AnasSarkiz/tscircuit-ai-agent-remote/assets/product-concepts/ai-remote-v1-infographic-v2.prompt.txt

Edit the attached AI Remote product infographic into a substantially cleaner, more premium SCREEN-FIRST handheld concept. The user's correction is the highest priority: MOST OF THE DEVICE IS SCREEN, and there is ONLY ONE PHYSICAL BUTTON, ON THE TOP EDGE, used to HOLD TO TALK. The old design has far too many controls and a small screen; completely redesign that device geometry while retaining the reference infographic's overall three-column presentation.

DEVICE INVARIANTS FOR EVERY VIEW: one consistent beautiful slim portrait rounded rectangular handheld, matte graphite/dark charcoal frame, restrained radiused corners, narrow bezels, a large edge-to-edge-ish portrait color touchscreen covering approximately 90% of the entire front face. The front is almost entirely glass/screen, like a small dedicated AI communicator. No chin, no large control panel, no front physical buttons. Exactly ONE tactile hold-to-talk button is recessed into the TOP EDGE of the enclosure, easily operated by an index finger. Show the top-edge button visibly in the three-quarter hero render, not centered on the front face. Discreet USB-C on the bottom edge. No rotary encoder, no dial, no knob, no dedicated APPROVE/REJECT physical buttons, no side switches, no extra side buttons, no exposed RGB LED. Tiny microphone openings and a discreet speaker opening may appear on the edge, subordinate to the screen. No visible physical control besides the single top-edge TALK button. Keep this geometry and button placement identical in the hero, exploded lid, and all other device renderings.

AESTHETIC: restrained, refined industrial design, excellent proportions, polished glass and matte graphite, premium consumer electronics CGI, not a chunky hobby enclosure. Clean white canvas, charcoal/navy typography, restrained teal/cyan accents, hairline separators, much more breathing room, clear hierarchy. Keep the three-column editorial idea of the supplied image but simplify all clutter and shorten text. Photoreal concept render, soft daylight lifestyle hero on a clean desk, tasteful studio lighting on exploded assembly. No background novelty typography, no mugs with slogans, no plant labels. No garish rainbow controls. Crisp carefully spelled typography throughout.

HEADER: large title "AI Remote V1" with V1 in teal. Subtitle "Hold to talk. Release to ask." Top right short sentence "Your AI, in your hand."

LEFT, LARGE HERO: the redesigned screen-dominant device is upright on a quiet wooden desk, slightly angled so the single top-edge button is clearly visible. Its front display is very large with a calm dark navy/cyan interface: small heading "LISTENING", a tasteful luminous cyan waveform, and simple large copy "I'm listening." Small line "Release to send". A minimal bottom status area is part of the screen, not a physical control. Keep the front elegant, spacious and mostly glass. Beneath hero: "One button. A conversation." and smaller "Hold, speak, release."

CENTER, EXPLODED CONCEPT: show the same slender enclosure with large front glass/display, the display module, a thin green concept PCB, a thin LiPo pouch, a small speaker, and rear shell. No front button mat or encoder mechanism. The only mechanical control is the single top-edge pushbutton. Five small numbered cyan/blue callouts, with correct leader targets and no overlaps:
1 "Large display" / "Screen-first interface"
2 "Hold-to-talk button" / "One button on the top edge"
3 "Voice + sound" / "Microphones and speaker"
4 "Wireless AI" / "Wi-Fi to your backend"
5 "Rechargeable" / "USB-C + LiPo"
This is an illustrative assembly, not verified mechanical CAD.

RIGHT: two clean, smaller conceptual green PCB views titled "PCB TOP — concept" and "PCB BOTTOM — concept". Show a slim portrait same-outline board on both faces. Top view contains an ESP32-S3 antenna module at the top with a clear hatched antenna keepout, microphone component categories, a display connector and exactly one top-edge button interface. No large tactile front controls, no encoder footprint, no colored physical buttons. Bottom view shows USB-C, power circuit, battery connector and speaker connector. Use only 3–4 concise readable labels per view: "ESP32-S3", "Antenna clearance", "Display connector", "Top button"; then "USB-C", "Power + battery", "Speaker". Caption "Proposed PCB layout"; do not invent final screen size or enclosure dimensions.

BOTTOM: simple elegant interaction flow with small teal icons: "HOLD" → "SPEAK" → "RELEASE" → "AI RESPONSE". No physical approval/rejection claims or decision icons. A thin readable footer states "Concept illustration • Proposed layout • Untested prototype".

Absolutely remove every old dial/encoder, all front physical buttons, the old MIC OFF side slider, green/red button imagery, the old physical approval callouts and the old small-screen proportions. The visual must communicate a dedicated handheld where almost the whole device is the display and the only physical button is on top, hold-to-talk only. Make the new enclosure visibly more minimal and screen-dominant than the original. Output a polished high-resolution 3:2 landscape infographic with nothing cropped and consistent product identity across views.
