AnasSarkiz/tscircuit-ai-agent-remote/assets/product-concepts/ai-remote-v1-infographic-v3.prompt.txt

Edit the referenced AI Remote infographic into a MUCH SIMPLER SQUARE DEVICE concept with TOP-SIDE PCB ASSEMBLY ONLY. The user wants a simple square form, and only top assembly. Preserve the earlier essential interaction: the front is almost entirely the display, exactly one exterior physical button on the top edge, HOLD TO TALK. Change the tall phone-like enclosure to a compact square, with width and height nearly equal. Do not merely crop the old image; redesign the product and simplify the composition.

Output one polished landscape 3:2 product concept graphic with bright white background, elegant restrained navy/black typography, soft cyan/teal accents, realistic premium industrial design CGI, generous whitespace, and only a few short labels. Far less text and diagram clutter than the reference.

SQUARE PRODUCT: a small slim square handheld AI communicator, graphite/dark charcoal rounded-square enclosure, softly radiused corners, thin bezels. A nearly square color display covers about 90% of the front face. No large chin or control panel. Exactly one modest recessed tactile button centered on the TOP EDGE, visibly separate from the glass, easy to hold with an index finger. No front buttons, no knobs, no encoder, no side switches, no extra buttons or visible status LEDs. Discreet USB-C on the bottom edge and tiny microphone/speaker apertures only. The same square device and top-button geometry must be consistent in every depiction.

COMPOSITION:
1. LEFT/HERO, roughly 50% width: large beautiful three-quarter front view of the square device, on an uncluttered pale warm wooden surface, soft studio/daylight reflections. Angle it gently so both the screen and the single TOP EDGE button are visible. No lifestyle props or distracting background. On-screen UI is minimal: small cyan heading "LISTENING", a single elegant cyan waveform, large copy "I'm listening.", small line "Release to send". Avoid smartphone UI clutter and time/battery icon rows. The device must look SQUARE rather than portrait-phone-shaped.
2. CENTER/RIGHT, roughly 50% width: a simple isolated assembly illustration, with only two or three levels, showing the same square front enclosure/display slightly raised over the square main PCB. Use one clear TOP VIEW of the populated PCB. Show every soldered electronic component on this TOP face: ESP32-S3 module, small power circuitry, a display connector, microphone categories, battery/speaker connectors and top-edge button. All connectors and controls are mounted/accessed from the same top component side as a PROPOSED assembly. The PCB underside is not shown; no bottom view or underside populated electronics. The PCB is compact and square to match the enclosure. If a rear enclosure/base is shown, keep it simple, no extra electronic layers or clutter. No invented routing-validation claims. Empty hatched antenna keepout with no copper/components; all placement is illustrative.

TEXT/HIERARCHY:
Top large title: "AI Remote"
Subtitle: "Square. Simple. Hold to talk."
Short callout pointing at the exterior top edge: "One top button"
One callout at screen: "Large display"
Heading over PCB view: "PCB — TOP ASSEMBLY ONLY"
Under PCB heading small note: "Proposed placement"
At most three small PCB leader labels: "ESP32-S3", "Display connector", "USB-C + power".
Bottom thin interaction strip, no excessive icons: "HOLD" → "SPEAK" → "RELEASE" → "AI RESPONSE".
Small readable footer: "Concept only • Top-side assembly proposed • Untested prototype"

STRICT REQUIREMENTS: Device outline is nearly 1:1 square, not tall portrait. Screen occupies nearly all front. Exactly one exterior physical top-edge hold-to-talk button. No rotary dial, no approve/reject physical controls, no side privacy slider. Only top-side populated PCB assembly is depicted; remove the previous bottom PCB diagram entirely. No dimensions or fabrication-ready claims. Do not represent this as validated CAD or a physical tested prototype. Reduce annotation count and give the render room to breathe. Clean accurate spelling, no duplicated labels, no cropped text, no overlapping arrows. Premium, minimal, practical, elegant.
