AnasSarkiz/tscircuit-ai-agent-remote/CLOUD_HANDOFF.md

Latest delivery checkpoint: generated native SHA-256
`16c299accb1750ce3b93997726c7c3316595e9848730bd9f20a55b6d24c4317a`.
Read `evidence/pcb-completion-2026-10-08/review.md` and current receipt index.
All 13 actual phase SRJs/output paths are archived. Optional replay endpoint
metadata/four via IDs differ; all copper geometry and electrical source records
are preserved. Fresh independent audits confirm 0 shorts/geometric violations,
12 open nets and all 9,813 parent connected pairs. Schematic UI has one retained
parallel-branch advisory; the additional R63/U3 collision is corrected. Native
retains 16 supplier-refresh and four pin-attribute lookup warnings. Genuine
imports and strict rotation remain qualified; no warning is hidden. Source
snapshot runs complete but unchanged golden references fail. No fabricated
final supervisor timing/memory is reported after the session lost that receipt.
Setup installs separate checksum-verified Bun 1.4.0 for generation while keeping
Bun 1.3.9 frozen install/tests. Saved onboarding draft revision 32 is read back;
it does not apply runtime policy. Public delivery is established by final
publication receipts, not by presumed cloud CI or fabrication approval.

## Current canonical generator qualification — 2026-10-08

**0.0.11-wip-generator-qualification — NOT READY TO ORDER.** Canonical project
runtime fixes eliminate all 169 schema failures and missing pill paste. The
untouched genuine C7848 import clears U14 supplier rotation. Local regulator
escape requirements now explicitly preserve 1 mm trunks. All 9,813 existing
connected pairs are preserved; all 125 purchased component poses are unchanged.
Fresh native checks still report 50 connection errors / 12 physically open
assigned nets plus two unassigned battery contacts. Shorts and measured copper
clearance violations are zero. The final 2.8-inch LCD, backlight, RF/mechanical
integration and battery polarity remain unqualified.

The corrected canonical Gerber library preserves USB slots. Independent strict
Gerber parsing and Excellon inspection pass; actual exports are explicitly
NOT FOR FABRICATION. Strict PnP rotation passes for all 125 parts, and the official
resolved BOM covers all 43 supplier identities. Current inventory confirms 39
identities conservatively; D2 is out of stock and three positive-stock records
require assembly-availability confirmation. Complete current/thermal and full fabrication gates remain open.
All 15 original schematic style issues are corrected in the actual schematic
trial, with identical PCB/CAD geometry. One newly exposed alignment advisory
misclassifies the VMOTOR flyback/bleeder parallel branches as a series pair;
its exact six-contact topology and conflicting orientation advice are reviewed
and retained in the schematic-style-repair evidence. Final routed checks are
recorded independently; no failure is hidden.

Core also prevents disabled subcircuits from starting autorouting during
updates; both disabled controls and an enabled control are regression-tested.
The actual isolated MCU diagnostic now has zero copper and zero routing events.
Board tests: 51 pass; the full-board fabrication gate still fails on 50
unresolved native connections. These are 50 assigned open contacts plus two
unassigned J3 contacts, not a completed board.

Receipts and source patches: `evidence/pcb-completion-2026-10-08/` and `toolchain/`.
Older entries below are historical.

---

## Current local microphone bypass — 2026-10-08

**0.0.10-wip-microphone-bypass; not ready to order.** Read
`evidence/microphone-local-bypass-2026-10-08/review.md` and its native/qualification
receipts first. C81/C45000 is now (17.05,-28.10)/180 degrees top, beside U5;
R93/C105881 moves to (16.50,-31.42)/0 degrees top. Actual .30 mm top bypass:
1.442790 mm supply, .599976 mm ground pour entry, no bypass via. All four local
terminal contacts pass. Only these two rigid purchased poses change; all 125
identities, 123 stationary geometries and 244 genuine asset/solver files remain.

Native SHA `8be25ca28e6271890aab0d450ffdc62088ced91967ae1b6185ab8267ff9f1177`:
381 traces / 320 full-span .30/.45 vias / 273 pours. Zero measured shorts and
geometric/clearance violations; all 9,813 prior contacts preserved and all 250
active authored region widths pass. Full-board gates still fail: 50 native
errors (46 J7/4 U27), 12 assigned open nets, plus two unassigned J3 outer
contacts. Requested centered 2.8-inch landscape LCD is unimplemented; exact
contact/fold/bend/antenna/backlight qualification remains required.

All five source checks, TypeScript, formatting and 94 routing regressions pass;
board tests 49 pass/2 fail, UI style 15 issues, strict schema 169 failures,
unchanged-reference source snapshots fail. Two native routes violate explicit
width minima and 65 need nominal/current review; 32 native paste records,
polygon Gerber/short-check and U14 rotation remain unresolved. No order claim.

Fresh official JLC pages: 12/43 identities cover one board, 2 have zero public
buyability (U1/D2), 29 HTTP503 inventory results unknown. D2 also reports zero
stock. $26.3055 is the prior unchanged-identity reference subtotal, not a quote.
Latest core .2110 still lacks the tested paste fix; keep frozen runtime.

The genuine renderer required 43 exact prior official supplier-orientation
cache inputs to retain supplier maps during live lookup failures. Their origin,
hashes and failed native trial are preserved. For source rebuilds: run
`bun run publish:prepare`, link frozen node_modules as previously documented,
then `python3 evidence/microphone-local-bypass-2026-10-08/restore-supplier-orientation.py .publish/board /tmp/restored-board-supplier-orientation.json`.
Preserve actual native/events; clean stage with publish:prepare before upload.
Public package is 128 regular files; hidden input caches are exact GitHub
evidence, not invented solver results. One heavy Linux operation through the
budget supervisor at a time; no local Mac routing or unchanged whole-net retry.

Public GitHub implementation 3d88ca2 and tsci .10 release
d17c1129-2a2a-4834-a186-e562b77aa268 are verified: all128 anonymous files exact,
native preview exact object, release public/listed/ready. The two HTTP413 files
were verified missing before bounded supported archive repair. No readiness
override. Both automatic .10 cloud jobs failed infrastructure sandbox
initialization before source execution; any supported retry/actual observation
is recorded separately, never inferred from uploaded native availability.
The actual .9 cloud job completed without a user-code job error, superseding
its old pending observation. Latest official circuit-json .521 independently
still reports the same169 failures on the exact current native. Active pins
remain frozen. Cloud draft30 startup instructions are saved/readback exact;
installation/repositories/network/requirements unchanged. Review/save/publish
is needed to activate the environment; fresh restoration remains unverified.
Earlier entries are historical.

---

## Current UART and supply repair — 2026-10-07

**0.0.9-wip-standard-uart; not ready to order.** Read
`evidence/programmer-direct-uart-2026-10-07/review.md` first. Genuine untouched J6/C160389 now
has RX/GND/TX on pins 1/2/3 and grounded holds 4/5; pose remains (-17.4,-10) mm,
0° top. Specified numbered SH3 cable directly connects the standard programmer;
separate power, manual BOOT/RESET and open enclosure required (6.3 mm mated
height). Hardware/cable assembly is untested.

Real authored UART copper, ground pad links, audio-gate detour and 0.8 mm bottom
V3V3 bypass are implemented. Native SHA `bcee32a49486610d7379583efb2b378846cc75f232272b50c717ad129c495704`.
381 traces / 322 full-span 0.30/0.45 mm vias / 273 pours. All 250 active region
widths and all 9,813 retained contact pairs pass. Other 124 purchased geometries
are unchanged. Measured shorts/geometry violations: 0/0. **50 native display
errors / 12 physically open nets remain.** Five source checks, TypeScript,
formatting and 94 routing regressions pass; board tests 49 pass/2 fail. Actual
UI: 15 style issues. Strict schema: 169 failures. Snapshots fail with unchanged
references. All failed trials and actual source/native events are preserved.

Requested centered landscape LCD remains unimplemented: exact fold/contact map,
bend radius, RF overlap and opposite backlight topology are unqualified. J3
outer battery contacts remain unnumbered/unrouted. Active paste, U14 rotation,
Gerber, two regulator width minima/current review and assembler allocation
remain gates. Official core 0.0.2108 still lacks the tested canonical paste fix.
Keep the frozen official runtime; no local package links, import/JSON edits,
weaker checks or orders. All 43 part identities have dated official receipts;
public buyability covers 40. Reference subtotal $26.3055 excludes fabrication,
assembly, external assemblies, shipping and minimum order quantities.

Public GitHub implementation commit 1642750 and tsci release
f520e705-7b21-4a06-89d2-a66b70ced491 (.9) are verified: all 128 public runtime
files match; the native preview is the exact qualified object. Release is public,
listed, latest and ready-to-build. No manual readiness override. An earlier
incomplete-upload cloud job failed missing STEP; that asset is now exact/public.
The later cloud job was still generating pours at observation, not a CI pass.
Continue with frozen Bun 1.3.9 and one budgeted heavy Linux operation at a time.
Saved cloud draft revision 29 retains all 20 custom hosts, install/repositories
and previous startup instructions; Save/Publish remains needed to apply it.
Earlier entries below are historical.

---

## Latest canonical paste repair — 2026-10-07

Read `evidence/core-pill-paste-fix-2026-10-07/review.md` first. The pill/rotated-pill
paste generator is fixed in canonical core source at base commit 90785db
(package 0.0.2106). Seventeen relevant tests, full TypeScript, formatting, build
and dist smoke pass. Genuine U14 coupon has 20 valid apertures with identical
physical pads; genuine U16/U27 coupons have 34. All local package links were
removed and official packages restored. Official 0.0.2106 still reproduces zero
U14 paste, so this is an unreleased source fix. Do not claim the active board's
32 missing paste records are repaired or deploy a local yalc runtime.

Active board remains official core 0.0.2090 and exact accepted native SHA below.
Latest copper audit still finds 0 measured shorts/clearance violations, 12 open
nets and 50 native open-port errors. No LCD pose, schematic or routing change is
accepted. Exact panel/RF/flex qualification and a supported released generator
fix remain dependencies. Saved cloud draft is revision 28 with 20 custom hosts;
its network settings still require runtime application. Use CI Bun 1.4.0 only
for the isolated upstream source work; keep the board's frozen setup intact.

## Latest 2.8-inch request —2026-10-07

The uploaded follow-up explicitly supersedes the2.3-inch plan with a landscape
BuyDisplay~2.8-inch panel and left/right FPC/J7 connection. **No replacement is
implemented.** Exact ER-TFT028A2-4 primary mirror confirms69.3×50.2mm body,
57.6×43.2mm active area,ILI9341 and common-cathode backlight. Centred body overlaps
current antenna keepout59.5mm²;flat 26.7mm tail leaves the enclosure;minimum bend
radius is not published. Preferred A3 download is still challenged and the actual
Cloudflare subdomain is proxy-blocked. Saved19-domain draft/startup priorities
need runtime application;model CDN is responding. Canonical exact/download C7848
re-import now fixes supplier pin 1 and preserves exact CAD assets/origin,but20
pill pads have no paste,so it is not applied to the active board. Old2.3-inch
staged sources and rejected placement are retained underE13. Current accepted
native/source/routes remain unchanged,with 50 opens and fabrication gates.
Read `evidence/display028-integration-2026-10-07/review.md` and the latest user
decision first. Do not continue the superseded2.3-inch poses or guess final J7
mating. Requested actual placement/routing is blocked,not complete.

Historical handoff follows.

## Current approved 2.3-inch selection and primary review — 2026-10-07

The user uploaded the exact **ER-TFT023-1** datasheet and accepted the smaller
2.3-inch display. The earlier ≥80% display-body coverage target is explicitly
relaxed for this panel. Select the no-touch ILI9342 / 320×240 panel for the next
revision; do not confuse an accepted selection with an implemented replacement.

The primary PDF is now archived and reviewed in
`evidence/display023-primary-review-2026-10-07/`. SHA-256:
`476f23033ca4ce0caa9ca6470fbc3d287b841240afaa54db986756fdfa588095`.
Rotate the native front view 90° CCW for a 45.8×50.9 mm portrait body with a
right-side flex. The 50-pin audit finds one required role change under the old
provisional mapping: panel pin 6 / IM0 must connect to 2.8 V VLCD, giving SPI
mode 1111. The other 49 assignments match; physical mapping is not qualified.
Existing 2.8 V logic and four-sink backlight circuitry fit the reviewed limits.

The manufacturer recommends a top-contact socket for a flat tail. Retaining
C262650 behind the panel needs a qualified two-fold path and proposed J7 rotation
270°; a single-fold alternative uses lower-contact C11063 at 90°. Both proposed
poses conditionally map panel n → J7 n. No arrangement or new contact-dependent
source/copper is accepted yet. The nominal placement proposal moves J7, U14,
C42 and C43, with about 69.54% body/PCB overlap and no nominal rectangle overlaps.
It does not establish full housing/flex fit, copper clearance or native DRC.

**Dependent implementation is blocked** by unresolved physical flex/slot/contact
tolerances and the existing U14/C7848 strict supplier pin-1 rotation discrepancy.
Do not patch a genuine import, guess bend limits, or preserve the old mapping
after a connector rotation. Preserve accepted native bytes and all 9,842 prior
connections before any qualified move. The archived proposal and exact native
measurement coupons make the remaining work reviewable; they are not a board
build or fabrication pass. Native remains 50 opens (46 J7 + 4 U27), and the board
is not ready to order. Public package remains 0.0.8-wip-speaker-routing.

The missing new panel PDF blocker is superseded by this upload. Supplier website
Cloudflare and the alternate connector's signed-CDN denial remain distinct
observations. Updated cloud startup instructions preserve the 17-host draft and
previous setup. Draft saving does not apply settings or publish the environment.

---

## Previous independent display search — 2026-10-07

The user instructs the agent to find the new display documentation directly,
rather than asking them for another PDF. Manufacturer catalog search, robots
and sitemap return Cloudflare403. Google/Bing CONNECT requests are denied;
their exact domains are now added to the saved draft, pending user
Save/Publish. GitHub code search works and yields third-party ER-TFT023-1
references. A 50-pin table matches the old panel's roles for the current SPI
configuration. One older BOM uses ER-CON50HT-1 and ILI9342 firmware, but its
symbol/datasheet point to ER-TFT024-3. These are useful leads, not current primary
mechanical/power/controller qualification. No exact PDF was found in those trees.

The user explicitly approved the CA import and the exact command completed
with exit 0. The initial missing-CA diagnosis was incorrect: the matching CA
already existed under `OpenAI-nebula-dns`. The actual browser failure was NSS
SEC_ERROR_READ_ONLY (-8126) under the filesystem sandbox. Approved browser access
to its actual database restored TLS verification. BuyDisplay then returned a
Cloudflare challenge requiring `challenges.cloudflare.com`; this host independently
returns CONNECT403. It is now added to the saved **17-domain draft**, alongside
the preserved supplier/search hosts. User Save/Publish is needed to apply it;
no proxy, TLS or challenge bypass is authorized. Do not request CA approval again.
See
`evidence/display-index-search-2026-10-07/review.md` and its exact receipts.

The restored browser also ran the actual schematic UI analysis against the
accepted native: **14 issues**, versus the earlier CLI result of zero. The
exact UI records are in that review's `ui-analysis/` directory. The UI check
executed but did not pass; the former certificate blocker is superseded.

The accepted board/source/native and public package remain unchanged. The
replacement's flex, pin correspondence and power limits remain unqualified.

---

## Previous display replacement review — 2026-10-07

The user rejects the ER-TFT026-1 bottom flex for the present right-side J7 and
requests review of BuyDisplay's SPI 2.3-inch 320×240 ILI9432 product plus a
matching connector. This supersedes the earlier conditional display selection,
not the accepted native copper checkpoint below. No replacement has been
qualified or implemented.

The uploaded ER-TFT026-1 primary PDF is now available and reviewed in
`evidence/display-datasheet-routing-2026-10-07/`; its contact face and local
pin-1 views are documented. All 50 named-net assignments match only under the
old provisional 51−n mapping. Do not keep reporting that the old PDF is missing,
and do not use it as a specification for the new display.

The new product page/PDF retrieval fails with Cloudflare HTTP403; normal
Chromium fails certificate trust. Its flex exit, pinout and electrical/mechanical
specifications remain unverified. Obtain the new exact PDF/drawing before
choosing its connector or changing contact-dependent nets and copper.
`evidence/display-replacement-review-2026-10-07/review.md` records the attempts
and qualification requirements.

Candidate C11063/AFC07-S50FCC-00 is a genuine imported 50-pin 0.5mm lower-contact
socket, with 6,076 official total stock / 6,045 available-to-buy at 11:30UTC.
It is not accepted for the new display. Its local pin-1 side differs from the
present upper-contact C262650 import; do not swap it without a physical mapping
review. The prior 13-domain draft now additionally allows the official JLCPCB
datasheet CDN `jlc-prod-smt.oss-eu-central-1.aliyuncs.com`. Updated continuation
instructions and the additive domain list are saved; user Save/Publish is still
needed to apply them. BuyDisplay's origin challenge is a separate failure.

Board source, native bytes, imports and all 126 published package files stay
unchanged. The board still has 50 native opens and is not fabrication ready.

---

## Current accepted speaker checkpoint — 2026-10-07

**0.0.8-wip-speaker-routing — NOT READY TO ORDER.** Resume from the untouched
official CLI native at `dist/index/circuit.json`, SHA-256
`35c5fb2bfc870daf11b5f5e30847f1e5a86fd886ebb8ef11fc3cf6e88e77e63d`.
The source repair connects both speaker outputs using explicit manual top-layer
paths. U3, J4, C50, R69 and R70 move; TP1 moves; 120 purchased poses stay fixed.
All imports/models/original solver paths are byte-identical. No purchased part
is added. Retirement lists keep source indices stable and retain logical traces
so genuine native connectivity errors remain visible.

Measured state: 384 traces, 325 full-span 0.30/0.45 vias, 270 pours; zero measured
shorts/clearance violations; all 9,842 previous terminal pairs preserved; all
247 active authored regions at nominal widths. Fifty native opens and twelve
physical open nets remain around J7/U27. J3 outer contacts remain unassigned.

Type/format, 92 routing regressions and five source/placement checks pass.
Board tests remain 48 pass / 2 fail. The direct official-platform placement
capture is correctly unrouted and matches real supplier metadata. CLI placement
still emits copper even with `--routing-disabled`; do not accept it as a pass.
CLI schematic style passes; the actual UI CDN module fails certificate trust.
All 26 sheets and critical copper views were inspected. The actual source
snapshot completes with both historical reference mismatches; do not blindly
update references. Detailed raw outcomes, rejected proposals and lossless
native event archives are in the current evidence directory.

The AKY2945 PDF is retrieved but does not number its outer contacts. The older
BuyDisplay retrieval observation below is superseded by the uploaded PDF and
replacement review above; final display mating remains unresolved.
JST/LCSC/EasyEDA requests also fail. The saved complete domain draft adds
`www.jst-mfg.com`, `www.lcsc.com`, `easyeda.com`; only user Save/Publish can apply
it. Do not bypass network policy, TLS, supplier drawings or failed imports.

Stock covers 42/43 identities for two prototypes; J6/C160405 is unavailable.
C265110 is a different SHL family and fails the supported exact import. No
substitute is accepted. Reference parts cost is $26.333/board; Standard PCBA,
setup/loading, external assemblies, shipping/tax and allocation remain open.

Next dependent gates: verified J3/J7 interfaces; genuine stocked programmer
connector import/mating; canonical paste/schema/polygon exporter corrections;
qualified U14 supplier rotation; regulator widths/current, remaining bypass,
signal integrity, stackup/enclosure/flex/battery and final CAM/assembly review.
Original imported exceptions remain only the two historical acoustic holes.
Never rewrite native JSON or solver caches, weaken checks, create custom parts,
resume the watcher, spawn agents, place orders or claim physical test results.

Use `source scripts/cloud/env.sh` and the exclusive budget supervisor for every
heavy cloud command. Follow the standing authorized GitHub main/public tsci WIP
workflow and verify every staged source/native byte before any upload retry.
[Current review](evidence/routing-continuation-2026-10-07/review.md) and
`context/build-checkpoint.json` carry the exact final publication observations.
The older sections below are historical.

---

## Historical manual routing repair — 2026-10-07

**0.0.7-wip-manual-routing-repairs — NOT READY TO ORDER.** This entry
supersedes the historical checkpoints below. U4 now has a real 0.36 mm ground
escape to a 0.30/0.45 mm through via. Its clock/data escapes were moved to make
room while retaining their original nets and minimum widths.

The supported source CLI build completes in 251.86 seconds and exits 1 with
**52 open-port errors**: 46 J7 display contacts, four U27 backlight contacts and
two SPEAKER_N contacts. The unchanged generated JSON contains 381 traces,
325 through vias and 271 pours. Independent geometric checks measure **zero
shorts and zero clearance violations**, preserve all 9,842 previously connected
numbered-terminal pairs and verify all 247 authored regions at their nominal
widths. There are still 13 physically open nets. J3's unassigned outer contacts
are excluded from that count; battery polarity and display mating remain
unqualified. Every purchased component footprint, pose and model is unchanged.

A speaker/VSYS candidate was rejected: its native output disconnected U25.2 and
C76.2 ground, losing 266 existing terminal pairs, and reported a bus-skew error.
The candidate and follow-up proposals are preserved as evidence, not accepted
routing. Original speaker constraints and original power copper remain intact.
No native errors or checks were suppressed.

The five source/placement checks pass. Board tests remain 48 pass / 2 fail;
169 strict native-schema failures, 32 missing U16/U27 paste records and the
official shorts/export error “Unsupported shape polygon” still block approval.
Two regulator traces violate explicit source widths; 63 nominal-width branches
and current/signal-integrity qualification remain open. Stock and programmer
limitations in the prior review still apply. No order or physical test occurred.

Primary supplier retrieval is blocked by HTTP 403 from the cloud policy. Add
`www.buydisplay.com` and `www.elektronik.ropla.eu` to the existing Environment
settings allowlist, then save and publish it to resume exact J3/J7 qualification.
The editable allowlist was unavailable; no unknown list was replaced.

[Current repair review and exact receipts](https://github.com/AnasSarkiz/tscircuit-ai-agent-remote/blob/main/evidence/routing-zero-drc-2026-10-07/review.md).
Matching public publication and cloud CI are separate observations; a WIP
preview does not establish zero DRC or fabrication readiness.

Current validation receipts: supported source checks pass, TypeScript and
formatting pass, and all 87 routing regressions pass. Full board tests remain
48 pass / 2 fail. The required source snapshot completes in 61.10 seconds and
fails on PCB/schematic differences; references are unchanged. All five cloud
supervisor smoke cases pass, including cleanup of a live descendant after its
parent exits. The final source build and measured copper are bound by SHA-256
in the repair review. Requirements/interfaces and schematic/BOM remain
**blocked**; final placement is **in progress**; routing, automated checks and
fabrication qualification remain **blocked**; ordering/hardware tests are
**not started**.

---

## Previous connection repairs — 2026-10-06

**0.0.6-wip-connection-repairs — NOT READY TO ORDER.** This is a historical
source/native checkpoint, superseded by the manual routing repair above.

Manual native routing reduces open-port errors from 89 to **53** and physically
open nets from 25 to **13**. The actual frozen-install CLI build completes in
256.86 seconds and exits 1 on the remaining errors. Its unchanged native output
has 380 traces, 322 full-span 0.30/0.45 mm vias and 269 pours. Independent copper
measurement finds **zero shorts and zero clearance violations**, preserves all
8,152 previously connected numbered-terminal pairs and adds 1,690 connected
pairs. All 245 authored regions meet their nominal widths after fixing an
outline-generator defect at short bends. Component footprints, poses, models
and original solver caches remain unchanged.

Source checks, CLI schematic style, TypeScript, formatting and 80 routing
regressions pass. Full board tests remain 48 pass / 2 fail. Remaining native
errors are 46 J7, four backlight U27, two SPEAKER_N contacts and U4 ground.
J3's centre NTC is routed; its outer polarity and J7 mating remain unqualified.
Two regulator routes violate their explicit source widths; 63 nominal-width
branches, current/signal integrity, 169 schema failures, 32 missing paste
records and polygon Gerber export still block fabrication. Dated stock still
shows J6/C160405 unavailable. The standard programmer needs the documented
adapter and has not been hardware-tested.

[Actual repair review and receipts](https://github.com/AnasSarkiz/tscircuit-ai-agent-remote/blob/main/evidence/connection-repair-2026-10-06/review.md).
Matching public source/native publication is established by its anonymous
verification receipts, not by preview availability or a passing cloud CI claim.
No fabrication order or physical test has been performed.

---

## Current six-point review — 2026-10-06

**0.0.5-wip-style-vias-power — NOT READY TO ORDER.** This entry supersedes the older counts and status below.

J1 now uses the requested native USB-C schematic symbol while preserving its numbered contacts, supplier identity, physical footprint and models. CLI schematic-placement analysis reports zero issues. The actual UI analysis was invoked but its external analysis module failed to load; this is a blocked check, not a passing result.

The clarified high-current requirement is implemented: all 80 authored high-current trunks and 59 audited native high-current traces use top/bottom copper. Six low-current pull-up/control/probe branches have separate documented requirements. All 217 vias physically span all four layers, with exactly 0.30 mm holes and 0.45 mm pads; blind/buried vias are explicitly disabled. All 151 native supply/control and relocated signal regions meet their nominal widths.

The supported frozen-install CLI build completes in 247.03 seconds and exits 1 with **89 real open-port errors**. Native output contains 328 traces, 217 vias and 183 pours. The independent geometry audit measures zero shorts and zero clearance violations, preserves all 8,146 previously connected port pairs, and still finds **25 physically open nets**. All 125 purchased component footprints, poses and models are unchanged. TP1 moves to (-22.2, 12.3) mm inside the main ground island. The five source checks, copper-free placement build, TypeScript, formatting and 64 routing regressions pass. Board tests report 48 pass / 2 fail (fabrication and strict native schema).

Official exact-part JLCPCB pages cover all 43 identities / 125 placements: 42 identities report enough total stock for one board; **J6 C160405 reports zero stock**. Positive stock for U1, D2 and U16 does not qualify assembly allocation. No stock reservation or assembler rotation approval is claimed.

Remaining fabrication blockers include unresolved J3 numbered outer polarity and J7 FPC mating, incomplete connections, 169 strict native-schema failures, missing pill-pad paste, unsupported polygon Gerber shorts/export, two regulator switching routes with 0.275 mm necks below their explicit 1.0 mm source requirement, 55 nominal-net-width branches requiring load review, and supplier rotations/current/stackup/signal-integrity/mechanical qualification. The standard JST programmer needs the documented adapter; direct connector mating and hardware operation are untested.

The supported source snapshot comparison completes in 61.13 seconds and fails on PCB and schematic differences; committed references are retained. All 26 native A4 pages, four copper layers, mask/paste and critical zooms were inspected. Native component guides cover all 135 references with valid annotation schema. Final component inventory confirms 32 missing pill-pad paste records on U16/U27.

[Full review and actual receipts](evidence/six-point-board-review-2026-10-06/review.md). Publication is recorded independently; native preview availability does not establish passing cloud CI or fabrication approval. No order or physical test has been performed.

---

## Schematic component explanations — 2026-10-06

Public version0.0.4-wip-schematic-notes is verified:120/120exact files,
latest/public/listed/ready=true and26native A4sheets. Accepted GitHub source is
81c066f8044f98c4d25e685a65edb3bc792affcb; nativeSHA256 is
8a68235d7b446165de53665adb2e53ca971e7e179969c2eb07c1e1185b140042.
[Updated native preview](https://tscircuit.com/AnasSarkiz/tscircuit-ai-agent-remote/releases/7fe00b28-1971-41f3-b4e5-c327c6b6b3e0/preview).
Automatic cloud job6873fe90-66f8-45be-8122-3a5fd15e15b9 is recorded separately.
No duplicate cloud build or model/native-file edits were used for publication.
The first80-second observation ends with the automatic cloud job still running;
remote CI is pending. Read the recorded build ID rather than requesting another.

Revision `0.0.4-wip-schematic-notes` adds a plain-English explanation for every
schematic component reference: 125 purchased components and 10 solder/test
pads. The 13 circuit drawings link to paired A4 component-guide pages, numbered
14–26, to keep the original symbols and connections readable.

Open the schematic sheet selector in tscircuit and choose a **Component guide**
page for the relevant circuit. Guides explain power, controls, USB/programming,
display, speaker, haptic drive, microphones, backlight and measurement access.
Battery connector polarity and display mating remain explicitly unverified.

[Annotation validation and rendered pages](https://github.com/AnasSarkiz/tscircuit-ai-agent-remote/blob/main/evidence/schematic-component-notes-2026-10-06/review.md).
This documentation revision does not establish fabrication or hardware readiness.

The fresh frozen-install native CLI build completed in249.96seconds and
retains90open-port errors. Annotation coverage/native schema, TypeScript and
formatting checks pass. AllPCB/source nets/ports and the original schematic
symbols/wires/labels match the prior board. The source checkpoint verifies
unchanged imports, models, lockfile and routing artifacts. The accepted schematic
snapshot adds all26A4pages; the PCB reference remains unchanged.

Final board checks remain blocked:47tests pass/3fail,169native schema failures
and90open ports. The placement fixture's extra mismatch is only10native test
pads receiving empty supplier maps from the CLI; strict PCB/net comparison
passes. The required source snapshot reaches its recorded360-second budget;
the supported snapshot of accepted native JSON completes, passes the reviewed
schematic reference and retains the original PCB-reference mismatch.

---

## Public correction checkpoint — 2026-10-06

Accepted source commit: `7c8c78efcd8ffb6072ce824aa95de75672c36188`.
Public tsci version: `0.0.3-wip-local-bypass`, release
`8dd2f2c2-5ce3-4826-a126-aa7cc7ea78b8`. All119 package files hash-match
anonymous readback; native preview exactly matches the accepted JSON.
[Preview](https://tscircuit.com/AnasSarkiz/tscircuit-ai-agent-remote/releases/8dd2f2c2-5ce3-4826-a126-aa7cc7ea78b8/preview).
Cloud build `5f93c81b-9582-428b-872d-654926e8d60d` was scheduled automatically;
it completed with user_code_job_infrastructure_error while waiting on part
orientation and its RPC stream disconnected. See cloud-build-failure.md; do not
queue duplicate jobs or claim successful cloud CI.
Full-board gates remain false. See the correction review and public receipts
under `evidence/board-corrections-2026-10-06/`.

## Latest MCU correction — 2026-10-06

**Revision `0.0.3-wip-local-bypass`; NOT READY TO ORDER.** C31 now has a
native top-layer local supply/ground connection beside U1: supply-pin distance
falls from36.000mm to2.000mm, with a0.8mm branch to the existing U1 supply
escape and no additional supply via. C30 now uses the genuine imported
22µF GRM188R61A226ME15D/C84419 shown in Espressif's reference circuit.
Bulk placement/effective capacitance and microphone bypasses still need work.

Fresh native copper has306 traces,249 full-span ordinary vias and190 pours:
**0measured shorts/clearance violations**, but26 open nets/90 native errors and
35GND islands remain. All152 authored region widths pass; two switch traces
and55 nominal-width branches still need correction/current qualification.
Eight target programmer copper groups pass; programming is not hardware-tested.
The supported BOM resolver generates125 purchased rows with verified recorded
MPNs/package labels and no blank descriptions. Current stock, rotations,
169schema failures,32missing paste apertures, polygon Gerber export and exact
battery/display mating still block fabrication.

[Correction evidence](evidence/board-corrections-2026-10-06/review.md).
The complete publication package now installs with the original frozen lockfile.
Its native CLI build finishes in222.33seconds and reports the90open-port errors;
all physical copper records match the validated board. Publication/remote CI
receipts are separate; this is a WIP step, not fabrication approval.

---

## Latest placement, component and programmer review — 2026-10-06

**NOT READY TO ORDER.** Electrical placement needs correction even though the
native overlap check passes: U1's nearest external3V3 bypass is26.160mm away;
U5's assigned100nF bypass is18.191mm away on a different supply copper island.
The manufacturer's local microphone bypass recommendation is not met by the
current separate-via arrangement.19 IC supply locations are measured in the
[new six-point review](evidence/board-programmer-stock-review-2026-10-06/review.md).

The requested Standard JST programmer v0.8.0 can use UART conditionally:
J5.1TX→J6.6RX, J5.2GND→J6.1GND, J5.3RX→J6.5TX. A custom3-to6 adapter,
separate target power, matching firmware and manual BOOT/RESET are required.
5host logical and8target logical/physical groups pass; no actual flashing test.
Fresh manufacturer pin tests5pass/0fail. Board copper/parts/imports remain
unchanged:26 open nets/90 native port errors and existing fabrication blockers.

All43 exact JLCPCB identities/125 placements have a dated stock manifest;
**current stock is unverified**, because the inherited proxy denies
jlcsearch.tscircuit.com with403. That one domain was added to the reusable
network draft; review/save and publish it in environment settings before retry.
Saving the draft does not apply or publish it. Historical C107701 stock8vs5
per board and C98220 stock22vs20 warrant priority refresh. No unchanged board
registry upload or fabrication approval is claimed.

## Current order-readiness audit — 2026-10-06

**NOT READY TO ORDER.** Fresh current native render is byte-identical to the
canonical board. Measured geometry:0 shorts/0 clearance violations, but26
physically open nets and90 native connection errors; J3 outer contacts are
additional unassigned omissions. All306 traces/792 wire segments checked:
0 below0.20 mm,2 regulator switch routes below explicit1.0 mm source minima,
and55 traces below named-net nominal widths needing current/escape review.
All152 authored region widths pass. Current critical manufacturer pin tests
pass; physical connectivity and current capacity remain unapproved.

Assembly still fails:32 missing U16/U27 paste records,169 native schema
failures,31 blank BOM descriptions,125 unqualified supplier rotations.
J3 pack polarity/J7 flex mating, stock/stackup/current/mechanical/fabrication
qualification remain open. Types and60 routing regressions pass; board tests
47pass/2real failed gates. Board/import/dependency/cache bytes unchanged.
[Full order-readiness report and measurements](evidence/order-readiness-2026-10-06/review.md).
This verification adds no copper and does not create a duplicate registry upload.

# AI Remote cloud continuation — current 2026-10-06

Latest manual/Freerouting continuation accepted **zero new board routes**.
Official Freerouting2.5.0/JDK25 are installed with verified release checksums.
The maintained exact-geometry bridge now checks engine pad topology/grid and
active-net plane semantics; representing SMT pad metal as structure planes had
made the router skip real missing signal connections. Corrected fixed-area
input is qualified, but the actual strict signal trial saved an empty SES
(0 wires / 0 vias) after geometry/no-connection errors. Manual contacts at actual
nominal net widths also returned0.
The supported 0.0001 mm extra-reserve /0.05 mm manual-grid trial also returned
0 paths on all6 eligible signals, preserving the required0.20 mm native minimum.
Read
`evidence/freerouting-continuation-2026-10-06/review.md` and
`scripts/routing/FREEROUTING.md`. Earlier DSN-development qualifications lack
the net-semantics check; never use normalized writer output as routing input.

Fresh audit still measures0 geometry violations/0 shorts, **26 disconnected
nets / 90 native errors**, and152 authored widths pass. Source/current native
JSON are unchanged. No zero-DRC/fabrication approval or new registry version.
52 routing regressions, TypeScript and formatting pass; board tests retain
42pass/2failed gates. Actual frozen install and4 supervisor smoke cases now
pass, superseding older installation-block wording below. Checkpoint hashes
record the reviewed helper-width fix and new tools; board/import/cache hashes
remain preserved. Startup/installation changes are a saved draft, not an applied
or published environment. Keep all existing interface/manufacturing restrictions.

Latest continuation tried native bus lanes and fanout, finer manual/power grids,
passive relocation, explicit AMP_SD_MODE paths and four ground-repair approaches.
**No new board copper/placement was accepted.** Bus lanes returned a terminal-
count error and no collision-free dogbone assignment; fanout routed 0/1. Manual
AMP paths joined the signal but split U3 ground. Moving the escape via did not
repair it; reducing the top cutout margin also introduced six drill violations.
Exact baseline sources and canonical JSON are restored. Read
`evidence/native-remaining-routing-2026-10-06/review.md` and its restored checkpoint
before retrying. Captured inputs/events/source snapshots are losslessly archived.
The new `scripts/routing/solve-native-stage.mjs` uses public native solver APIs;
results remain diagnostic until native regeneration and physical audits pass.
The stock DSN export drops required copper geometry/rules, so Freerouting was
not invoked. Required clearance/width/via rules and original caches are intact.

The original Pipeline9 SRJs and upstream report were delivered in
https://github.com/tscircuit/tscircuit-autorouter/issues/2878. The accepted board
and existing public WIP release below are unchanged. Fresh clean install is
blocked by HTTP401 for the locked pcb-trace-linter GitHub archive; retained
Linux tools work. No fresh dependency-install success or fabrication readiness
is claimed.

Latest routing request: explicitly use Pipeline9. `main.tsx` now selects
`autorouterVersion="beta_pipeline9"`; dependencies remain pinned. Actual native
metadata verified `AutoroutingPipelineSolver9_PreloadedTraceGraph`. The full-copper
USB attempt reached its time budget; the same input via the public library reached
the memory budget. A temporary signal-first trial reduced the input to 2,996
obstacles but returned `aJ ran out of iterations (capacity-autorouter@0.0.958)`.
No new route was accepted. All original copper is restored, and a fresh native
build has the identical SHA256 below. See `evidence/pipeline9-routing-2026-10-05/review.md`
and the preserved source snapshots/events/outcomes. Do not claim Pipeline9 completed
routing, accept the rejected reduced-copper output, or enable unqualified contacts.

The explicit selection is published at GitHub board commit
`a9600d81e40761d3fc7c2471c57cb05d77c548a4` and public tscircuit WIP version
`0.0.2-wip-pipeline9` (release `60b0df33-f229-4c85-8515-e9f5d2250674`).
All 116 files are anonymously byte-verified. The preview API finds the exact
native JSON and its preview page responds HTTP200. The earlier cloud-routing
release below is historical. The supported resume helper now accepts explicit
`--max-archive-bytes 3000000`; its three bounded archives overcame HTTP413 for
the full archive while preserving all original bytes. Use fresh receipts for
future mutations; this release is already complete. Cloud CI completion and
fresh browser visual review are not claimed. Updated startup instructions were
saved as a draft, not applied or published.

Latest human request: "push it to tsci" supersedes the earlier registry deferral. Native browser authentication completed as AnasSarkiz. Public release `0.0.2-wip-cloud-routing` now has**116/116 exact-matching files**, including current board JSON and required C262650 STEP. The official multipart archive endpoint resumed the existing release without changing any file bytes and enabled normal cloud scheduling. Build `ac331034-5de6-4b66-adf8-e29efd851e84` has started; check `evidence/cloud-tsci-publication/resumed-cloud-build-observation.json` for its actual result. See the current review and `resumed-complete-remote-receipt.json`. Do not repeat a full push, omit/modify required files or manually override readiness. Startup draft records the current workflow.

The registry preview API now finds `index.circuit.tsx` and returns the exact6,848-element native board array; its preview page responds HTTP200. `resumed-registry-preview-receipt.json` records this. Cloud CI remains running without an error or completion after two observation windows; the fresh final read is `resumed-cloud-build-latest-receipt.json`. Do not call this CI-passed or fabricate new preview-image validation. The locally built board and full registry upload are already verified; continue observing the existing remote job if needed.

**WIP prototype. Routing incomplete; NOT FABRICATION READY.** Continue this existing checkout. Linux cloud is running and tested. No Mac routing, replacement board, worktree, watcher, duplicate unchanged registry upload, supplier messages or fabrication order.

Repository: https://github.com/AnasSarkiz/tscircuit-ai-agent-remote, public main. Entry `index.circuit.tsx` delegates to `main.tsx`. Current exact native build: `dist/index/circuit.json`, **306 traces / 250 full-span vias / 190 pours / 90 native open-port errors**. Source/current build receipt: `context/build-checkpoint.json`. SHA256 `81c31f77ac0871bfc4414b0940752e4f4fe0692a62089320b409908d4a8d5315`. Matching native origin/source snapshot: `evidence/cloud-runs/final-native/`.

The independent audit measures **0 geometry violations / 0 shorts**, and all **152 authored region widths pass**, but finds **26 disconnected nets** and retains all 90 native errors. Its full gate fails. **46 errors concern J7**; the two unassigned J3 outer contacts are omitted from native counts. Do not turn measured partial results into zero-DRC or fabrication approval.

Read [current review](evidence/cloud-runs/review.md), VALIDATION.md, REQUIREMENTS.md, BOM.md, context/user-decisions.md and repository skills. Original migration handoff is preserved at `evidence/cloud-runs/historical-cloud-handoff.md`. Historical counts and unbuilt-proposal wording below older validation entries are superseded.

## Decisions and accepted implementation

Keep 50×65×1.0 mm/four-layer PCB, ≤60×75×16 mm enclosure, top assembly, ESP32-S3, one top hold-to-talk actuator, two microphones, external 8-ohm speaker, protected LiPo and USB charging/programming. J6 is optional service UART; J8 is removed in favor of M+/M− motor pads. Major placement remains conditionally frozen. C4's accepted A7 position is (-2.25,-12.65),90°; R103 now (1,18.9),0° after demonstrated PWM routing obstruction. Final mechanical/RF/FPC/harness qualification remains open.

U2 ground via is now (-3.35,-14.15) mm; actual closest foreign bottom wire gap **0.298119 mm** versus 0.20 required. Its original 0.192053 mm neighbor was CHARGER_ILIM, correcting the historical REG_PG label. Native GND top/internal pours, manual signal paths, and native internal/bottom routing regions plus ordinary vias are active. Genuine saved phase caches remain unchanged; retired USB_CC1 branch/amplifier-BCLK/display-enable replay portions are replaced by explicitly manual routes. Never manufacture a solver cache.

Manual trace `pcbPath` supports top/bottom full through transitions. Transitions to internal layers generated partial-span vias in rejected earlier trials. Internal routing uses native copper regions and explicit top→bottom vias. Audit rejects every ordinary via missing any board layer. Always validate actual geometry, width, drilled-aperture contact and physical connectivity, not source settings or endpoint markers alone.

J3: exact AKY2945/LP523450 pack drawing has red BAT+, yellow middle 10 kΩ NTC, black GND. Centre is PACK_NTC; keyed numbered outer polarity remains absent and both outer contacts stay unassigned/unrouted. Written numbered supplier evidence or physical measurement is required; do not guess.

J7: provisional BuyDisplay ER-TFT026-1 bare no-touch ILI9341 panel, not its 8051 development board. Logical SPI mapping is authored; actual contact face, pin-1 direction and portrait FPC fold/mating pose remain unqualified. Contact-dependent fanout stays deferred; safe upstream circuitry may continue. Top GND excludes the contact strip. Supplier references and mechanical allocations remain in the original A4/A7 evidence.

## Validated capabilities and remaining gates

TypeScript and maintained-source formatting pass; routing regressions 17 pass; board tests **42 pass / 2 fail**, retaining fabrication/native-schema failures. Required five electrical/placement checks pass. Standard CLI copper-free placement build passes. Current direct native placement fixture uses the same renderer as routed JSON; the CLI adds empty metadata to native pads.

Current routed native API render completes in 180.20 s/1.68 GB peak RSS. Full routed CLI build, bitmap shorts and snapshot reached time budgets and are incomplete. Gerber shorts/export fail `Unsupported shape polygon`; no fabrication ZIP was generated. Strict schema has169 failing elements. U16/U27 each lack16 native pill-paste records; official core2091 investigation still does not fix these. Imported definitions/pins/assets and locked dependency versions must not be patched or checks relaxed. Current/BOM/CPL/stock, USB/speaker SI and final mechanical/stencil checks remain open. No physical hardware evidence exists.

Use `evidence/cloud-runs/final-copper-audit.json` for exact remaining real-port islands. Independent open wiring includes USB, supply leafs/GND islands, upstream LCD/reset, amplifier enable/speaker pair and microphones. Conservative planner failures are not proof of impossibility. Rejected priority/multilayer trials remain evidence, not accepted copper.

## Reusable cloud commands

```sh
cd /workspace/tscircuit-ai-agent-remote
source scripts/cloud/env.sh
python3 scripts/cloud/verify_checkpoint.py
python3 scripts/cloud/run_with_budget.py --seconds 300 --log /tmp/native-render.log -- bun evidence/a7-routing-2026-10-05/capture-native.tsx /tmp/native-render
python3 scripts/cloud/run_with_budget.py --seconds 120 --log /tmp/placement-fixture.log -- bun scripts/routing/capture-placement.tsx dist/placement/circuit.json
python3 scripts/cloud/run_with_budget.py --seconds 120 --log /tmp/copper-audit.log -- python3 scripts/routing/audit-copper.py dist/index/circuit.json /tmp/copper-audit.json
```

All heavy operations run sequentially through the single-lock memory/time supervisor. Audit exit1 is correct while any native error/disconnection remains. Keep Bun1.3.9/core2090/CLI2237/capacity958 and the lockfile. Current dependencies support development; clean frozen install remains HTTP403-blocked at api.github.com until the saved environment network change is applied. No credential values are needed in chat.

The CLI virtual filesystem eagerly reads diagnostic JSON across the checkout. Raw native events exhausted memory. `scripts/cloud/archive-native-events.py` losslessly archives verified original event/start bytes; per-capture receipts give `tar -xzf native-events.tar.gz` restoration instructions. Preserve full actual events/JSON/snapshots before changes, and avoid retaining huge duplicate raw events during CLI builds. Archives are directly committed; do not discard failed evidence.

GitHub WIP pushes with matching generated JSON are authorized. Registry publication/retries remain deferred; no upstream issue messages, extra agents, watcher activity, orders or invented physical-test claims. Review exact publication receipts before stating a remote update succeeded.
