AnasSarkiz/tscircuit-ai-agent-remote/context/user-decisions.md

Implementation follow-up, 2026-10-08 (not a new human decision): WIP .10 moves
only genuine C81/R93 to provide a measured 1.442790 mm top supply / .599976 mm
top ground U5 bypass, .30 mm wide with no bypass via. Zero measured shorts and
clearance violations, all 9,813 previous contacts preserved, all genuine
identities/assets retained. Full-board gates remain failed: 50 native J7/U27
errors / 12 assigned open nets plus J3 unassigned outer contacts, 169 schema
failures, 15 actual UI style issues and width/paste/export/stock/mechanical
qualification. Latest user target remains zero DRC and zero missing connections;
no lowered threshold or fabrication approval. Actual .9 cloud job now completed
without a user-code job error. Fresh .10 inventory only confirms 12/43 identities
covering one board, U1/D2 zero public buyability and 29 unknown HTTP503 results.
Read evidence/microphone-local-bypass-2026-10-08/review.md. Public implementation
3d88ca2 / tsci .10 release d17c1129 have all128 files and exact native preview
verified. Both automatic .10 cloud jobs failed platform sandbox initialization
before executing source; any supported retry remains a separate observation.
Latest official schema .521 still has169 failures on this exact native. Draft30
startup saving/readback preserves previous settings and does not activate the
environment. Standing push authority continues; requested centered landscape
LCD remains unimplemented.

Implementation follow-up, 2026-10-07 (not a new human decision): genuine
J6/C160389 direct SH3 UART and the local 0.8 mm bottom supply bypass are
implemented and qualified as WIP .9. Actual cable/programming operation is
untested. Other purchased poses remain. Zero measured shorts/geometry
violations does not mean full zero DRC: 50 display errors / 12 open nets,
schema/style/paste/export/width/stock/mechanical gates remain. The centered
2.8-inch LCD request remains active and unimplemented. Read current checkpoint
and evidence/programmer-direct-uart-2026-10-07/review.md. Standing public
GitHub/tsci publication authorization remains in force. The implementation is
now public at GitHub 1642750 and tsci .9/f520e705; all 128 files and the native
preview are exact. Cloud source build success remains unverified. Draft29
startup/settings saving does not apply/publish the environment.

Latest explicit request, 2026-10-07, user-pasted file_00000000cb0881f4952a48a1ad747186:
**Replace the unfinished ER-TFT023-1 plan with a BuyDisplay approximately2.8-inch
LANDSCAPE display**, preferably ER-TFT028A3-4 or an exact-qualified close variant.
PCB approximately50×65mm/front approximately60×75mm;body approximately69×50mm,
active approximately58×43mm. Keep the body centred on the board. In the finished
landscape device,FPC must exit left/right;move J7 to the corresponding PCB edge
using the real manufacturer drawing. Verify pitch,thickness,face,pin 1 and minimum
bend radius;no guessed folds,antenna overlap or reuse of an incompatible pinout.
Move interfering parts while preserving RF/electrical constraints,review backlight,
then actually implement/reroute and run complete connectivity/DRC. Do not stop at
an image-only proposal. This supersedes the earlier 2.3-inch selection and coverage
relaxation. ER-TFT028A2-4 exact primary mirror is reviewed as a candidate only:
69.3×50.2mm landscape body,ILI9341,common-cathode backlight,26.7mm tail. It overlaps
the current RF keepout and has no published minimum bend radius. Final J7 mating
and poses remain unassigned;no PCB replacement/routing is accepted. See
`evidence/display028-integration-2026-10-07/review.md`. The unaccepted 2.3-inch staged
source is preserved separately and restored to exact publicHEAD. No orders,
genuine-import patches,check suppression,watcher,subagents or other-chat messages.

Independent implementation follow-up, 2026-10-07: the canonical rounded-pad paste
generator is fixed and tested in upstream source, with genuine 20-pad U14 and
34-pad U16/U27 coupons. This is an unreleased runtime change, not a new human
decision or active board repair. All local links are removed. Board source,
placement and copper remain unchanged; exact LCD/RF/flex gates still precede
J7 placement and routing. See `evidence/core-pill-paste-fix-2026-10-07/review.md`.

Historical 2.3-inch decision below is superseded by this request.

Latest explicit display decision, 2026-10-07: **“Accept the 2.3-inch display
(Recommended)”**. Select no-touch ER-TFT023-1 for the next revision, and relax
the earlier ≥80% display-body coverage target for this panel. The uploaded exact
ER-TFT023-1 primary PDF is now available and reviewed; it confirms ILI9342,
50 contacts at 0.5 mm, and a right-side flex after portrait rotation. This approval
does not verify a folded mating arrangement or authorize guessing its contacts.
The review finds required SPI IM0-high / mode 1111, and a nominal placement
proposal, with final mating and U14 supplier pin-1 discrepancy still unresolved.
No board source/native replacement has been accepted; preserve the current WIP.
See evidence/display023-primary-review-2026-10-07/review.md.

Latest explicit browser approval, 2026-10-07: **"Approve this CA import"** for
the existing environment proxy CA into Chromium's `/home/agent/.pki/nssdb`.
The exact import completed. Fingerprints show this CA was already trusted under
another nickname; actual browser NSS initialization was blocked by read-only
sandbox access. Approved browser execution restored normal TLS, then encountered
a real supplier Cloudflare challenge whose required host is proxy-denied.
The 17-domain draft preserves supplier/search hosts and adds
`challenges.cloudflare.com`; saving the draft is not runtime application or
environment publication. Do not ask for the same CA approval again. Keep TLS
verification and the inherited proxy intact. The actual schematic UI analysis
now ran and reports 14 unresolved issues; no passing style/DRC/order claim.

Latest continuation, 2026-10-07: search for the replacement display directly
on the website and other published sources instead of asking the user to supply
another PDF. Continue independently accessible review; actual network and
automatic approval-review denials remain external blockers when unresolved.
The earlier browser CA-import question has now been explicitly answered above.

Latest display request, 2026-10-07: reject the ER-TFT026-1 bottom-tail panel
because it does not connect mechanically to the current right-side J7. Review
https://www.buydisplay.com/spi-2-3-inch-tft-lcd-touch-screen-display-320x240-ili9432-controller
and find a matching genuine JLCPCB connector. This authorizes a qualified
display/connector replacement and supersedes the earlier conditional display
selection. It does not confirm the new product's pinout, contact face or fit.
Review the exact replacement-panel drawing before changing the board; the
uploaded ER-TFT026-1 datasheet belongs to the rejected old display. Existing
native copper remains the accepted WIP checkpoint while selection is pending.

Latest continuation: continue toward zero DRC, including manual routing. The goal remains fully connected, correctly sized, fabrication-qualified copper. Keep checks intact, verify every accepted repair against previous connections and publish matching WIP source/native after completed steps. Do not guess unverified J3/J7 contacts or turn partial geometry results into fabrication approval.

Latest request, 2026-10-06: fix the connection errors autonomously and keep the matching tscircuit source/native updated. Repair independently verified interfaces without per-issue approval, preserve actual connection/width/DRC evidence and report unresolved gates honestly. Do not guess J3 outer polarity or J7 physical mating, alter genuine imports or solver caches, hide native errors, place an order, resume the watcher or send other-chat messages.

Latest six-point request,2026-10-06: use the native USB-C standard connector
schematic for J1, run UI and CLI style analysis, verify current JLCPCB stock,
require ordinary through vias with0.30mm holes/0.45mm pads, and route high-current
paths on the outer PCB layers (explicit user clarification). The J1 symbol change
and additional canonical role aliases are explicitly requested; preserve the
original numbered physical contacts, imported footprint and manufacturer model.
Saved solver output remains immutable; any dimensional replay adaptation is
explicitly authored and must be independently measured. Preserve unresolved
J3/J7 mating and fabrication gates; no orders or invented stock/hardware evidence.

Latest request, 2026-10-06: add text in the schematic explaining each component.
Use readable native schematic annotations and paired A4 guide pages where
needed; preserve electrical source, PCB layout/routing and existing fabrication
gates. Publish the annotated revision under the standing public authorization.

Latest implementation request,2026-10-06: autonomously fix the review issues
and keep tscircuit updated. This explicitly supersedes historical registry
upload deferrals. Continue independent corrections without per-issue approval;
preserve actual source/copper evidence and fabrication gates. No guessing
battery polarity or display mating, no orders or physical-test claims.

# Accepted human decisions and continuation authority

Latest review request, 2026-10-06: check placement, part suitability, current
JLCPCB availability, real nets and issues, and programming using
https://tscircuit.com/tscircuit/standard-jst-programmer#3d. Its public v0.8.0
UART J5 has 3.3V TX/GND/RX and supports the ESP32-S3 UART bootloader conditionally.
Current six-pin J6 requires a reviewed three-to-six adapter, separate target
power, matching programmer firmware and manual BOOT/RESET. This is not direct
SWD compatibility or hardware-tested programming. Preserve native USB access.
Measured remote MCU/microphone bypass placements now block final electrical
placement acceptance despite passing overlap checks. See
evidence/board-programmer-stock-review-2026-10-06/review.md. Current supplier
lookup is proxy-blocked; historical stock is not current availability.

Latest request, 2026-10-06: independently verify current actual connections,
shorts/DRC, every trace width, real components/pin assignments and whether the
board is ready to order. Preserve real failures and do not approve fabrication
without all current gates passing.

Latest clarification: use manual tracing together with Freerouting for remaining
connections. Continue autonomously within the existing board requirements;
accept only actual native copper that passes clearance/short/width/connectivity
checks. Tool completion or saved output is not routing/fabrication approval.

Latest routing continuation, 2026-10-06: proceed with manual tracing or a qualified
remaining-trace router, and try tscircuit bus-lane/fanout solvers where useful.
Preserve existing copper, manufacturing rules and actual native solver evidence;
accept changes only after independent clearance, short, width and connectivity
checks. The requested Pipeline9 SRJs and upstream bug report were delivered in
https://github.com/tscircuit/tscircuit-autorouter/issues/2878.

Latest routing request, 2026-10-05: use Pipeline9. Explicitly select the supported `autorouterVersion="beta_pipeline9"` and preserve actual native solver events before accepting new routes. Keep the existing zero-shorts, geometry and full-connectivity requirements; do not interpret this request as approval to guess J3 outer polarity or J7 contact orientation.

Latest request, 2026-10-05: "push it to tsci" explicitly authorizes publishing the current engineering WIP to tscircuit, superseding the earlier registry-upload deferral. Preserve all imported models and fabrication blockers; do not represent partial or unauthenticated publication as success.

This is a curated decision record, not a full conversation export. Original supplied briefs are in user-requests/ and current artifacts/validation supply exact engineering evidence.

- Continue the existing handheld AI remote to prototype fabrication readiness; do not restart. No fabrication order or invented physical tests.
- Rounded enclosure, dominant front display, one top-edge hold-to-talk button. Top PCB assembly. ESP32-S3 Wi-Fi/BLE/USB, dual digital microphones, external speaker, haptic function. J8 haptic JST removed in favor of direct motor pads. J6 UART optional; USB programming is required.
- PCB fixed 50 × 65 mm. Current accepted A7 thickness 1.0 mm, four layers. Enclosure maximum 60 × 75 × 16 mm; use latest A7 mechanical evidence, not earlier 15 mm proposal. Keep battery/display/metal/wiring outside the antenna region. Major placement frozen conditionally; documented C4 passive move accepted.
- Display bought from BuyDisplay, not JLCPCB: provisional ER-TFT026-1 no-touch with integrated ILI9341 controller, not the 8051 development kit. Physical display coverage target ≥80% of PCB; projected overlap 82.712%, tolerance allocation 81.737%. This does not prove final FPC fit or usable pixel coverage.
- Protected rechargeable 1S battery AKY2945 / LP523450. Supplier drawing: red BAT+, yellow 10 kΩ NTC in centre, black GND, JST PHR-3 2 mm. J3 centre must be PACK_NTC. Outer contact numbering NOT confirmed: do not guess or route either outer contact until keyed numbered supplier confirmation or physical measurement.
- J7 display connector orientation/face/pin1/short-FPC fold still needs exact physical/vendor evidence. Continue independent and upstream routing; no speculative contact-dependent fanout.
- Genuine JLC imports for board electronics; no custom/edited imported symbols or footprints except expressly allowed C370970 and C5656610 0.60 mm acoustic hole. Alternatives must be genuine imports with pin/land/stock review. Current resistor substitution C22548 → C21190 and C105588 → C22775; verify BOM quantities/current stock before assembly.
- Both board GitHub repository and tscircuit package must be public, with generated circuit.json included. Official compressed registry upload was explicitly authorized; A7 brief currently defers registry upload retries and requests routing progress. Migration Git push is authorized and needed for Cloud.
- Saved routes must preserve real native events/full JSON/per-phase paths before moves and demonstrate replay. Manual native paths allowed, clearly separated from genuine solver outputs. Incomplete/time-killed solver runs are NOT accepted routes.
- Stop reporting issues to another chat. Background automation remains paused; do not resume it. No extra threads/agents requested.
- Latest instruction: stop Mac routing due to memory exhaustion; set up this repo for Codex Cloud with all relevant continuation context. Carry over current accepted checkpoint and unbuilt proposals separately. Linux setup/resource supervisor limits one heavy process at a time and records failures truthfully.

Engineering status remains partial routing, pending copper/DRC/fabrication review. See CLOUD_HANDOFF.md for current exact build/source/cache hashes, blockers, next actions and commands.
