AnasSarkiz/tscircuit-ai-agent-remote/evidence/display023-routing-2026-10-07/review.md

# Superseded 2.3-inch staging — not accepted

This directory preserves the actual uncommitted attempt to implement the earlier
centred ER-TFT023-1 request. The later uploaded 2.8-inch landscape request supersedes
it. Every staged electrical/placement source was archived before restoring the
exact public HEAD source. The accepted routed native JSON was never overwritten.

The first canonical copper-free placement capture reports 18 native courtyard
errors. The later v4 proposal has zero intersections among 125 independently
transformed courtyards, but was never applied to the board or checked by a final
native placement build. Neither result is a completed placement/routing pass.
Retired-path source in the archive is an abandoned partial staging step.

The initial genuine exact-import download returned 16-byte `Domain forbidden`
model bodies despite CLI exit 0; these were rejected. The no-download source had
a 4.05 mm model origin that did not align with the existing normalized assets.
A later real canonical import with valid downloads resolves pin-1 metadata and
CAD alignment, but its 20 pill pads lack paste. See
../display028-integration-2026-10-07/u14-canonical-import/qualification.json.
No imported component was hand-patched or accepted with fabricated geometry.

The cloud setup rerun completed frozen installation and supervisor smoke checks.
Its new smoke outputs are retained under setup-rerun-smoke before restoring the
previously tracked outputs. Current design status and remaining blockers are in
../display028-integration-2026-10-07/review.md.
