AnasSarkiz/tscircuit-ai-agent-remote/evidence/blocker-recheck-2026-10-03-1357/usb/schematic-a4.pdf

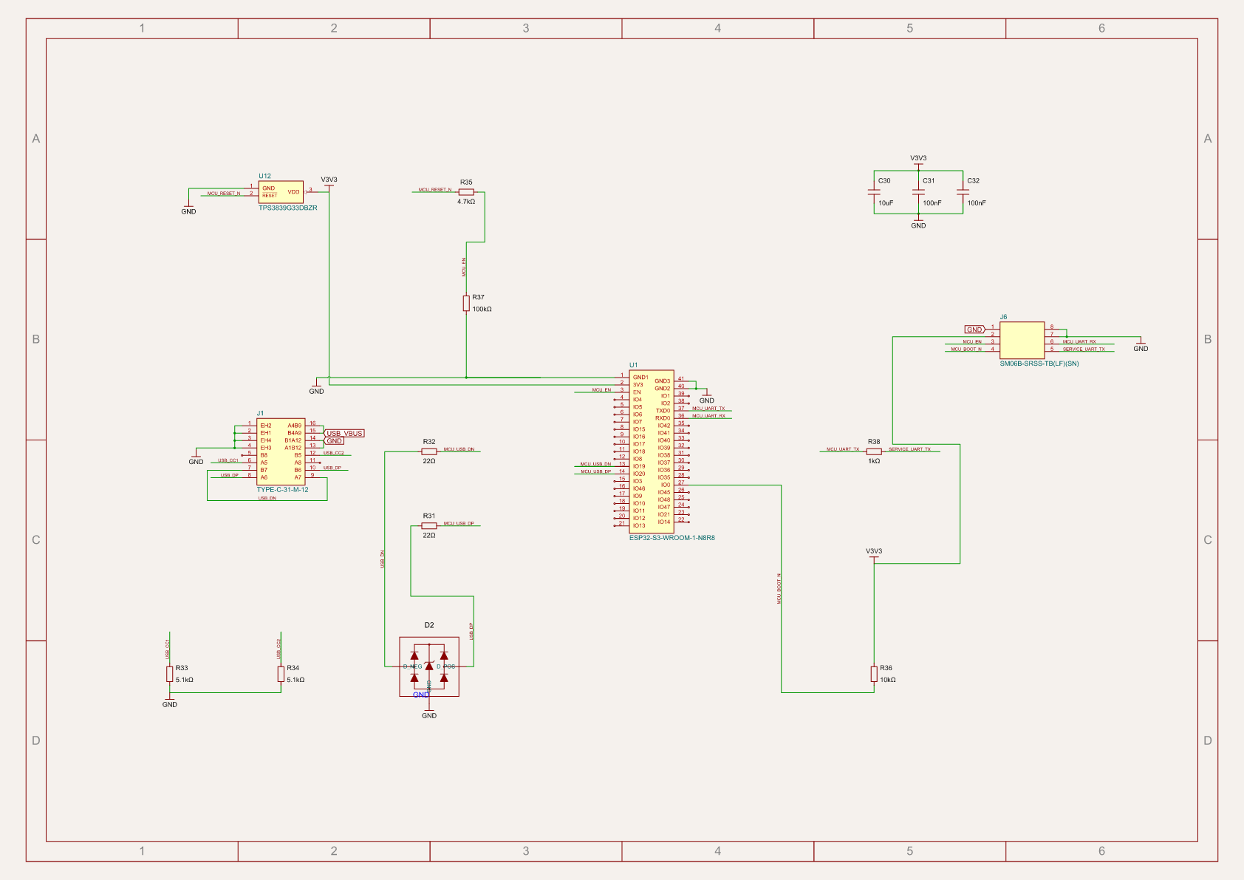
[picture p9: page 1]
