AnasSarkiz/tscircuit-ai-agent-remote/evidence/a3-routing-2026-10-04/buydisplay/afc07-s50eca.png

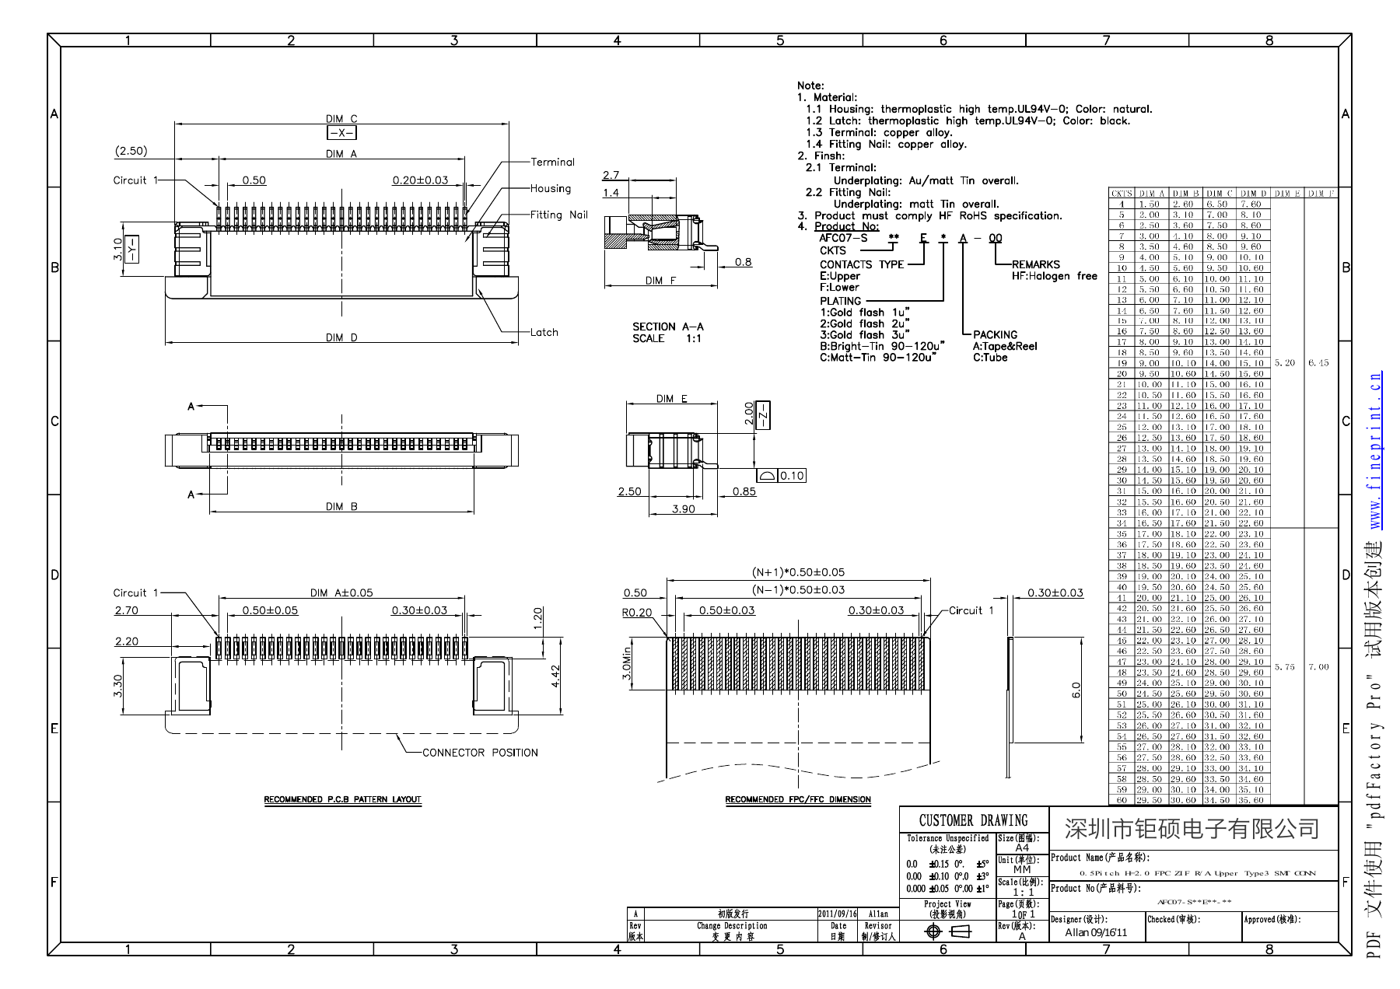
evidence/a3-routing-2026-10-04/buydisplay/afc07-s50eca.png
