AnasSarkiz/tscircuit-ai-agent-remote/evidence/a3-routing-2026-10-04/buydisplay/er022-drawing.png

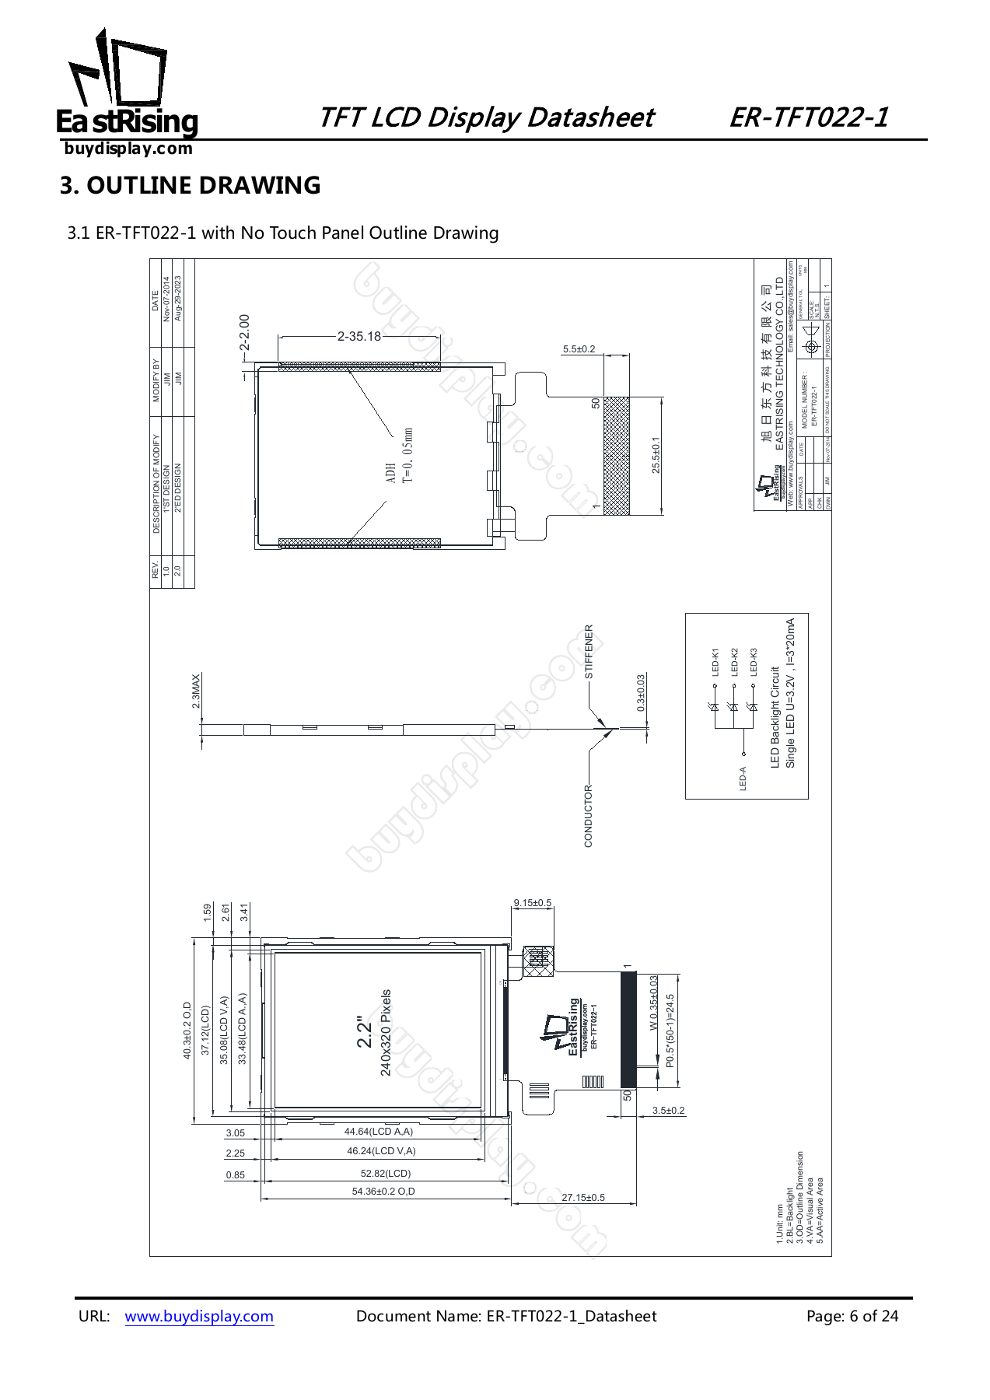
evidence/a3-routing-2026-10-04/buydisplay/er022-drawing.png
