AnasSarkiz/tscircuit-ai-agent-remote/evidence/a3-routing-2026-10-04/buydisplay/er024-drawing.png

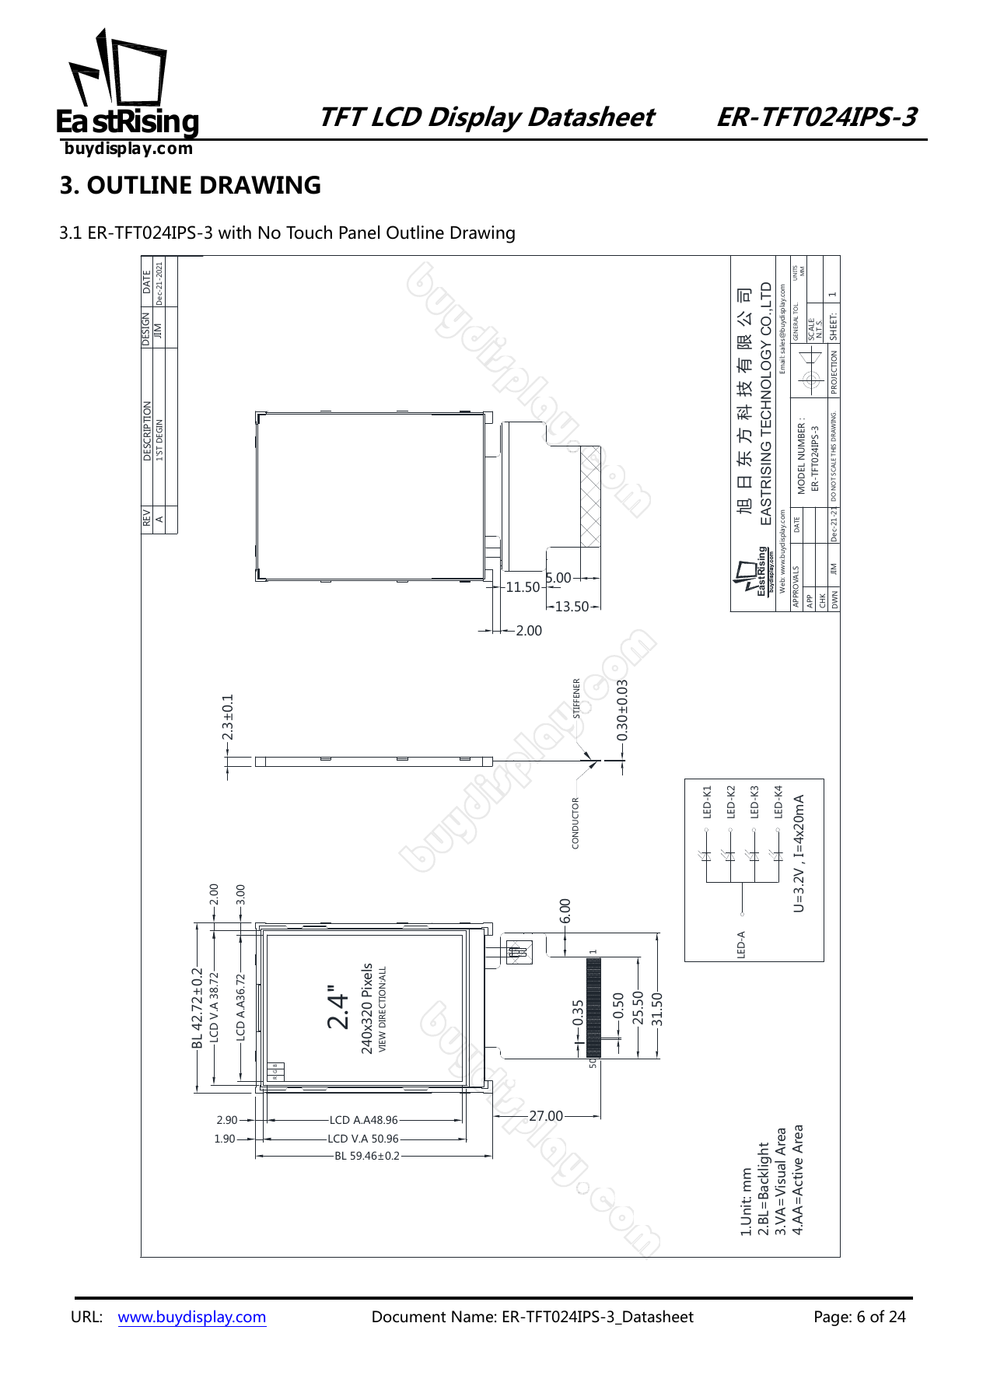
evidence/a3-routing-2026-10-04/buydisplay/er024-drawing.png
