AnasSarkiz/tscircuit-ai-agent-remote/evidence/a3-routing-2026-10-04/buydisplay/ercon50.png

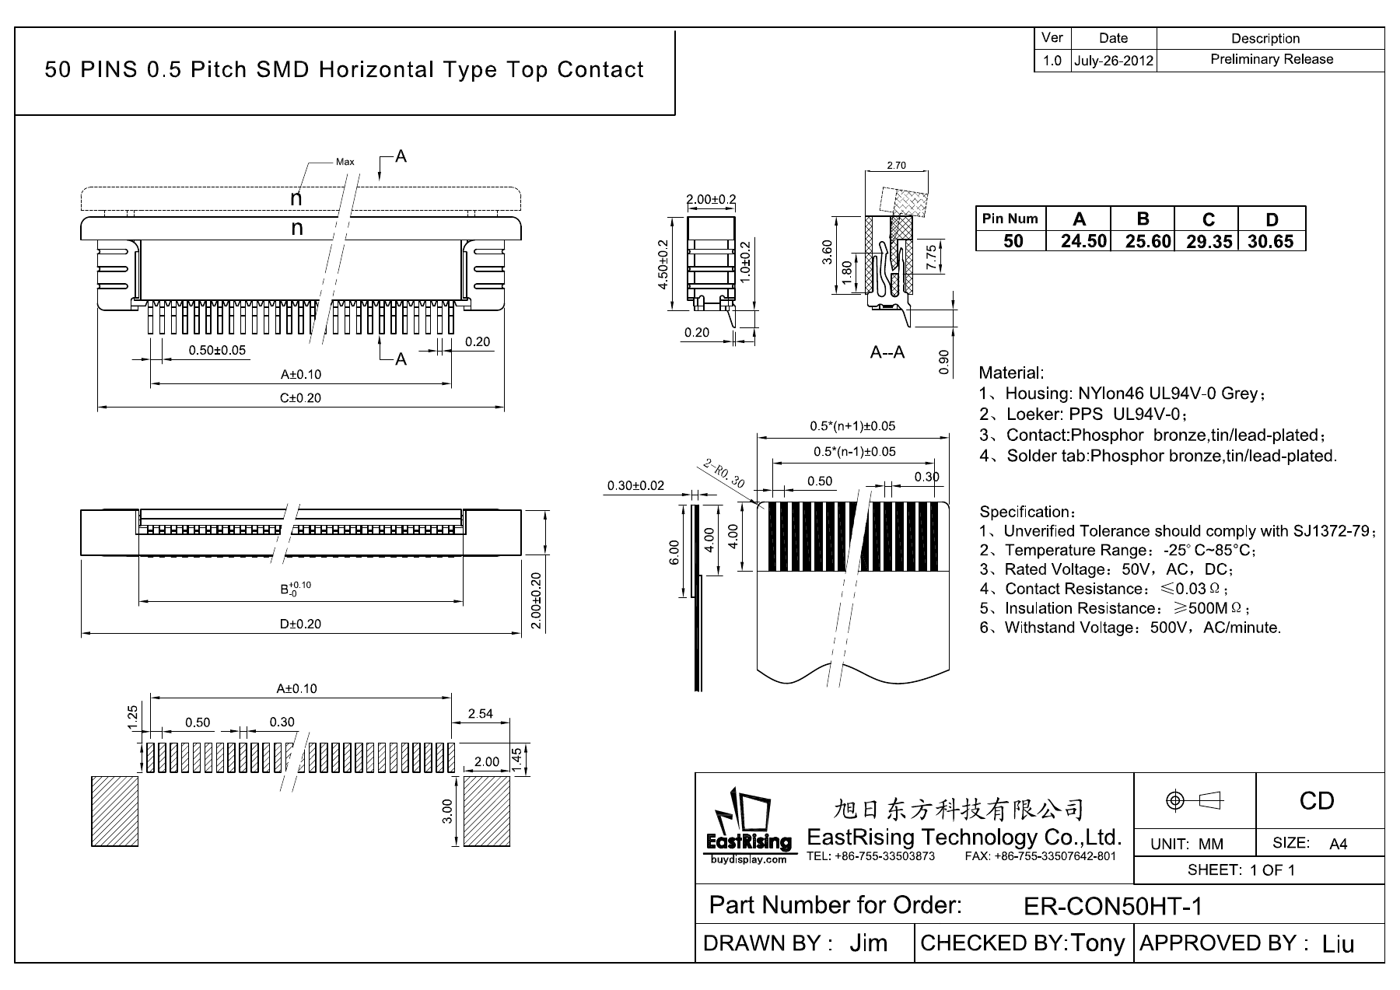
evidence/a3-routing-2026-10-04/buydisplay/ercon50.png
