AnasSarkiz/tscircuit-ai-agent-remote/evidence/a3-routing-2026-10-04/buydisplay/module-drawing-page42.png

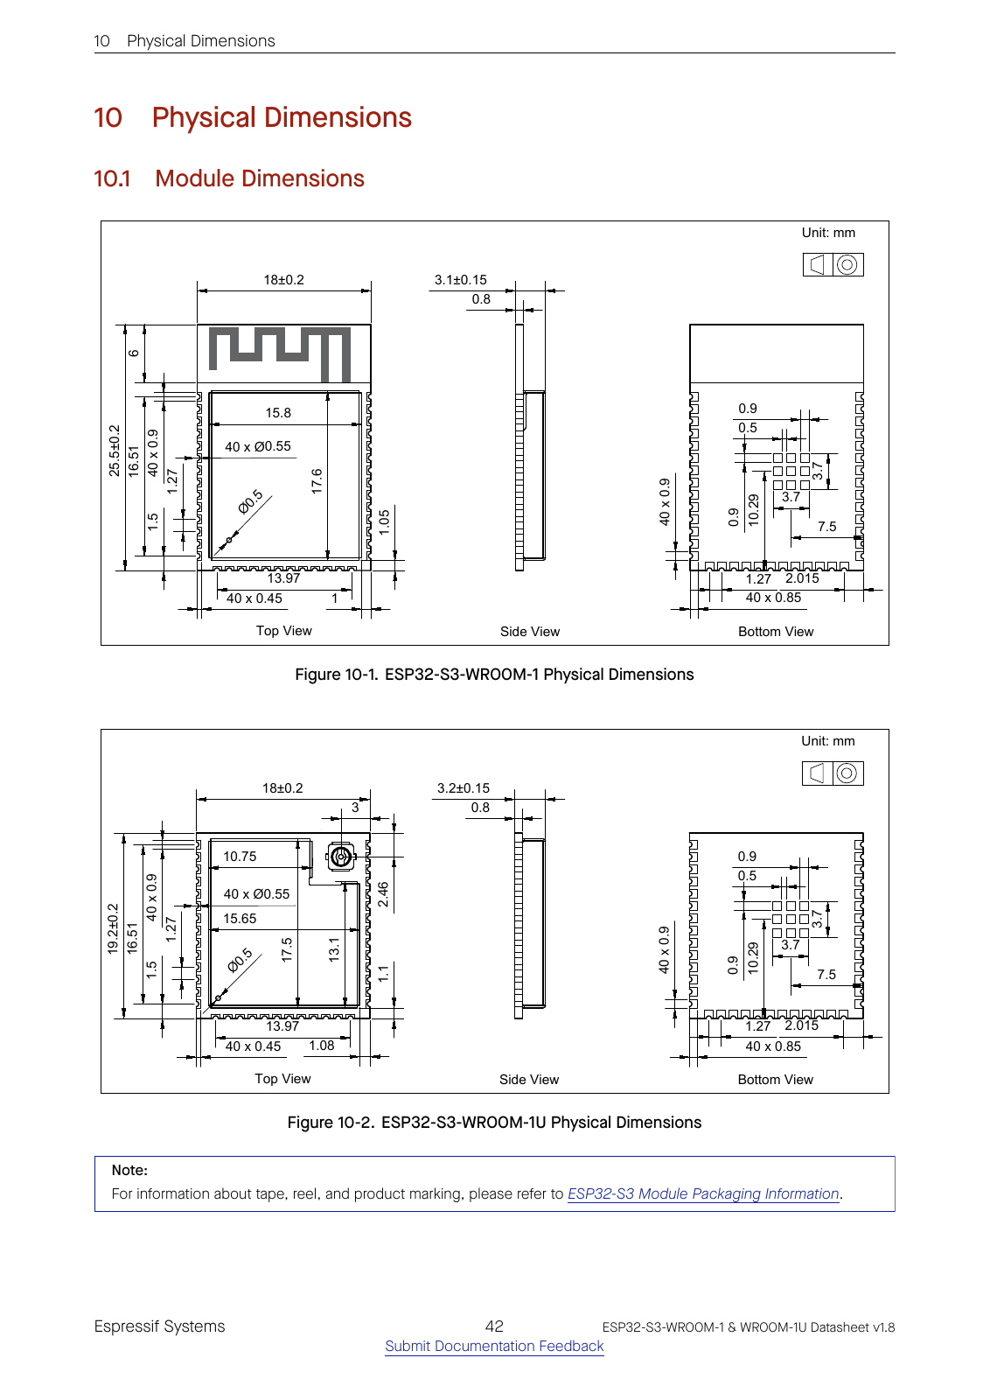
evidence/a3-routing-2026-10-04/buydisplay/module-drawing-page42.png
