AnasSarkiz/tscircuit-ai-agent-remote/evidence/a3-routing-2026-10-04/esp32-antenna.png

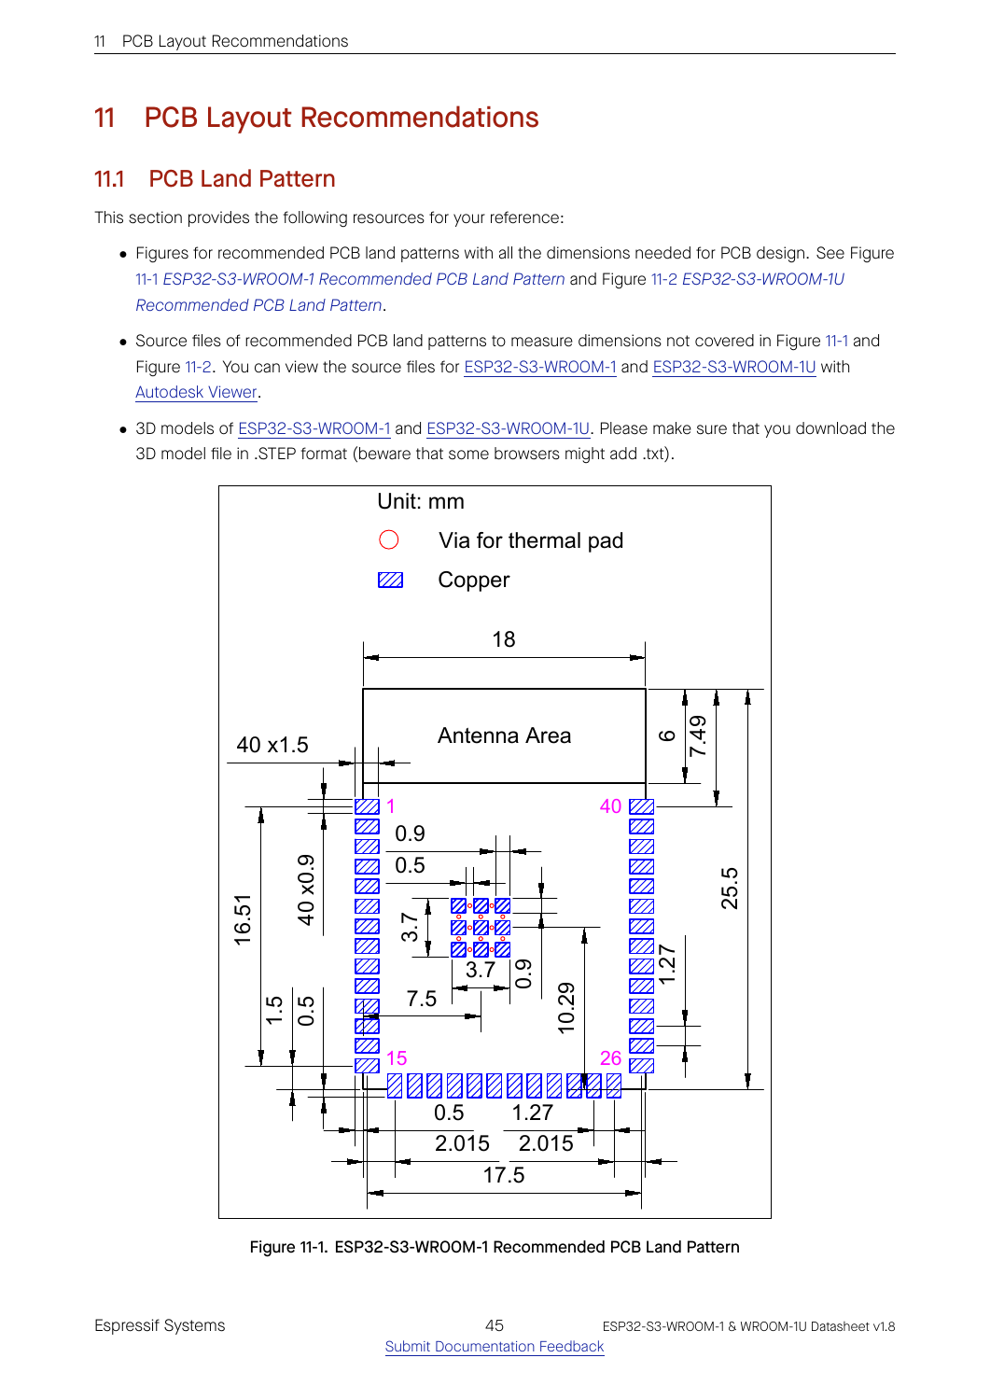
evidence/a3-routing-2026-10-04/esp32-antenna.png
