AnasSarkiz/tscircuit-ai-agent-remote/evidence/a3-routing-2026-10-04/esp32-land.png

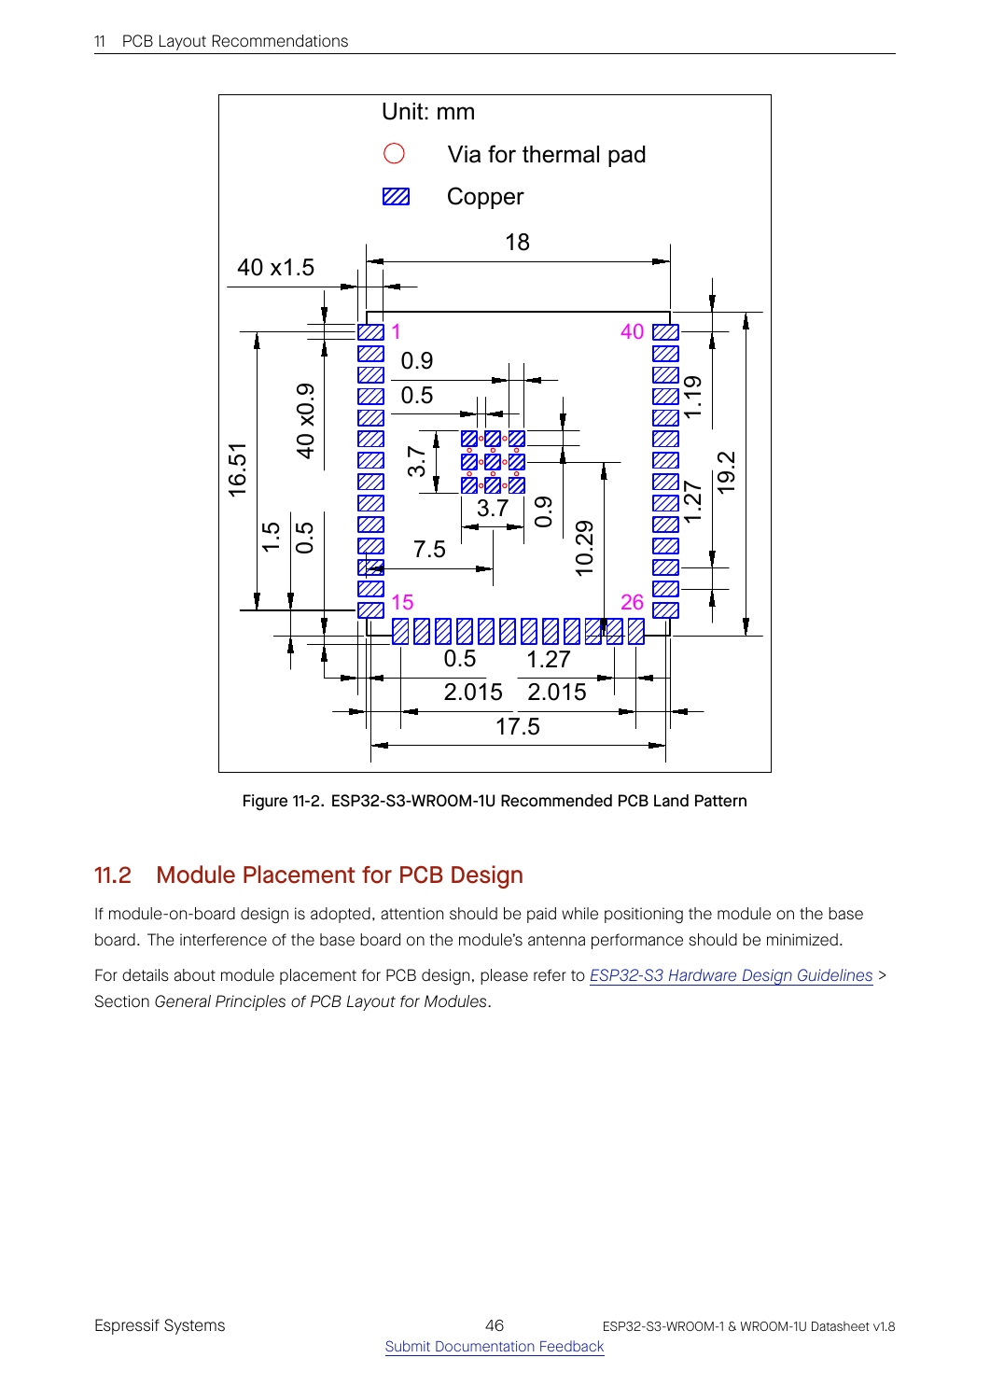
evidence/a3-routing-2026-10-04/esp32-land.png
