AnasSarkiz/tscircuit-ai-agent-remote/evidence/a3-routing-2026-10-04/jst-ph-mated.png

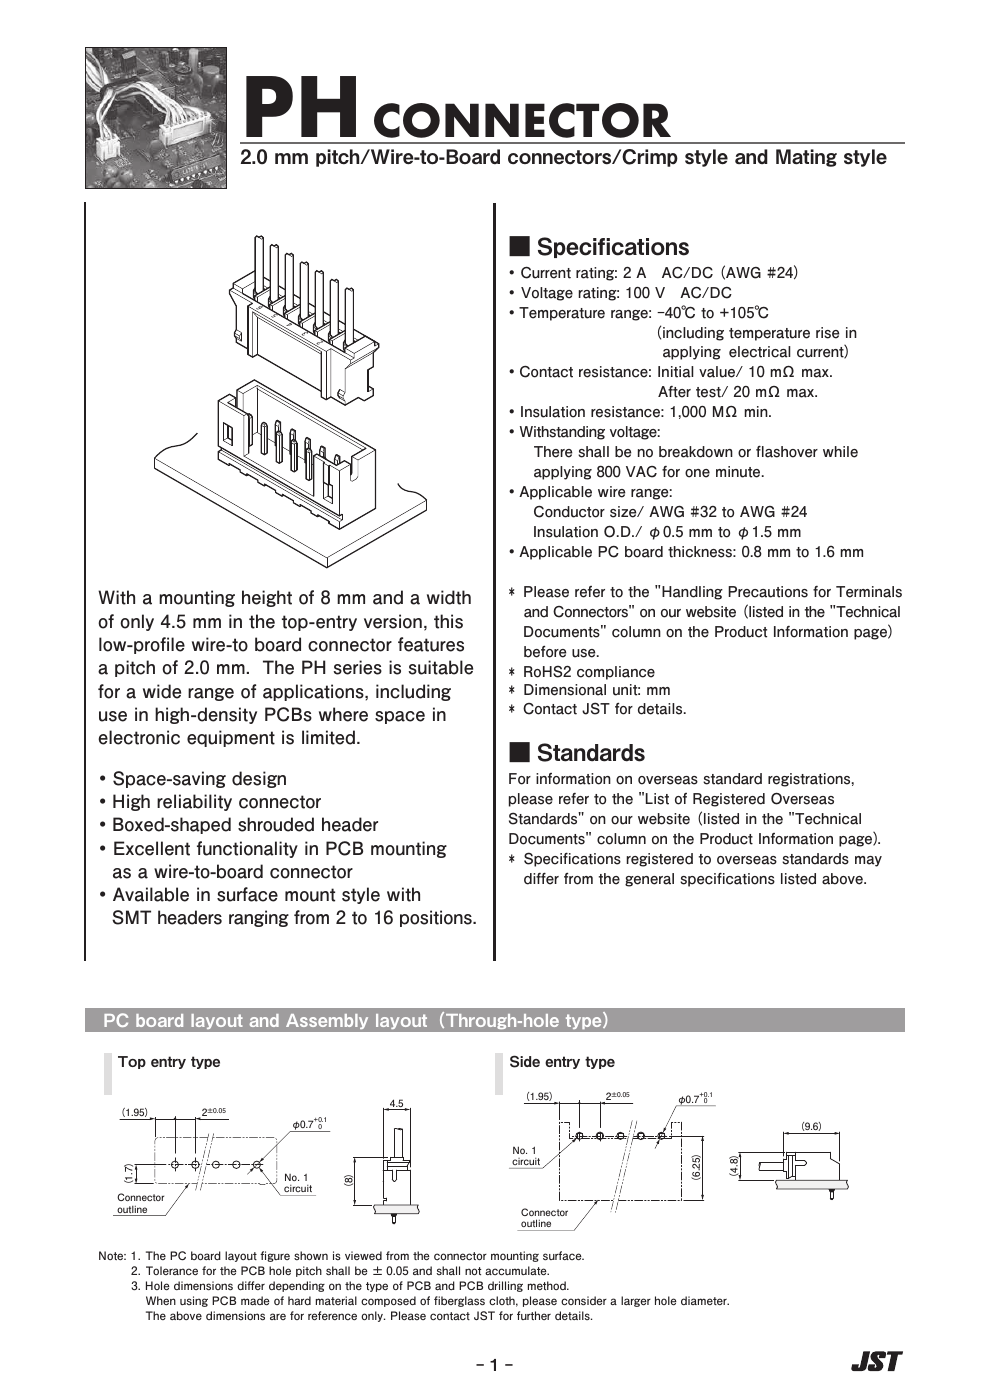
evidence/a3-routing-2026-10-04/jst-ph-mated.png
