AnasSarkiz/tscircuit-ai-agent-remote/evidence/a3-routing-2026-10-04/tps63802-layout-28.png

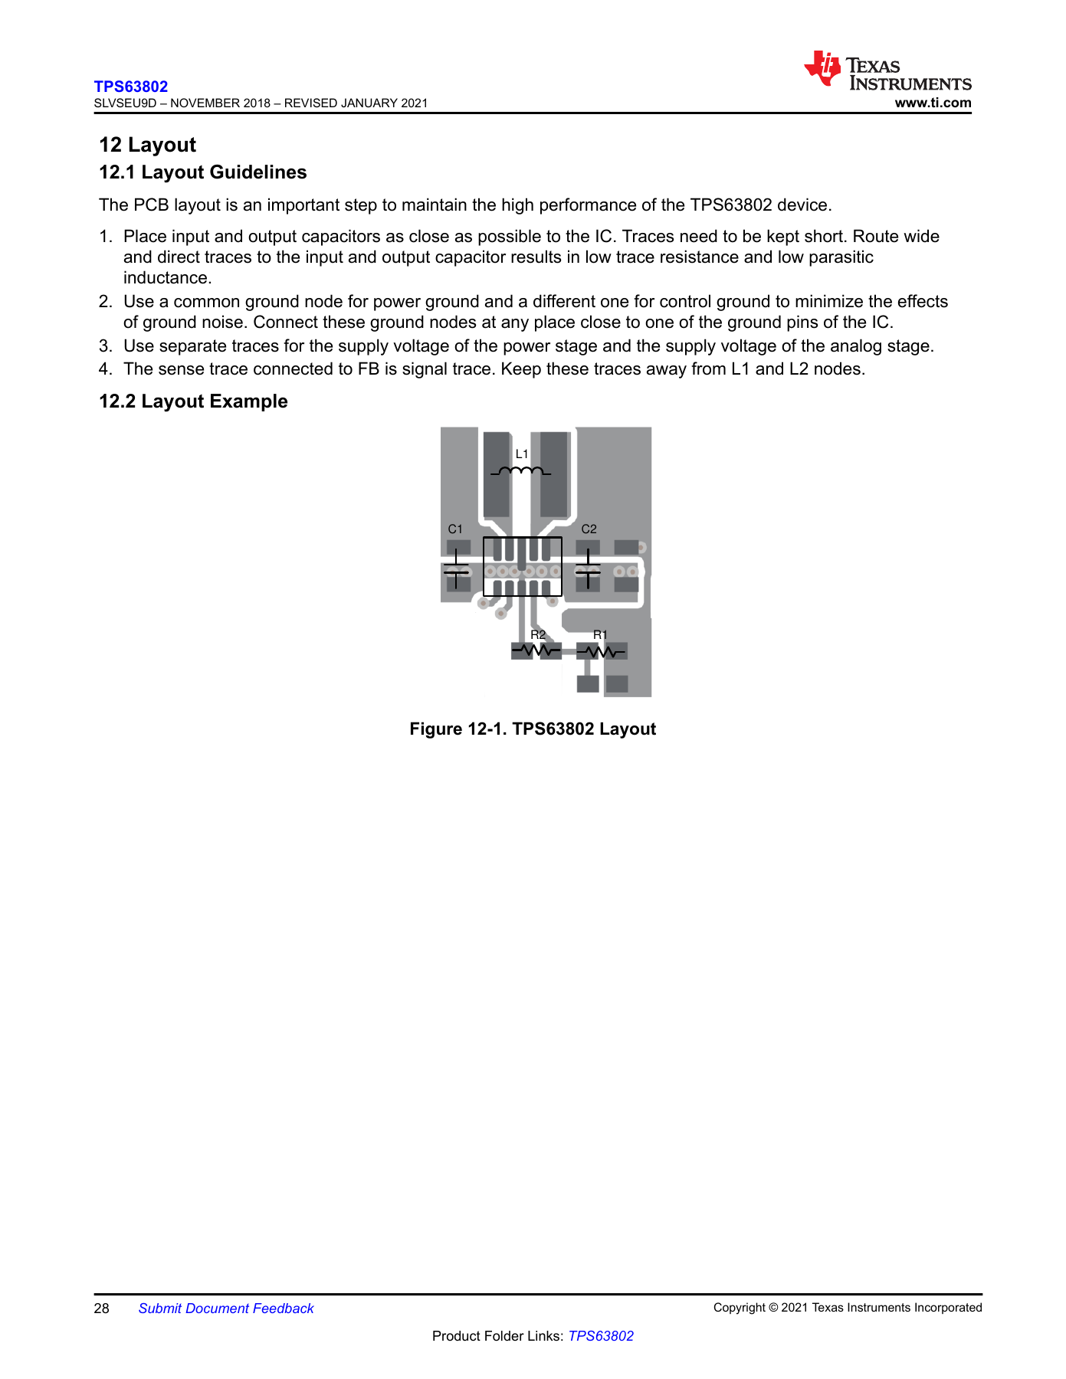
evidence/a3-routing-2026-10-04/tps63802-layout-28.png
