AnasSarkiz/tscircuit-ai-agent-remote/evidence/a4-display-coverage-2026-10-04/jst-side-entry.png

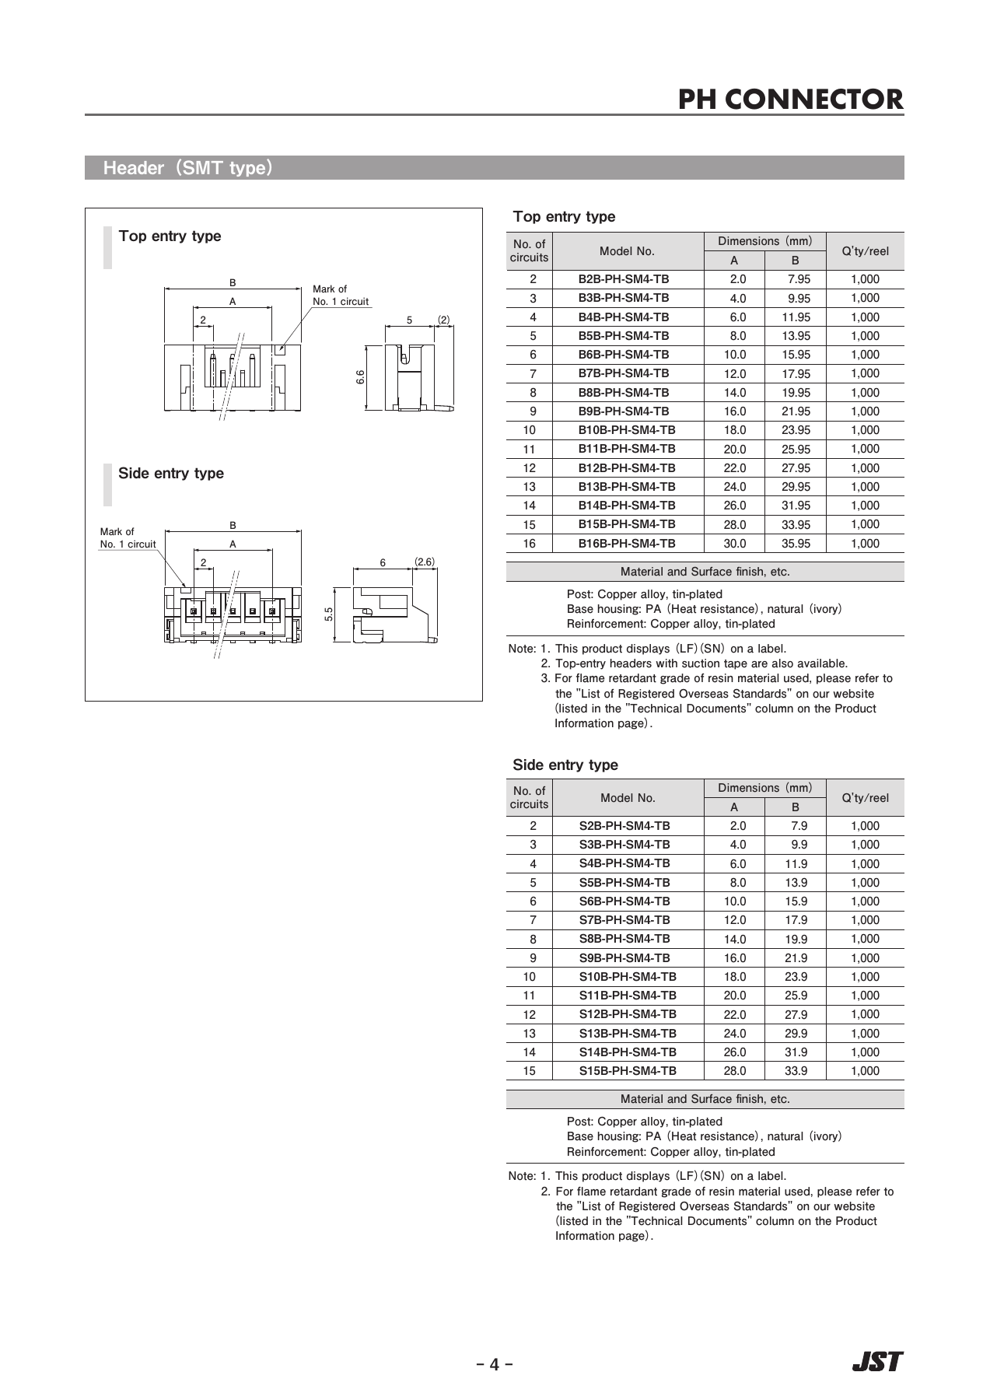
evidence/a4-display-coverage-2026-10-04/jst-side-entry.png
