AnasSarkiz/tscircuit-ai-agent-remote/evidence/a4-placement-gate-2026-10-04/placement.png

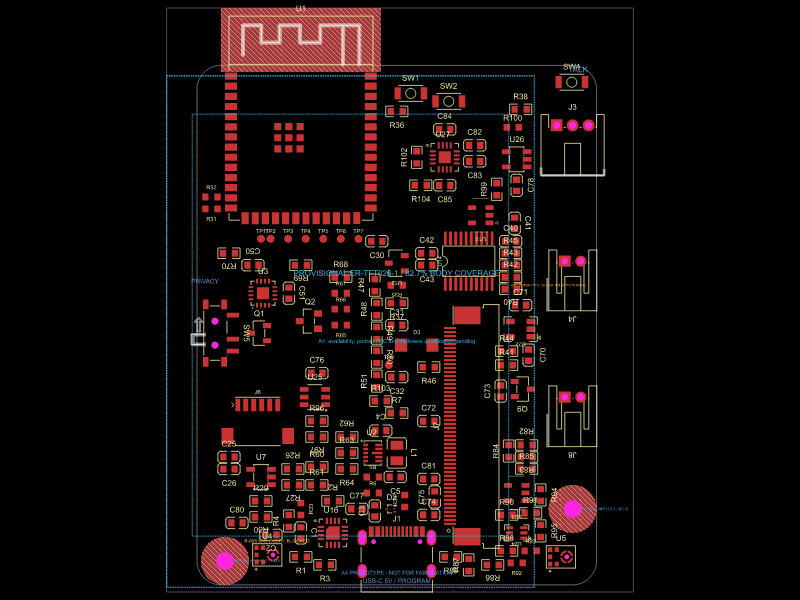
evidence/a4-placement-gate-2026-10-04/placement.png
