AnasSarkiz/tscircuit-ai-agent-remote/evidence/a5-connector-simplification-2026-10-04/inner1.png

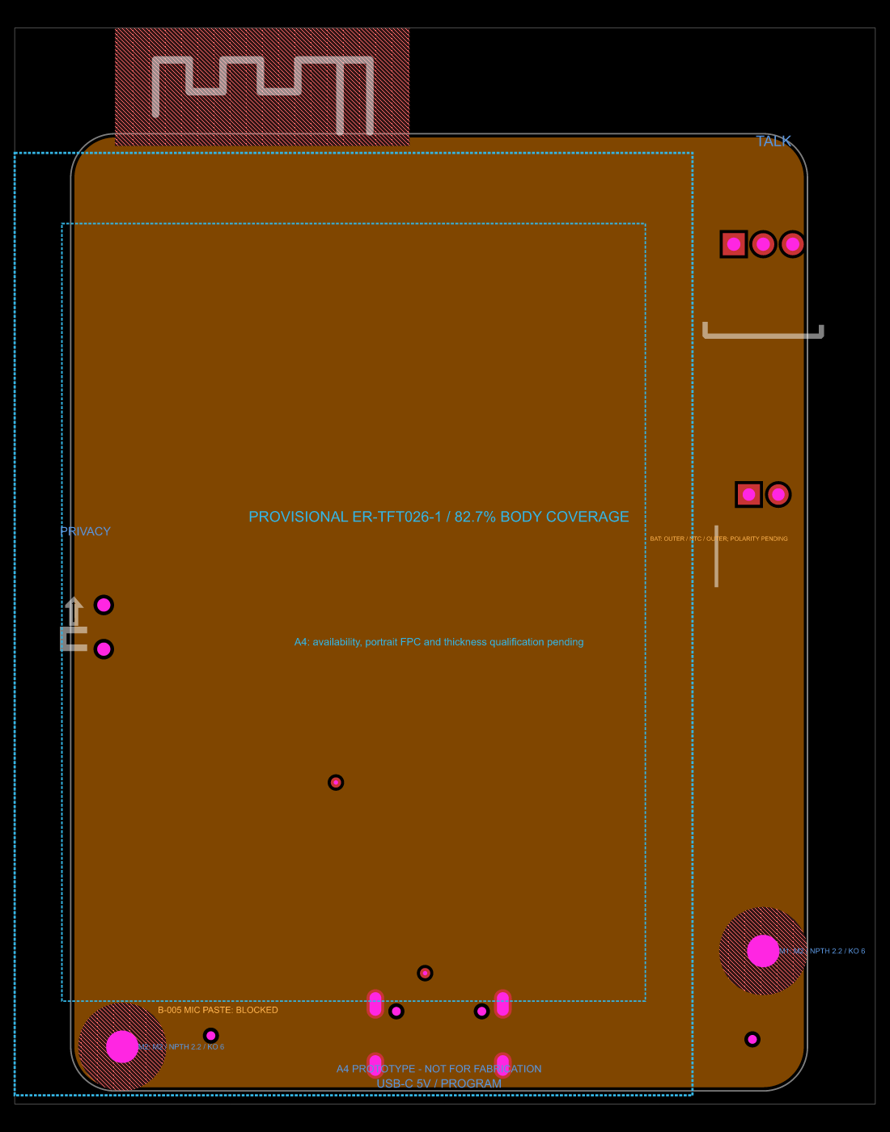
evidence/a5-connector-simplification-2026-10-04/inner1.png
