AnasSarkiz/tscircuit-ai-agent-remote/evidence/a5-connector-simplification-2026-10-04/schematic.png

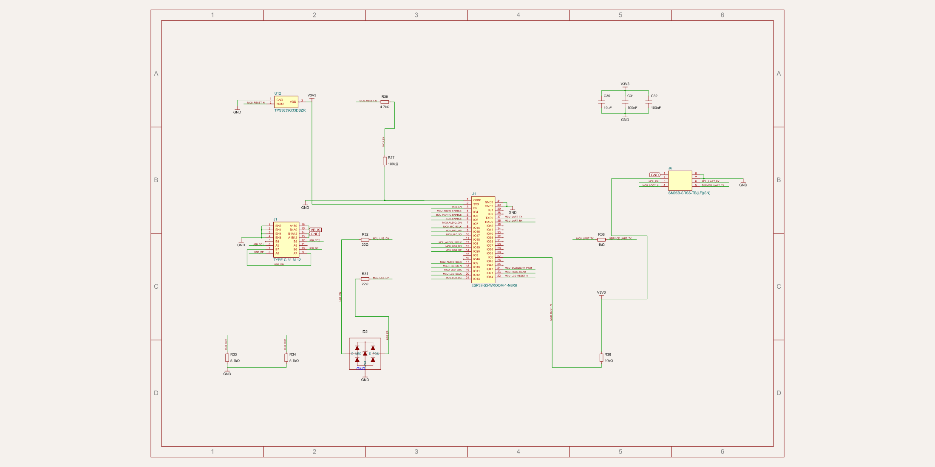
evidence/a5-connector-simplification-2026-10-04/schematic.png
