AnasSarkiz/tscircuit-ai-agent-remote/evidence/blocker-recheck-2026-10-03-1357/alternatives/C41348533/native-output/pcb.png

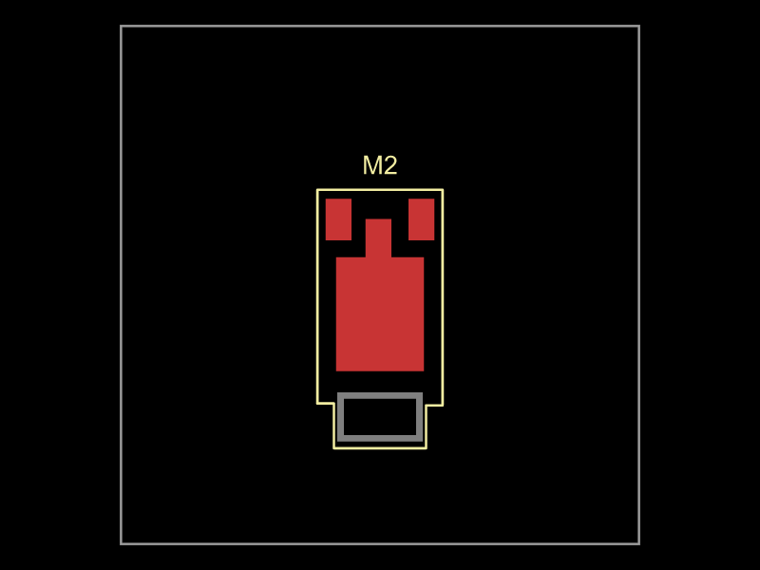
evidence/blocker-recheck-2026-10-03-1357/alternatives/C41348533/native-output/pcb.png
