AnasSarkiz/tscircuit-ai-agent-remote/evidence/blocker-recheck-2026-10-03-1357/amplifier/a4-page.png

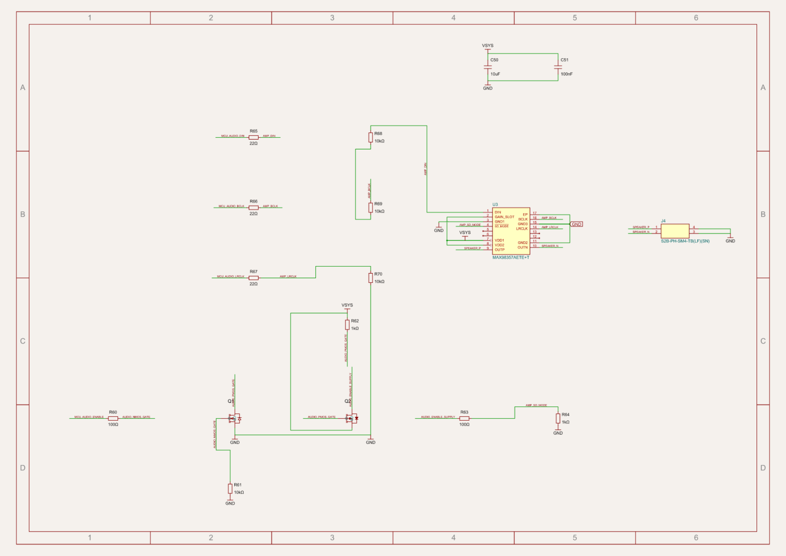
evidence/blocker-recheck-2026-10-03-1357/amplifier/a4-page.png
