AnasSarkiz/tscircuit-ai-agent-remote/evidence/blocker-recheck-2026-10-03-1357/comparator/a4-page.png

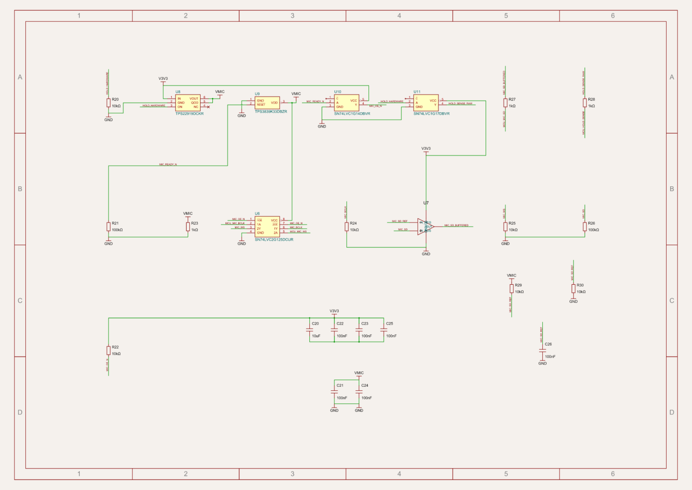
evidence/blocker-recheck-2026-10-03-1357/comparator/a4-page.png
