AnasSarkiz/tscircuit-ai-agent-remote/evidence/blocker-recheck-2026-10-03-1357/microphone/native-output/schematic-current.png

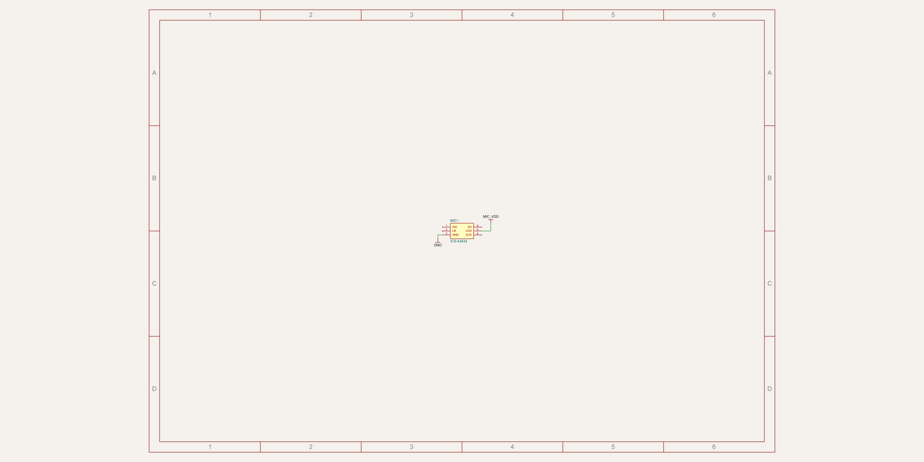
evidence/blocker-recheck-2026-10-03-1357/microphone/native-output/schematic-current.png
