AnasSarkiz/tscircuit-ai-agent-remote/evidence/charger-battery-ready-review-2026-10-03/schematic.png

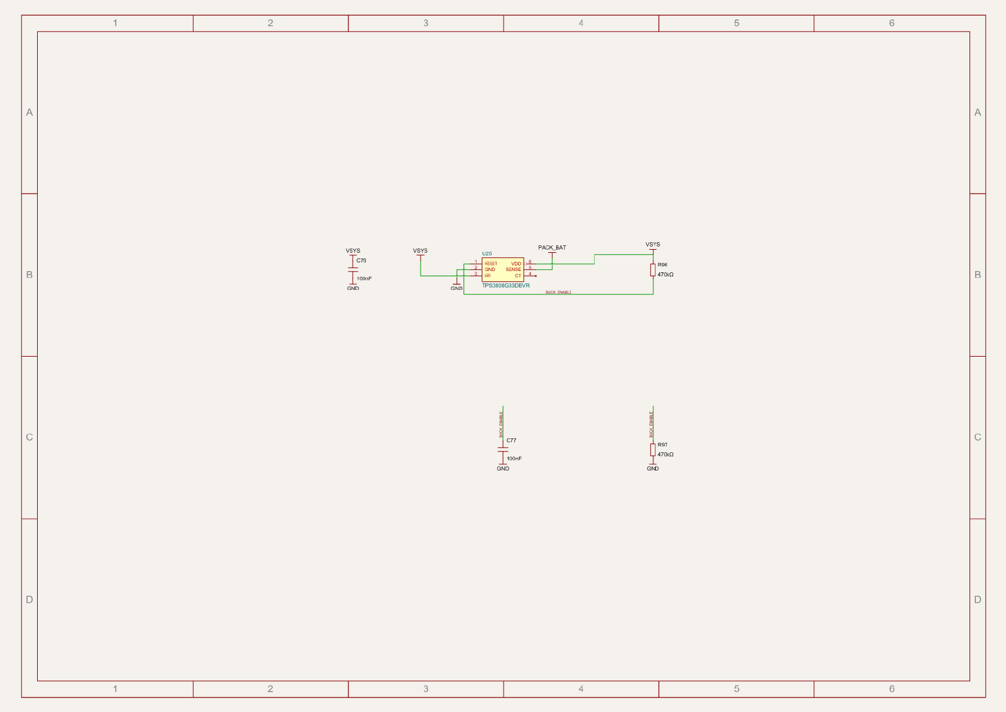
evidence/charger-battery-ready-review-2026-10-03/schematic.png
