AnasSarkiz/tscircuit-ai-agent-remote/evidence/connector-orientation-review-2026-10-04/before/display-ribbon.png

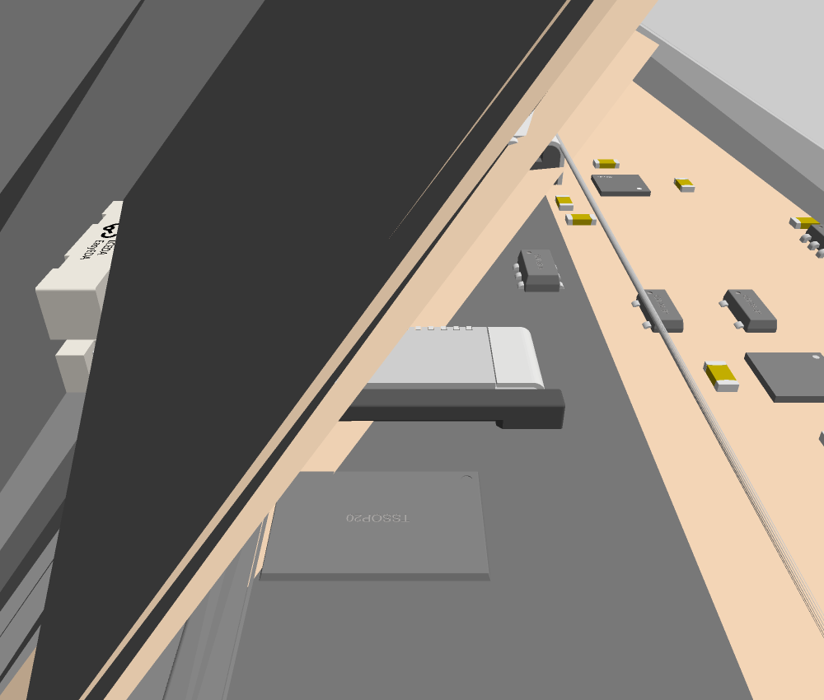
evidence/connector-orientation-review-2026-10-04/before/display-ribbon.png
