AnasSarkiz/tscircuit-ai-agent-remote/evidence/connector-orientation-review-2026-10-04/before/speaker-left-edge.png

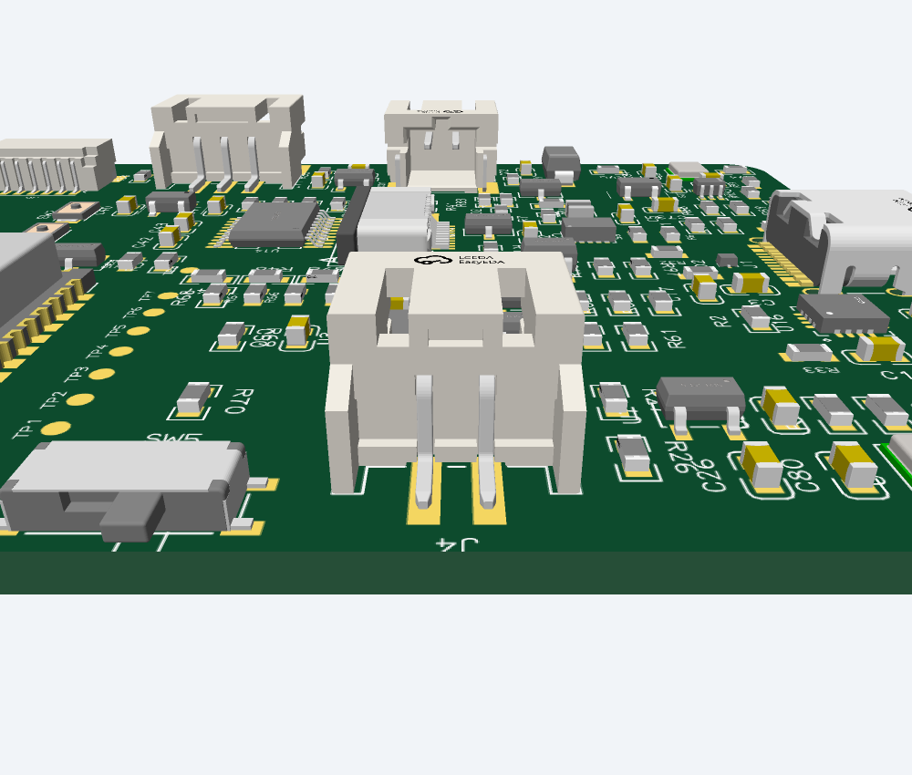
evidence/connector-orientation-review-2026-10-04/before/speaker-left-edge.png
