AnasSarkiz/tscircuit-ai-agent-remote/evidence/controls-review-2026-10-03/isolation-pcb.png

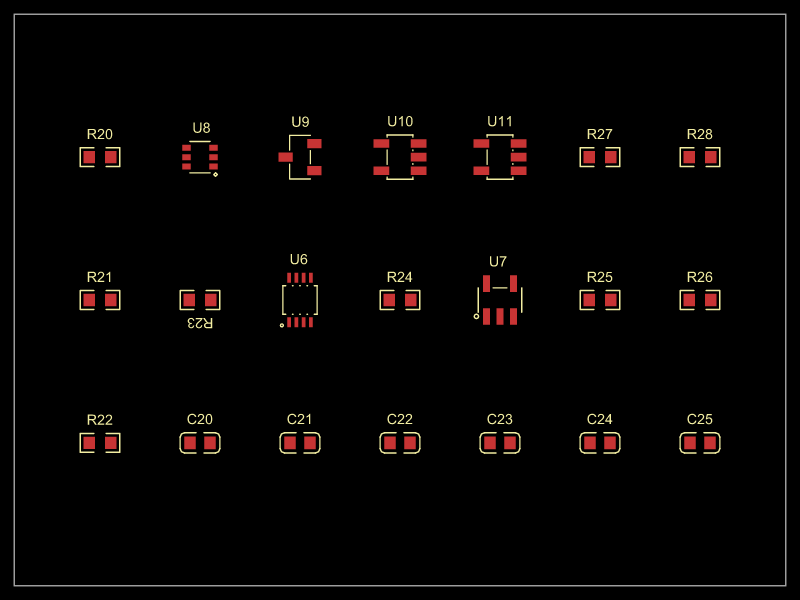
evidence/controls-review-2026-10-03/isolation-pcb.png
