AnasSarkiz/tscircuit-ai-agent-remote/evidence/controls-review-2026-10-03/panasonic-side-switch-2.png

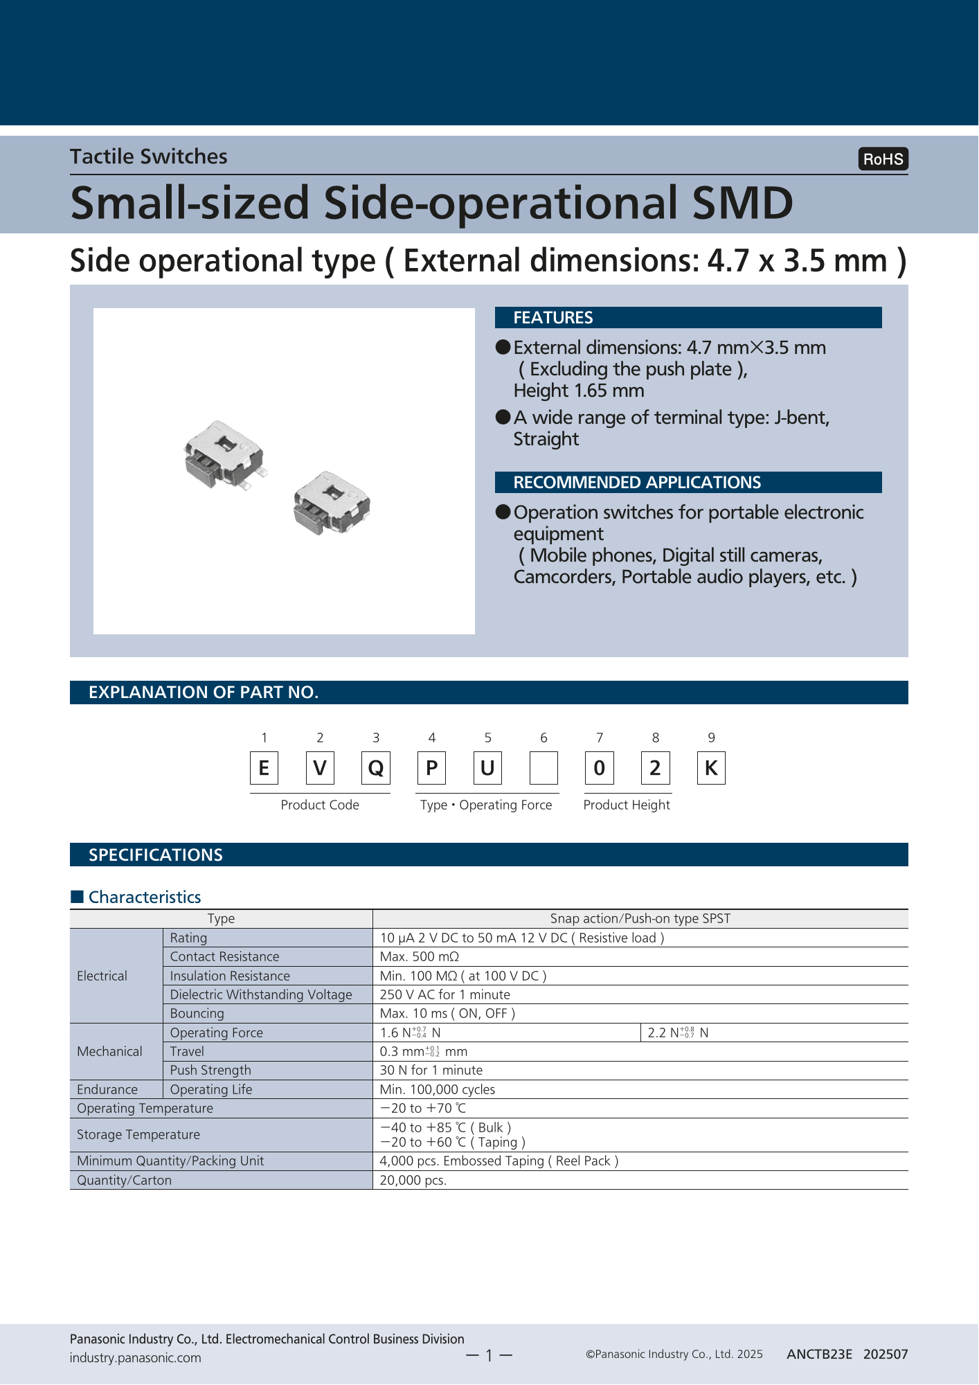
evidence/controls-review-2026-10-03/panasonic-side-switch-2.png
