AnasSarkiz/tscircuit-ai-agent-remote/evidence/controls-review-2026-10-03/regulator-current-pcb.png

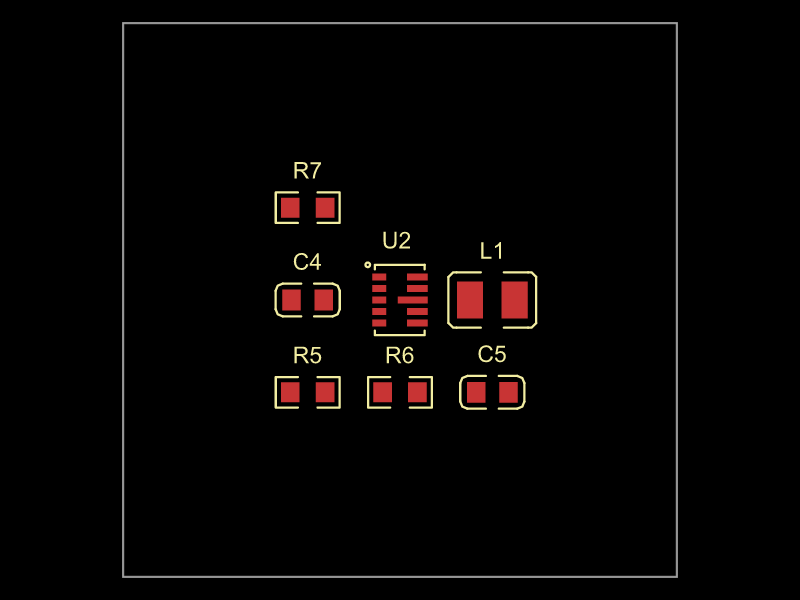
evidence/controls-review-2026-10-03/regulator-current-pcb.png
