AnasSarkiz/tscircuit-ai-agent-remote/evidence/controls-review-2026-10-03/tlv3201-pinout.png

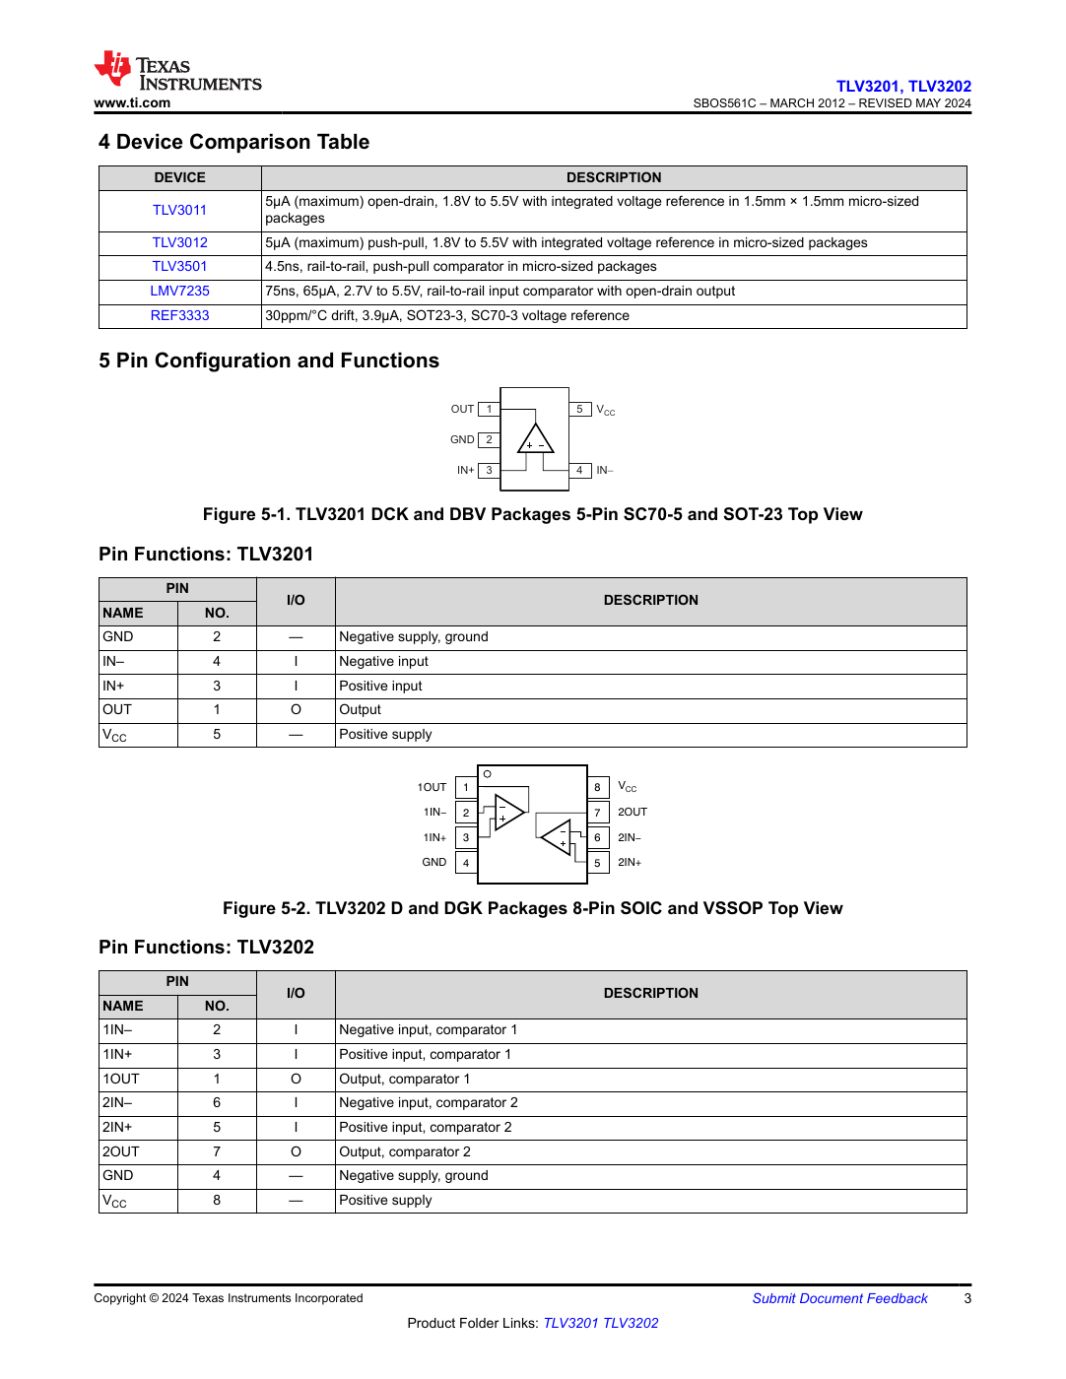
evidence/controls-review-2026-10-03/tlv3201-pinout.png
