AnasSarkiz/tscircuit-ai-agent-remote/evidence/controls-review-2026-10-03/tps3839-electrical.png

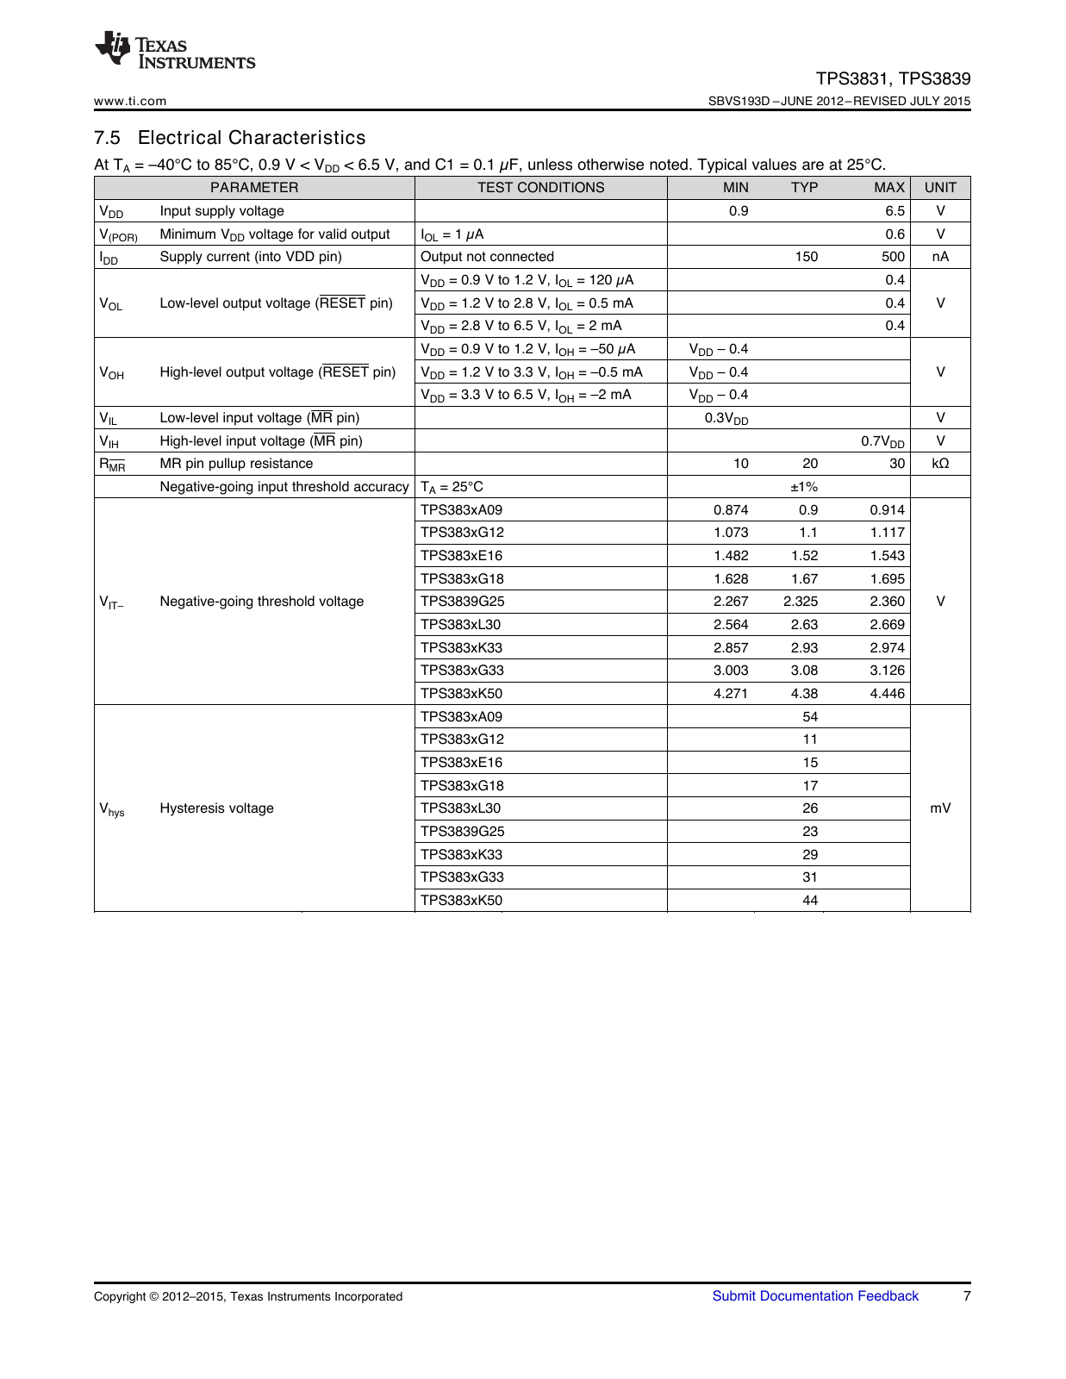
evidence/controls-review-2026-10-03/tps3839-electrical.png
