AnasSarkiz/tscircuit-ai-agent-remote/evidence/controls-review-2026-10-03/tps22919-pinout.png

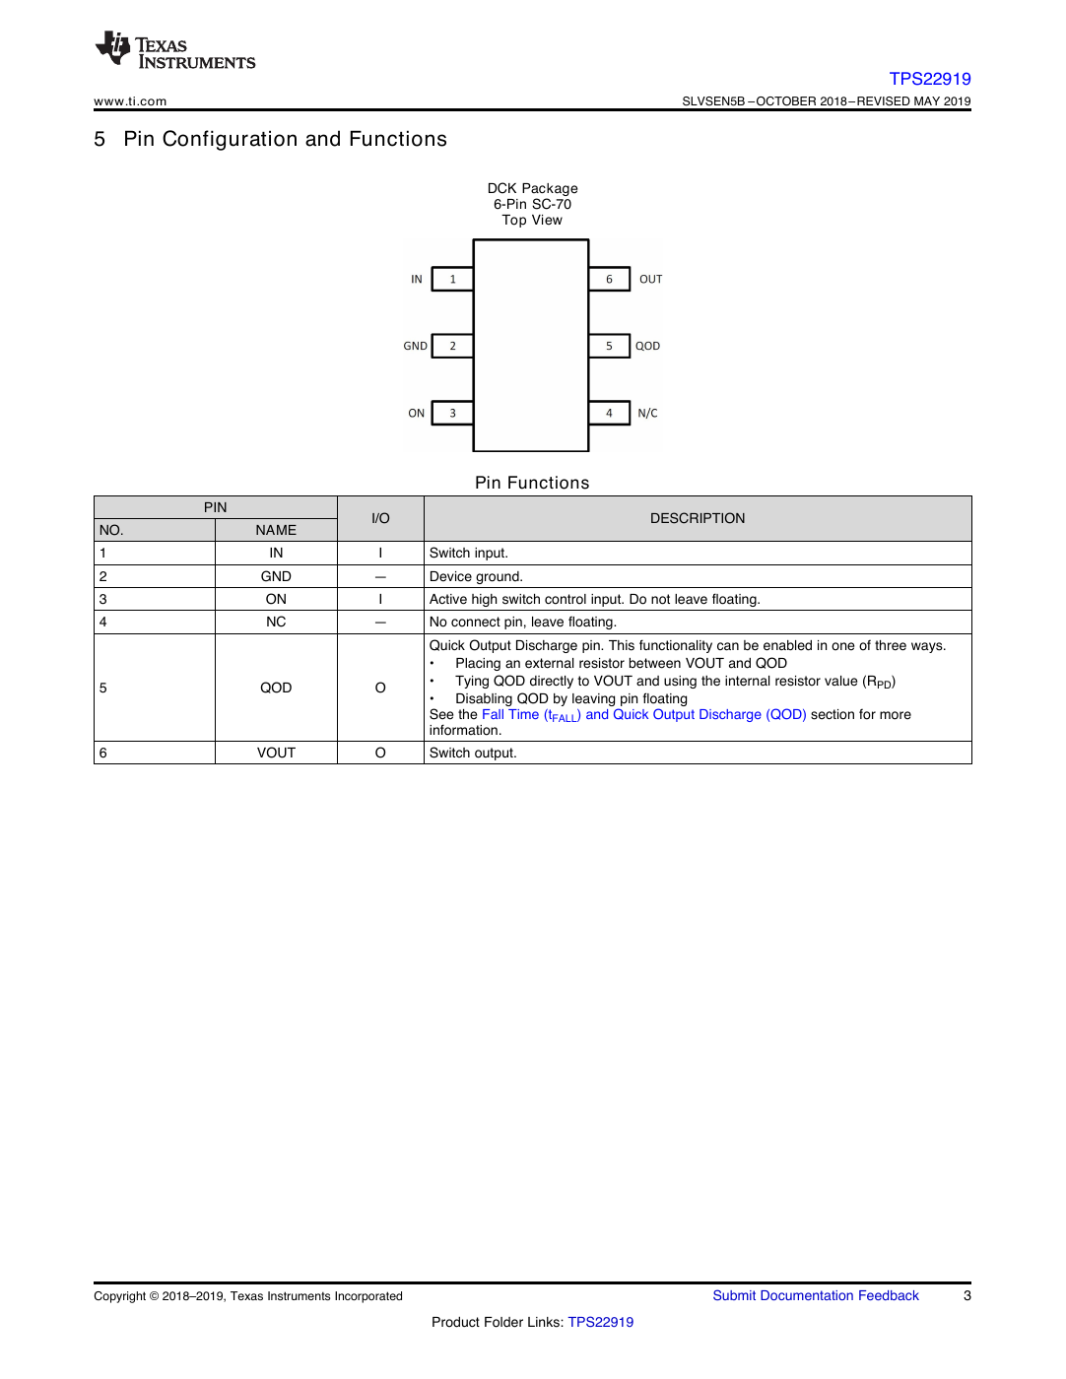
evidence/controls-review-2026-10-03/tps22919-pinout.png
