AnasSarkiz/tscircuit-ai-agent-remote/evidence/core-b010-proposal-2026-10-03/pcb.png

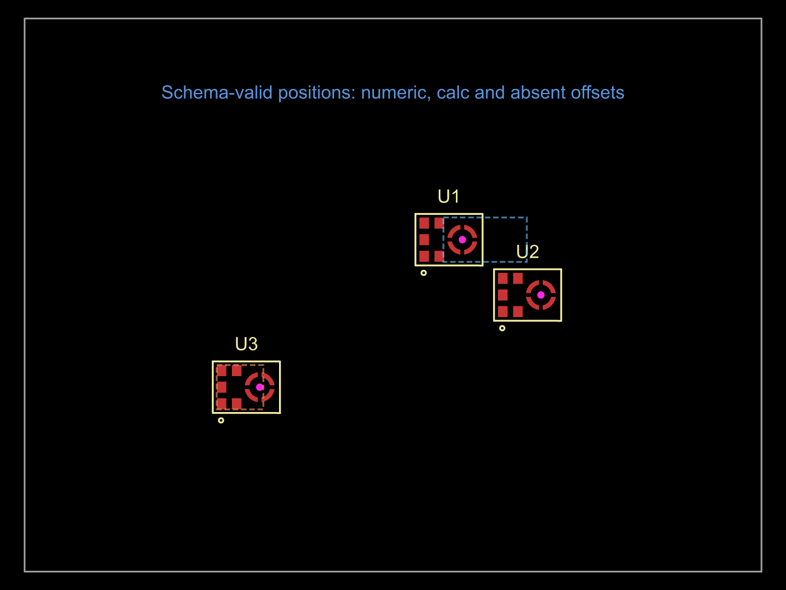
evidence/core-b010-proposal-2026-10-03/pcb.png
