AnasSarkiz/tscircuit-ai-agent-remote/evidence/datasheets/alps-ec11e-2.png

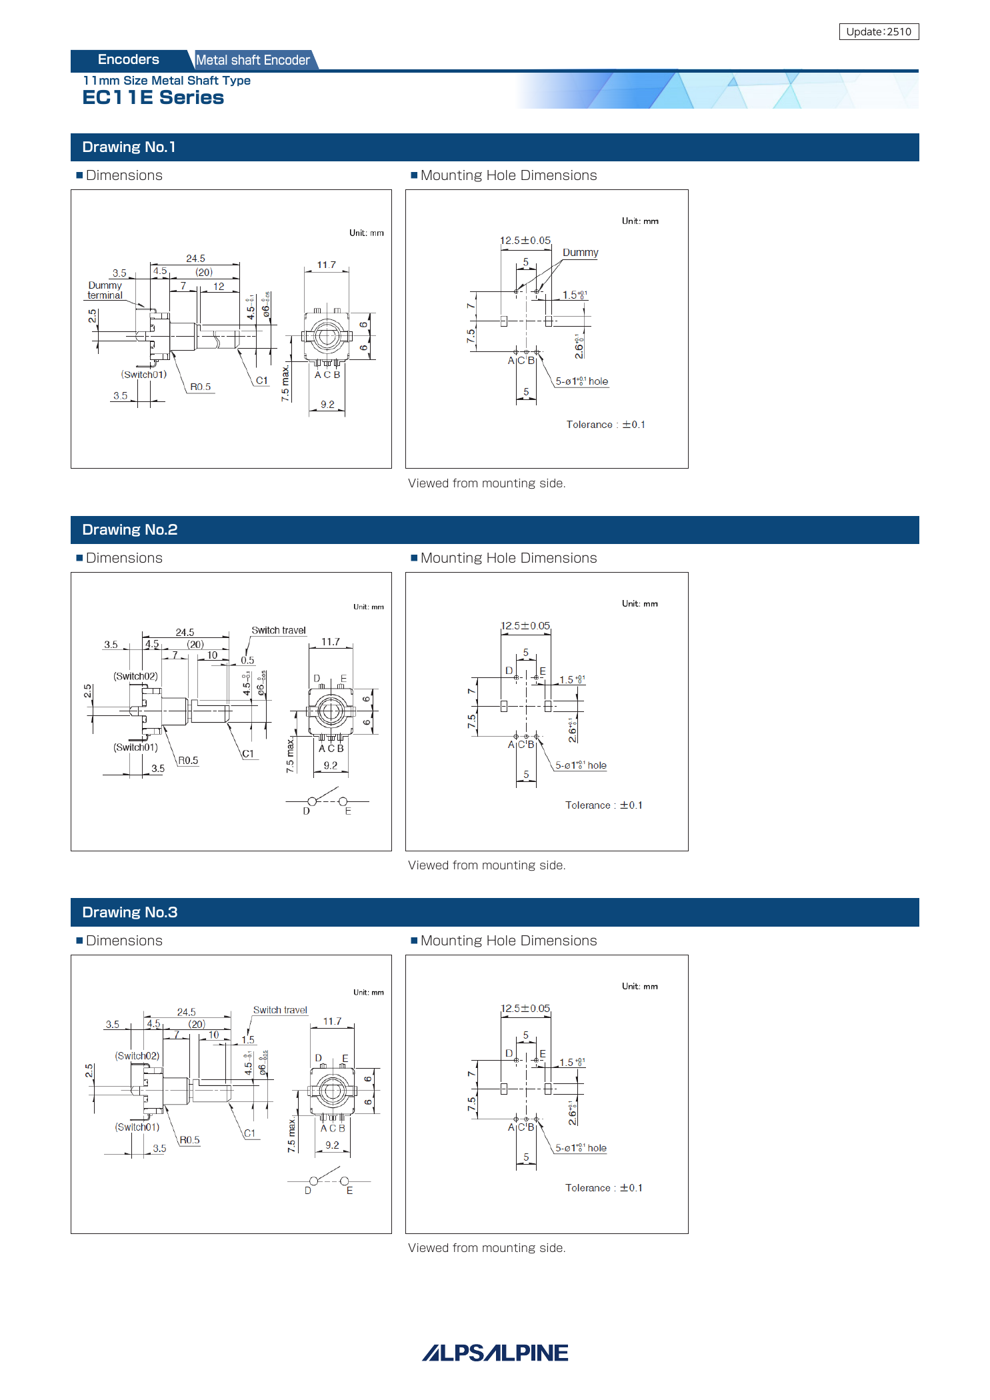
evidence/datasheets/alps-ec11e-2.png
