AnasSarkiz/tscircuit-ai-agent-remote/evidence/datasheets/tps63802-35.png

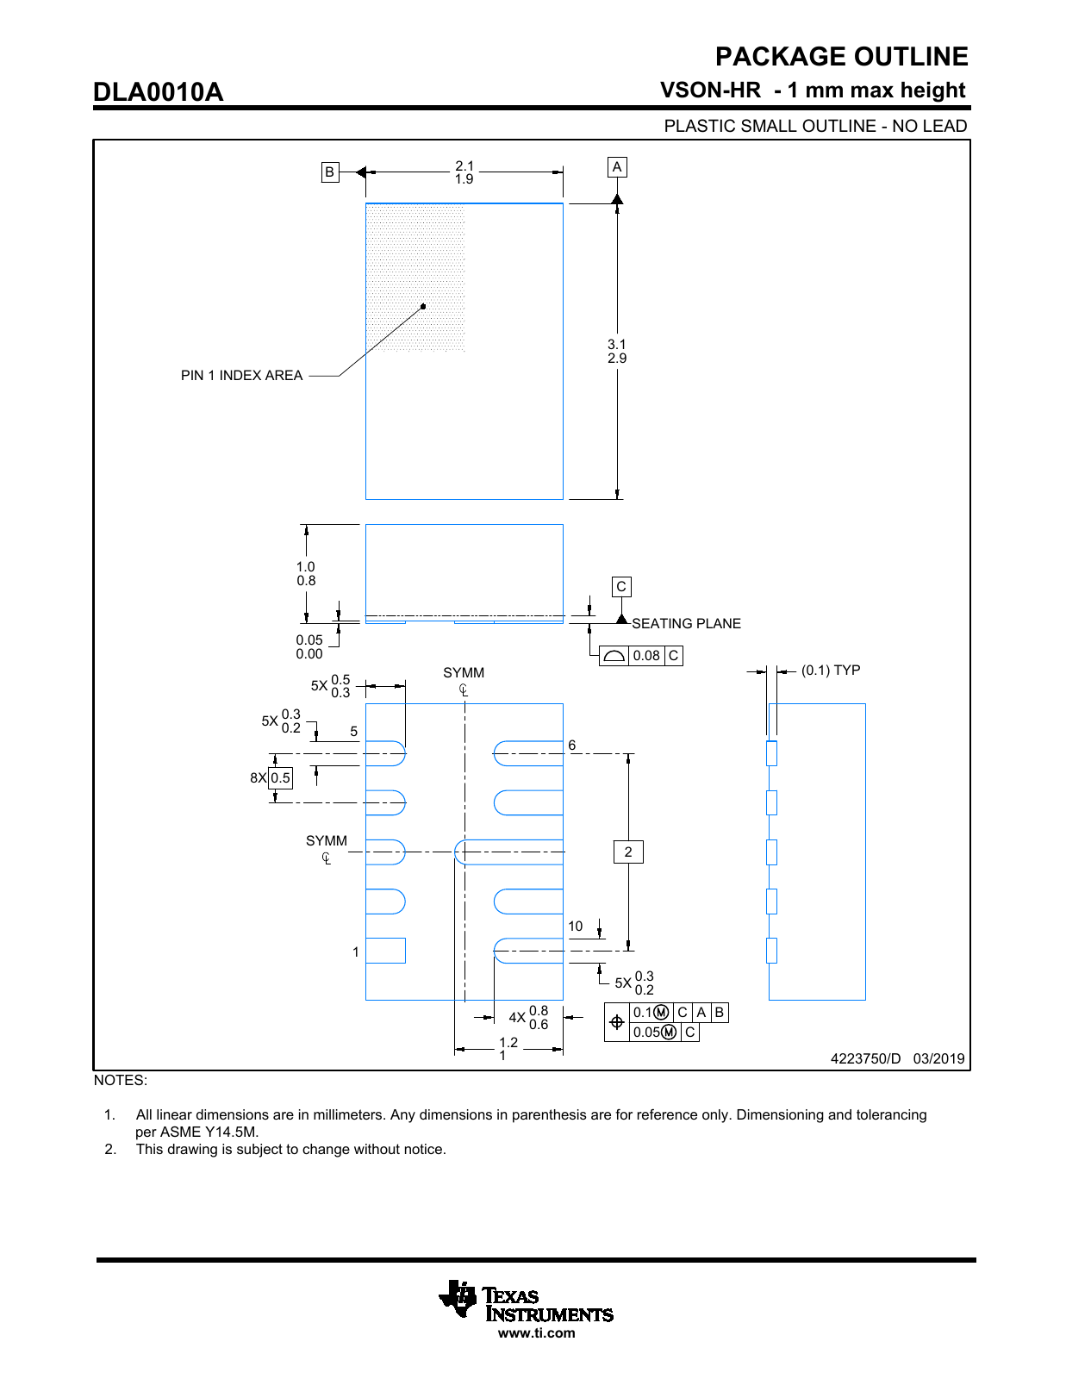
evidence/datasheets/tps63802-35.png
