AnasSarkiz/tscircuit-ai-agent-remote/evidence/datasheets/tps63802-36.png

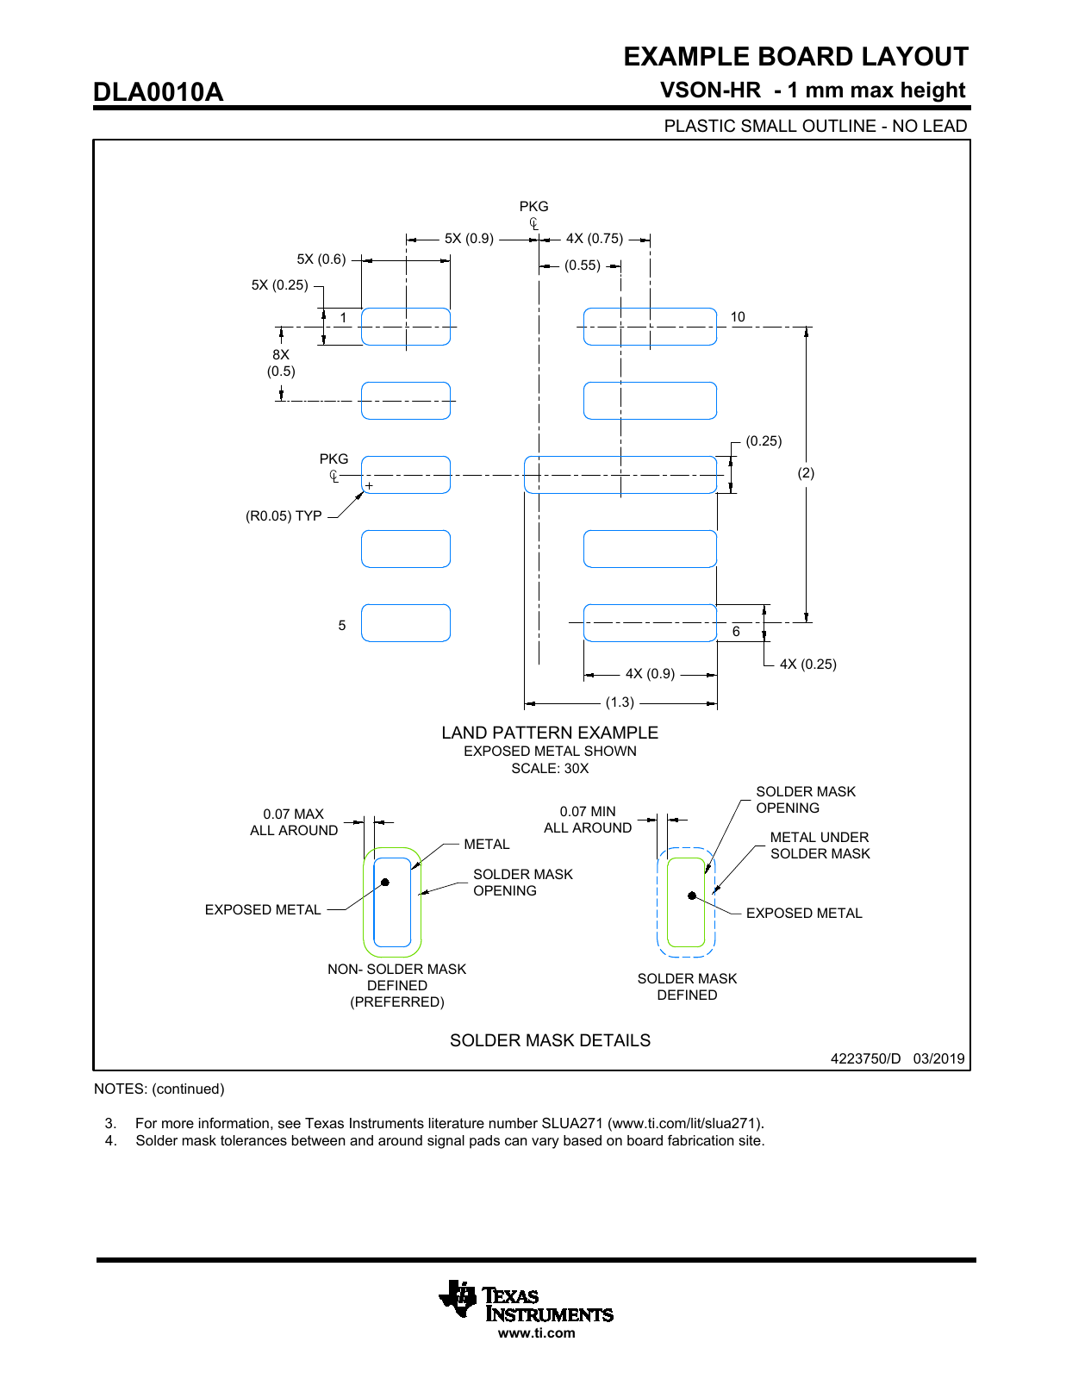
evidence/datasheets/tps63802-36.png
