AnasSarkiz/tscircuit-ai-agent-remote/evidence/datasheets/waveshare-1.54-1.png

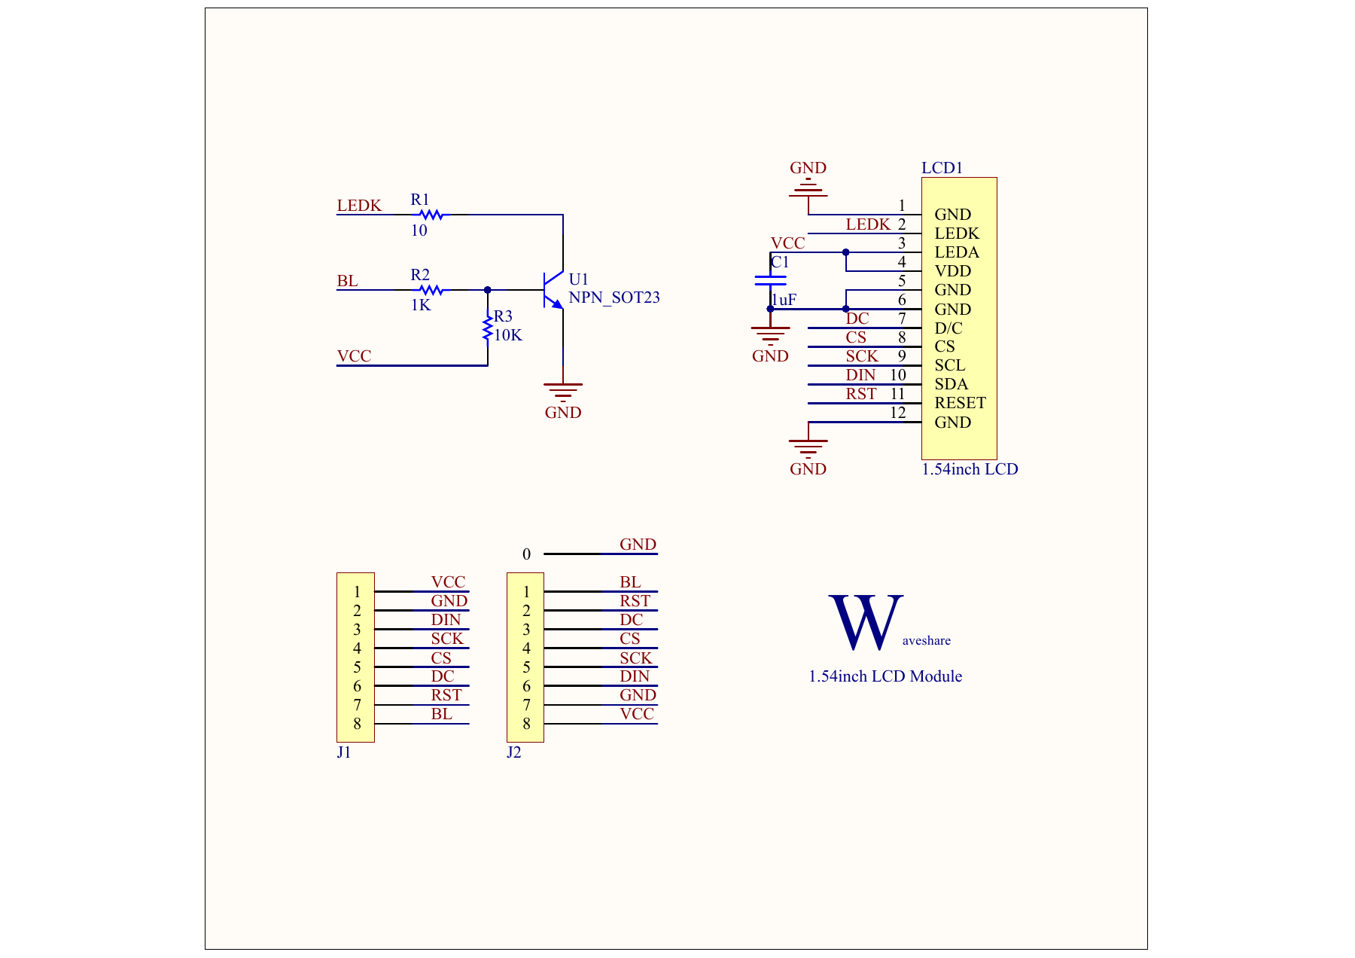
evidence/datasheets/waveshare-1.54-1.png
