AnasSarkiz/tscircuit-ai-agent-remote/evidence/datasheets/waveshare-1.54-2.png

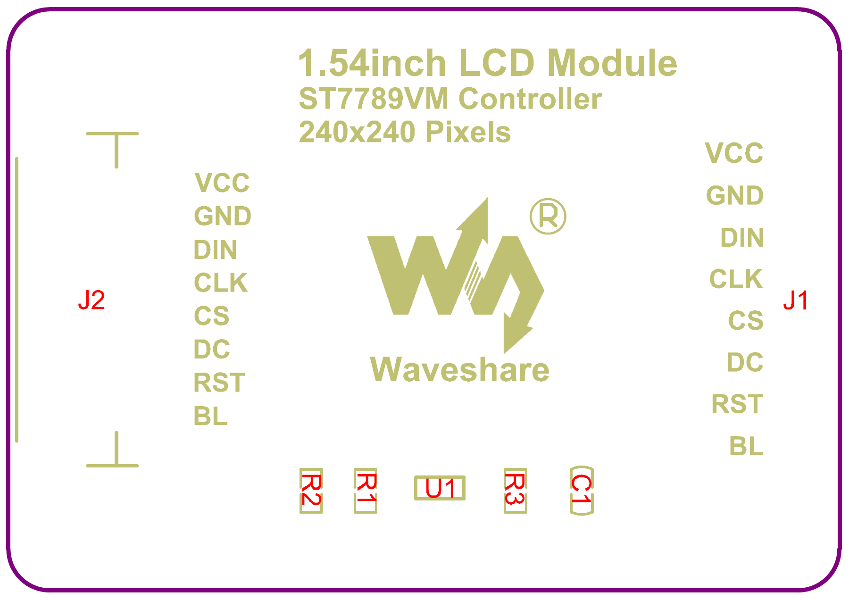
evidence/datasheets/waveshare-1.54-2.png
