AnasSarkiz/tscircuit-ai-agent-remote/evidence/display023-primary-review-2026-10-07/no-touch-flex-detail.png

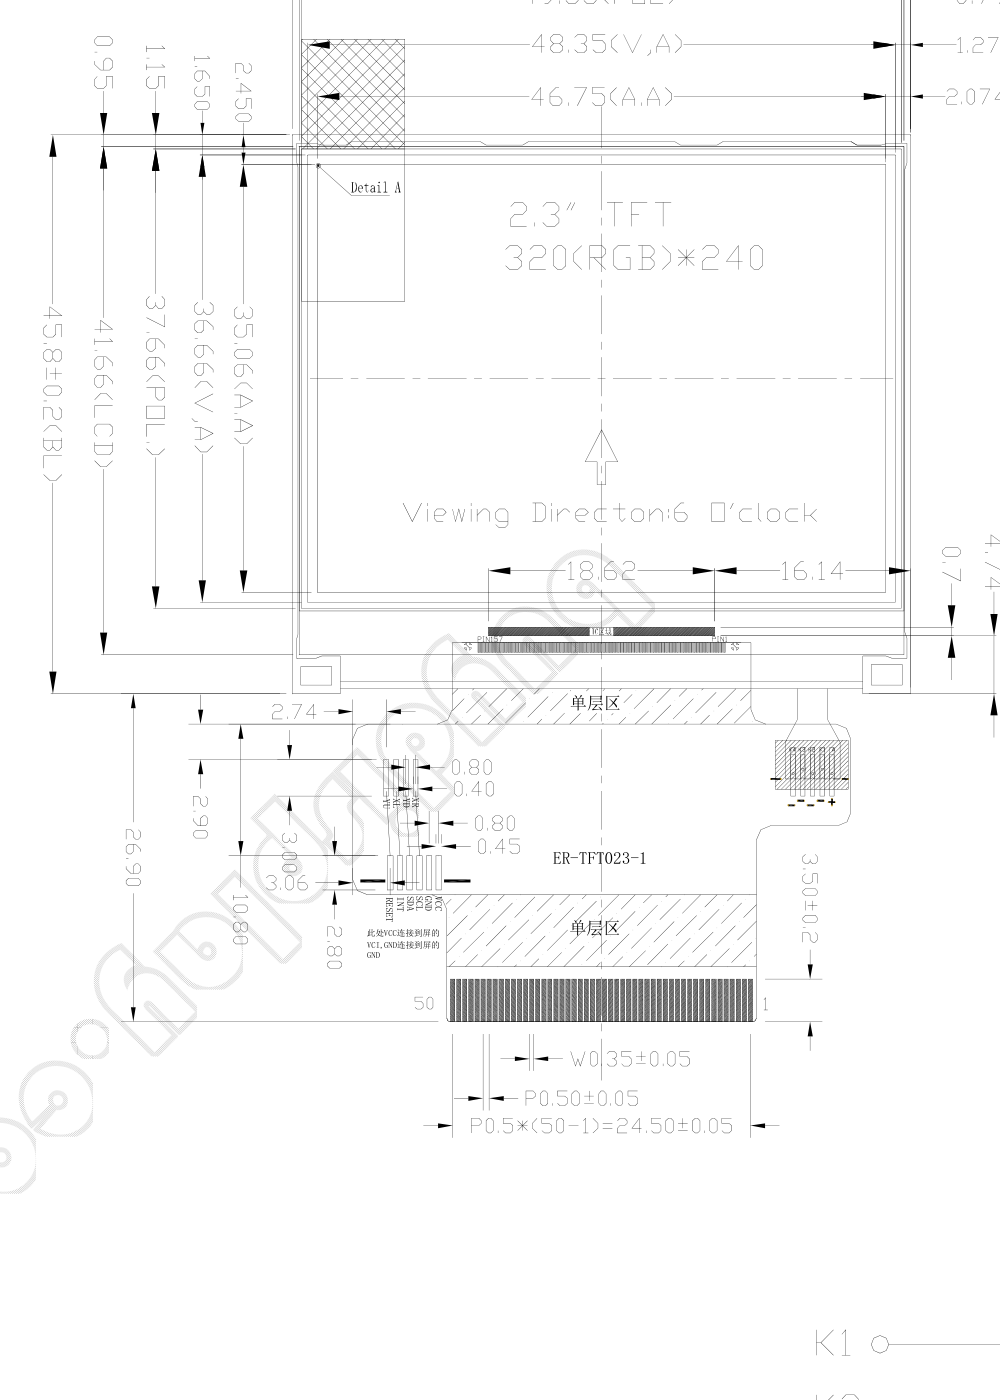
evidence/display023-primary-review-2026-10-07/no-touch-flex-detail.png
