AnasSarkiz/tscircuit-ai-agent-remote/evidence/display028-integration-2026-10-07/mechanical-review.png

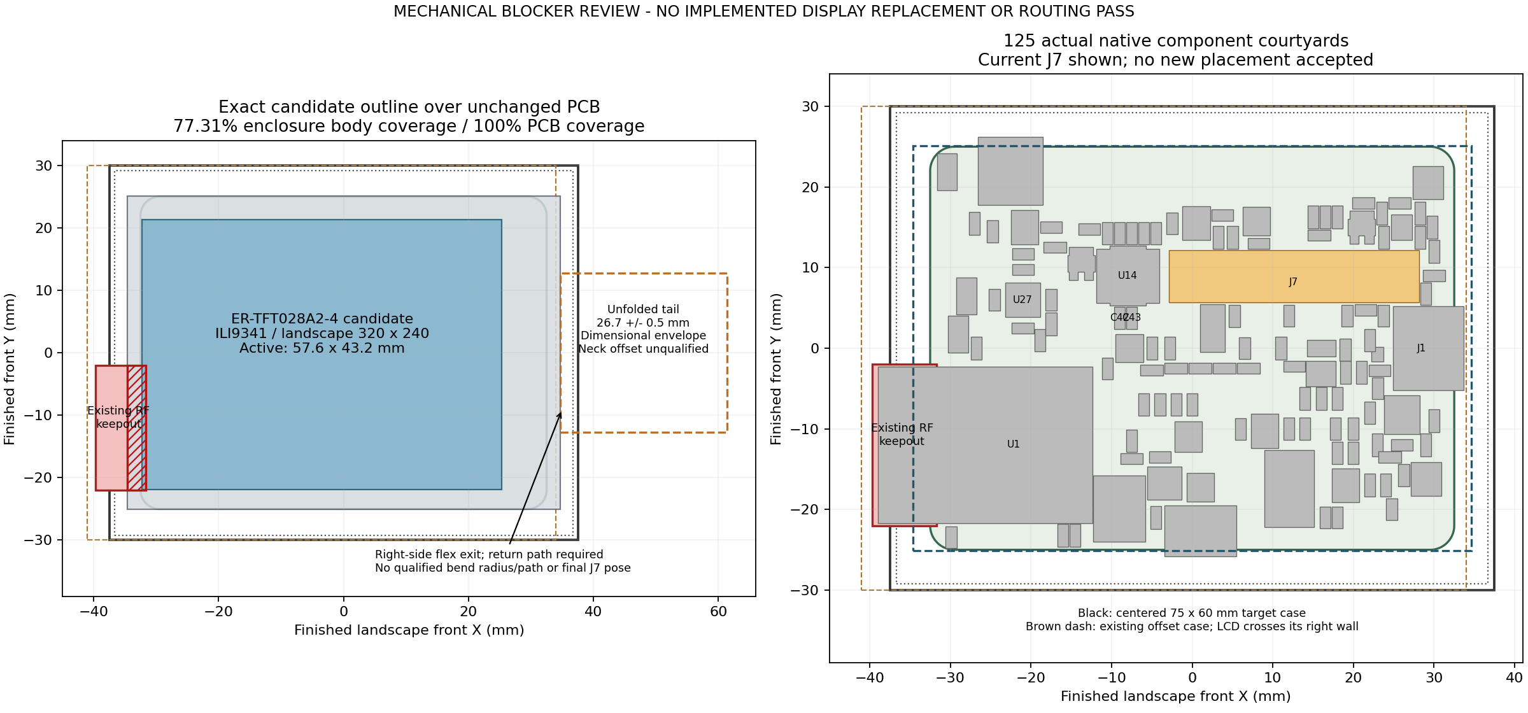
evidence/display028-integration-2026-10-07/mechanical-review.png
