AnasSarkiz/tscircuit-ai-agent-remote/evidence/display028-integration-2026-10-07/primary/no-touch-outline.png

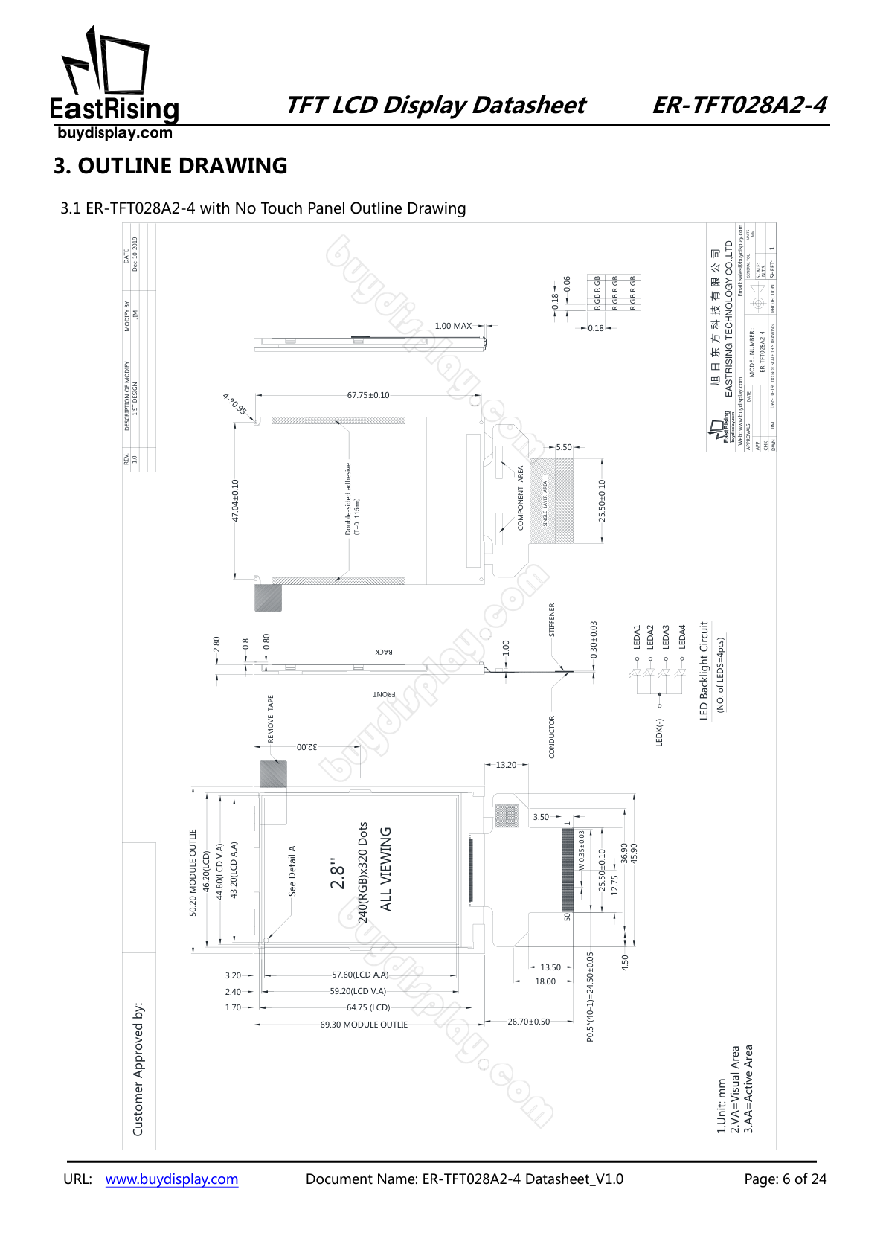
evidence/display028-integration-2026-10-07/primary/no-touch-outline.png
