AnasSarkiz/tscircuit-ai-agent-remote/evidence/display-datasheet-routing-2026-10-07/connector-fpc-detail.png

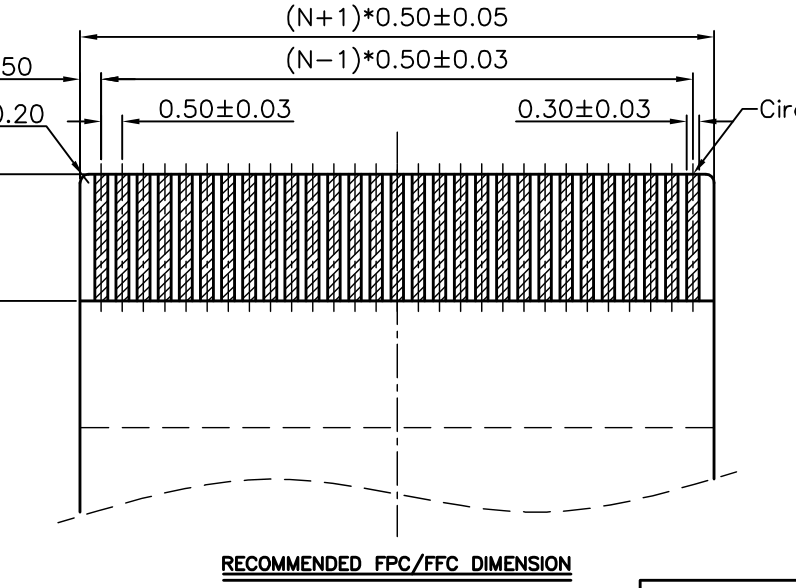
evidence/display-datasheet-routing-2026-10-07/connector-fpc-detail.png
