AnasSarkiz/tscircuit-ai-agent-remote/evidence/display-datasheet-routing-2026-10-07/connector-section-detail.png

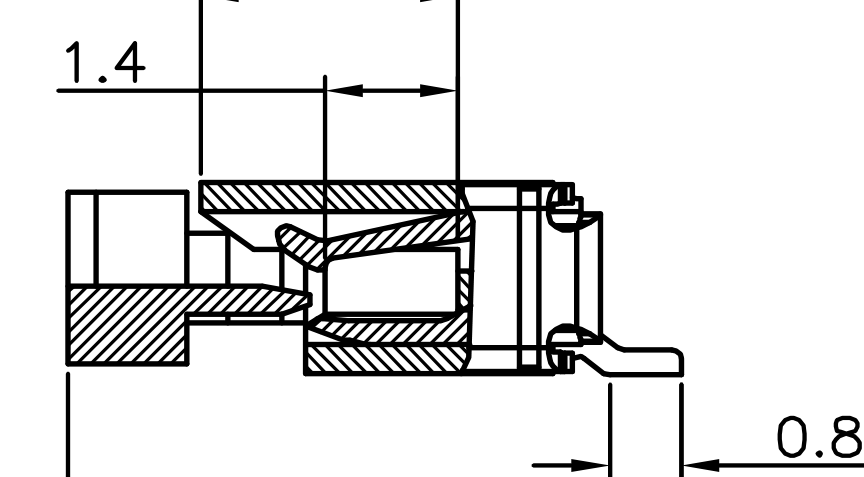
evidence/display-datasheet-routing-2026-10-07/connector-section-detail.png
