AnasSarkiz/tscircuit-ai-agent-remote/evidence/display-datasheet-routing-2026-10-07/page-10.png

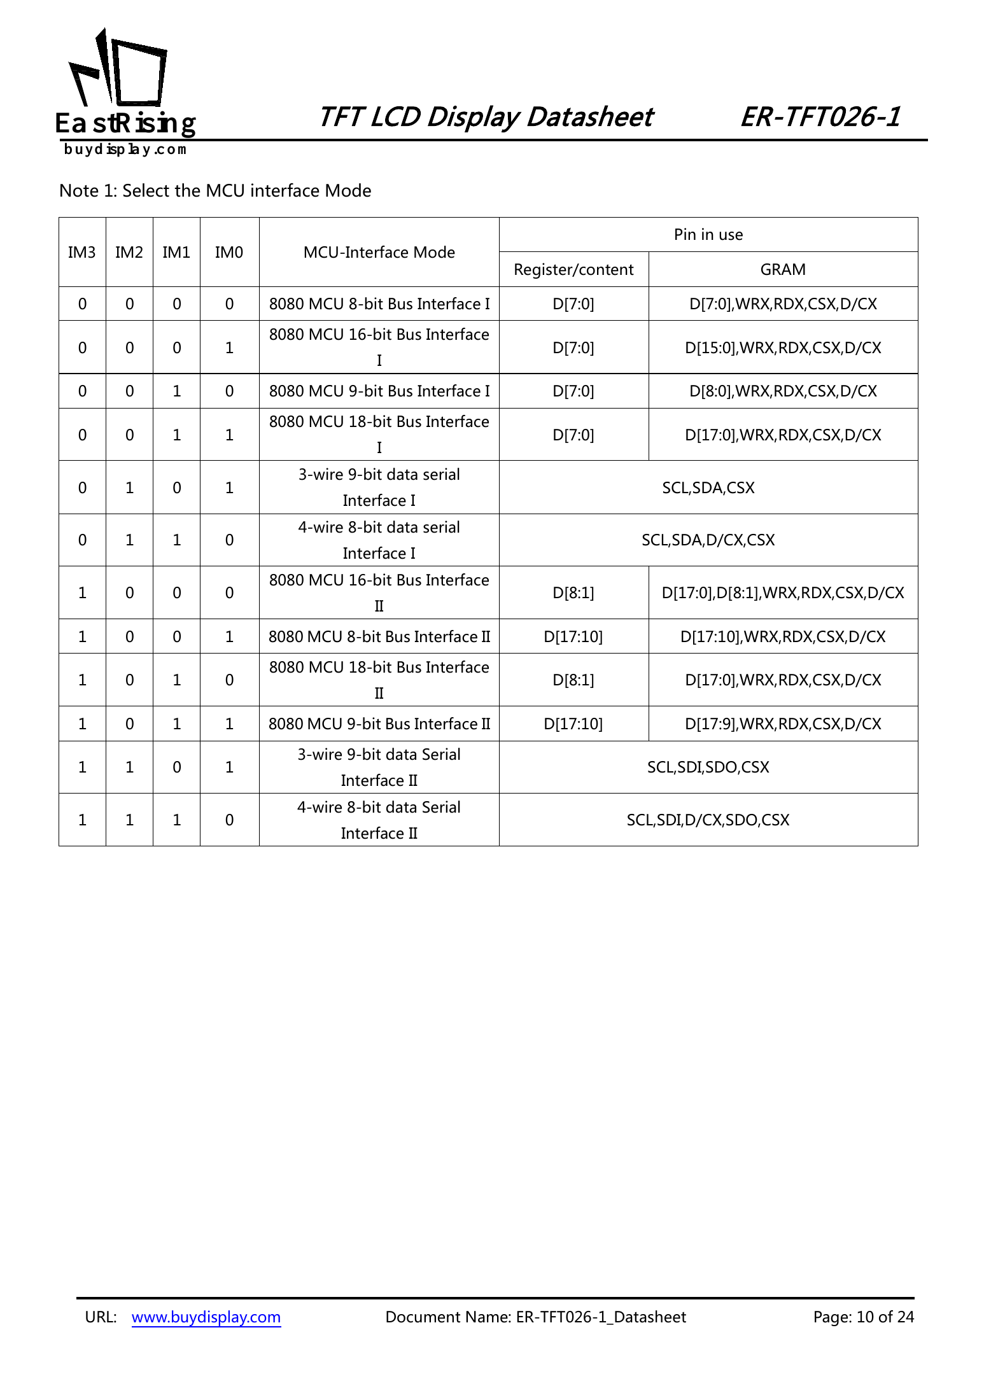
evidence/display-datasheet-routing-2026-10-07/page-10.png
