AnasSarkiz/tscircuit-ai-agent-remote/evidence/display-index-search-2026-10-07/approved-browser/product.png

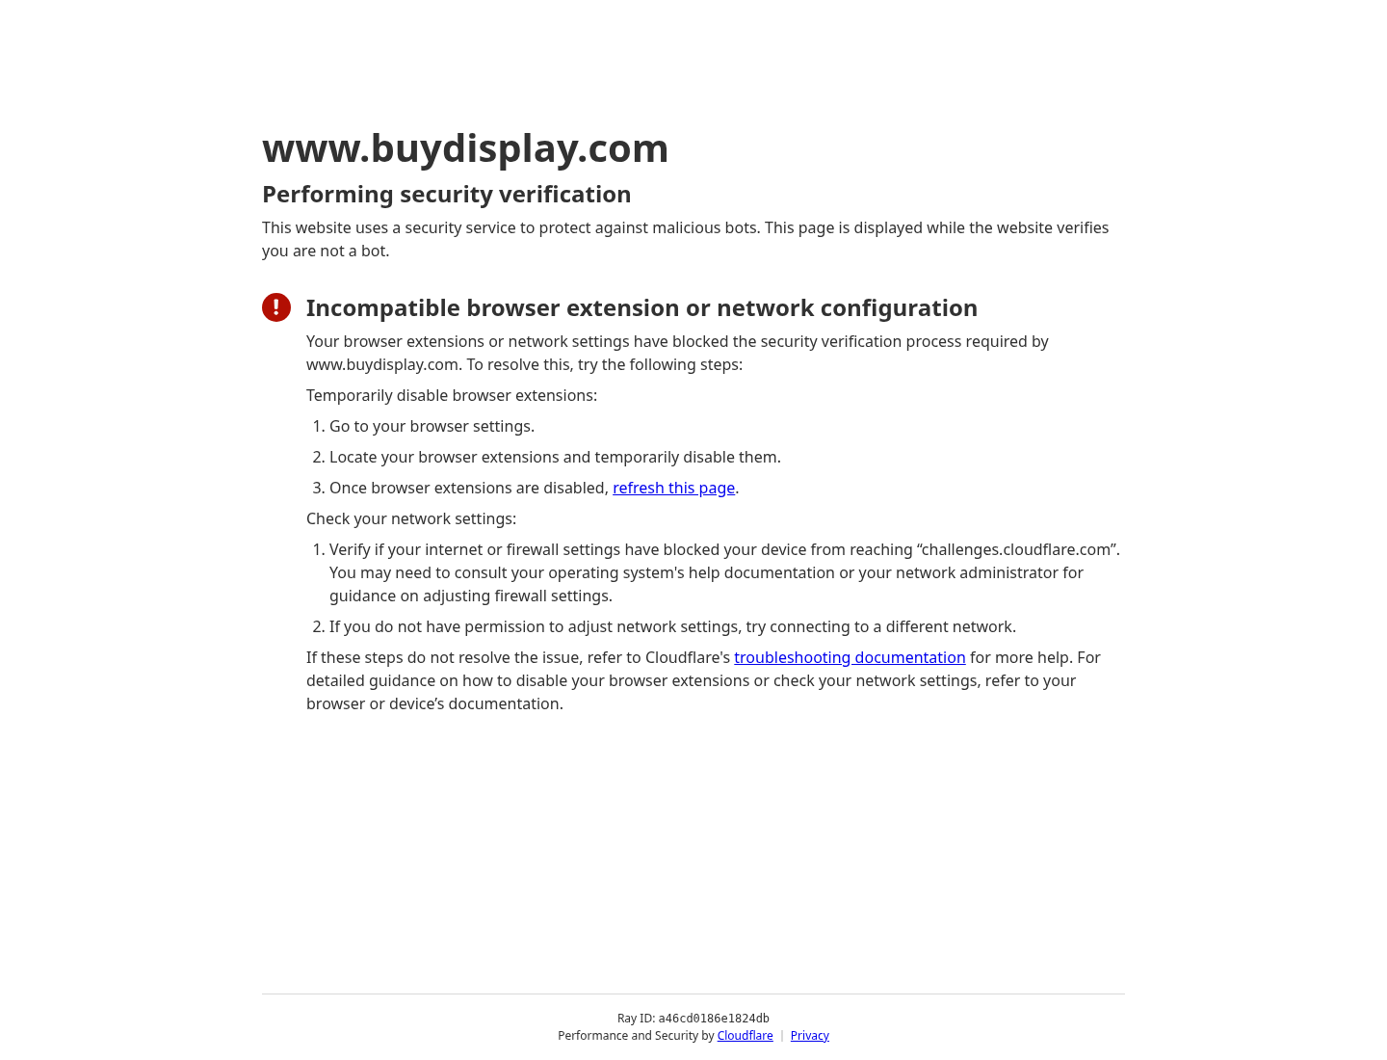
evidence/display-index-search-2026-10-07/approved-browser/product.png
