AnasSarkiz/tscircuit-ai-agent-remote/evidence/display-index-search-2026-10-07/ui-analysis/ui-style-analysis.png

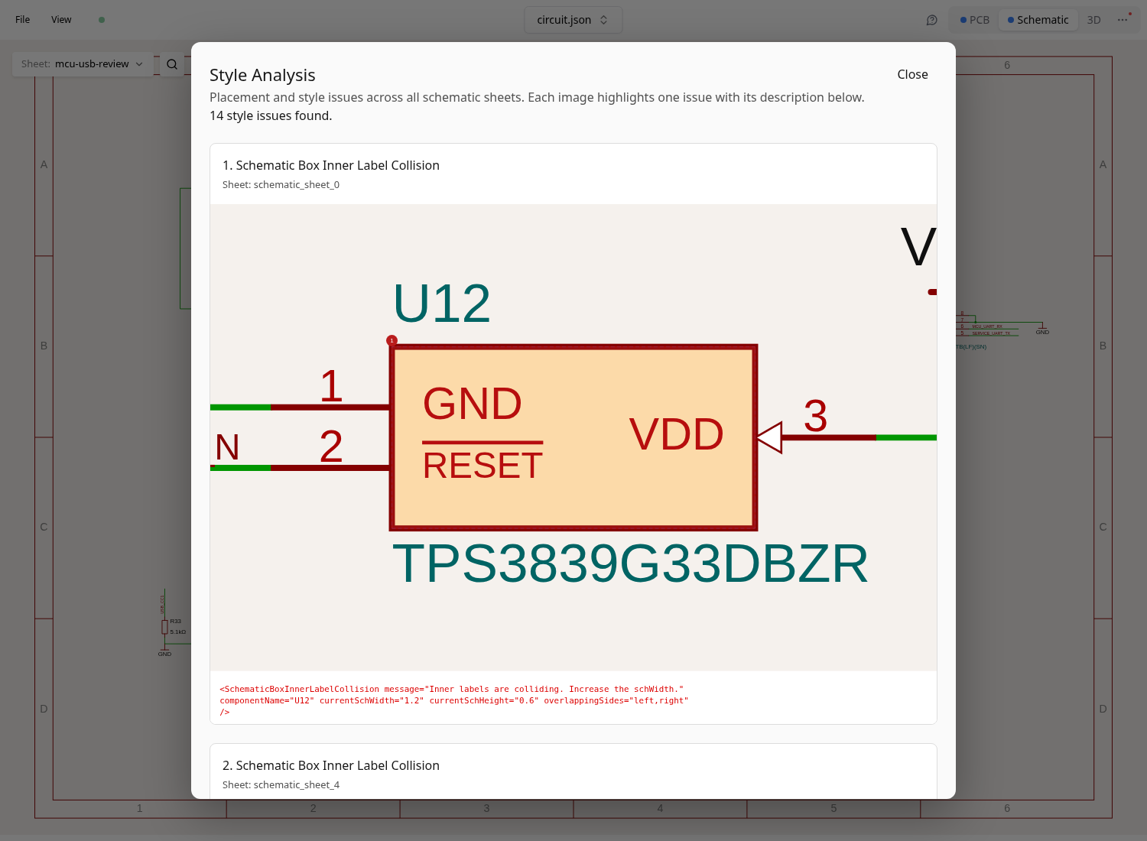
evidence/display-index-search-2026-10-07/ui-analysis/ui-style-analysis.png
