AnasSarkiz/tscircuit-ai-agent-remote/evidence/display-review-2026-10-03/schematic.png

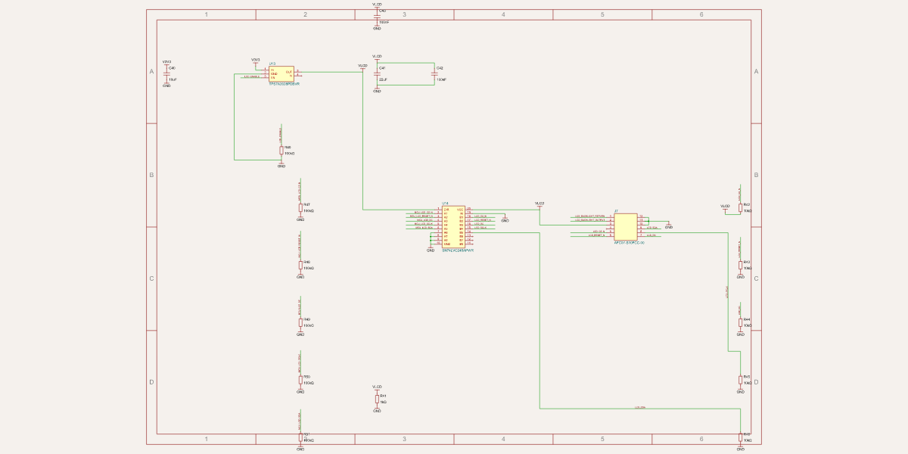
evidence/display-review-2026-10-03/schematic.png
