AnasSarkiz/tscircuit-ai-agent-remote/evidence/encoder-footprint-pcb.png

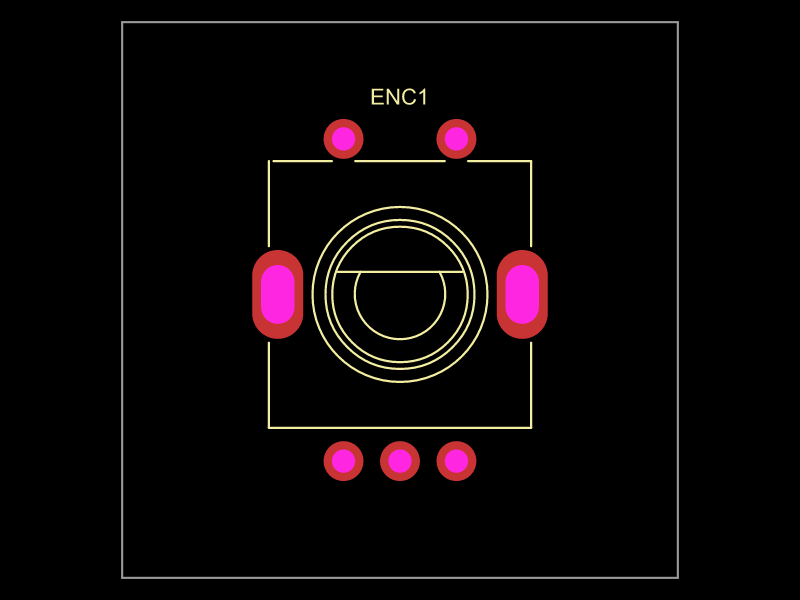
evidence/encoder-footprint-pcb.png
