AnasSarkiz/tscircuit-ai-agent-remote/evidence/haptic-review-2026-10-03/3d.png

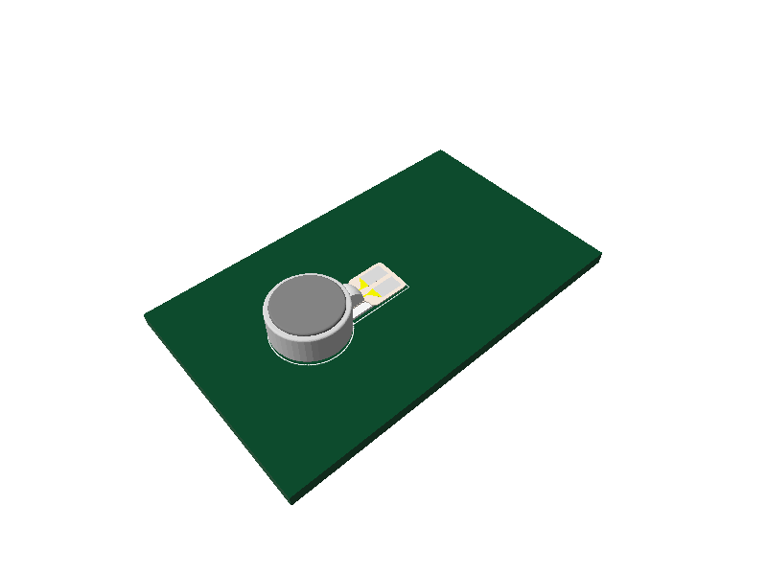
evidence/haptic-review-2026-10-03/3d.png
