AnasSarkiz/tscircuit-ai-agent-remote/evidence/hold-control-alternate-review-2026-10-03/schematic.png

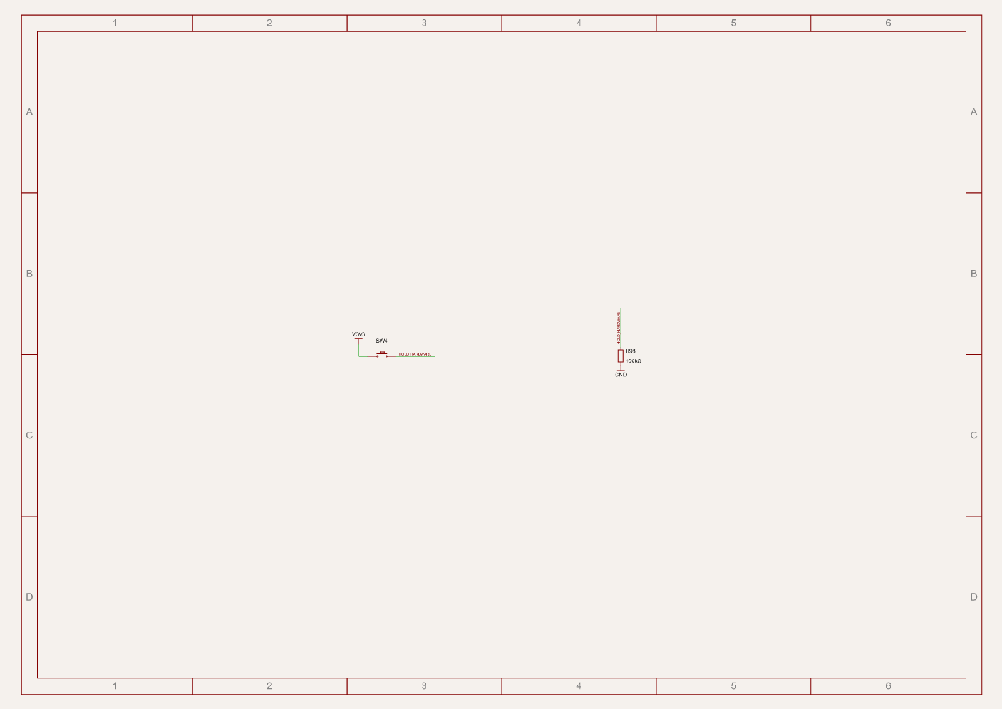
evidence/hold-control-alternate-review-2026-10-03/schematic.png
