AnasSarkiz/tscircuit-ai-agent-remote/evidence/hold-readback-review-2026-10-03/pcb.png

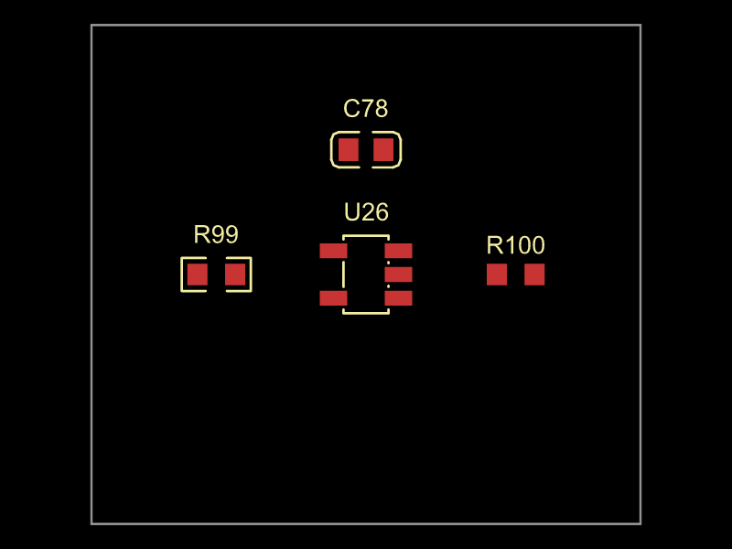
evidence/hold-readback-review-2026-10-03/pcb.png
