AnasSarkiz/tscircuit-ai-agent-remote/evidence/integrated-preview-2026-10-03/3d-bottom.png

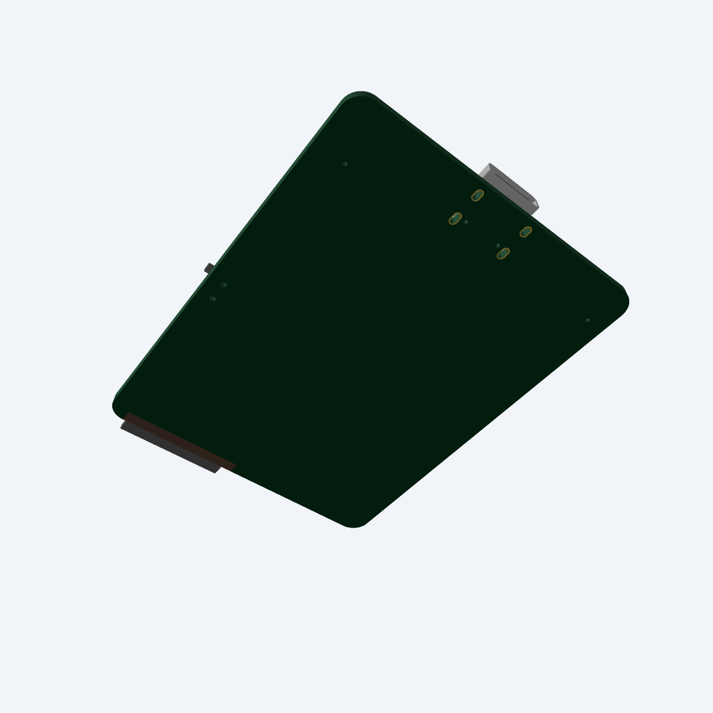
evidence/integrated-preview-2026-10-03/3d-bottom.png
