AnasSarkiz/tscircuit-ai-agent-remote/evidence/integrated-preview-2026-10-03/3d-top.png

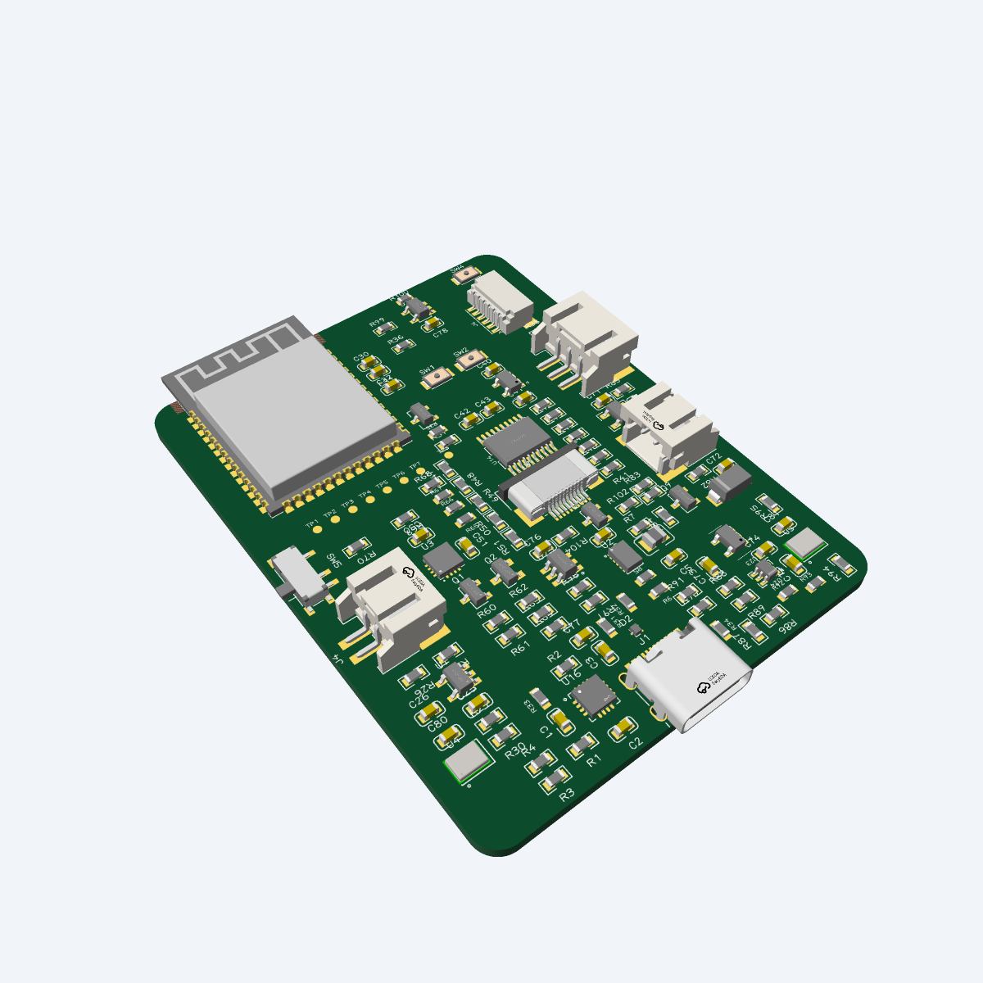
evidence/integrated-preview-2026-10-03/3d-top.png
