AnasSarkiz/tscircuit-ai-agent-remote/evidence/integrated-preview-2026-10-03/board-overview.png

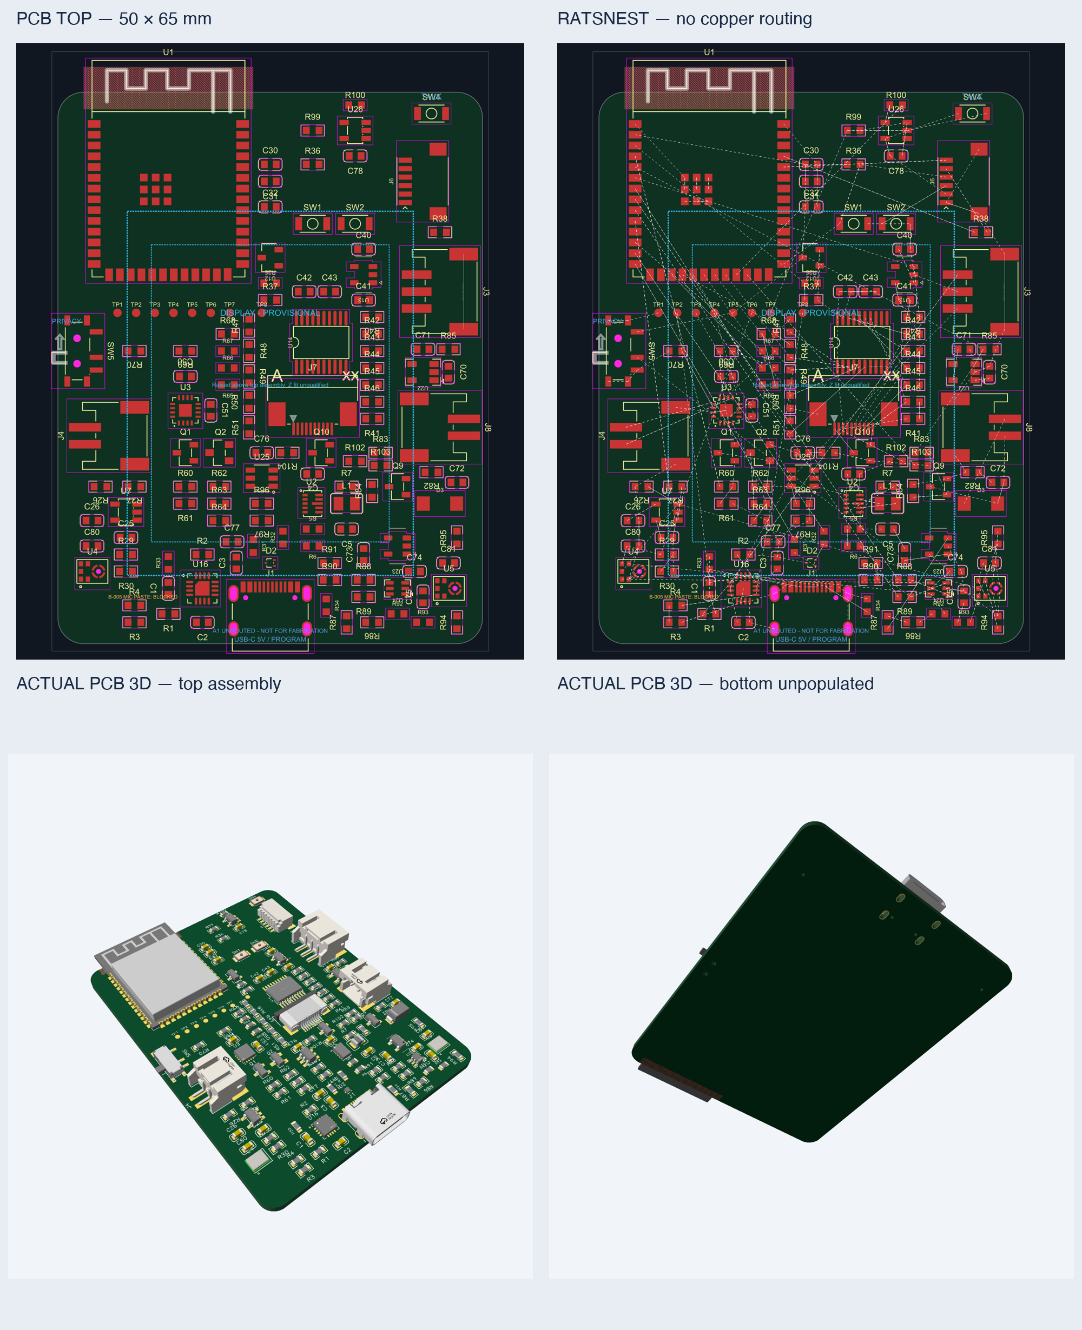
evidence/integrated-preview-2026-10-03/board-overview.png
