AnasSarkiz/tscircuit-ai-agent-remote/evidence/integrated-preview-2026-10-03/initial-pcb.png

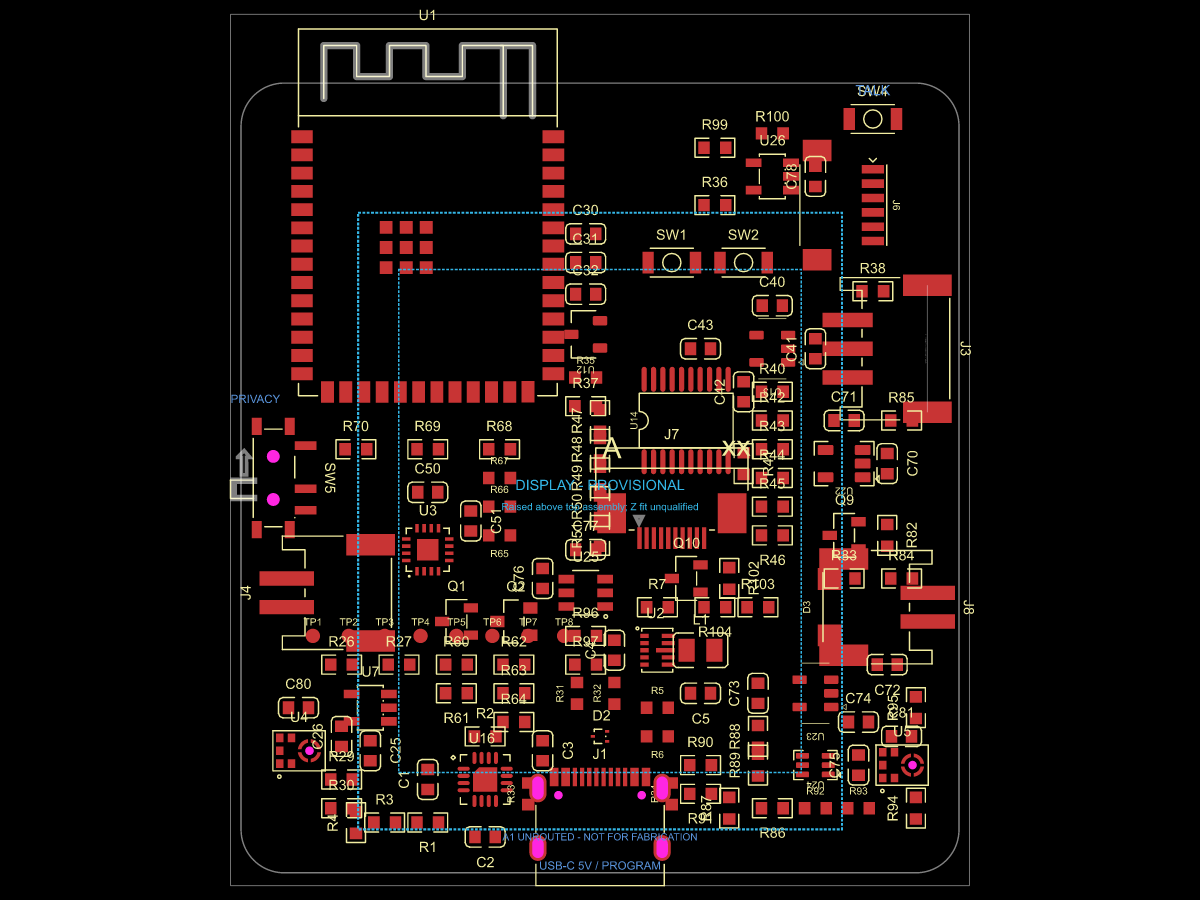
evidence/integrated-preview-2026-10-03/initial-pcb.png
