AnasSarkiz/tscircuit-ai-agent-remote/evidence/integrated-preview-2026-10-03/pcb-top.png

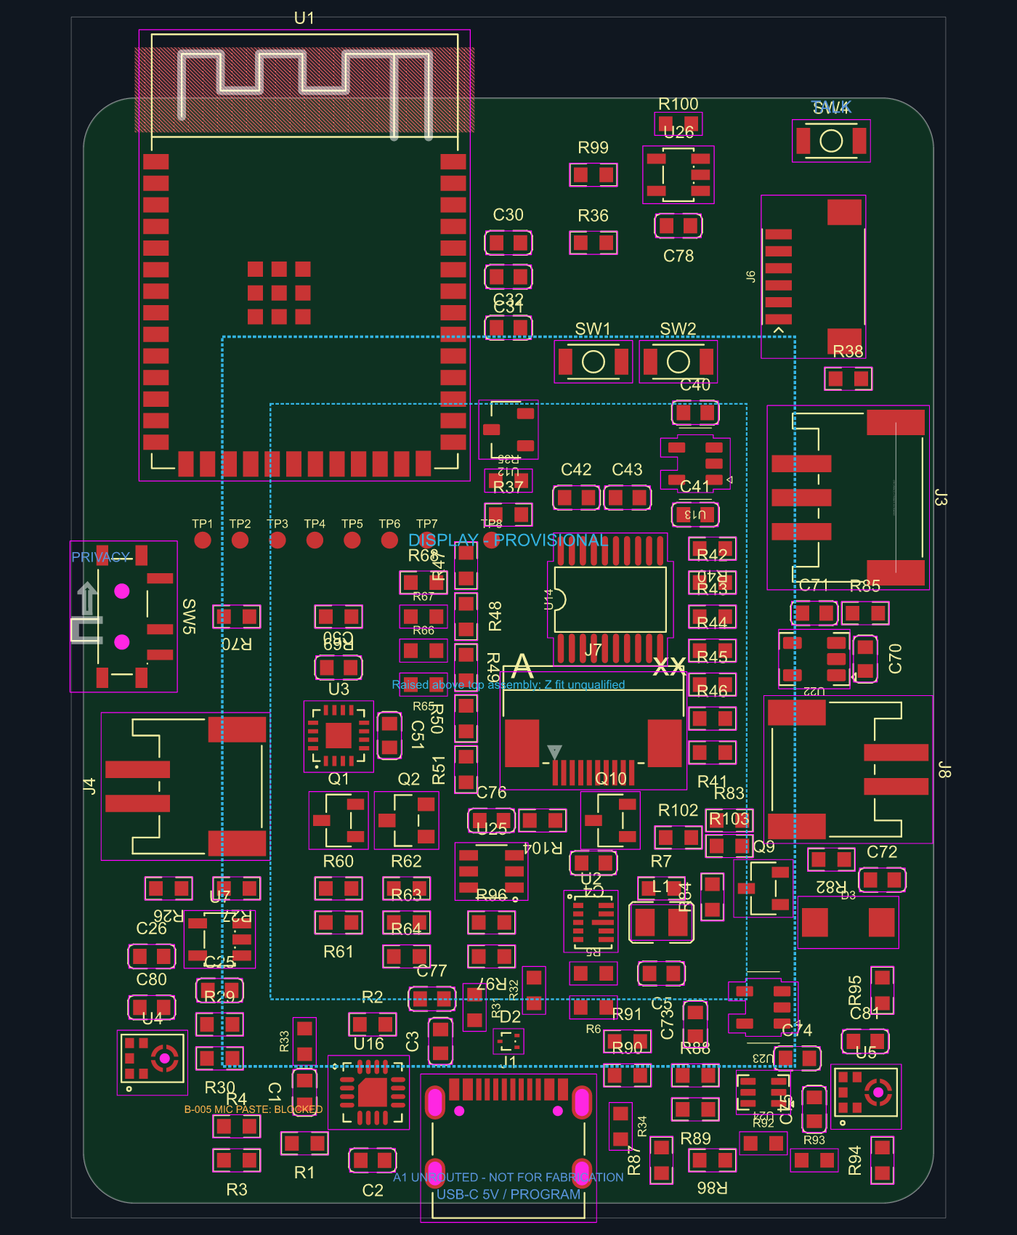
evidence/integrated-preview-2026-10-03/pcb-top.png
