AnasSarkiz/tscircuit-ai-agent-remote/evidence/integrated-preview-2026-10-03/schematic-review-2.png

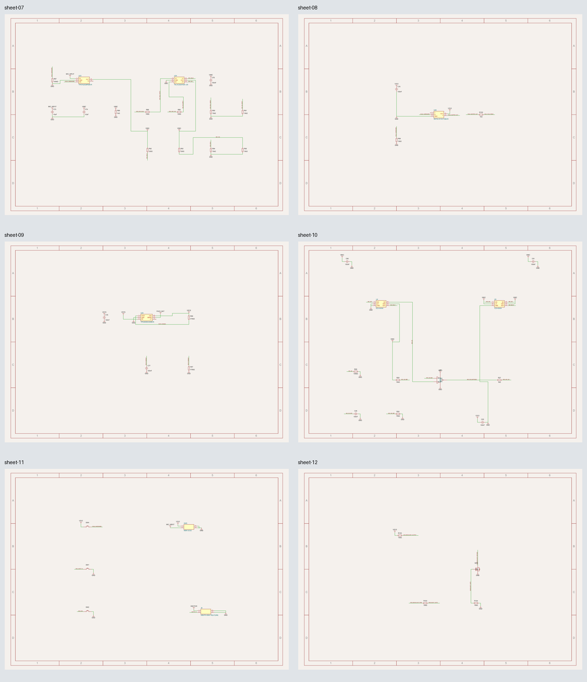
evidence/integrated-preview-2026-10-03/schematic-review-2.png
