AnasSarkiz/tscircuit-ai-agent-remote/evidence/mcu-usb-review-2026-10-03/regulator-pcb.png

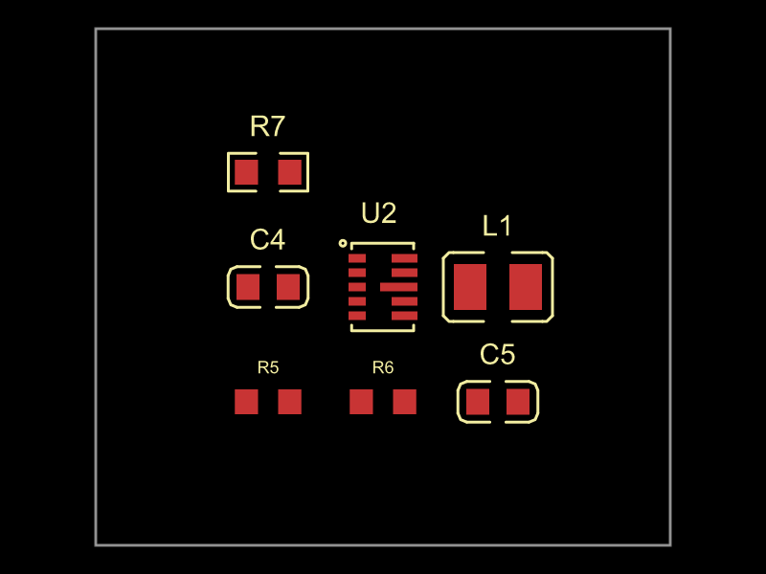
evidence/mcu-usb-review-2026-10-03/regulator-pcb.png
