AnasSarkiz/tscircuit-ai-agent-remote/evidence/mcu-usb-review-2026-10-03/switch-pcb.png

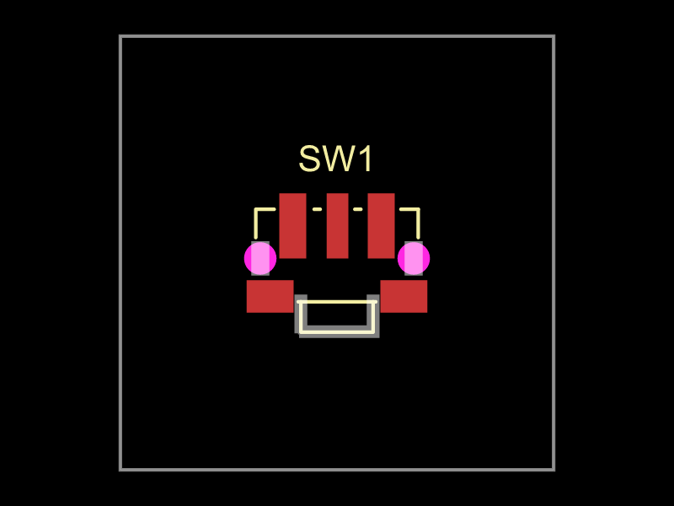
evidence/mcu-usb-review-2026-10-03/switch-pcb.png
