AnasSarkiz/tscircuit-ai-agent-remote/evidence/mechanical-envelope-review-2026-10-03/envelope-study.png

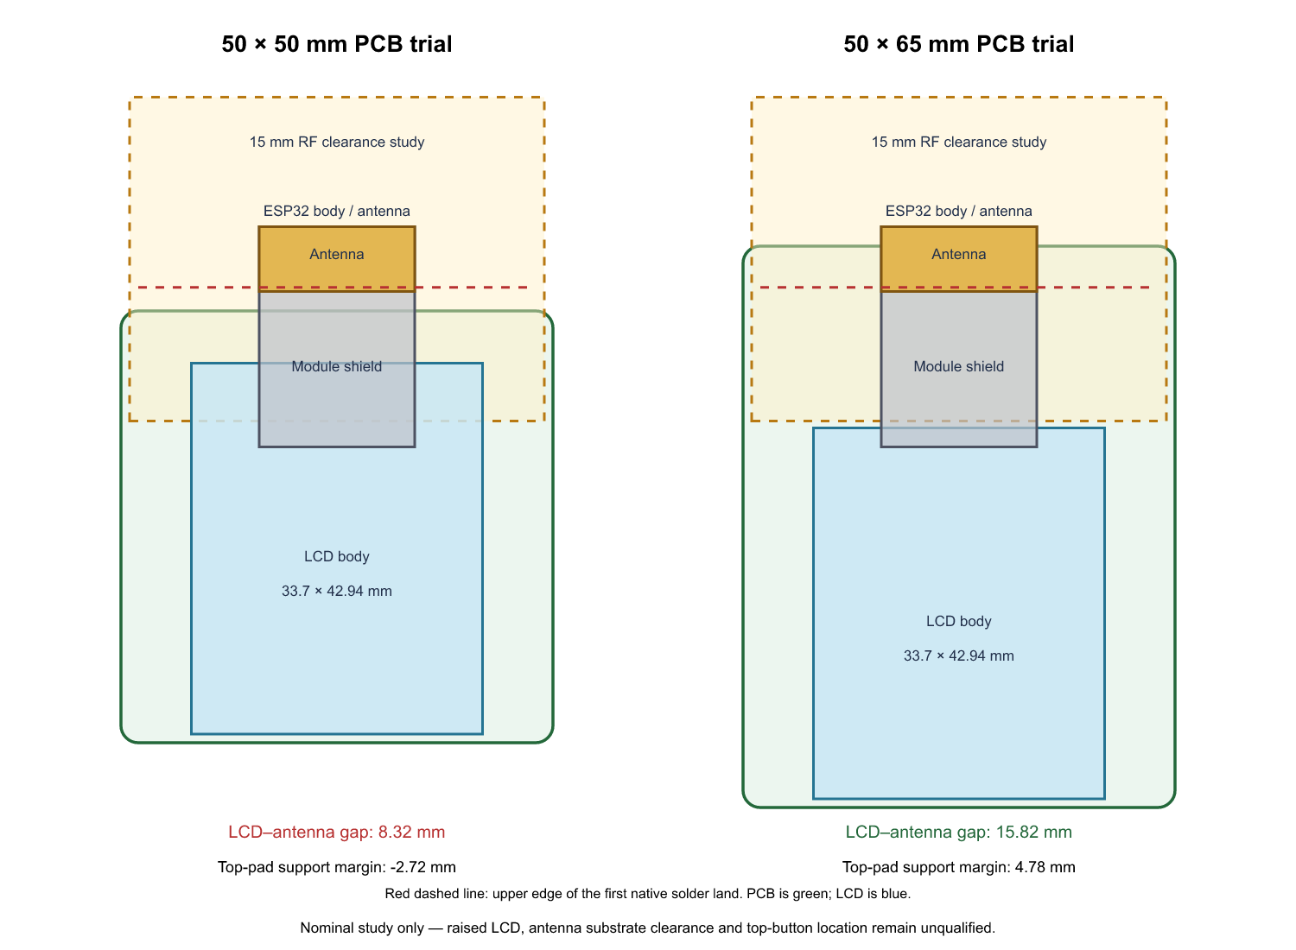
evidence/mechanical-envelope-review-2026-10-03/envelope-study.png
