AnasSarkiz/tscircuit-ai-agent-remote/evidence/microphone-local-bypass-2026-10-08/rendered/bottom.png

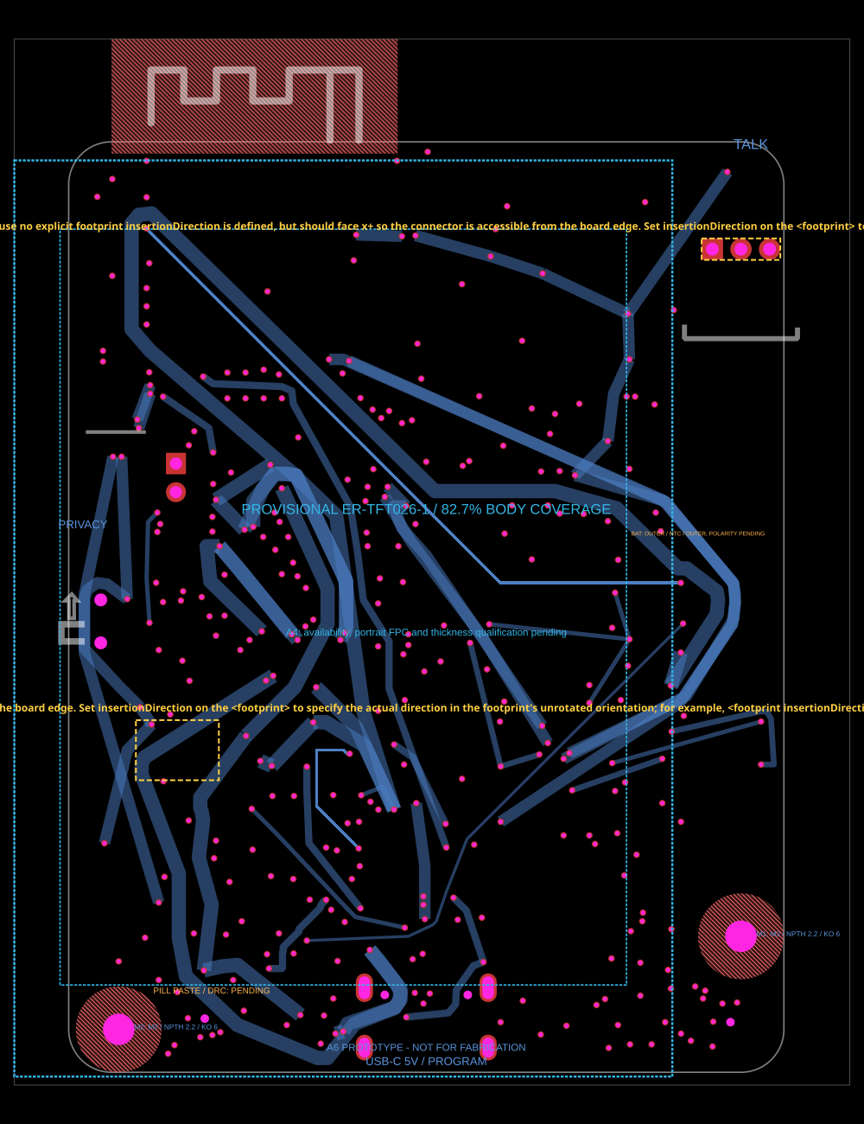
evidence/microphone-local-bypass-2026-10-08/rendered/bottom.png
