AnasSarkiz/tscircuit-ai-agent-remote/evidence/microphone-local-bypass-2026-10-08/rendered/display-backlight.png

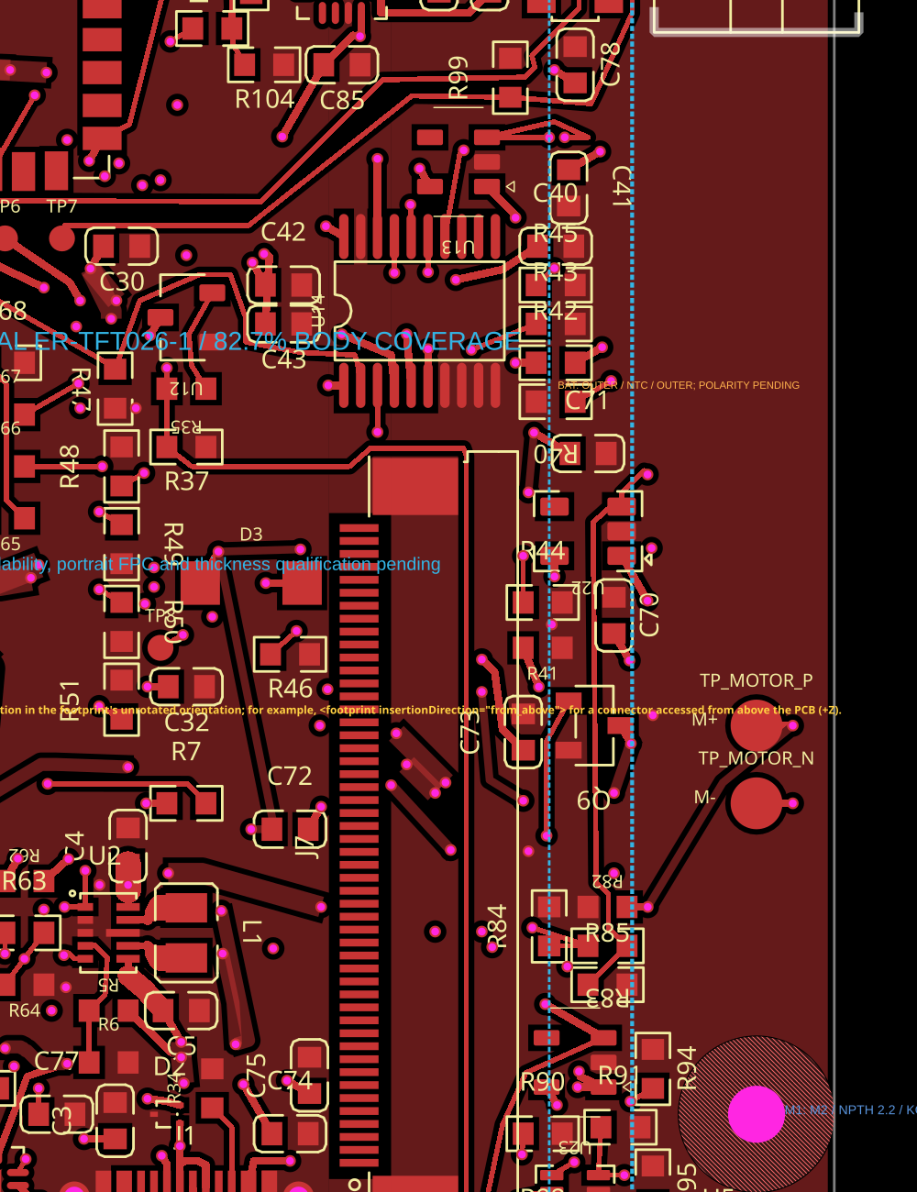
evidence/microphone-local-bypass-2026-10-08/rendered/display-backlight.png
