AnasSarkiz/tscircuit-ai-agent-remote/evidence/microphone-local-bypass-2026-10-08/rendered/inner1.png

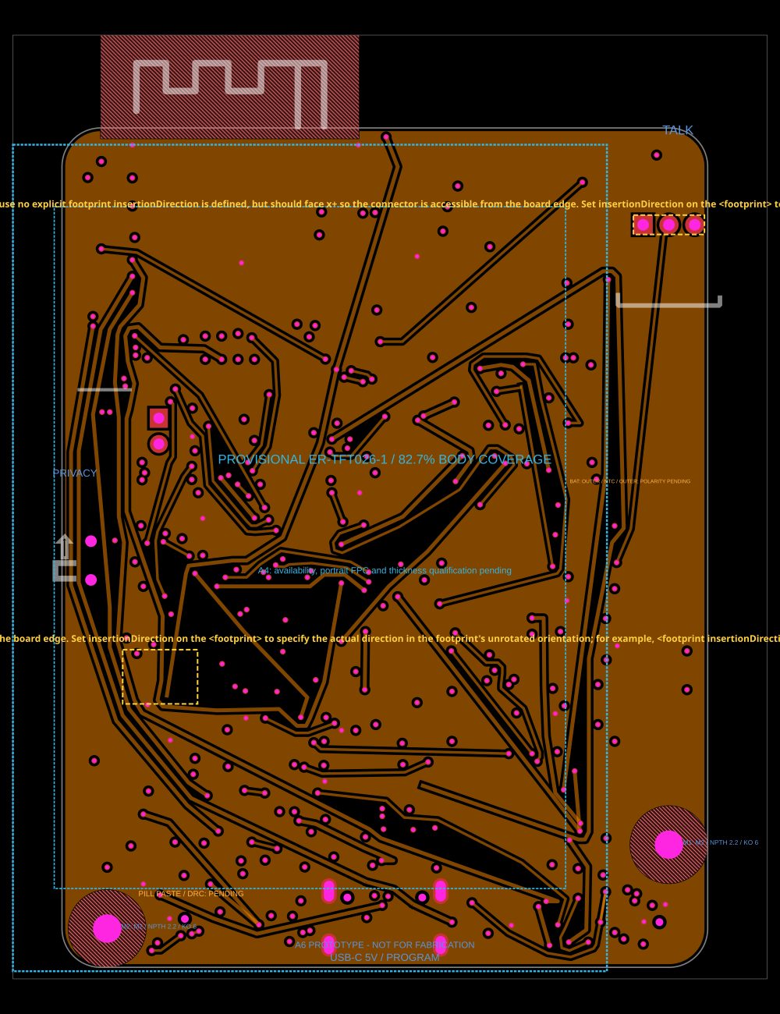
evidence/microphone-local-bypass-2026-10-08/rendered/inner1.png
