AnasSarkiz/tscircuit-ai-agent-remote/evidence/microphone-local-bypass-2026-10-08/rendered/mcu-local-bypass.png

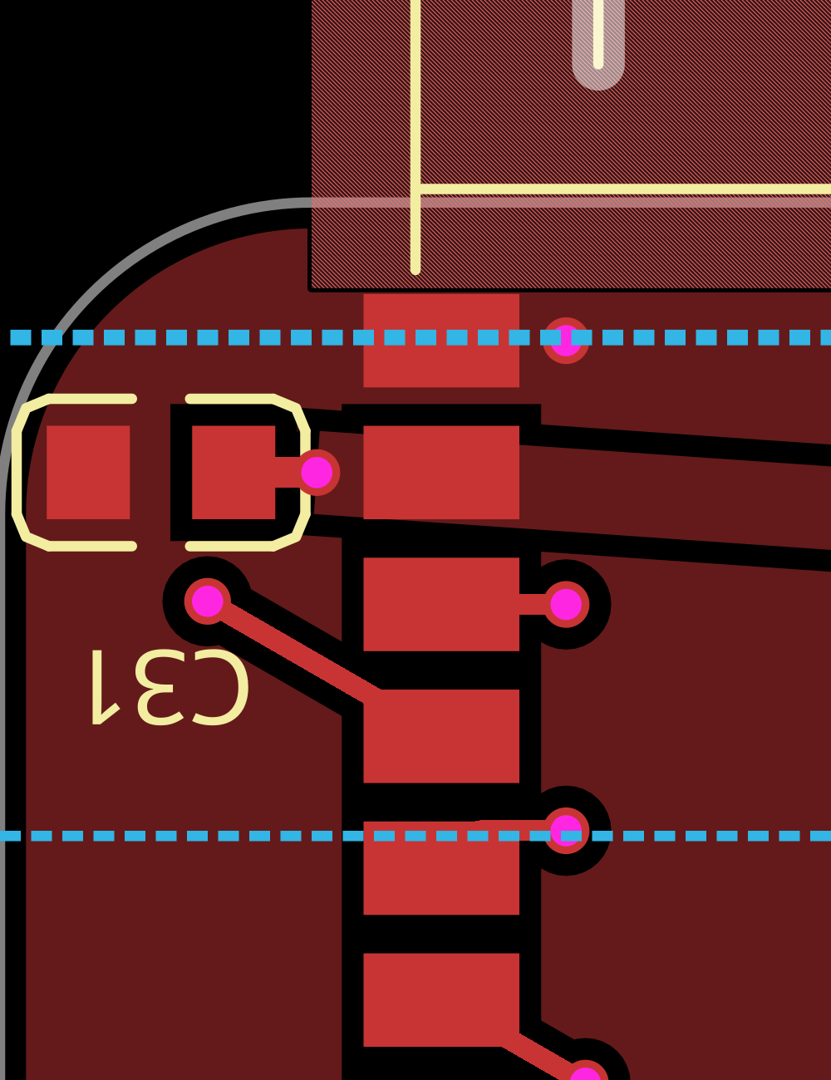
evidence/microphone-local-bypass-2026-10-08/rendered/mcu-local-bypass.png
