AnasSarkiz/tscircuit-ai-agent-remote/evidence/microphone-local-bypass-2026-10-08/rendered/speaker-output.png

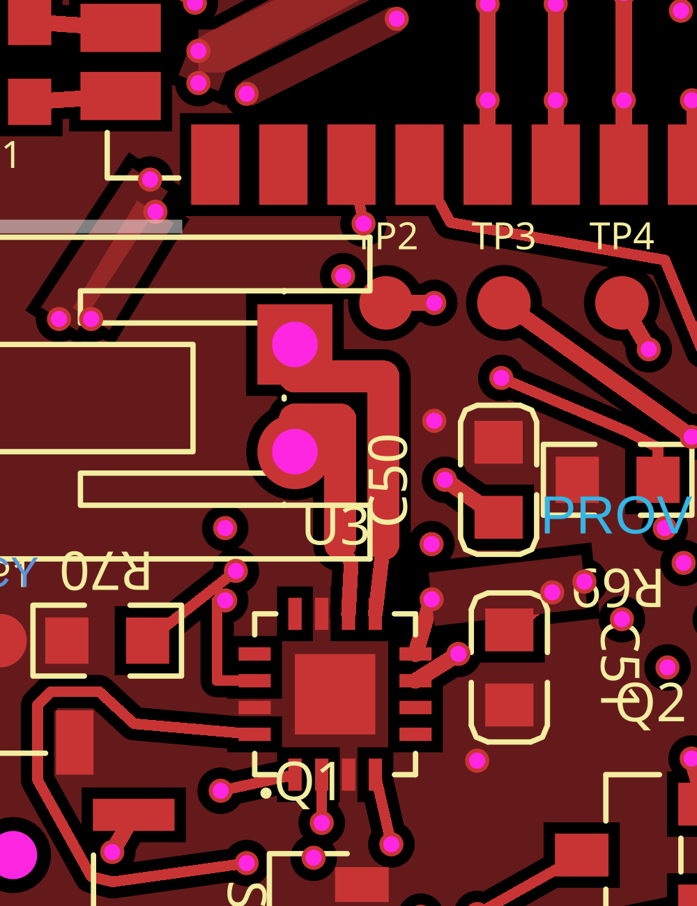
evidence/microphone-local-bypass-2026-10-08/rendered/speaker-output.png
