AnasSarkiz/tscircuit-ai-agent-remote/evidence/microphone-local-bypass-2026-10-08/rendered/top-mask.png

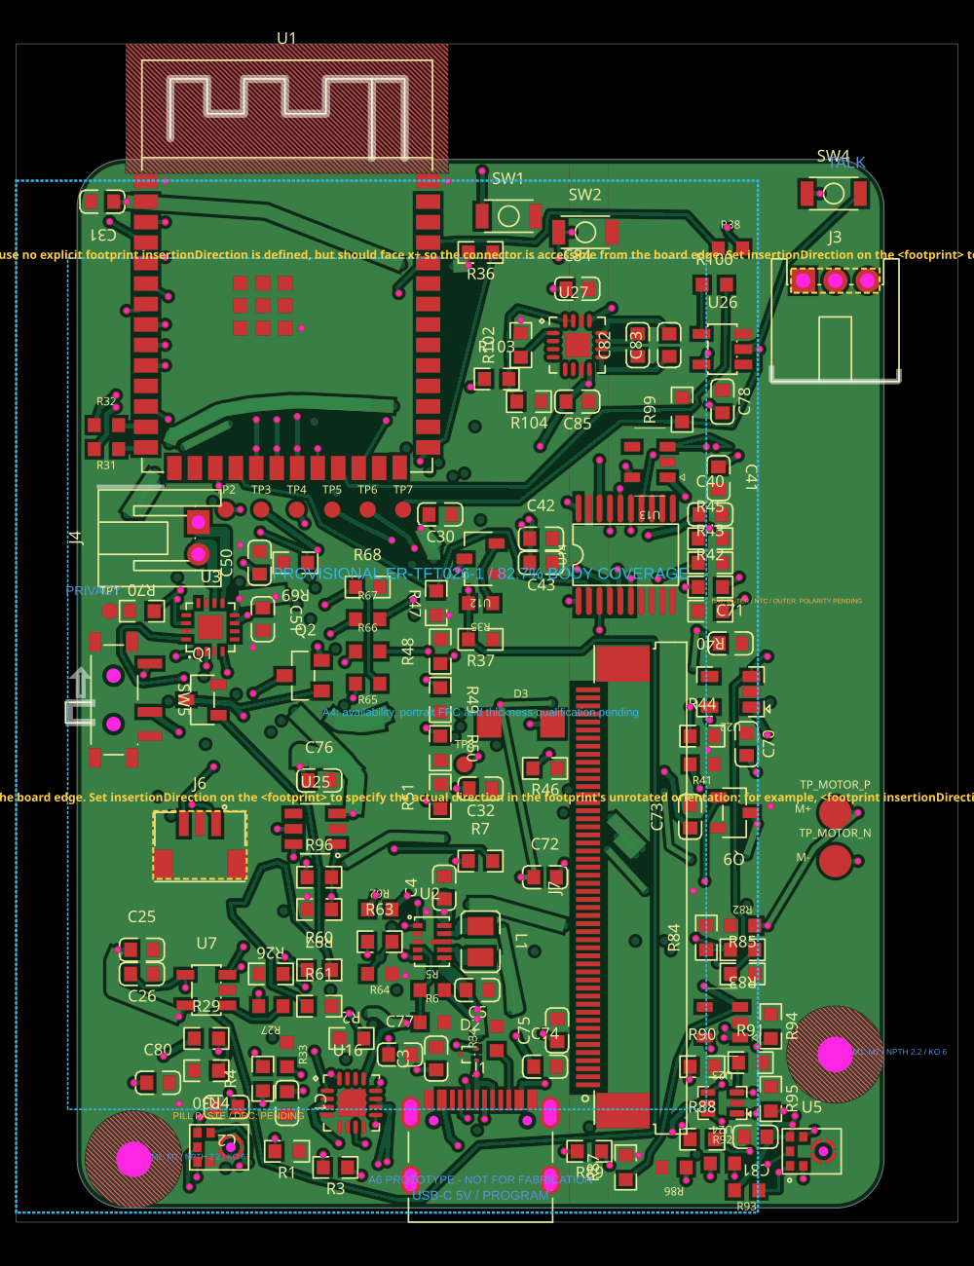
evidence/microphone-local-bypass-2026-10-08/rendered/top-mask.png
