AnasSarkiz/tscircuit-ai-agent-remote/evidence/microphone-local-bypass-2026-10-08/schematics/01-mcu-usb-review.png

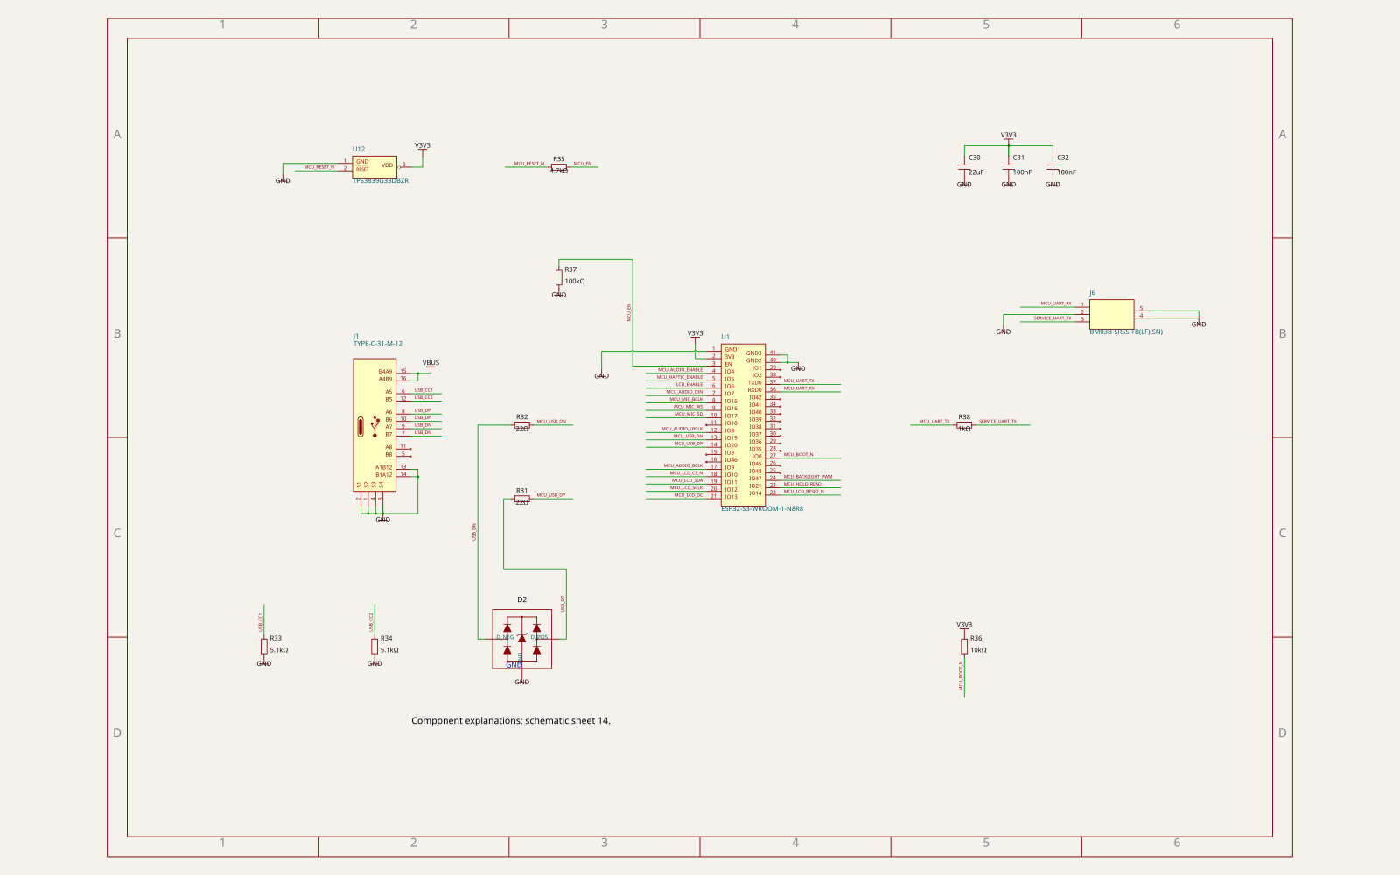
evidence/microphone-local-bypass-2026-10-08/schematics/01-mcu-usb-review.png
