AnasSarkiz/tscircuit-ai-agent-remote/evidence/microphone-local-bypass-2026-10-08/schematics/02-ChargerSheet.png

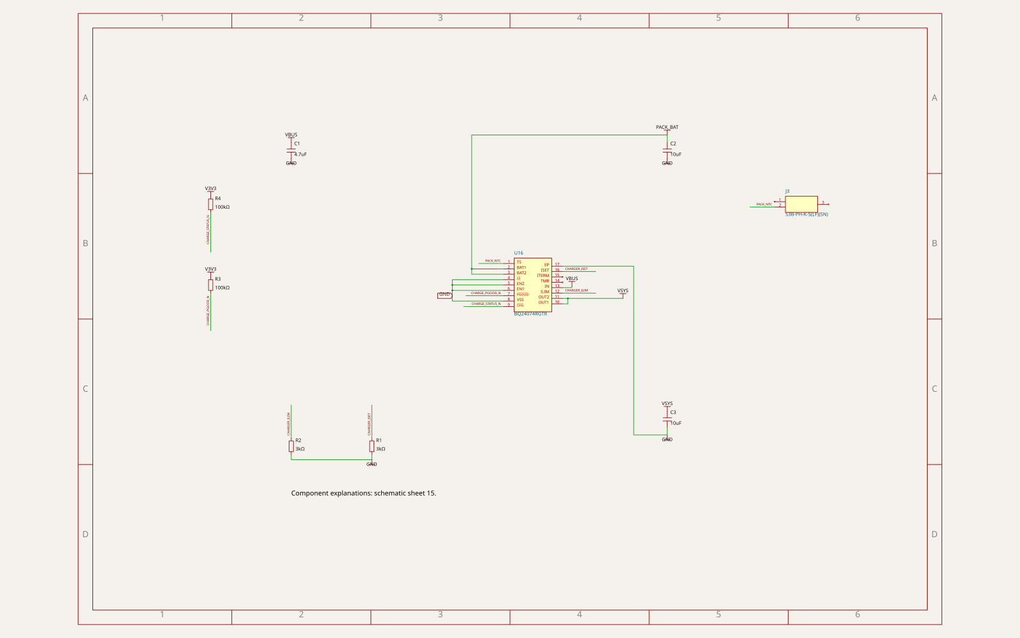
evidence/microphone-local-bypass-2026-10-08/schematics/02-ChargerSheet.png
