AnasSarkiz/tscircuit-ai-agent-remote/evidence/microphone-local-bypass-2026-10-08/schematics/03-regulated-3v3-review.png

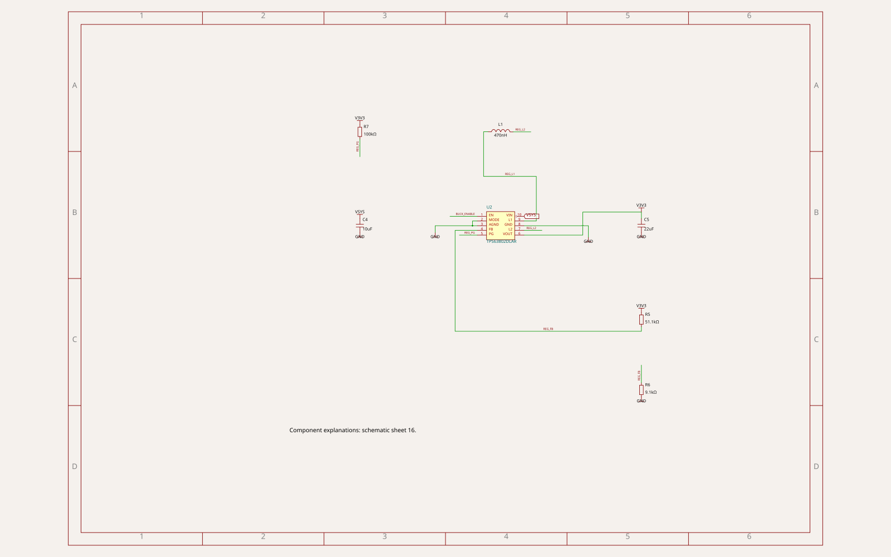
evidence/microphone-local-bypass-2026-10-08/schematics/03-regulated-3v3-review.png
