AnasSarkiz/tscircuit-ai-agent-remote/evidence/microphone-local-bypass-2026-10-08/schematics/05-speaker-amplifier-review.png

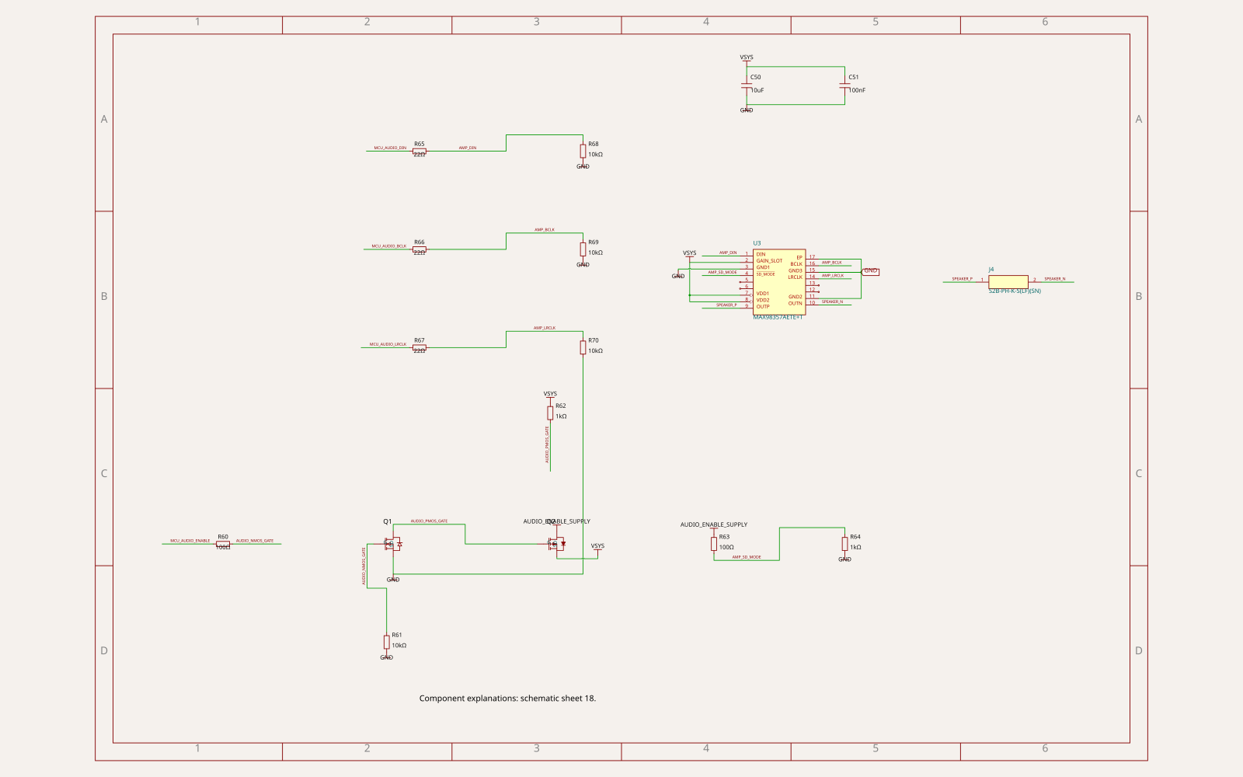
evidence/microphone-local-bypass-2026-10-08/schematics/05-speaker-amplifier-review.png
