AnasSarkiz/tscircuit-ai-agent-remote/evidence/microphone-local-bypass-2026-10-08/schematics/06-haptic-driver-review.png

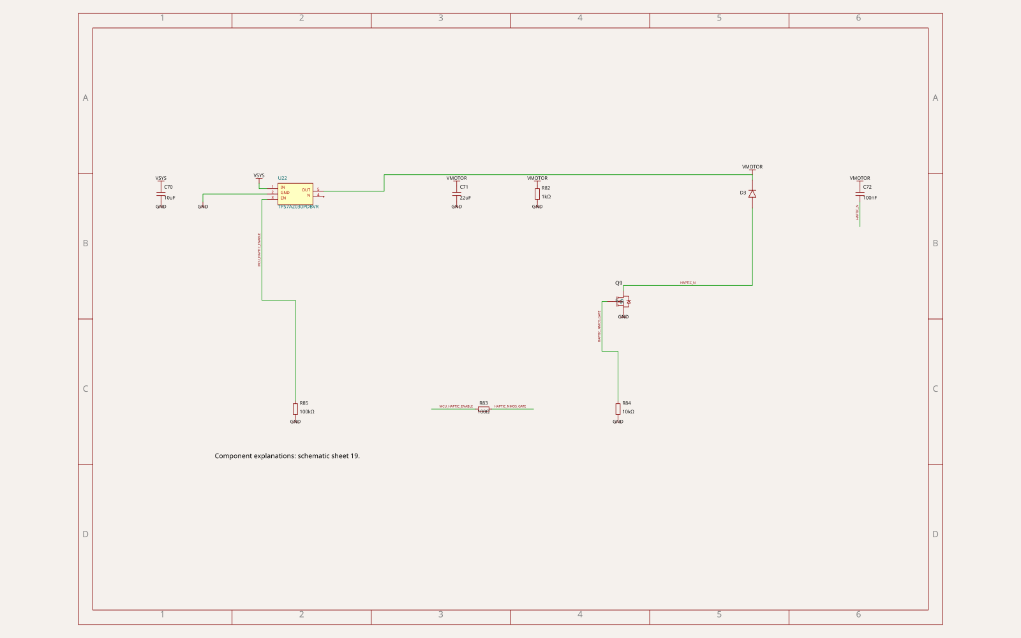
evidence/microphone-local-bypass-2026-10-08/schematics/06-haptic-driver-review.png
