AnasSarkiz/tscircuit-ai-agent-remote/evidence/microphone-local-bypass-2026-10-08/schematics/07-mic-regulated-clock-review.png

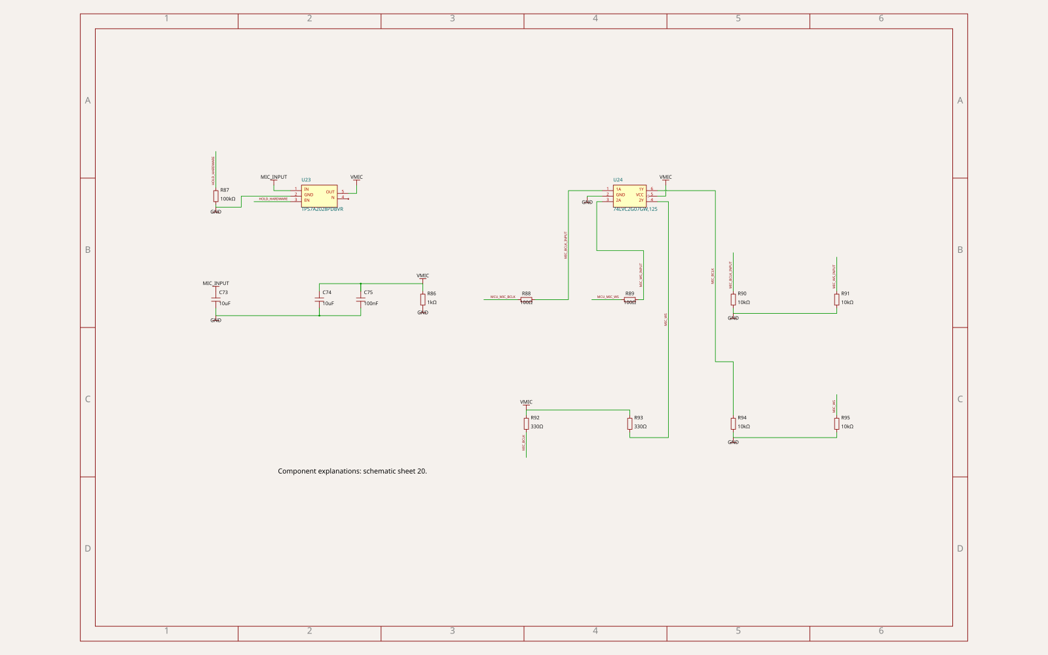
evidence/microphone-local-bypass-2026-10-08/schematics/07-mic-regulated-clock-review.png
