AnasSarkiz/tscircuit-ai-agent-remote/evidence/microphone-local-bypass-2026-10-08/schematics/10-MicrophonesSheet.png

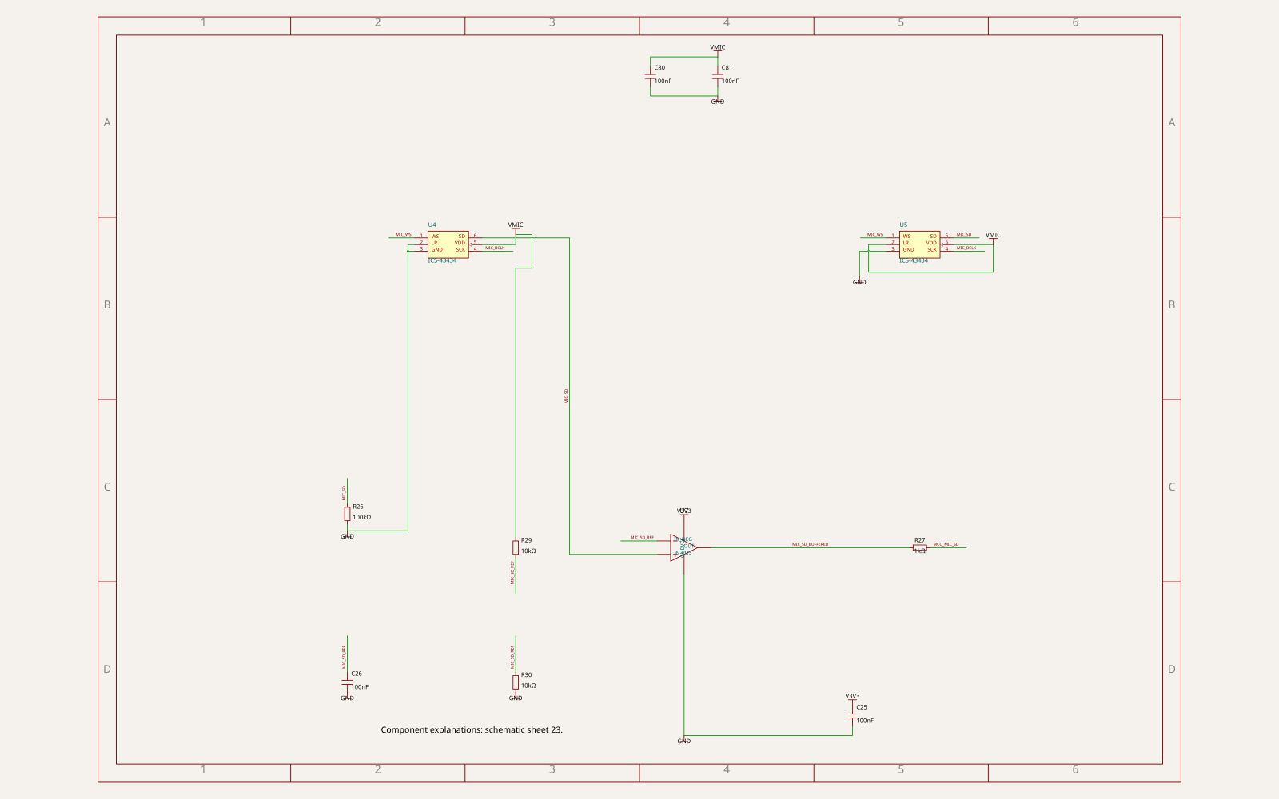
evidence/microphone-local-bypass-2026-10-08/schematics/10-MicrophonesSheet.png
