AnasSarkiz/tscircuit-ai-agent-remote/evidence/microphone-local-bypass-2026-10-08/schematics/12-BacklightSheet.png

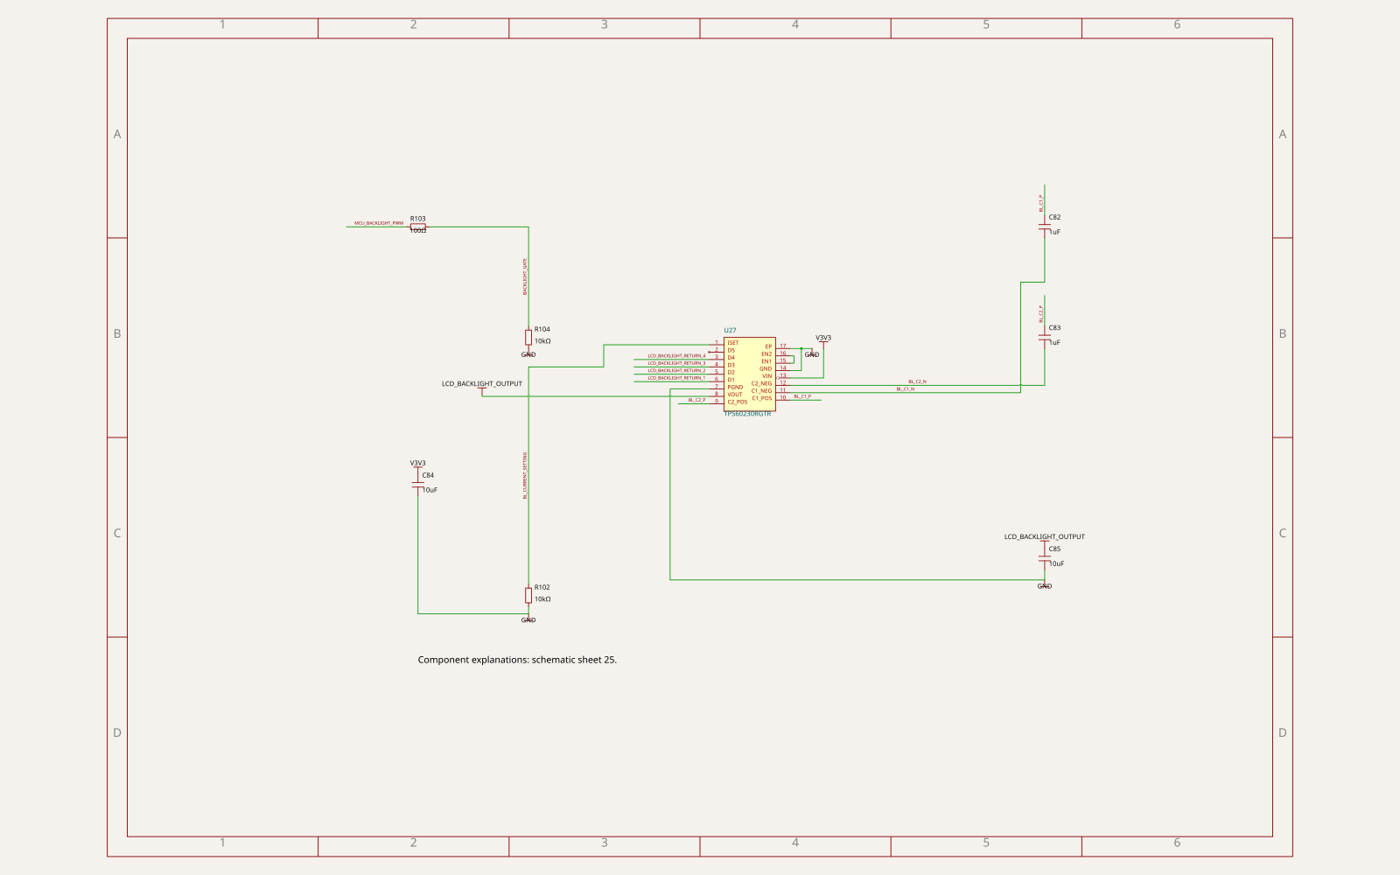
evidence/microphone-local-bypass-2026-10-08/schematics/12-BacklightSheet.png
