AnasSarkiz/tscircuit-ai-agent-remote/evidence/microphone-local-bypass-2026-10-08/ui-analysis/sandbox-ui-style-analysis.png

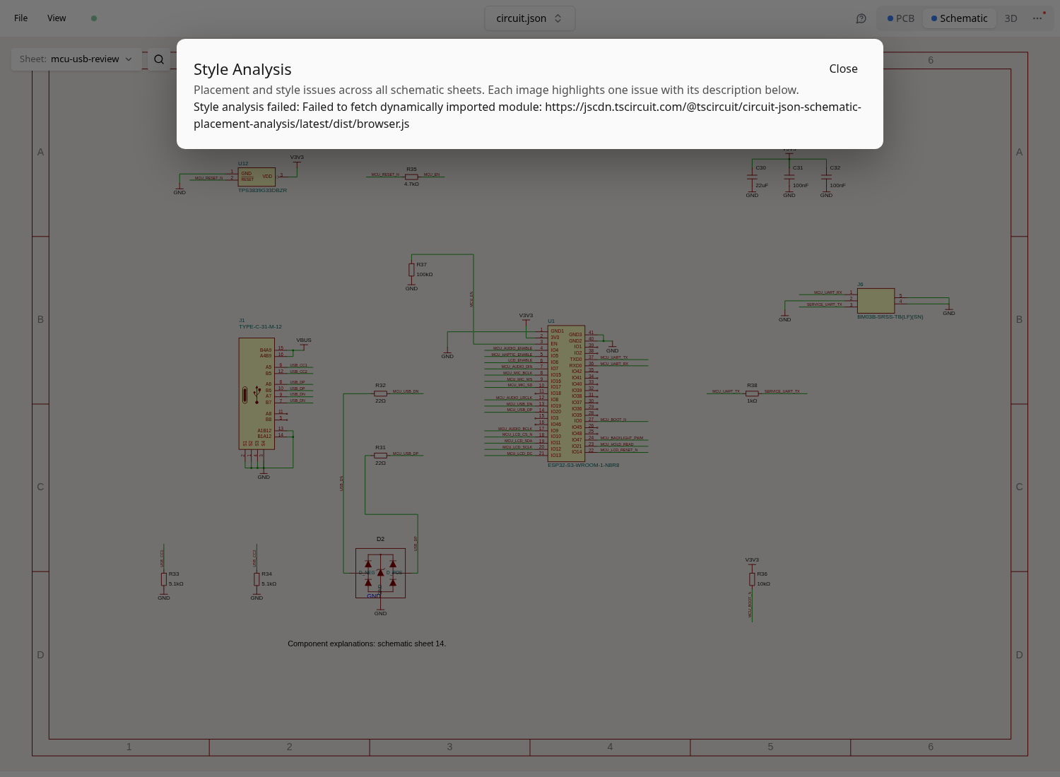
evidence/microphone-local-bypass-2026-10-08/ui-analysis/sandbox-ui-style-analysis.png
