AnasSarkiz/tscircuit-ai-agent-remote/evidence/microphone-open-drain-review-2026-10-03/pcb.png

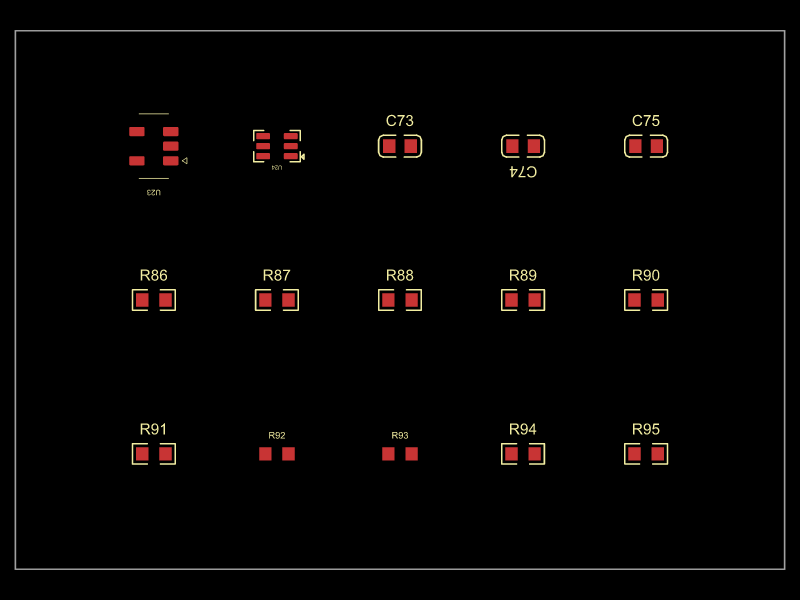
evidence/microphone-open-drain-review-2026-10-03/pcb.png
