AnasSarkiz/tscircuit-ai-agent-remote/evidence/pcb-completion-2026-10-08/before-final-label-clearance/ui-analysis/ui-style-analysis.png

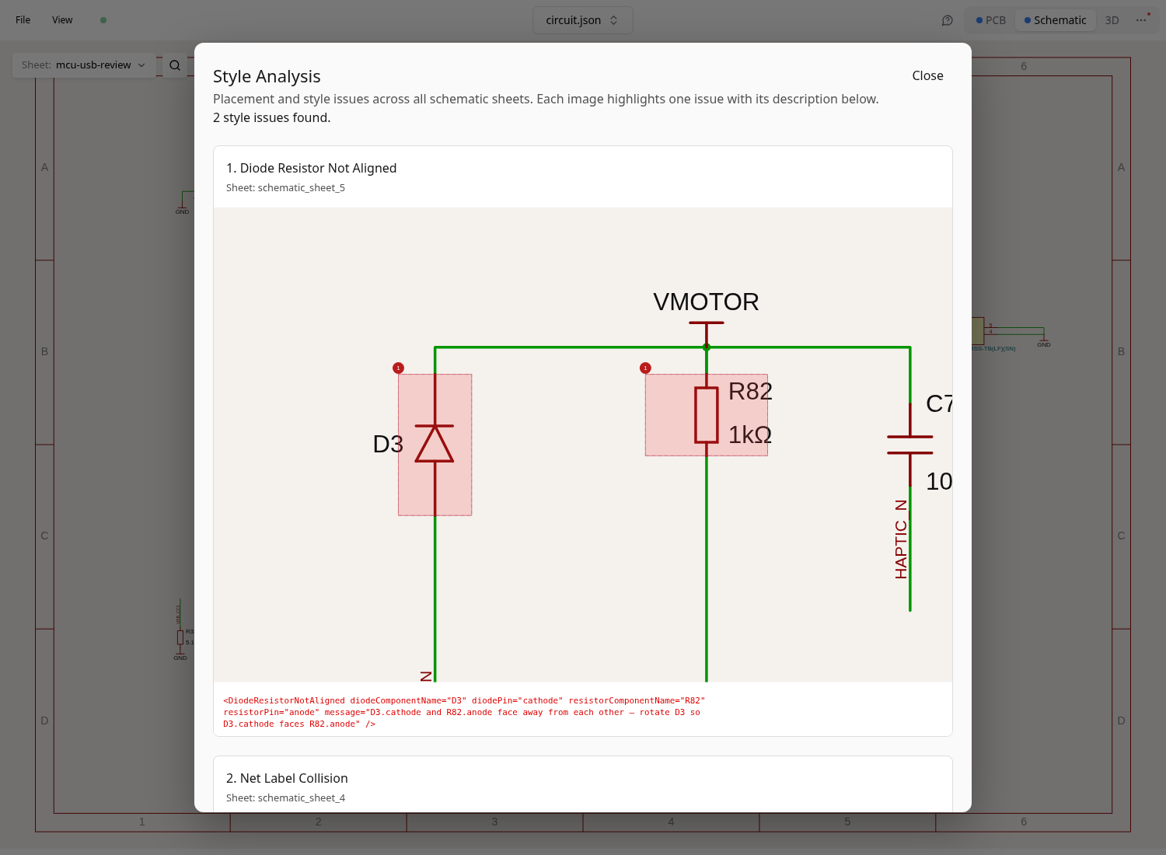
evidence/pcb-completion-2026-10-08/before-final-label-clearance/ui-analysis/ui-style-analysis.png
