AnasSarkiz/tscircuit-ai-agent-remote/evidence/pcb-completion-2026-10-08/jst-ph-numbering-2.png

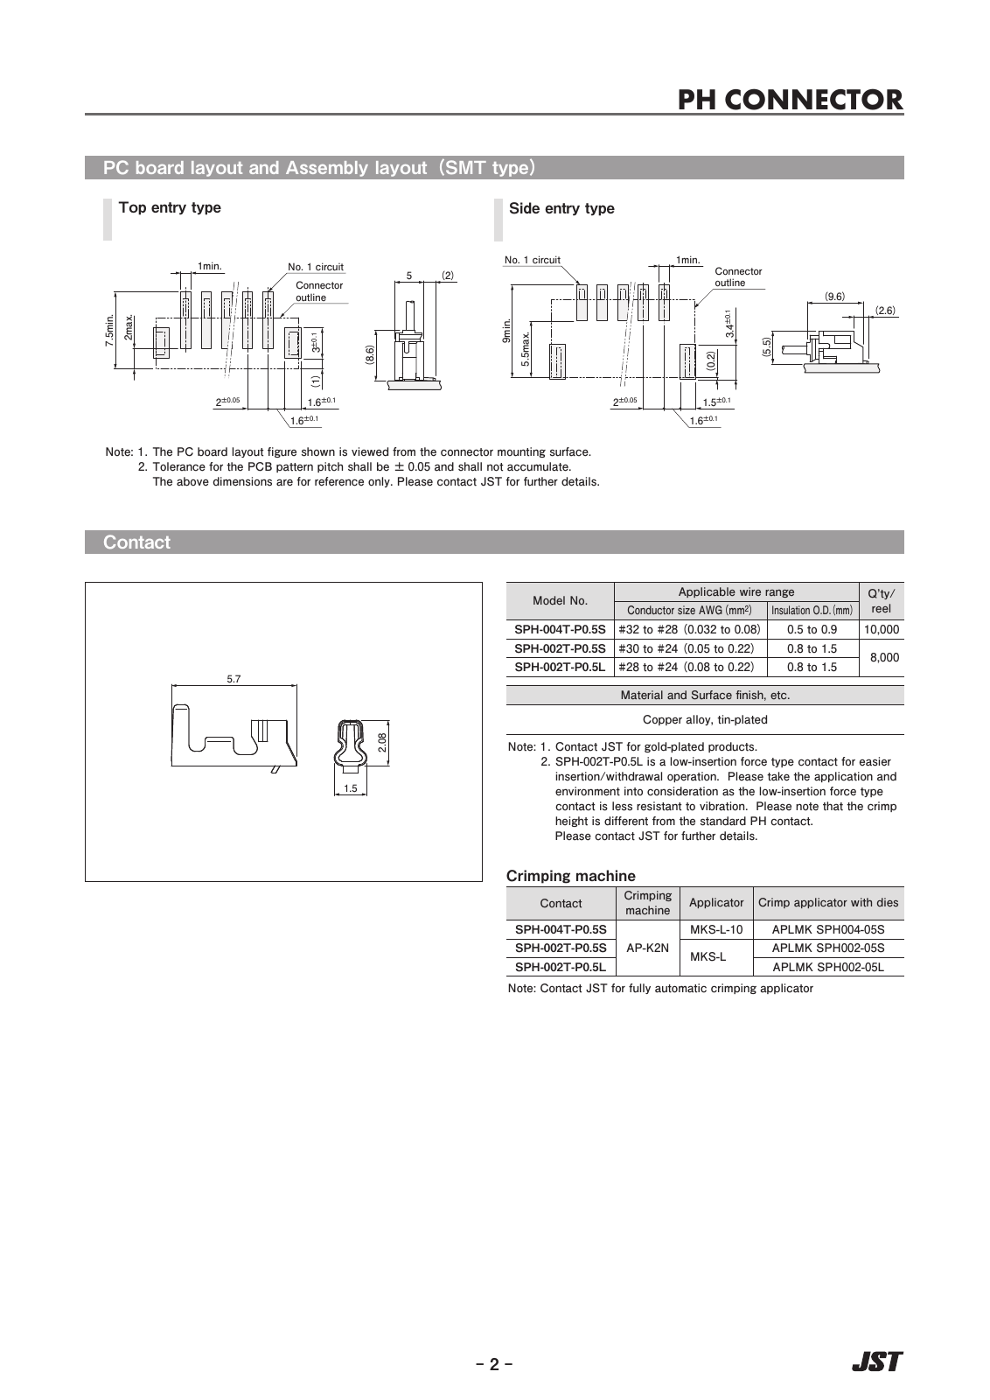
evidence/pcb-completion-2026-10-08/jst-ph-numbering-2.png
