AnasSarkiz/tscircuit-ai-agent-remote/evidence/pcb-completion-2026-10-08/pill-paste-margins.png

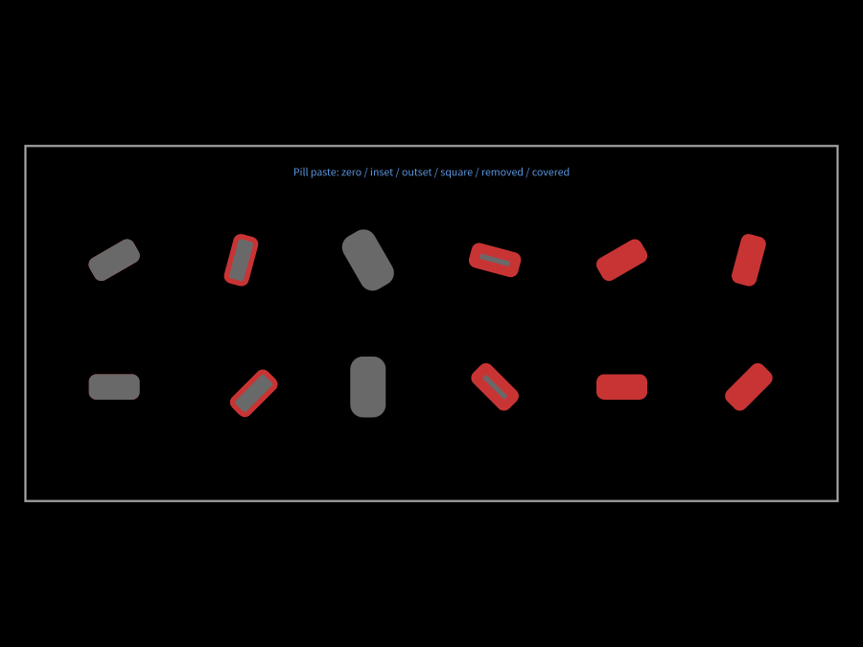
evidence/pcb-completion-2026-10-08/pill-paste-margins.png
