AnasSarkiz/tscircuit-ai-agent-remote/evidence/routing-continuation-2026-10-07/snapshot-review/pcb-current-cli.png

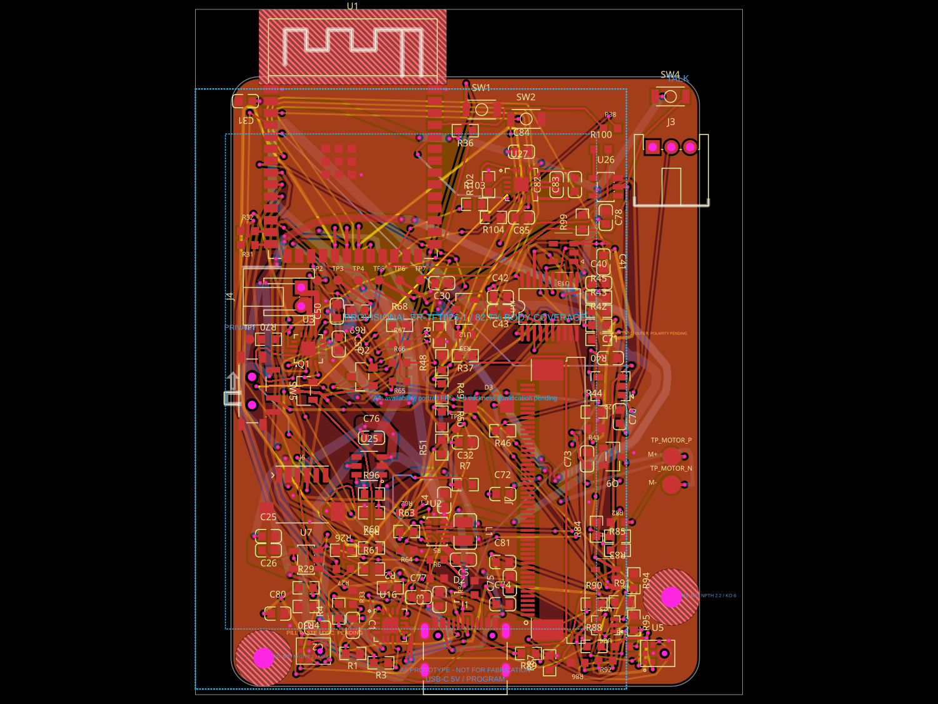
evidence/routing-continuation-2026-10-07/snapshot-review/pcb-current-cli.png
