AnasSarkiz/tscircuit-ai-agent-remote/evidence/routing-continuation-2026-10-07/snapshot-review/schematic-current-cli.png

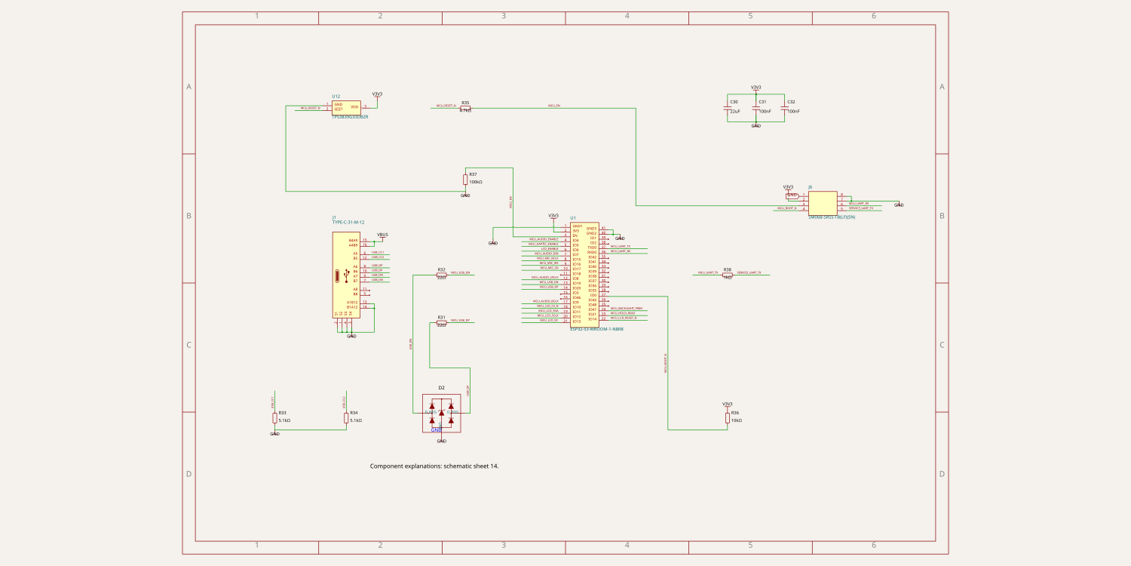
evidence/routing-continuation-2026-10-07/snapshot-review/schematic-current-cli.png
