AnasSarkiz/tscircuit-ai-agent-remote/evidence/routing-continuation-2026-10-07/snapshot-review/schematic-original.png

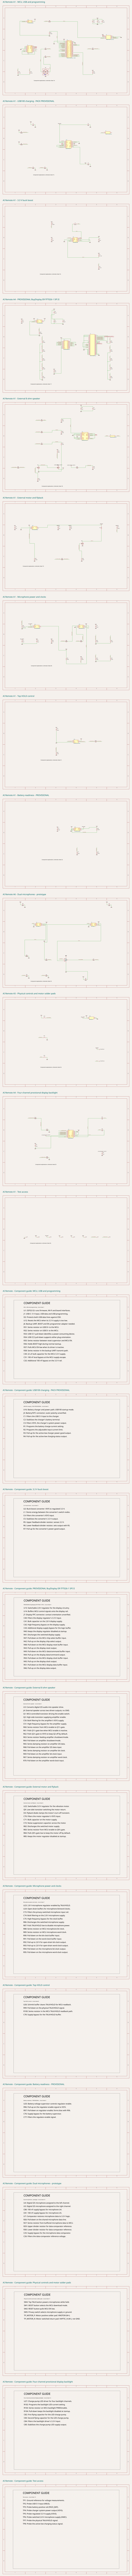
evidence/routing-continuation-2026-10-07/snapshot-review/schematic-original.png
