AnasSarkiz/tscircuit-ai-agent-remote/evidence/routing-continuation-2026-10-07/ui-style-analysis.png

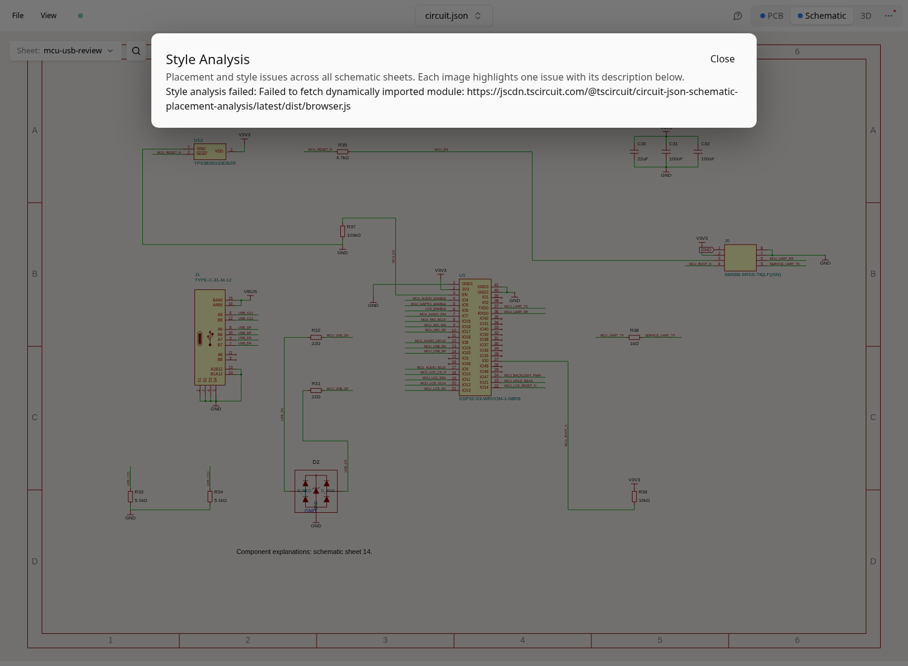
evidence/routing-continuation-2026-10-07/ui-style-analysis.png
