AnasSarkiz/tscircuit-ai-agent-remote/evidence/routing-intake-2026-10-04/display-10.png

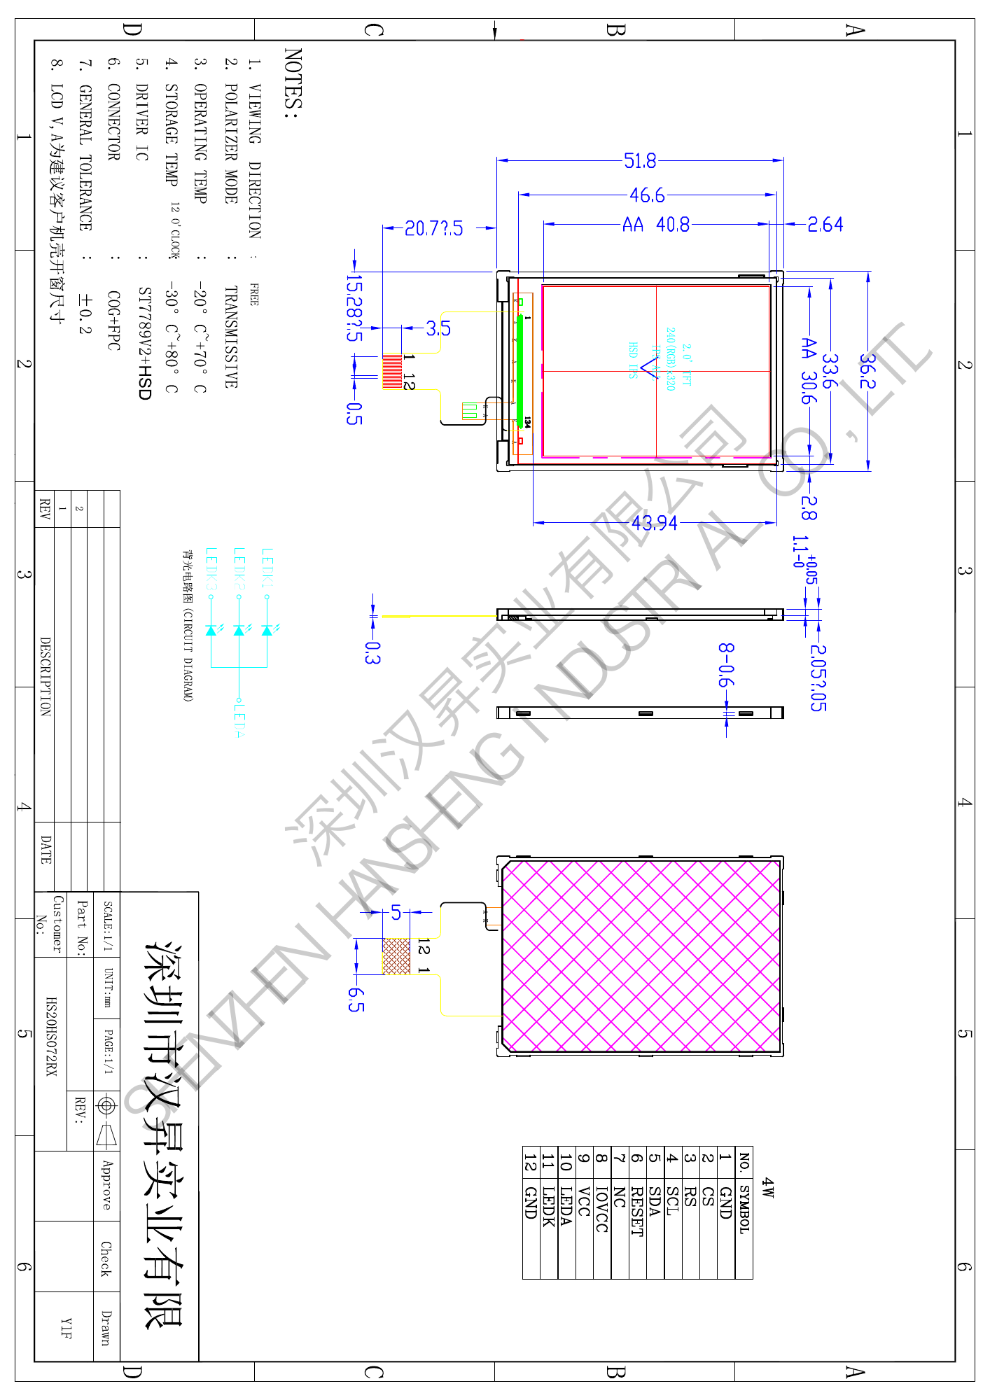
evidence/routing-intake-2026-10-04/display-10.png
