AnasSarkiz/tscircuit-ai-agent-remote/evidence/routing-intake-2026-10-04/display-11.png

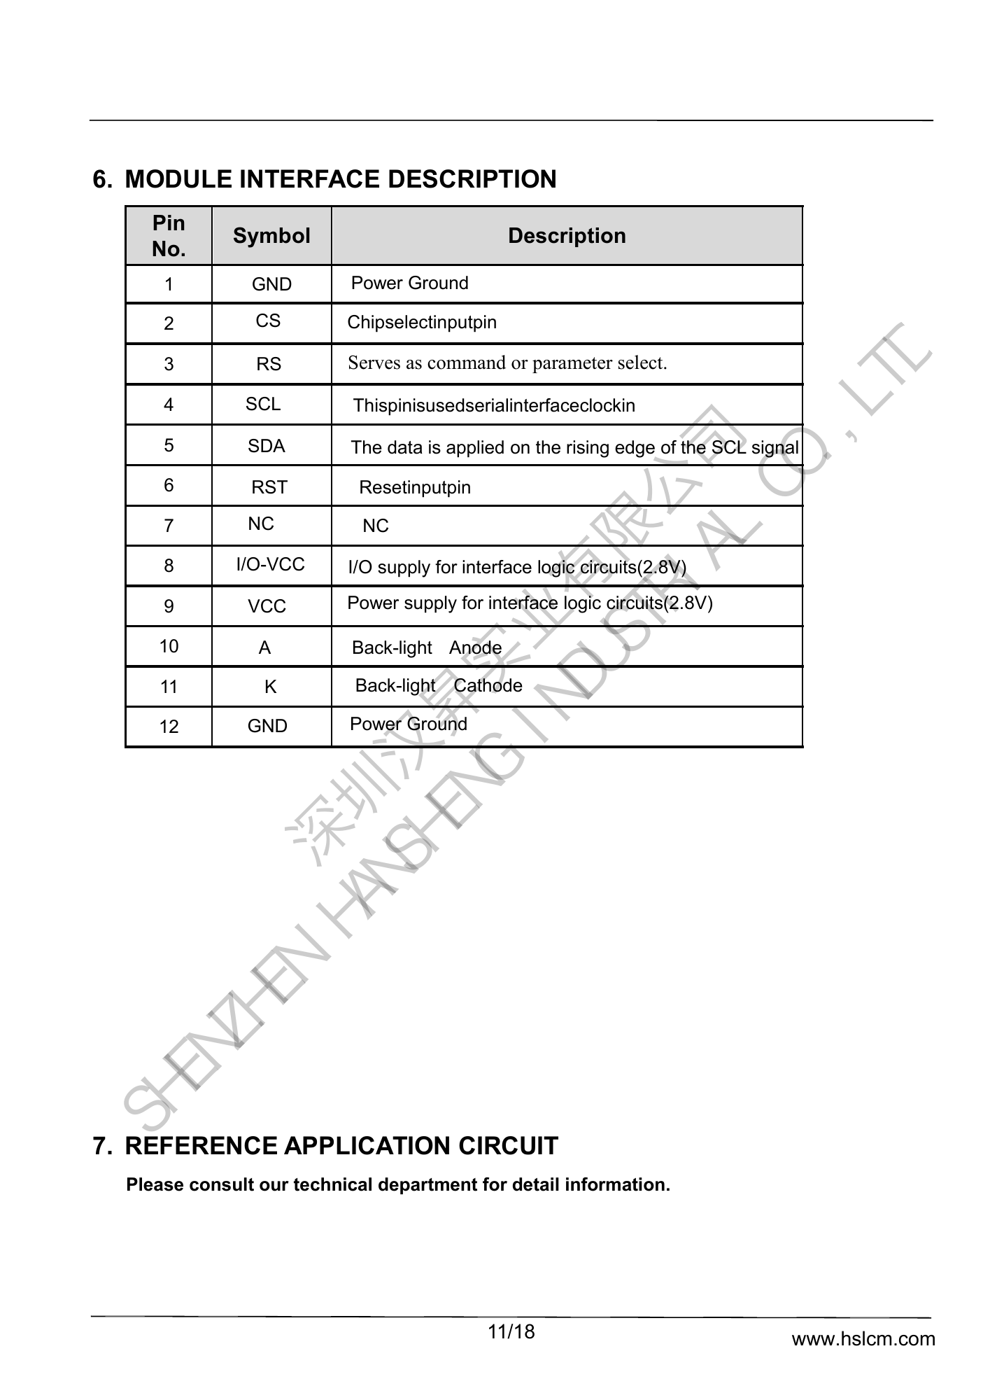
evidence/routing-intake-2026-10-04/display-11.png
