AnasSarkiz/tscircuit-ai-agent-remote/evidence/routing-intake-2026-10-04/display-ribbon.png

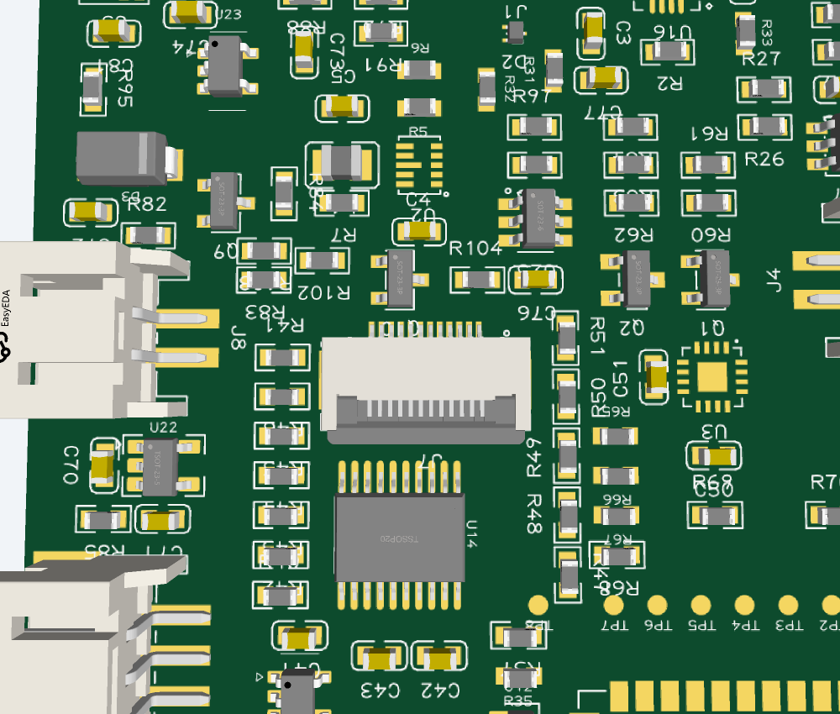
evidence/routing-intake-2026-10-04/display-ribbon.png
