AnasSarkiz/tscircuit-ai-agent-remote/evidence/routing-intake-2026-10-04/pcb-ratsnest.png

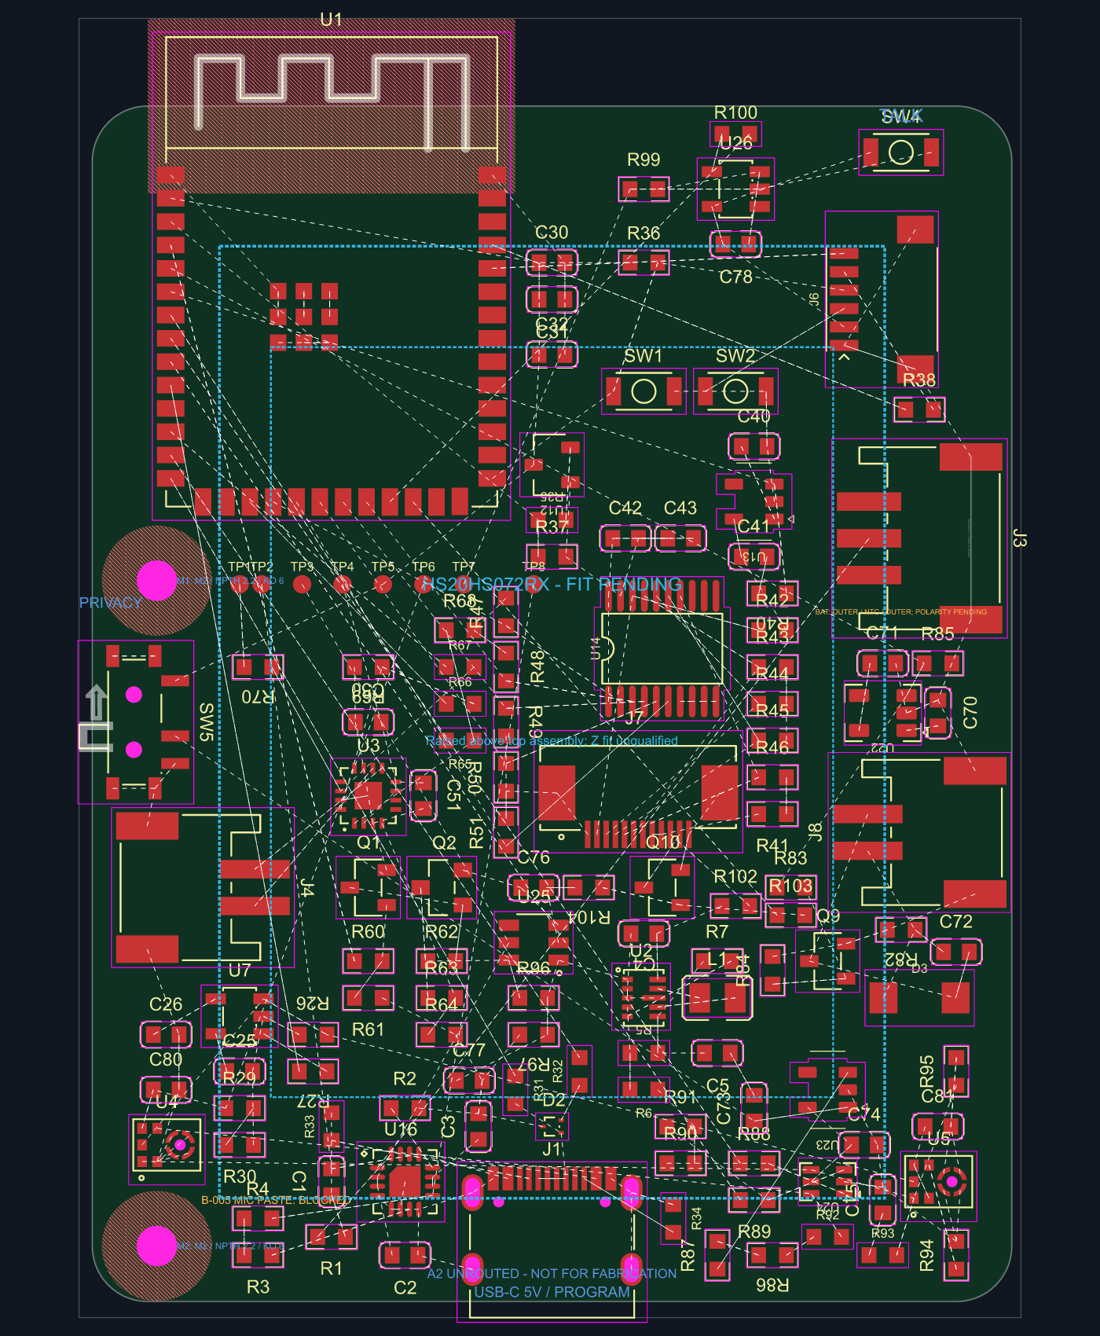
evidence/routing-intake-2026-10-04/pcb-ratsnest.png
