AnasSarkiz/tscircuit-ai-agent-remote/evidence/routing-intake-2026-10-04/pcb-top.png

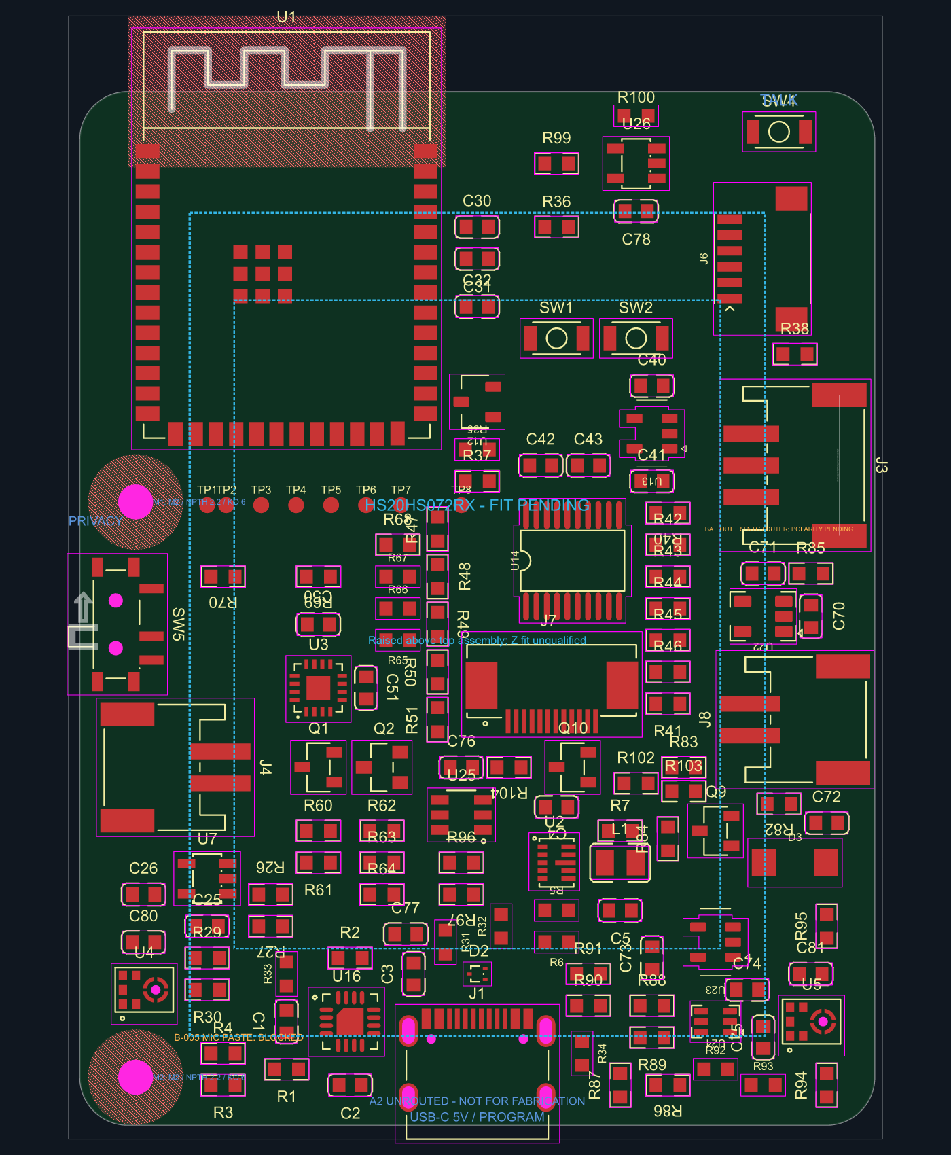
evidence/routing-intake-2026-10-04/pcb-top.png
