AnasSarkiz/tscircuit-ai-agent-remote/evidence/routing-intake-2026-10-04/sheet-06.png

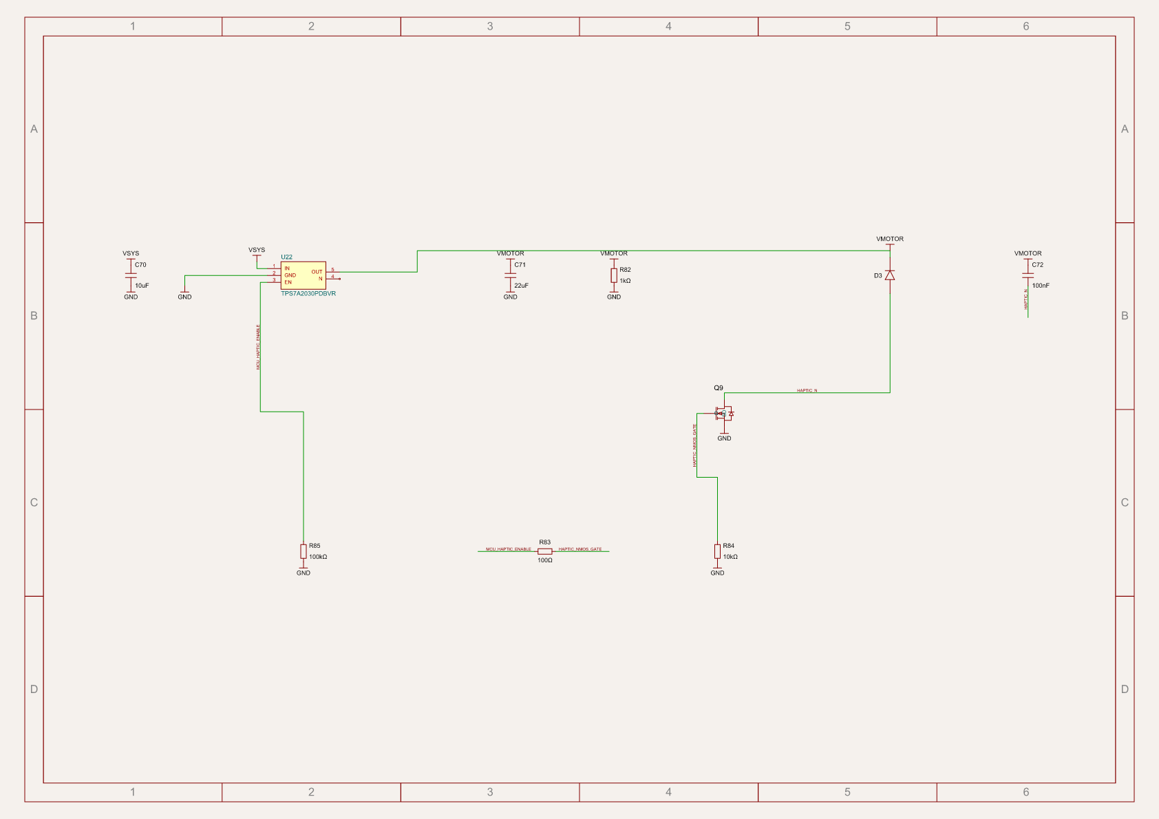
evidence/routing-intake-2026-10-04/sheet-06.png
