AnasSarkiz/tscircuit-ai-agent-remote/evidence/routing-intake-2026-10-04/sheet-10.png

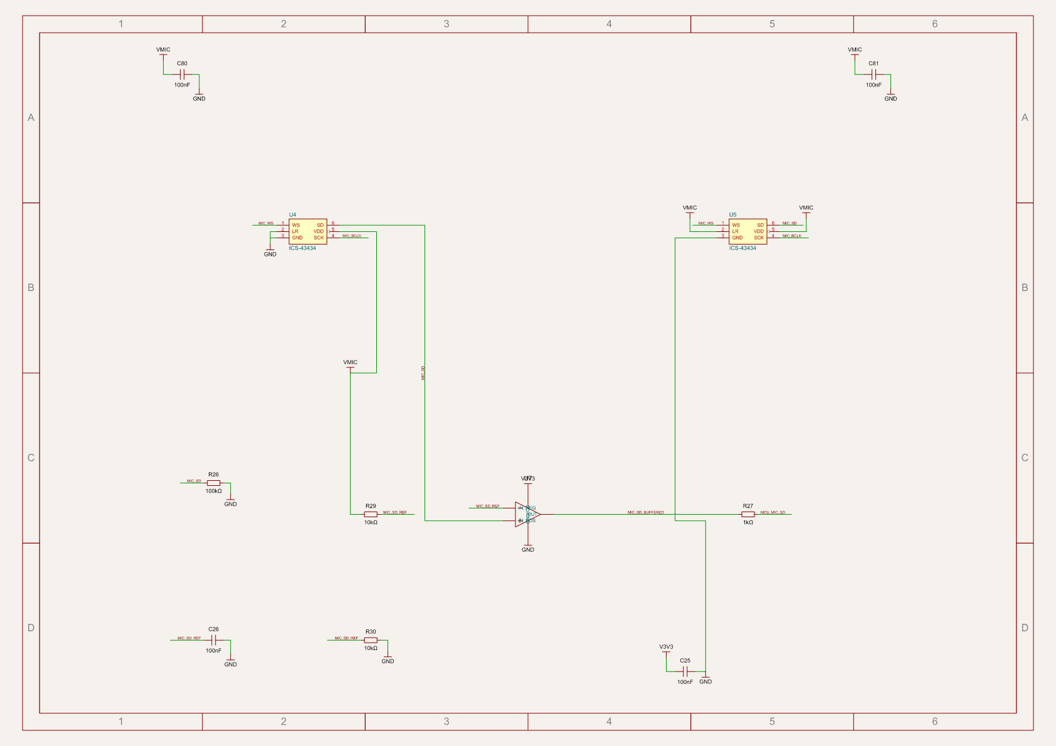
evidence/routing-intake-2026-10-04/sheet-10.png
