AnasSarkiz/tscircuit-ai-agent-remote/evidence/routing-intake-2026-10-04/sheet-11.png

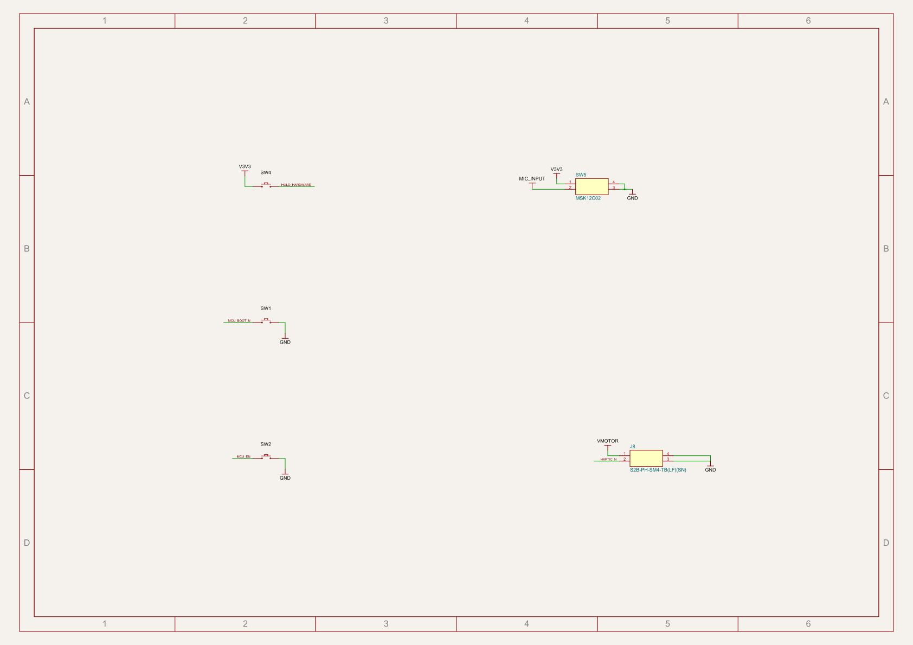
evidence/routing-intake-2026-10-04/sheet-11.png
