AnasSarkiz/tscircuit-ai-agent-remote/evidence/routing-intake-2026-10-04/speaker-left-edge.png

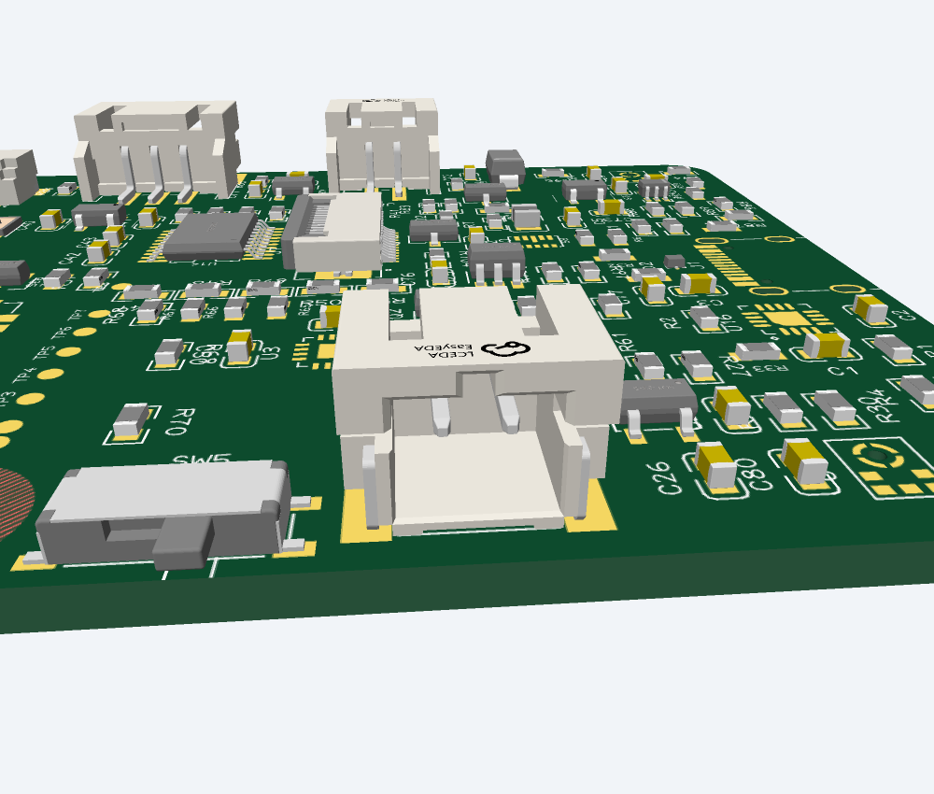
evidence/routing-intake-2026-10-04/speaker-left-edge.png
