AnasSarkiz/tscircuit-ai-agent-remote/evidence/routing-intake-2026-10-04/usb-bottom-edge.png

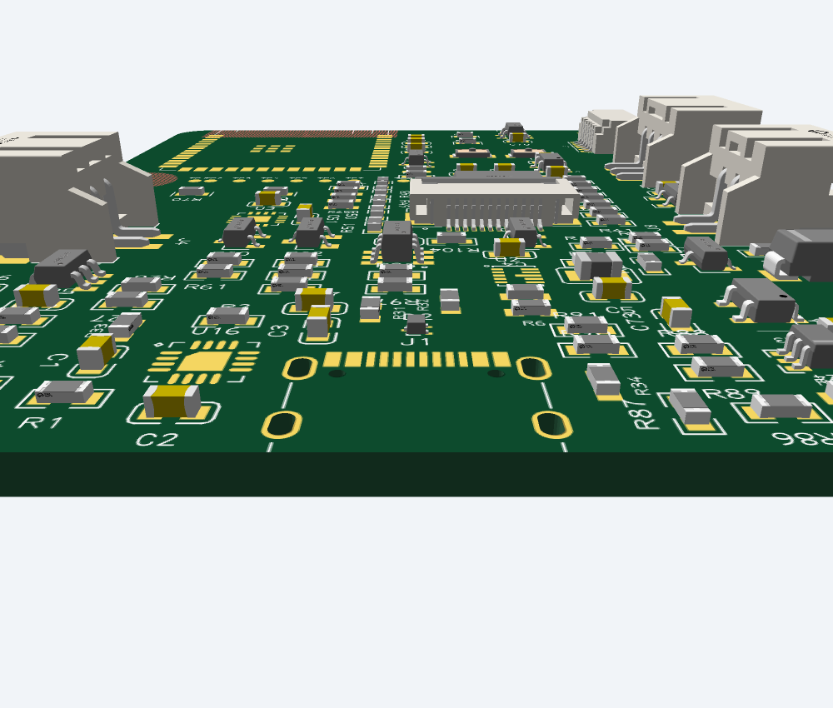
evidence/routing-intake-2026-10-04/usb-bottom-edge.png
