AnasSarkiz/tscircuit-ai-agent-remote/evidence/schematic-component-notes-2026-10-06/final-views/circuit-overview.png

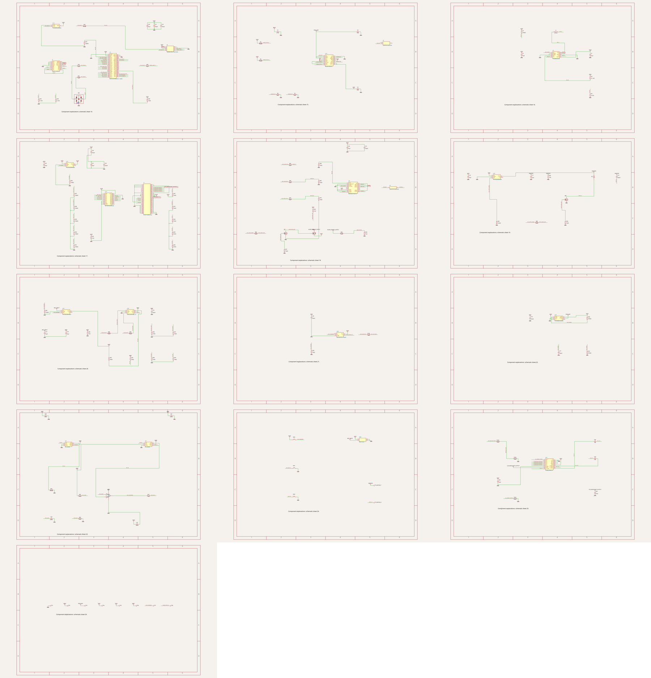
evidence/schematic-component-notes-2026-10-06/final-views/circuit-overview.png
