AnasSarkiz/tscircuit-ai-agent-remote/evidence/six-point-board-review-2026-10-06/final-schematics/circuits-8-13-contact.png

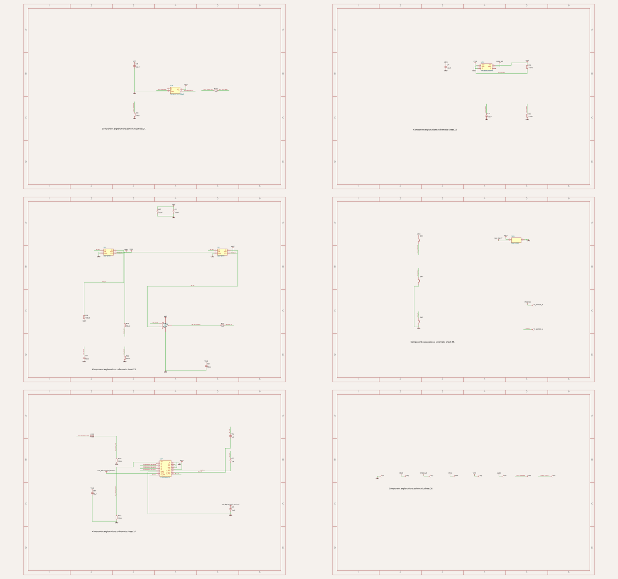
evidence/six-point-board-review-2026-10-06/final-schematics/circuits-8-13-contact.png
