AnasSarkiz/tscircuit-ai-agent-remote/evidence/top-control-mechanical-review-2026-10-03/top-control-study.png

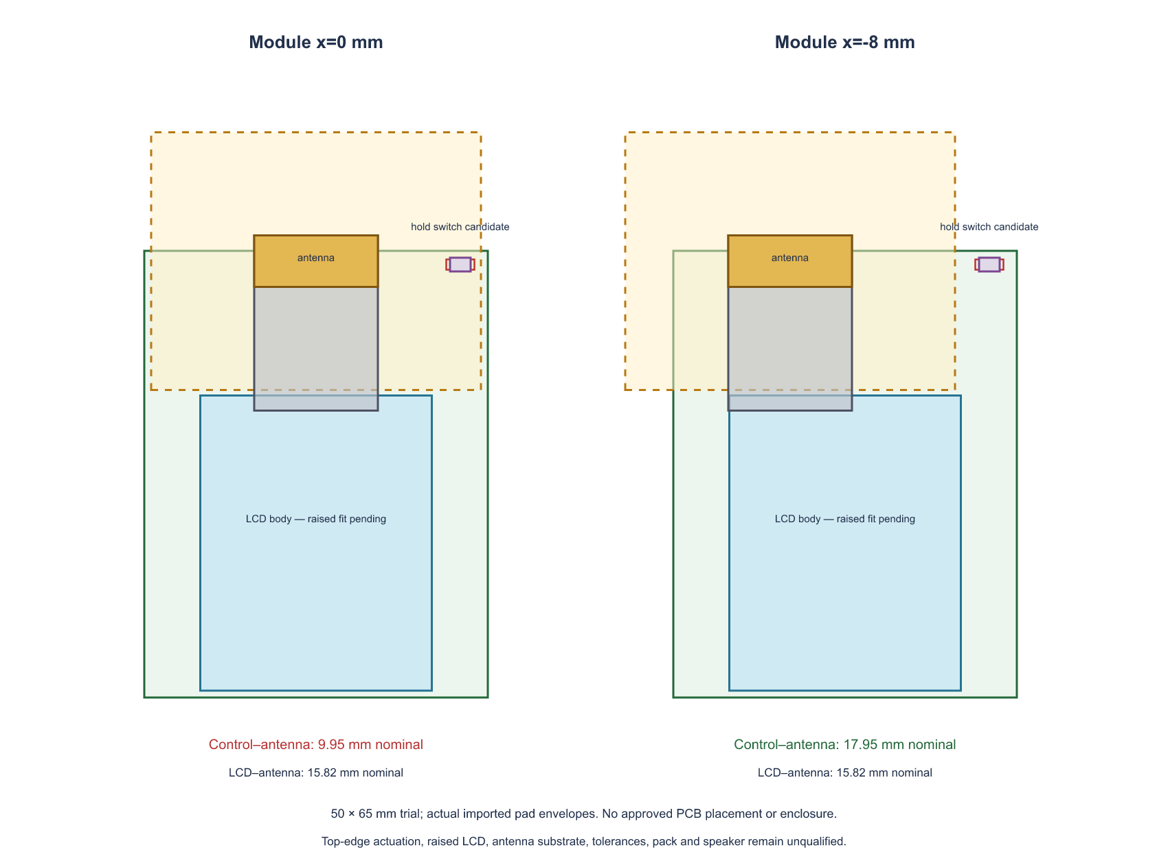
evidence/top-control-mechanical-review-2026-10-03/top-control-study.png
