AnasSarkiz/tscircuit-ai-agent-remote/evidence/type-c-current-review-2026-10-03/hold-candidate-pcb.png

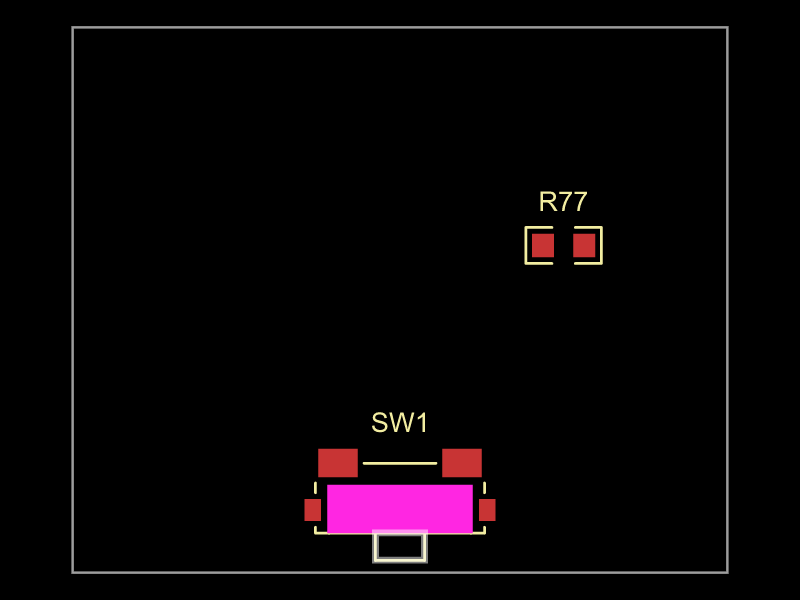
evidence/type-c-current-review-2026-10-03/hold-candidate-pcb.png
