AnasSarkiz/tscircuit-ai-agent-remote/evidence/type-c-current-review-2026-10-03/pcb.png

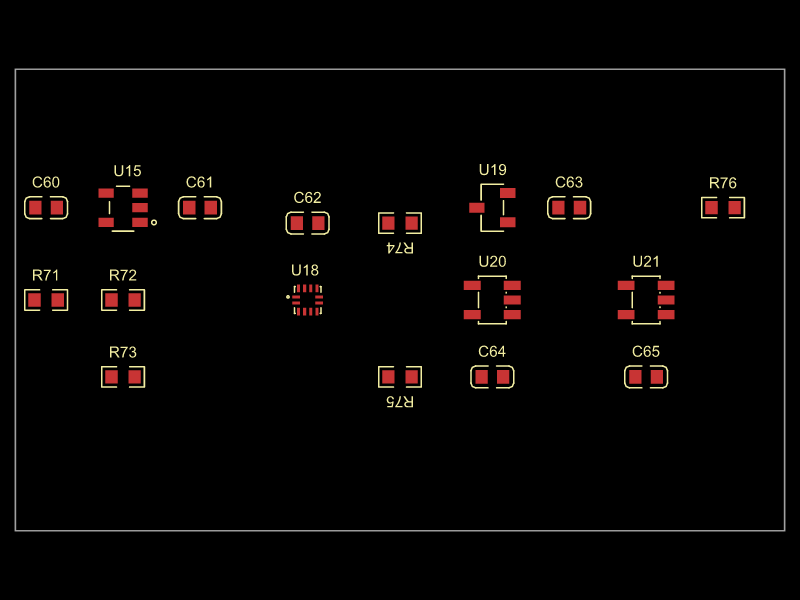
evidence/type-c-current-review-2026-10-03/pcb.png
