AnasSarkiz/tscircuit-ai-agent-remote/evidence/type-c-current-review-2026-10-03/schematic.png

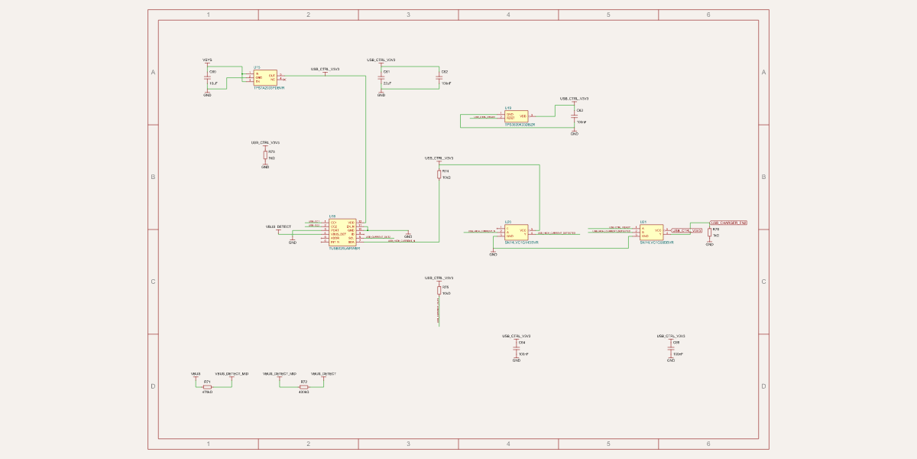
evidence/type-c-current-review-2026-10-03/schematic.png
