AnasSarkiz/tscircuit-ai-agent-remote/references/alps-skrtlae010-circuit.gif

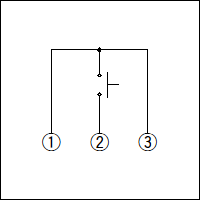
references/alps-skrtlae010-circuit.gif
