AnasSarkiz/tscircuit-ai-agent-remote/references/alps-skrtlae010-dimensions.gif

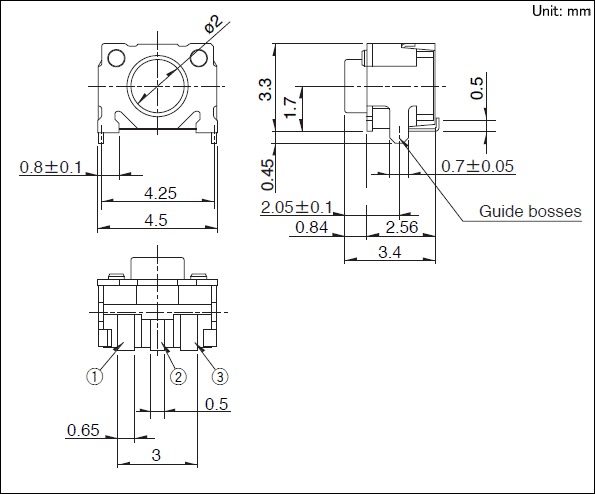
references/alps-skrtlae010-dimensions.gif
