AnasSarkiz/tscircuit-ai-agent-remote/evidence/a6-bom-routing-2026-10-04/review.md

# A6 — qualified resistor substitutions, polygon paste and partial copper

2026-10-04. Parent public GitHub revision faa491d22d1a55210833a8ea3086ae56dc450245. Intended public board-only package 0.0.2-wip-a6-bom-routing. Engineering prototype, NOT FABRICATION READY. Watcher stays paused; cross-chat messages stay disabled.

## Completed implementation

Seven C22548/RC0603FR-071KL references R38/R41/R62/R64/R82/R86/R27 now use genuine previously imported C21190/0603WAF1001T5E. Together with existing R100, total quantity is eight. Six C105588/RC0603FR-07100RL references R60/R63/R83/R88/R89/R103 now use genuinely imported C22775/0603WAF1000T5E. Supported exact search gives C21190 stock 8,013,731 and C22775 stock 7,325,193 on this date. Quantity, 0603 size, resistance, ±1%, 100 mW and ±100 ppm/°C ratings reviewed against the UNI-ROYAL family specification and native import; no imported definition edited. The source-level connection graph still has the same 123 connected groups. Supplier lands are preserved; full assembly qualification and final availability refresh remain required. Active inventory is 125 purchased parts / 43 identities plus 10 native pads.

Official core0.0.2083 includes PR4359 polygon paste. Aligned official peers: Circuit JSON0.0.515, props0.0.685, modelprinter0.0.6, capacity-autorouter0.0.958, checks0.0.237 and circuit-to-svg0.0.440. CLI remains0.1.2235 and tscircuit0.0.2742. Core-only upgrade first failed missing getNemaMotorReferencePoints; published peer alignment resolves that failure. Rendering initially failed with the previous renderer; matching official renderer resolves it. Failed attempts/logs remain saved.

Native SMT paste omissions fell from45 to32: the two microphones' eight polygon ground pads, four USB polygons and charger EP now have native paste. U16/C54313 and U27/C1848364 each still lack paste on16 pill pads. 487 SMT pads /469 paste shapes; shape count alone does not establish pad coverage. No hand-created paste or modified generated JSON.

Native routing adds two amplifier clock paths, two amplifier DIN paths and five backlight traces. C82/C83 rotate90° and move to (9.75,21)/(11.7,21) mm to avoid crossings. Backlight C1 phases use0.27 mm; C2 phases0.30 mm; current-setting0.20 mm. Ordinary minimum0.20 mm and clearance floors stay unchanged. Combined amplifier attempt had0.11487 mm trace clearance and was rejected. LRCLK attempts still exhaust the native solver, including with published router958; proposed R70 move was reverted. First backlight attempt created accidental contacts; second nominal0.30 C1 attempt measured0.199872 mm clearance and was rejected. Accepted native C1 routes give at least0.215126 mm trace clearance and no neck-down warnings. All raw start/end events, full JSON and per-phase native paths remain saved, including failed attempts.

Current canonical output has20 actual traces and2 vias. The original11 traces and2 via records are unchanged. Seven newly cached phase files replay with exact route geometry, layer/width and actual PCB-port association multisets. Generated trace IDs are excluded from comparison; native replay additionally inserts source_trace_id into connectsTo for four backlight traces, so full record byte identity is not claimed. Cache is genuine native output, not reconstructed from copper. All five prior missing backlight traces are resolved. Native unconnected-port errors fall413→402; routeRemaining staysfalse, J7 and J3 outer contacts remain deferred. This is independent partial routing, not complete board copper.

Actual audit of nine added traces: other-net pad clearance0.203668 mm; trace clearance0.215126 mm; drill clearance4.12470 mm; board edge6.02000 mm; keepout11.49933 mm. Via hole/outer0.30/0.70 mm, native plane antipad0.207303 mm. Conservative geometry auditors report no violations in their stated scope. Charging, power, clock AC/current/thermal qualification and final stackup remain open.

## Checks and visual review

Five required native source checks pass: netlist, pin_specification, source, schematic-placement and placement. Placement CAD build exits0 with zero traces/vias/pours and identical source components/ports/nets/traces and PCB components/pads/holes/keepouts/ports to the canonical design. Final routed build exits1 with402 retained pcb_port_not_connected_error records; no pcb_trace_missing_error, short, clearance or autorouting failures remain in that native output. It is not a successful fabrication build.

The required default `tsci check shorts dist/index/circuit.json` exits1: `Unsupported shape polygon`. Its Gerber/paste export cannot handle newly emitted polygon paste. Official CLI2237 source comparison only changes runframe/release metadata and does not resolve it; no unrelated CLI update or patch used. Diagnostic `--mode pcb` exits0, no shorts, but does not replace the required Gerber check. B-005 paste/export compatibility remains a fabrication blocker. New standalone renderer/check peers improve native rendering/checks but cannot change the CLI's bundled Gerber converter.

Format/types pass. Tests42pass/2retained failures,418assertions: strict native MCU fixture schema and whole-board zero-error fabrication gate. Full native JSON has169 strict failures:15 schematic groups,135 PCB components,15 PCB groups,2silkscreen texts,2holes. No schema relaxation or excluded failing test. Current generated four copper layers, top paste, amplifier/backlight/charger/USB details, thirteen A4 sheets and fresh placement 3D are inspected. Reference text on detailed PCB renders overlaps in crowded regions; final silkscreen/assembly readability review remains open. These are prototype renders, not physical tests or placement approval.

Snapshot changes are intended resistor/capacitor/paste/copper/prototype-note previews and are reviewed before updating; final snapshot result is recorded in check-results.json. Snapshot acceptance cannot clear the retained fabrication errors.

## Battery, display and mechanical findings

See mechanical-search.md with primary-source URLs and inspected drawings. AKY2945 drawing establishes red BAT+, yellow centre10kNTC, black BAT−, but no outer circuit numbers. J3.2=PACK_NTC; J3.1/3 remain unassigned and unrouted. Supplier page currently lists zero stock. No generic harness convention or another LP523450 pack was used as confirmation. No supplier message was sent. Written supplier numbering or a physical keyed-pack measurement is still needed.

Display has integrated ILI9341; it is the external bare BuyDisplay ER-TFT026-1 no-touch panel, not a JLC screen or8051 kit. Body overlap82.712% nominal/81.737% under the stated dimensional allocation meets the physical80% target. J7 top-contact50pin connector orientation, actual portrait FPC fold/contactface/pin1 and current bare-panel availability remain unqualified. Its current Rev3 text was obtained; current drawing retrieval fails/403, so historical Rev1 drawing is not used to approve physical mating. Logical pin-map tests alone do not establish flex mating. Dependent J7 routing remains deferred.

JST PH specifies0.8–1.6 mm board thickness. JLC nominal0.8±0.1 mm can produce0.7 mm, outside that range. Nominal1.0±10% meets JST but increases current conservative height sum14.87→15.07 mm, exceeding the15 mm limit by0.07 mm. This is a specific conflict under the current flat-cover assumptions; alternative case/pack geometry is not yet qualified. Exact AKY drawing supports upper10% thickness expansion:5.7→6.27 mm, but measured compressed dimension is not an installed-envelope guarantee. Alternative pack search found no qualified thinner matching protected/10kNTC/current/harness pack. PCB remains50×65 mm, case hardmax60×75×15 mm. No arbitrary clearance cuts, enlarged case or changed stackup.

Display/metal/pack/FPC RF exclusion, speaker/motor harness, screwheads, shell/actuator/strainrelief clearances and actual USB impedance/current/power/privacy/fault behavior remain open. Gerbers, drills, assembly BOM/CPL and physical prototype tests are not approved. Official native BOM previously had31 blank Comment fields and supplier-code footprint fallback; no manually repaired fabrication CSV is supplied.

## Evidence identity

Canonical fresh dist/index/circuit.json SHA256 70fe9a8e08b1eff92b99894708e5808158e680fa83a2967214aaaef588c05a45. Native-final copy, inventory, compact strict-schema results, source-equivalence/replay receipts, geometry auditors and command logs identify this source checkpoint. Runtime publication contains only transitive board sources/imports/models/routes/config/dependencies and this built JSON. Publication receipt is separately verified; a local commit or partial registry upload is not publication completion.
