AnasSarkiz/tscircuit-ai-agent-remote/evidence/a6-bom-routing-2026-10-04/publication/review.md

# A6 public publication outcome — verified 2026-10-04

Implementation commit a699a2d4337d5eafa26a777fee58c037de491f8f is on public AnasSarkiz/tscircuit-ai-agent-remote main; push exit0 and exact ls-remote agree. Anonymous repo/readback HTTP200, private=false. Committed dist/index/circuit.json is2,829,068bytes, SHA25670fe9a8e08b1eff92b99894708e5808158e680fa83a2967214aaaef588c05a45, byte-identical to validated local output.

Native official compressed public upload0.0.2-wip-a6-bom-routing exits1. Archive HTTP413; supported file-by-file fallback reports101uploaded/2failed: required imports/AFC07_S50ECA_00/AFC07_S50ECA_00.step and TYPE_C_31_M_12.step. Exact anonymous readback confirms the latter persisted with matching hash despite reported failure. A single initial transient network readback failure for TPS60230RGTR.obj was retried without re-upload and matches. Final receipt102/103matching, one404, zero mismatches/unverified files, noextra files; private=false/unlisted=false/ready_to_build=false. Current Circuit JSON and all saved route files match. Files stayed frozen during upload/readback.

Onlymissingfile is C262650 display-connector STEP,11,395,444bytes, localSHA256ddbd85a8e13ece9dbf820c09c5187c37d91c28286b1e6db82c32adef13dfb3e0. B-009 publication completion remains blocked. Neither model omission nor a custom upload, output patch or readiness override was used. Raw private publisher log remains/private/tmp/ai-remote-a6-publication.log; only its hash/size and safe diagnostic lines are preserved here. Request-body payload/credentials are excluded.

Additional read-only alternative searches for exact SM3B-PH-SM4-TB and SM2B-PH-SM4-TB surface-mount JST PH headers return empty native in-stock results. They do not establish assembly availability or a mechanical substitute; existing active connector definitions and PCB thickness remain unchanged. Current402 remaining-routing errors are indexed by component/net in remaining-routing.json, including145GND,24V3V3,19VSYS,15VLCD and14VMICerrors. They are port errors, not a count of required new traces.

This receipt-only checkpoint changes no board runtime inputs and does not initiate a redundant same-state publication. No fabrication-ready, hardware-tested or physical battery-pinout claim. Watcher paused; cross-chat messaging disabled.

Publicsource: https://github.com/AnasSarkiz/tscircuit-ai-agent-remote/commit/a699a2d4337d5eafa26a777fee58c037de491f8f
Publicpackage: https://tscircuit.com/AnasSarkiz/tscircuit-ai-agent-remote?version=0.0.2-wip-a6-bom-routing#files
