AnasSarkiz/tscircuit-ai-agent-remote/evidence/bom-export-review-2026-10-03/NOT-FOR-FABRICATION-bom-characterization.csv

Designator | Comment | Value | Footprint | JLCPCB Part #
SW4 |  | C255576 | C255576 | C255576
R98 | 100k | 100k | C14675 | C14675
