AnasSarkiz/tscircuit-ai-agent-remote/evidence/microphone-local-bypass-2026-10-08/pin-assignments.csv

reference | pin_number | source_port_name | port_hints | named_nets | pcb_port_id | physical_island_ids | net_has_missing_physical_connections | native_port_error
U1 | 1 | GND1 | GND1;pin1;1 | GND | pcb_port_0 | pcb_copper_pour_88 | True | False
U1 | 2 | 3V3 | 3V3;pin2;2 | V3V3 | pcb_port_1 | pcb_smtpad_480 | False | False
U1 | 3 | EN | EN;pin3;3 | MCU_EN | pcb_port_2 | pcb_smtpad_85 | False | False
U1 | 4 | IO4 | IO4;pin4;4 | MCU_AUDIO_ENABLE | pcb_port_3 | pcb_smtpad_284 | False | False
U1 | 5 | IO5 | IO5;pin5;5 | MCU_HAPTIC_ENABLE | pcb_port_4 | saved_phase_null_15_2:13 | False | False
U1 | 6 | IO6 | IO6;pin6;6 | LCD_ENABLE | pcb_port_5 | pcb_smtpad_233 | False | False
U1 | 7 | IO7 | IO7;pin7;7 | MCU_AUDIO_DIN | pcb_port_6 | pcb_smtpad_293 | False | False
U1 | 8 | IO15 | IO15;pin8;8 | MCU_MIC_BCLK | pcb_port_7 | pcb_smtpad_351 | False | False
U1 | 9 | IO16 | IO16;pin9;9 | MCU_MIC_WS | pcb_port_8 | pcb_smtpad_353 | False | False
U1 | 10 | IO17 | IO17;pin10;10 | MCU_MIC_SD | pcb_port_9 | pcb_smtpad_421 | False | False
U1 | 11 | IO18 | IO18;pin11;11 |  | pcb_port_10 | pcb_smtpad_10 | False | False
U1 | 12 | IO8 | IO8;pin12;12 | MCU_AUDIO_LRCLK | pcb_port_11 | pcb_smtpad_301 | False | False
U1 | 13 | IO19 | IO19;pin13;13 | MCU_USB_DN | pcb_port_12 | pcb_smtpad_75 | False | False
U1 | 14 | IO20 | IO20;pin14;14 | MCU_USB_DP | pcb_port_13 | pcb_smtpad_73 | False | False
U1 | 15 | IO3 | IO3;pin15;15 |  | pcb_port_14 | pcb_smtpad_14 | False | False
U1 | 16 | IO46 | IO46;pin16;16 |  | pcb_port_15 | pcb_smtpad_15 | False | False
U1 | 17 | IO9 | IO9;pin17;17 | MCU_AUDIO_BCLK | pcb_port_16 | pcb_smtpad_297 | False | False
U1 | 18 | IO10 | IO10;pin18;18 | MCU_LCD_CS_N | pcb_port_17 | pcb_smtpad_17 | False | False
U1 | 19 | IO11 | IO11;pin19;19 | MCU_LCD_SDA | pcb_port_18 | pcb_smtpad_253 | False | False
U1 | 20 | IO12 | IO12;pin20;20 | MCU_LCD_SCLK | pcb_port_19 | pcb_smtpad_249 | False | False
U1 | 21 | IO13 | IO13;pin21;21 | MCU_LCD_DC | pcb_port_20 | pcb_smtpad_245 | False | False
U1 | 22 | IO14 | IO14;pin22;22 | MCU_LCD_RESET_N | pcb_port_21 | pcb_smtpad_154 | False | False
U1 | 23 | IO21 | IO21;pin23;23 | MCU_HOLD_READ | pcb_port_22 | pcb_smtpad_22 | False | False
U1 | 24 | IO47 | IO47;pin24;24 | MCU_BACKLIGHT_PWM | pcb_port_23 | pcb_smtpad_465 | False | False
U1 | 25 | IO48 | IO48;pin25;25 |  | pcb_port_24 | pcb_smtpad_24 | False | False
U1 | 26 | IO45 | IO45;pin26;26 |  | pcb_port_25 | pcb_smtpad_25 | False | False
U1 | 27 | IO0 | IO0;pin27;27 | MCU_BOOT_N | pcb_port_26 | pcb_smtpad_433 | False | False
U1 | 28 | IO35 | IO35;pin28;28 |  | pcb_port_27 | pcb_smtpad_27 | False | False
U1 | 29 | IO36 | IO36;pin29;29 |  | pcb_port_28 | pcb_smtpad_28 | False | False
U1 | 30 | IO37 | IO37;pin30;30 |  | pcb_port_29 | pcb_smtpad_29 | False | False
U1 | 31 | IO38 | IO38;pin31;31 |  | pcb_port_30 | pcb_smtpad_30 | False | False
U1 | 32 | IO39 | IO39;pin32;32 |  | pcb_port_31 | pcb_smtpad_31 | False | False
U1 | 33 | IO40 | IO40;pin33;33 |  | pcb_port_32 | pcb_smtpad_32 | False | False
U1 | 34 | IO41 | IO41;pin34;34 |  | pcb_port_33 | pcb_smtpad_33 | False | False
U1 | 35 | IO42 | IO42;pin35;35 |  | pcb_port_34 | pcb_smtpad_34 | False | False
U1 | 36 | RXD0 | RXD0;pin36;36 | MCU_UART_RX | pcb_port_35 | pcb_smtpad_69 | False | False
U1 | 37 | TXD0 | TXD0;pin37;37 | MCU_UART_TX | pcb_port_36 | pcb_smtpad_36 | False | False
U1 | 38 | IO2 | IO2;pin38;38 |  | pcb_port_37 | pcb_smtpad_37 | False | False
U1 | 39 | IO1 | IO1;pin39;39 |  | pcb_port_38 | pcb_smtpad_38 | False | False
U1 | 40 | GND2 | GND2;pin40;40 | GND | pcb_port_39 | pcb_copper_pour_88 | True | False
U1 | 41 | GND3 | GND3;pin41;41 | GND | pcb_port_40 | pcb_copper_pour_88 | True | False
U1 |  | pin41_internal_1 | pin41_internal_1;pin41;41 | GND | pcb_port_41 | pcb_copper_pour_88 | True | False
U1 |  | pin41_internal_2 | pin41_internal_2;pin41;41 | GND | pcb_port_42 | pcb_copper_pour_88 | True | False
U1 |  | pin41_internal_3 | pin41_internal_3;pin41;41 | GND | pcb_port_43 | pcb_copper_pour_88 | True | False
U1 |  | pin41_internal_4 | pin41_internal_4;pin41;41 | GND | pcb_port_44 | pcb_copper_pour_88 | True | False
U1 |  | pin41_internal_5 | pin41_internal_5;pin41;41 | GND | pcb_port_45 | pcb_copper_pour_88 | True | False
U1 |  | pin41_internal_6 | pin41_internal_6;pin41;41 | GND | pcb_port_46 | pcb_copper_pour_88 | True | False
U1 |  | pin41_internal_7 | pin41_internal_7;pin41;41 | GND | pcb_port_47 | pcb_copper_pour_88 | True | False
U1 |  | pin41_internal_8 | pin41_internal_8;pin41;41 | GND | pcb_port_48 | pcb_copper_pour_88 | True | False
J1 | 1 | S2 | S2;EH2;SHELL2;pin1;1 | GND | pcb_port_49 | pcb_copper_pour_88 | True | False
J1 | 2 | S1 | S1;EH1;SHELL1;pin2;2 | GND | pcb_port_50 | pcb_copper_pour_88 | True | False
J1 | 3 | S4 | S4;EH4;SHELL4;pin3;3 | GND | pcb_port_51 | pcb_copper_pour_88 | True | False
J1 | 4 | S3 | S3;EH3;SHELL3;pin4;4 | GND | pcb_port_52 | pcb_copper_pour_88 | True | False
J1 | 5 | B8 | B8;SBU2;pin5;5 |  | pcb_port_53 | pcb_smtpad_49 | False | False
J1 | 6 | A5 | A5;CC1;pin6;6 | USB_CC1 | pcb_port_54 | pcb_smtpad_50 | False | False
J1 | 7 | B7 | B7;DN2;DM2;pin7;7 | USB_DN | pcb_port_55 | pcb_smtpad_74 | False | False
J1 | 8 | A6 | A6;DP1;pin8;8 | USB_DP | pcb_port_56 | pcb_smtpad_72 | False | False
J1 | 9 | A7 | A7;DN1;DM1;pin9;9 | USB_DN | pcb_port_57 | pcb_smtpad_74 | False | False
J1 | 10 | B6 | B6;DP2;pin10;10 | USB_DP | pcb_port_58 | pcb_smtpad_72 | False | False
J1 | 11 | A8 | A8;SBU1;pin11;11 |  | pcb_port_59 | pcb_smtpad_55 | False | False
J1 | 12 | B5 | B5;CC2;pin12;12 | USB_CC2 | pcb_port_60 | pcb_smtpad_56 | False | False
J1 | 13 | A1B12 | A1B12;GND1;pin13;13 | GND | pcb_port_61 | pcb_copper_pour_88 | True | False
J1 | 14 | B1A12 | B1A12;GND2;pin14;14 | GND | pcb_port_62 | pcb_copper_pour_88 | True | False
J1 | 15 | B4A9 | B4A9;VBUS1;pin15;15 | VBUS | pcb_port_63 | pcb_smtpad_112 | False | False
J1 | 16 | A4B9 | A4B9;VBUS2;pin16;16 | VBUS | pcb_port_64 | pcb_smtpad_112 | False | False
D2 | 3 | pin3 | pin3;GND;3 | GND | pcb_port_65 | pcb_copper_pour_88 | True | False
D2 | 1 | pin1 | pin1;D_POS;1 | USB_DP | pcb_port_66 | pcb_smtpad_72 | False | False
D2 | 2 | pin2 | pin2;D_NEG;2 | USB_DN | pcb_port_67 | pcb_smtpad_74 | False | False
U12 | 1 | GND | GND;pin1;1 | GND | pcb_port_68 | pcb_copper_pour_88 | True | False
U12 | 2 | N_RESET | N_RESET;pin2;2 | MCU_RESET_N | pcb_port_69 | pcb_smtpad_65 | False | False
U12 | 3 | VDD | VDD;pin3;3 | V3V3 | pcb_port_70 | pcb_smtpad_480 | False | False
J6 | 1 | pin1 | pin1;1 | MCU_UART_RX | pcb_port_71 | pcb_smtpad_69 | False | False
J6 | 2 | pin2 | pin2;2 | GND | pcb_port_72 | pcb_copper_pour_88 | True | False
J6 | 3 | pin3 | pin3;3 | SERVICE_UART_TX | pcb_port_73 | pcb_smtpad_71 | False | False
J6 | 4 | pin4 | pin4;4 | GND | pcb_port_74 | pcb_copper_pour_88 | True | False
J6 | 5 | pin5 | pin5;5 | GND | pcb_port_75 | pcb_copper_pour_88 | True | False
R31 | 1 | pin1 | pin1;anode;pos;left;1 | USB_DP | pcb_port_76 | pcb_smtpad_72 | False | False
R31 | 2 | pin2 | pin2;cathode;neg;right;2 | MCU_USB_DP | pcb_port_77 | pcb_smtpad_73 | False | False
R32 | 1 | pin1 | pin1;anode;pos;left;1 | USB_DN | pcb_port_78 | pcb_smtpad_74 | False | False
R32 | 2 | pin2 | pin2;cathode;neg;right;2 | MCU_USB_DN | pcb_port_79 | pcb_smtpad_75 | False | False
R33 | 1 | pin1 | pin1;anode;pos;left;1 | USB_CC1 | pcb_port_80 | pcb_smtpad_50 | False | False
R33 | 2 | pin2 | pin2;cathode;neg;right;2 | GND | pcb_port_81 | pcb_copper_pour_88 | True | False
R34 | 1 | pin1 | pin1;anode;pos;left;1 | USB_CC2 | pcb_port_82 | pcb_smtpad_56 | False | False
R34 | 2 | pin2 | pin2;cathode;neg;right;2 | GND | pcb_port_83 | pcb_copper_pour_88 | True | False
R35 | 1 | pin1 | pin1;anode;pos;left;1 | MCU_RESET_N | pcb_port_84 | pcb_smtpad_65 | False | False
R35 | 2 | pin2 | pin2;cathode;neg;right;2 | MCU_EN | pcb_port_85 | pcb_smtpad_85 | False | False
R36 | 1 | pin1 | pin1;anode;pos;left;1 | V3V3 | pcb_port_86 | pcb_smtpad_480 | False | False
R36 | 2 | pin2 | pin2;cathode;neg;right;2 | MCU_BOOT_N | pcb_port_87 | pcb_smtpad_433 | False | False
R37 | 1 | pin1 | pin1;anode;pos;left;1 | MCU_EN | pcb_port_88 | pcb_smtpad_85 | False | False
R37 | 2 | pin2 | pin2;cathode;neg;right;2 | GND | pcb_port_89 | pcb_copper_pour_88 | True | False
R38 | 1 | pin1 | pin1;anode;pos;left;1 | MCU_UART_TX | pcb_port_90 | pcb_smtpad_36 | False | False
R38 | 2 | pin2 | pin2;cathode;neg;right;2 | SERVICE_UART_TX | pcb_port_91 | pcb_smtpad_71 | False | False
C30 | 1 | pin1 | pin1;1 | V3V3 | pcb_port_92 | pcb_smtpad_480 | False | False
C30 | 2 | pin2 | pin2;2 | GND | pcb_port_93 | pcb_copper_pour_88 | True | False
C31 | 1 | pin1 | pin1;1 | V3V3 | pcb_port_94 | pcb_smtpad_480 | False | False
C31 | 2 | pin2 | pin2;2 | GND | pcb_port_95 | pcb_copper_pour_88 | True | False
C32 | 1 | pin1 | pin1;1 | V3V3 | pcb_port_96 | pcb_smtpad_480 | False | False
C32 | 2 | pin2 | pin2;2 | GND | pcb_port_97 | pcb_copper_pour_88 | True | False
U16 | 1 | TS | TS;pin1;1 | PACK_NTC | pcb_port_98 | pcb_smtpad_94 | False | False
U16 | 2 | BAT1 | BAT1;pin2;2 | PACK_BAT | pcb_port_99 | pcb_smtpad_478 | False | False
U16 | 3 | BAT2 | BAT2;pin3;3 | PACK_BAT | pcb_port_100 | pcb_smtpad_478 | False | False
U16 | 4 | N_CE | N_CE;pin4;4 | GND | pcb_port_101 | pcb_copper_pour_88 | True | False
U16 | 5 | EN2 | EN2;pin5;5 | GND | pcb_port_102 | pcb_copper_pour_88 | True | False
U16 | 6 | EN1 | EN1;pin6;6 | GND | pcb_port_103 | pcb_copper_pour_88 | True | False
U16 | 7 | N_PGOOD | N_PGOOD;pin7;7 | CHARGE_PGOOD_N | pcb_port_104 | pcb_smtpad_121 | False | False
U16 | 8 | VSS | VSS;pin8;8 | GND | pcb_port_105 | pcb_copper_pour_88 | True | False
U16 | 9 | N_CHG | N_CHG;pin9;9 | CHARGE_STATUS_N | pcb_port_106 | pcb_smtpad_483 | False | False
U16 | 10 | OUT1 | OUT1;pin10;10 | VSYS | pcb_port_107 | pcb_smtpad_287 | False | False
U16 | 11 | OUT2 | OUT2;pin11;11 | VSYS | pcb_port_108 | pcb_smtpad_287 | False | False
U16 | 12 | ILIM | ILIM;pin12;12 | CHARGER_ILIM | pcb_port_109 | pcb_smtpad_120 | False | False
U16 | 13 | IN | IN;pin13;13 | VBUS | pcb_port_110 | pcb_smtpad_112 | False | False
U16 | 14 | TMR | TMR;pin14;14 |  | pcb_port_111 | pcb_smtpad_107 | False | False
U16 | 15 | ITERM | ITERM;pin15;15 |  | pcb_port_112 | pcb_smtpad_108 | False | False
U16 | 16 | ISET | ISET;pin16;16 | CHARGER_ISET | pcb_port_113 | pcb_smtpad_118 | False | False
U16 | 17 | EP | EP;pin17;17 | GND | pcb_port_114 | pcb_copper_pour_88 | True | False
J3 | 1 | pin1 | pin1;1 |  | pcb_port_115 | pcb_plated_hole_6 | False | False
J3 | 2 | pin2 | pin2;2 | PACK_NTC | pcb_port_116 | pcb_smtpad_94 | False | False
J3 | 3 | pin3 | pin3;3 |  | pcb_port_117 | pcb_plated_hole_4 | False | False
C1 | 1 | pin1 | pin1;1 | VBUS | pcb_port_118 | pcb_smtpad_112 | False | False
C1 | 2 | pin2 | pin2;2 | GND | pcb_port_119 | pcb_copper_pour_88 | True | False
C2 | 1 | pin1 | pin1;1 | PACK_BAT | pcb_port_120 | pcb_smtpad_478 | False | False
C2 | 2 | pin2 | pin2;2 | GND | pcb_port_121 | pcb_copper_pour_88 | True | False
C3 | 1 | pin1 | pin1;1 | VSYS | pcb_port_122 | pcb_smtpad_287 | False | False
C3 | 2 | pin2 | pin2;2 | GND | pcb_port_123 | pcb_copper_pour_88 | True | False
R1 | 1 | pin1 | pin1;anode;pos;left;1 | CHARGER_ISET | pcb_port_124 | pcb_smtpad_118 | False | False
R1 | 2 | pin2 | pin2;cathode;neg;right;2 | GND | pcb_port_125 | pcb_copper_pour_88 | True | False
R2 | 1 | pin1 | pin1;anode;pos;left;1 | CHARGER_ILIM | pcb_port_126 | pcb_smtpad_120 | False | False
R2 | 2 | pin2 | pin2;cathode;neg;right;2 | GND | pcb_port_127 | pcb_copper_pour_88 | True | False
R3 | 1 | pin1 | pin1;anode;pos;left;1 | V3V3 | pcb_port_128 | pcb_smtpad_480 | False | False
R3 | 2 | pin2 | pin2;cathode;neg;right;2 | CHARGE_PGOOD_N | pcb_port_129 | pcb_smtpad_121 | False | False
R4 | 1 | pin1 | pin1;anode;pos;left;1 | V3V3 | pcb_port_130 | pcb_smtpad_480 | False | False
R4 | 2 | pin2 | pin2;cathode;neg;right;2 | CHARGE_STATUS_N | pcb_port_131 | pcb_smtpad_483 | False | False
U2 | 1 | EN | EN;pin1;1 | BUCK_ENABLE | pcb_port_132 | pcb_smtpad_386 | False | False
U2 | 2 | MODE | MODE;pin2;2 | GND | pcb_port_133 | pcb_copper_pour_88 | True | False
U2 | 3 | AGND | AGND;pin3;3 | GND | pcb_port_134 | pcb_copper_pour_88 | True | False
U2 | 4 | FB | FB;pin4;4 | REG_FB | pcb_port_135 | pcb_smtpad_143 | False | False
U2 | 5 | PG | PG;pin5;5 | REG_PG | pcb_port_136 | saved_phase_null_13_0:16 | False | False
U2 | 6 | VOUT | VOUT;pin6;6 | V3V3 | pcb_port_137 | pcb_smtpad_480 | False | False
U2 | 7 | L2 | L2;pin7;7 |  | pcb_port_138 | pcb_smtpad_128 | False | False
U2 | 8 | GND | GND;pin8;8 | GND | pcb_port_139 | pcb_copper_pour_88 | True | False
U2 | 9 | L1 | L1;pin9;9 |  | pcb_port_140 | pcb_smtpad_126 | False | False
U2 | 10 | VIN | VIN;pin10;10 | VSYS | pcb_port_141 | pcb_smtpad_287 | False | False
L1 | 1 | pin1 | pin1;anode;pos;left;1 |  | pcb_port_142 | pcb_smtpad_126 | False | False
L1 | 2 | pin2 | pin2;cathode;neg;right;2 |  | pcb_port_143 | pcb_smtpad_128 | False | False
C4 | 1 | pin1 | pin1;1 | VSYS | pcb_port_144 | pcb_smtpad_287 | False | False
C4 | 2 | pin2 | pin2;2 | GND | pcb_port_145 | pcb_copper_pour_88 | True | False
C5 | 1 | pin1 | pin1;1 | V3V3 | pcb_port_146 | pcb_smtpad_480 | False | False
C5 | 2 | pin2 | pin2;2 | GND | pcb_port_147 | pcb_copper_pour_88 | True | False
R5 | 1 | pin1 | pin1;anode;pos;left;1 | V3V3 | pcb_port_148 | pcb_smtpad_480 | False | False
R5 | 2 | pin2 | pin2;cathode;neg;right;2 | REG_FB | pcb_port_149 | pcb_smtpad_143 | False | False
R6 | 1 | pin1 | pin1;anode;pos;left;1 | REG_FB | pcb_port_150 | pcb_smtpad_143 | False | False
R6 | 2 | pin2 | pin2;cathode;neg;right;2 | GND | pcb_port_151 | pcb_copper_pour_88 | True | False
R7 | 1 | pin1 | pin1;anode;pos;left;1 | V3V3 | pcb_port_152 | pcb_smtpad_480 | False | False
R7 | 2 | pin2 | pin2;cathode;neg;right;2 | REG_PG | pcb_port_153 | saved_phase_null_13_0:16 | False | False
U13 | 1 | IN | IN;pin1;1 | V3V3 | pcb_port_154 | pcb_smtpad_480 | False | False
U13 | 2 | GND | GND;pin2;2 | GND | pcb_port_155 | pcb_copper_pour_88 | True | False
U13 | 3 | EN | EN;pin3;3 | LCD_ENABLE | pcb_port_156 | pcb_smtpad_233 | False | False
U13 | 4 | N | N;C;pin4;4 |  | pcb_port_157 | pcb_smtpad_150 | False | False
U13 | 5 | OUT | OUT;pin5;5 | VLCD | pcb_port_158 | pcb_smtpad_238 | True | False
U14 | 1 | DIR | DIR;pin1;1 | VLCD | pcb_port_159 | pcb_smtpad_238 | True | False
U14 | 2 | A1 | A1;pin2;2 | MCU_LCD_CS_N | pcb_port_160 | pcb_smtpad_17 | False | False
U14 | 3 | A2 | A2;pin3;3 | MCU_LCD_RESET_N | pcb_port_161 | pcb_smtpad_154 | False | False
U14 | 4 | A3 | A3;pin4;4 | MCU_LCD_DC | pcb_port_162 | pcb_smtpad_245 | False | False
U14 | 5 | A4 | A4;pin5;5 | MCU_LCD_SCLK | pcb_port_163 | pcb_smtpad_249 | False | False
U14 | 6 | A5 | A5;pin6;6 | MCU_LCD_SDA | pcb_port_164 | pcb_smtpad_253 | False | False
U14 | 7 | A6 | A6;pin7;7 | GND | pcb_port_165 | pcb_copper_pour_88 | True | False
U14 | 8 | A7 | A7;pin8;8 | GND | pcb_port_166 | pcb_copper_pour_88 | True | False
U14 | 9 | A8 | A8;pin9;9 | GND | pcb_port_167 | pcb_copper_pour_88 | True | False
U14 | 10 | GND | GND;pin10;10 | GND | pcb_port_168 | pcb_copper_pour_88 | True | False
U14 | 11 | B8 | B8;pin11;11 |  | pcb_port_169 | pcb_smtpad_162 | False | False
U14 | 12 | B7 | B7;pin12;12 |  | pcb_port_170 | pcb_smtpad_163 | False | False
U14 | 13 | B6 | B6;pin13;13 |  | pcb_port_171 | pcb_smtpad_164 | False | False
U14 | 14 | B5 | B5;pin14;14 | LCD_SDA | pcb_port_172 | pcb_smtpad_255 | True | False
U14 | 15 | B4 | B4;pin15;15 | LCD_SCLK | pcb_port_173 | pcb_smtpad_251 | True | False
U14 | 16 | B3 | B3;pin16;16 | LCD_DC | pcb_port_174 | pcb_smtpad_247 | True | False
U14 | 17 | B2 | B2;pin17;17 | LCD_RESET_N | pcb_port_175 | pcb_smtpad_243 | True | False
U14 | 18 | B1 | B1;pin18;18 | LCD_CS_N | pcb_port_176 | pcb_smtpad_239 | True | False
U14 | 19 | N_OE | N_OE;pin19;19 | GND | pcb_port_177 | pcb_copper_pour_88 | True | False
U14 | 20 | VCC | VCC;pin20;20 | VLCD | pcb_port_178 | pcb_smtpad_238 | True | False
J7 | 1 | pin1 | pin1;1 | GND | pcb_port_179 | pcb_smtpad_172 | True | True
J7 | 2 | pin2 | pin2;2 | GND | pcb_port_180 | pcb_smtpad_173 | True | True
J7 | 3 | pin3 | pin3;3 | GND | pcb_port_181 | pcb_smtpad_174 | True | True
J7 | 4 | pin4 | pin4;4 |  | pcb_port_182 | pcb_smtpad_175 | False | False
J7 | 5 | pin5 | pin5;5 |  | pcb_port_183 | pcb_smtpad_176 | False | False
J7 | 6 | pin6 | pin6;6 |  | pcb_port_184 | pcb_smtpad_177 | False | False
J7 | 7 | pin7 | pin7;7 |  | pcb_port_185 | pcb_smtpad_178 | False | False
J7 | 8 | pin8 | pin8;8 | GND | pcb_port_186 | pcb_smtpad_179 | True | True
J7 | 9 | pin9 | pin9;9 | VLCD | pcb_port_187 | pcb_smtpad_180 | True | True
J7 | 10 | pin10 | pin10;10 | VLCD | pcb_port_188 | pcb_smtpad_181 | True | True
J7 | 11 | pin11 | pin11;11 | VLCD | pcb_port_189 | pcb_smtpad_182 | True | True
J7 | 12 | pin12 | pin12;12 |  | pcb_port_190 | pcb_smtpad_183 | False | False
J7 | 13 | pin13 | pin13;13 | LCD_CS_N | pcb_port_191 | pcb_smtpad_184 | True | True
J7 | 14 | pin14 | pin14;14 | LCD_SCLK | pcb_port_192 | pcb_smtpad_185 | True | True
J7 | 15 | pin15 | pin15;15 | LCD_DC | pcb_port_193 | pcb_smtpad_186 | True | True
J7 | 16 | pin16 | pin16;16 | VLCD | pcb_port_194 | pcb_smtpad_187 | True | True
J7 | 17 | pin17 | pin17;17 | LCD_SDA | pcb_port_195 | pcb_smtpad_188 | True | True
J7 | 18 | pin18 | pin18;18 |  | pcb_port_196 | pcb_smtpad_189 | False | False
J7 | 19 | pin19 | pin19;19 | GND | pcb_port_197 | pcb_smtpad_190 | True | True
J7 | 20 | pin20 | pin20;20 | GND | pcb_port_198 | pcb_smtpad_191 | True | True
J7 | 21 | pin21 | pin21;21 | GND | pcb_port_199 | pcb_smtpad_192 | True | True
J7 | 22 | pin22 | pin22;22 | GND | pcb_port_200 | pcb_smtpad_193 | True | True
J7 | 23 | pin23 | pin23;23 | GND | pcb_port_201 | pcb_smtpad_194 | True | True
J7 | 24 | pin24 | pin24;24 | GND | pcb_port_202 | pcb_smtpad_195 | True | True
J7 | 25 | pin25 | pin25;25 | GND | pcb_port_203 | pcb_smtpad_196 | True | True
J7 | 26 | pin26 | pin26;26 | GND | pcb_port_204 | pcb_smtpad_197 | True | True
J7 | 27 | pin27 | pin27;27 | GND | pcb_port_205 | pcb_smtpad_198 | True | True
J7 | 28 | pin28 | pin28;28 | GND | pcb_port_206 | pcb_smtpad_199 | True | True
J7 | 29 | pin29 | pin29;29 | GND | pcb_port_207 | pcb_smtpad_200 | True | True
J7 | 30 | pin30 | pin30;30 | GND | pcb_port_208 | pcb_smtpad_201 | True | True
J7 | 31 | pin31 | pin31;31 | GND | pcb_port_209 | pcb_smtpad_202 | True | True
J7 | 32 | pin32 | pin32;32 | GND | pcb_port_210 | pcb_smtpad_203 | True | True
J7 | 33 | pin33 | pin33;33 | GND | pcb_port_211 | pcb_smtpad_204 | True | True
J7 | 34 | pin34 | pin34;34 | GND | pcb_port_212 | pcb_smtpad_205 | True | True
J7 | 35 | pin35 | pin35;35 | GND | pcb_port_213 | pcb_smtpad_206 | True | True
J7 | 36 | pin36 | pin36;36 | GND | pcb_port_214 | pcb_smtpad_207 | True | True
J7 | 37 | pin37 | pin37;37 | GND | pcb_port_215 | pcb_smtpad_208 | True | True
J7 | 38 | pin38 | pin38;38 | GND | pcb_port_216 | pcb_smtpad_209 | True | True
J7 | 39 | pin39 | pin39;39 | GND | pcb_port_217 | pcb_smtpad_210 | True | True
J7 | 40 | pin40 | pin40;40 | GND | pcb_port_218 | pcb_smtpad_211 | True | True
J7 | 41 | pin41 | pin41;41 | LCD_RESET_N | pcb_port_219 | pcb_smtpad_214 | True | True
J7 | 42 | pin42 | pin42;42 | VLCD | pcb_port_220 | pcb_smtpad_215 | True | True
J7 | 43 | pin43 | pin43;43 | VLCD | pcb_port_221 | pcb_smtpad_216 | True | True
J7 | 44 | pin44 | pin44;44 | VLCD | pcb_port_222 | pcb_smtpad_217 | True | True
J7 | 45 | pin45 | pin45;45 | GND | pcb_port_223 | pcb_smtpad_218 | True | True
J7 | 46 | pin46 | pin46;46 | LCD_BACKLIGHT_RETURN_4 | pcb_port_224 | pcb_smtpad_219 | True | True
J7 | 47 | pin47 | pin47;47 | LCD_BACKLIGHT_RETURN_3 | pcb_port_225 | pcb_smtpad_220 | True | True
J7 | 48 | pin48 | pin48;48 | LCD_BACKLIGHT_RETURN_2 | pcb_port_226 | pcb_smtpad_221 | True | True
J7 | 49 | pin49 | pin49;49 | LCD_BACKLIGHT_RETURN_1 | pcb_port_227 | pcb_smtpad_222 | True | True
J7 | 50 | pin50 | pin50;50 | LCD_BACKLIGHT_OUTPUT | pcb_port_228 | pcb_smtpad_223 | True | True
J7 | 51 | pin51 | pin51;51 | GND | pcb_port_229 | pcb_copper_pour_88 | True | True
J7 | 52 | pin52 | pin52;52 | GND | pcb_port_230 | pcb_copper_pour_88 | True | True
C40 | 1 | pin1 | pin1;1 | V3V3 | pcb_port_231 | pcb_smtpad_480 | False | False
C40 | 2 | pin2 | pin2;2 | GND | pcb_port_232 | pcb_copper_pour_88 | True | False
C41 | 1 | pin1 | pin1;1 | VLCD | pcb_port_233 | pcb_smtpad_238 | True | False
C41 | 2 | pin2 | pin2;2 | GND | pcb_port_234 | pcb_copper_pour_88 | True | False
C42 | 1 | pin1 | pin1;1 | VLCD | pcb_port_235 | pcb_smtpad_238 | True | False
C42 | 2 | pin2 | pin2;2 | GND | pcb_port_236 | pcb_copper_pour_88 | True | False
C43 | 1 | pin1 | pin1;1 | VLCD | pcb_port_237 | pcb_smtpad_238 | True | False
C43 | 2 | pin2 | pin2;2 | GND | pcb_port_238 | pcb_copper_pour_88 | True | False
R40 | 1 | pin1 | pin1;anode;pos;left;1 | LCD_ENABLE | pcb_port_239 | pcb_smtpad_233 | False | False
R40 | 2 | pin2 | pin2;cathode;neg;right;2 | GND | pcb_port_240 | pcb_copper_pour_88 | True | False
R41 | 1 | pin1 | pin1;anode;pos;left;1 | VLCD | pcb_port_241 | pcb_smtpad_238 | True | False
R41 | 2 | pin2 | pin2;cathode;neg;right;2 | GND | pcb_port_242 | pcb_copper_pour_88 | True | False
R47 | 1 | pin1 | pin1;anode;pos;left;1 | MCU_LCD_CS_N | pcb_port_243 | pcb_smtpad_17 | False | False
R47 | 2 | pin2 | pin2;cathode;neg;right;2 | GND | pcb_port_244 | pcb_copper_pour_88 | True | False
R42 | 1 | pin1 | pin1;anode;pos;left;1 | LCD_CS_N | pcb_port_245 | pcb_smtpad_239 | True | False
R42 | 2 | pin2 | pin2;cathode;neg;right;2 | VLCD | pcb_port_246 | pcb_smtpad_238 | True | False
R48 | 1 | pin1 | pin1;anode;pos;left;1 | MCU_LCD_RESET_N | pcb_port_247 | pcb_smtpad_154 | False | False
R48 | 2 | pin2 | pin2;cathode;neg;right;2 | GND | pcb_port_248 | pcb_copper_pour_88 | True | False
R43 | 1 | pin1 | pin1;anode;pos;left;1 | LCD_RESET_N | pcb_port_249 | pcb_smtpad_243 | True | False
R43 | 2 | pin2 | pin2;cathode;neg;right;2 | GND | pcb_port_250 | pcb_copper_pour_88 | True | False
R49 | 1 | pin1 | pin1;anode;pos;left;1 | MCU_LCD_DC | pcb_port_251 | pcb_smtpad_245 | False | False
R49 | 2 | pin2 | pin2;cathode;neg;right;2 | GND | pcb_port_252 | pcb_copper_pour_88 | True | False
R44 | 1 | pin1 | pin1;anode;pos;left;1 | LCD_DC | pcb_port_253 | pcb_smtpad_247 | True | False
R44 | 2 | pin2 | pin2;cathode;neg;right;2 | GND | pcb_port_254 | pcb_copper_pour_88 | True | False
R50 | 1 | pin1 | pin1;anode;pos;left;1 | MCU_LCD_SCLK | pcb_port_255 | pcb_smtpad_249 | False | False
R50 | 2 | pin2 | pin2;cathode;neg;right;2 | GND | pcb_port_256 | pcb_copper_pour_88 | True | False
R45 | 1 | pin1 | pin1;anode;pos;left;1 | LCD_SCLK | pcb_port_257 | pcb_smtpad_251 | True | False
R45 | 2 | pin2 | pin2;cathode;neg;right;2 | GND | pcb_port_258 | pcb_copper_pour_88 | True | False
R51 | 1 | pin1 | pin1;anode;pos;left;1 | MCU_LCD_SDA | pcb_port_259 | pcb_smtpad_253 | False | False
R51 | 2 | pin2 | pin2;cathode;neg;right;2 | GND | pcb_port_260 | pcb_copper_pour_88 | True | False
R46 | 1 | pin1 | pin1;anode;pos;left;1 | LCD_SDA | pcb_port_261 | pcb_smtpad_255 | True | False
R46 | 2 | pin2 | pin2;cathode;neg;right;2 | GND | pcb_port_262 | pcb_copper_pour_88 | True | False
U3 | 1 | DIN | DIN;pin1;1 | AMP_DIN | pcb_port_263 | pcb_smtpad_294 | False | False
U3 | 2 | GAIN_SLOT | GAIN_SLOT;pin2;2 | VSYS | pcb_port_264 | pcb_smtpad_287 | False | False
U3 | 3 | GND1 | GND1;pin3;3 | GND | pcb_port_265 | pcb_copper_pour_88 | True | False
U3 | 4 | N_SD_MODE | N_SD_MODE;pin4;4 | AMP_SD_MODE | pcb_port_266 | pcb_smtpad_259 | False | False
U3 | 5 | pin5 | pin5;5 |  | pcb_port_267 | pcb_smtpad_260 | False | False
U3 | 6 | pin6 | pin6;6 |  | pcb_port_268 | pcb_smtpad_261 | False | False
U3 | 7 | VDD1 | VDD1;pin7;7 | VSYS | pcb_port_269 | pcb_smtpad_287 | False | False
U3 | 8 | VDD2 | VDD2;pin8;8 | VSYS | pcb_port_270 | pcb_smtpad_287 | False | False
U3 | 9 | OUTP | OUTP;pin9;9 | SPEAKER_P | pcb_port_271 | pcb_smtpad_264 | False | False
U3 | 10 | OUTN | OUTN;pin10;10 | SPEAKER_N | pcb_port_272 | pcb_smtpad_265 | False | False
U3 | 11 | GND2 | GND2;pin11;11 | GND | pcb_port_273 | pcb_copper_pour_88 | True | False
U3 | 12 | pin12 | pin12;12 |  | pcb_port_274 | pcb_smtpad_267 | False | False
U3 | 13 | pin13 | pin13;13 |  | pcb_port_275 | pcb_smtpad_268 | False | False
U3 | 14 | LRCLK | LRCLK;pin14;14 | AMP_LRCLK | pcb_port_276 | pcb_smtpad_269 | False | False
U3 | 15 | GND3 | GND3;pin15;15 | GND | pcb_port_277 | pcb_copper_pour_88 | True | False
U3 | 16 | BCLK | BCLK;pin16;16 | AMP_BCLK | pcb_port_278 | pcb_smtpad_271 | False | False
U3 | 17 | EP | EP;pin17;17 | GND | pcb_port_279 | pcb_copper_pour_88 | True | False
Q1 | 3 | pin3 | pin3;D;3 | AUDIO_PMOS_GATE | pcb_port_280 | pcb_smtpad_288 | False | False
Q1 | 1 | pin1 | pin1;G;1 | AUDIO_NMOS_GATE | pcb_port_281 | pcb_smtpad_273 | False | False
Q1 | 2 | pin2 | pin2;S;2 | GND | pcb_port_282 | pcb_copper_pour_88 | True | False
Q2 | 3 | pin3 | pin3;D;3 | AUDIO_ENABLE_SUPPLY | pcb_port_283 | pcb_smtpad_290 | False | False
Q2 | 1 | pin1 | pin1;G;1 | AUDIO_PMOS_GATE | pcb_port_284 | pcb_smtpad_288 | False | False
Q2 | 2 | pin2 | pin2;S;2 | VSYS | pcb_port_285 | pcb_smtpad_287 | False | False
J4 | 1 | pin1 | pin1;1 | SPEAKER_P | pcb_port_286 | pcb_smtpad_264 | False | False
J4 | 2 | pin2 | pin2;2 | SPEAKER_N | pcb_port_287 | pcb_smtpad_265 | False | False
C50 | 1 | pin1 | pin1;1 | VSYS | pcb_port_288 | pcb_smtpad_287 | False | False
C50 | 2 | pin2 | pin2;2 | GND | pcb_port_289 | pcb_copper_pour_88 | True | False
C51 | 1 | pin1 | pin1;1 | VSYS | pcb_port_290 | pcb_smtpad_287 | False | False
C51 | 2 | pin2 | pin2;2 | GND | pcb_port_291 | pcb_copper_pour_88 | True | False
R60 | 1 | pin1 | pin1;anode;pos;left;1 | MCU_AUDIO_ENABLE | pcb_port_292 | pcb_smtpad_284 | False | False
R60 | 2 | pin2 | pin2;cathode;neg;right;2 | AUDIO_NMOS_GATE | pcb_port_293 | pcb_smtpad_273 | False | False
R61 | 1 | pin1 | pin1;anode;pos;left;1 | AUDIO_NMOS_GATE | pcb_port_294 | pcb_smtpad_273 | False | False
R61 | 2 | pin2 | pin2;cathode;neg;right;2 | GND | pcb_port_295 | pcb_copper_pour_88 | True | False
R62 | 1 | pin1 | pin1;anode;pos;left;1 | VSYS | pcb_port_296 | pcb_smtpad_287 | False | False
R62 | 2 | pin2 | pin2;cathode;neg;right;2 | AUDIO_PMOS_GATE | pcb_port_297 | pcb_smtpad_288 | False | False
R63 | 1 | pin1 | pin1;anode;pos;left;1 | AUDIO_ENABLE_SUPPLY | pcb_port_298 | pcb_smtpad_290 | False | False
R63 | 2 | pin2 | pin2;cathode;neg;right;2 | AMP_SD_MODE | pcb_port_299 | pcb_smtpad_259 | False | False
R64 | 1 | pin1 | pin1;anode;pos;left;1 | AMP_SD_MODE | pcb_port_300 | pcb_smtpad_259 | False | False
R64 | 2 | pin2 | pin2;cathode;neg;right;2 | GND | pcb_port_301 | pcb_copper_pour_88 | True | False
R65 | 1 | pin1 | pin1;anode;pos;left;1 | MCU_AUDIO_DIN | pcb_port_302 | pcb_smtpad_293 | False | False
R65 | 2 | pin2 | pin2;cathode;neg;right;2 | AMP_DIN | pcb_port_303 | pcb_smtpad_294 | False | False
R68 | 1 | pin1 | pin1;anode;pos;left;1 | AMP_DIN | pcb_port_304 | pcb_smtpad_294 | False | False
R68 | 2 | pin2 | pin2;cathode;neg;right;2 | GND | pcb_port_305 | pcb_copper_pour_88 | True | False
R66 | 1 | pin1 | pin1;anode;pos;left;1 | MCU_AUDIO_BCLK | pcb_port_306 | pcb_smtpad_297 | False | False
R66 | 2 | pin2 | pin2;cathode;neg;right;2 | AMP_BCLK | pcb_port_307 | pcb_smtpad_271 | False | False
R69 | 1 | pin1 | pin1;anode;pos;left;1 | AMP_BCLK | pcb_port_308 | pcb_smtpad_271 | False | False
R69 | 2 | pin2 | pin2;cathode;neg;right;2 | GND | pcb_port_309 | pcb_copper_pour_88 | True | False
R67 | 1 | pin1 | pin1;anode;pos;left;1 | MCU_AUDIO_LRCLK | pcb_port_310 | pcb_smtpad_301 | False | False
R67 | 2 | pin2 | pin2;cathode;neg;right;2 | AMP_LRCLK | pcb_port_311 | pcb_smtpad_269 | False | False
R70 | 1 | pin1 | pin1;anode;pos;left;1 | AMP_LRCLK | pcb_port_312 | pcb_smtpad_269 | False | False
R70 | 2 | pin2 | pin2;cathode;neg;right;2 | GND | pcb_port_313 | pcb_copper_pour_88 | True | False
U22 | 1 | IN | IN;pin1;1 | VSYS | pcb_port_314 | pcb_smtpad_287 | False | False
U22 | 2 | GND | GND;pin2;2 | GND | pcb_port_315 | pcb_copper_pour_88 | True | False
U22 | 3 | EN | EN;pin3;3 | MCU_HAPTIC_ENABLE | pcb_port_316 | saved_phase_null_15_2:13 | False | False
U22 | 4 | N | N;C;pin4;4 |  | pcb_port_317 | pcb_smtpad_308 | False | False
U22 | 5 | OUT | OUT;pin5;5 | VMOTOR | pcb_port_318 | pcb_smtpad_321 | False | False
Q9 | 3 | pin3 | pin3;D;3 | HAPTIC_N | pcb_port_319 | pcb_smtpad_444 | False | False
Q9 | 1 | pin1 | pin1;G;1 | HAPTIC_NMOS_GATE | pcb_port_320 | pcb_smtpad_326 | False | False
Q9 | 2 | pin2 | pin2;S;2 | GND | pcb_port_321 | pcb_copper_pour_88 | True | False
D3 | 1 | cathode | cathode;neg;pin1;1 | VMOTOR | pcb_port_322 | pcb_smtpad_321 | False | False
D3 | 2 | anode | anode;pos;pin2;2 | HAPTIC_N | pcb_port_323 | pcb_smtpad_444 | False | False
C70 | 1 | pin1 | pin1;1 | VSYS | pcb_port_324 | pcb_smtpad_287 | False | False
C70 | 2 | pin2 | pin2;2 | GND | pcb_port_325 | pcb_copper_pour_88 | True | False
C71 | 1 | pin1 | pin1;1 | VMOTOR | pcb_port_326 | pcb_smtpad_321 | False | False
C71 | 2 | pin2 | pin2;2 | GND | pcb_port_327 | pcb_copper_pour_88 | True | False
C72 | 1 | pin1 | pin1;1 | VMOTOR | pcb_port_328 | pcb_smtpad_321 | False | False
C72 | 2 | pin2 | pin2;2 | HAPTIC_N | pcb_port_329 | pcb_smtpad_444 | False | False
R82 | 1 | pin1 | pin1;anode;pos;left;1 | VMOTOR | pcb_port_330 | pcb_smtpad_321 | False | False
R82 | 2 | pin2 | pin2;cathode;neg;right;2 | GND | pcb_port_331 | pcb_copper_pour_88 | True | False
R83 | 1 | pin1 | pin1;anode;pos;left;1 | MCU_HAPTIC_ENABLE | pcb_port_332 | saved_phase_null_15_2:13 | False | False
R83 | 2 | pin2 | pin2;cathode;neg;right;2 | HAPTIC_NMOS_GATE | pcb_port_333 | pcb_smtpad_326 | False | False
R84 | 1 | pin1 | pin1;anode;pos;left;1 | HAPTIC_NMOS_GATE | pcb_port_334 | pcb_smtpad_326 | False | False
R84 | 2 | pin2 | pin2;cathode;neg;right;2 | GND | pcb_port_335 | pcb_copper_pour_88 | True | False
R85 | 1 | pin1 | pin1;anode;pos;left;1 | MCU_HAPTIC_ENABLE | pcb_port_336 | saved_phase_null_15_2:13 | False | False
R85 | 2 | pin2 | pin2;cathode;neg;right;2 | GND | pcb_port_337 | pcb_copper_pour_88 | True | False
U23 | 1 | IN | IN;pin1;1 | MIC_INPUT | pcb_port_338 | pcb_smtpad_441 | False | False
U23 | 2 | GND | GND;pin2;2 | GND | pcb_port_339 | pcb_copper_pour_88 | True | False
U23 | 3 | EN | EN;pin3;3 | HOLD_HARDWARE | pcb_port_340 | pcb_smtpad_372 | False | False
U23 | 4 | N | N;C;pin4;4 |  | pcb_port_341 | pcb_smtpad_332 | False | False
U23 | 5 | OUT | OUT;pin5;5 | VMIC | pcb_port_342 | pcb_smtpad_401 | False | False
U24 | 1 | 1A | 1A;pin1;1 | MIC_BCLK_INPUT | pcb_port_343 | pcb_smtpad_355 | False | False
U24 | 2 | GND | GND;pin2;2 | GND | pcb_port_344 | pcb_copper_pour_88 | True | False
U24 | 3 | 2A | 2A;pin3;3 | MIC_WS_INPUT | pcb_port_345 | pcb_smtpad_352 | False | False
U24 | 4 | 2Y | 2Y;pin4;4 | MIC_WS | pcb_port_346 | pcb_smtpad_391 | False | False
U24 | 5 | VCC | VCC;pin5;5 | VMIC | pcb_port_347 | pcb_smtpad_401 | False | False
U24 | 6 | 1Y | 1Y;pin6;6 | MIC_BCLK | pcb_port_348 | pcb_smtpad_393 | False | False
C73 | 1 | pin1 | pin1;1 | MIC_INPUT | pcb_port_349 | pcb_smtpad_441 | False | False
C73 | 2 | pin2 | pin2;2 | GND | pcb_port_350 | pcb_copper_pour_88 | True | False
C74 | 1 | pin1 | pin1;1 | VMIC | pcb_port_351 | pcb_smtpad_401 | False | False
C74 | 2 | pin2 | pin2;2 | GND | pcb_port_352 | pcb_copper_pour_88 | True | False
C75 | 1 | pin1 | pin1;1 | VMIC | pcb_port_353 | pcb_smtpad_401 | False | False
C75 | 2 | pin2 | pin2;2 | GND | pcb_port_354 | pcb_copper_pour_88 | True | False
R86 | 1 | pin1 | pin1;anode;pos;left;1 | VMIC | pcb_port_355 | pcb_smtpad_401 | False | False
R86 | 2 | pin2 | pin2;cathode;neg;right;2 | GND | pcb_port_356 | pcb_copper_pour_88 | True | False
R87 | 1 | pin1 | pin1;anode;pos;left;1 | HOLD_HARDWARE | pcb_port_357 | pcb_smtpad_372 | False | False
R87 | 2 | pin2 | pin2;cathode;neg;right;2 | GND | pcb_port_358 | pcb_copper_pour_88 | True | False
R88 | 1 | pin1 | pin1;anode;pos;left;1 | MCU_MIC_BCLK | pcb_port_359 | pcb_smtpad_351 | False | False
R88 | 2 | pin2 | pin2;cathode;neg;right;2 | MIC_BCLK_INPUT | pcb_port_360 | pcb_smtpad_355 | False | False
R89 | 1 | pin1 | pin1;anode;pos;left;1 | MCU_MIC_WS | pcb_port_361 | pcb_smtpad_353 | False | False
R89 | 2 | pin2 | pin2;cathode;neg;right;2 | MIC_WS_INPUT | pcb_port_362 | pcb_smtpad_352 | False | False
R90 | 1 | pin1 | pin1;anode;pos;left;1 | MIC_BCLK_INPUT | pcb_port_363 | pcb_smtpad_355 | False | False
R90 | 2 | pin2 | pin2;cathode;neg;right;2 | GND | pcb_port_364 | pcb_copper_pour_88 | True | False
R91 | 1 | pin1 | pin1;anode;pos;left;1 | MIC_WS_INPUT | pcb_port_365 | pcb_smtpad_352 | False | False
R91 | 2 | pin2 | pin2;cathode;neg;right;2 | GND | pcb_port_366 | pcb_copper_pour_88 | True | False
R92 | 1 | pin1 | pin1;anode;pos;left;1 | VMIC | pcb_port_367 | pcb_smtpad_401 | False | False
R92 | 2 | pin2 | pin2;cathode;neg;right;2 | MIC_BCLK | pcb_port_368 | pcb_smtpad_393 | False | False
R93 | 1 | pin1 | pin1;anode;pos;left;1 | VMIC | pcb_port_369 | pcb_smtpad_401 | False | False
R93 | 2 | pin2 | pin2;cathode;neg;right;2 | MIC_WS | pcb_port_370 | pcb_smtpad_391 | False | False
R94 | 1 | pin1 | pin1;anode;pos;left;1 | MIC_BCLK | pcb_port_371 | pcb_smtpad_393 | False | False
R94 | 2 | pin2 | pin2;cathode;neg;right;2 | GND | pcb_port_372 | pcb_copper_pour_88 | True | False
R95 | 1 | pin1 | pin1;anode;pos;left;1 | MIC_WS | pcb_port_373 | pcb_smtpad_391 | False | False
R95 | 2 | pin2 | pin2;cathode;neg;right;2 | GND | pcb_port_374 | pcb_copper_pour_88 | True | False
U26 | 1 | N_C | N_C;pin1;1 |  | pcb_port_375 | pcb_smtpad_370 | False | False
U26 | 2 | A | A;pin2;2 | HOLD_HARDWARE | pcb_port_376 | pcb_smtpad_372 | False | False
U26 | 3 | GND | GND;pin3;3 | GND | pcb_port_377 | pcb_copper_pour_88 | True | False
U26 | 4 | Y | Y;pin4;4 | HOLD_BUFFER_OUT | pcb_port_378 | pcb_smtpad_373 | False | False
U26 | 5 | VCC | VCC;pin5;5 | V3V3 | pcb_port_379 | pcb_smtpad_480 | False | False
R99 | 1 | pin1 | pin1;anode;pos;left;1 | HOLD_HARDWARE | pcb_port_380 | pcb_smtpad_372 | False | False
R99 | 2 | pin2 | pin2;cathode;neg;right;2 | GND | pcb_port_381 | pcb_copper_pour_88 | True | False
R100 | 1 | pin1 | pin1;anode;pos;left;1 | HOLD_BUFFER_OUT | pcb_port_382 | pcb_smtpad_373 | False | False
R100 | 2 | pin2 | pin2;cathode;neg;right;2 | MCU_HOLD_READ | pcb_port_383 | pcb_smtpad_22 | False | False
C78 | 1 | pin1 | pin1;1 | V3V3 | pcb_port_384 | pcb_smtpad_480 | False | False
C78 | 2 | pin2 | pin2;2 | GND | pcb_port_385 | pcb_copper_pour_88 | True | False
U25 | 1 | N_RESET | N_RESET;pin1;1 | BUCK_ENABLE | pcb_port_386 | pcb_smtpad_386 | False | False
U25 | 2 | GND | GND;pin2;2 | GND | pcb_port_387 | pcb_copper_pour_88 | True | False
U25 | 3 | N_MR | N_MR;pin3;3 | VSYS | pcb_port_388 | pcb_smtpad_287 | False | False
U25 | 4 | CT | CT;pin4;4 |  | pcb_port_389 | pcb_smtpad_382 | False | False
U25 | 5 | SENSE | SENSE;pin5;5 | PACK_BAT | pcb_port_390 | pcb_smtpad_478 | False | False
U25 | 6 | VDD | VDD;pin6;6 | VSYS | pcb_port_391 | pcb_smtpad_287 | False | False
R96 | 1 | pin1 | pin1;anode;pos;left;1 | VSYS | pcb_port_392 | pcb_smtpad_287 | False | False
R96 | 2 | pin2 | pin2;cathode;neg;right;2 | BUCK_ENABLE | pcb_port_393 | pcb_smtpad_386 | False | False
R97 | 1 | pin1 | pin1;anode;pos;left;1 | BUCK_ENABLE | pcb_port_394 | pcb_smtpad_386 | False | False
R97 | 2 | pin2 | pin2;cathode;neg;right;2 | GND | pcb_port_395 | pcb_copper_pour_88 | True | False
C76 | 1 | pin1 | pin1;1 | VSYS | pcb_port_396 | pcb_smtpad_287 | False | False
C76 | 2 | pin2 | pin2;2 | GND | pcb_port_397 | pcb_copper_pour_88 | True | False
C77 | 1 | pin1 | pin1;1 | BUCK_ENABLE | pcb_port_398 | pcb_smtpad_386 | False | False
C77 | 2 | pin2 | pin2;2 | GND | pcb_port_399 | pcb_copper_pour_88 | True | False
U4 | 1 | WS | WS;pin1;1 | MIC_WS | pcb_port_400 | pcb_smtpad_391 | False | False
U4 | 2 | LR | LR;pin2;2 | GND | pcb_port_401 | pcb_copper_pour_88 | True | False
U4 | 3 | GND | GND;pin3;3 | GND | pcb_port_402 | pcb_copper_pour_88 | True | False
U4 | 4 | SCK | SCK;pin4;4 | MIC_BCLK | pcb_port_403 | pcb_smtpad_393 | False | False
U4 | 5 | VDD | VDD;pin5;5 | VMIC | pcb_port_404 | pcb_smtpad_401 | False | False
U4 | 6 | SD | SD;pin6;6 | MIC_SD | pcb_port_405 | pcb_smtpad_395 | False | False
U4 |  | pin3_internal_1 | pin3_internal_1;pin3;3 | GND | pcb_port_406 | pcb_copper_pour_88 | True | False
U4 |  | pin3_internal_2 | pin3_internal_2;pin3;3 | GND | pcb_port_407 | pcb_copper_pour_88 | True | False
U4 |  | pin3_internal_3 | pin3_internal_3;pin3;3 | GND | pcb_port_408 | pcb_copper_pour_88 | True | False
U5 | 1 | WS | WS;pin1;1 | MIC_WS | pcb_port_409 | pcb_smtpad_391 | False | False
U5 | 2 | LR | LR;pin2;2 | VMIC | pcb_port_410 | pcb_smtpad_401 | False | False
U5 | 3 | GND | GND;pin3;3 | GND | pcb_port_411 | pcb_copper_pour_88 | True | False
U5 | 4 | SCK | SCK;pin4;4 | MIC_BCLK | pcb_port_412 | pcb_smtpad_393 | False | False
U5 | 5 | VDD | VDD;pin5;5 | VMIC | pcb_port_413 | pcb_smtpad_401 | False | False
U5 | 6 | SD | SD;pin6;6 | MIC_SD | pcb_port_414 | pcb_smtpad_395 | False | False
U5 |  | pin3_internal_1 | pin3_internal_1;pin3;3 | GND | pcb_port_415 | pcb_copper_pour_88 | True | False
U5 |  | pin3_internal_2 | pin3_internal_2;pin3;3 | GND | pcb_port_416 | pcb_copper_pour_88 | True | False
U5 |  | pin3_internal_3 | pin3_internal_3;pin3;3 | GND | pcb_port_417 | pcb_copper_pour_88 | True | False
C80 | 1 | pin1 | pin1;1 | VMIC | pcb_port_418 | pcb_smtpad_401 | False | False
C80 | 2 | pin2 | pin2;2 | GND | pcb_port_419 | pcb_copper_pour_88 | True | False
C81 | 1 | pin1 | pin1;1 | VMIC | pcb_port_420 | pcb_smtpad_401 | False | False
C81 | 2 | pin2 | pin2;2 | GND | pcb_port_421 | pcb_copper_pour_88 | True | False
U7 | 2 | pin2 | pin2;GND;2 | GND | pcb_port_422 | pcb_copper_pour_88 | True | False
U7 | 3 | pin3 | pin3;IN_POS;3 | MIC_SD | pcb_port_423 | pcb_smtpad_395 | False | False
U7 | 4 | pin4 | pin4;IN_NEG;4 | MIC_SD_REF | pcb_port_424 | pcb_smtpad_422 | False | False
U7 | 5 | pin5 | pin5;VCC;5 | V3V3 | pcb_port_425 | pcb_smtpad_480 | False | False
U7 | 1 | pin1 | pin1;OUT;1 | MIC_SD_BUFFERED | pcb_port_426 | pcb_smtpad_417 | False | False
R26 | 1 | pin1 | pin1;anode;pos;left;1 | MIC_SD | pcb_port_427 | pcb_smtpad_395 | False | False
R26 | 2 | pin2 | pin2;cathode;neg;right;2 | GND | pcb_port_428 | pcb_copper_pour_88 | True | False
R27 | 1 | pin1 | pin1;anode;pos;left;1 | MIC_SD_BUFFERED | pcb_port_429 | pcb_smtpad_417 | False | False
R27 | 2 | pin2 | pin2;cathode;neg;right;2 | MCU_MIC_SD | pcb_port_430 | pcb_smtpad_421 | False | False
R29 | 1 | pin1 | pin1;anode;pos;left;1 | VMIC | pcb_port_431 | pcb_smtpad_401 | False | False
R29 | 2 | pin2 | pin2;cathode;neg;right;2 | MIC_SD_REF | pcb_port_432 | pcb_smtpad_422 | False | False
R30 | 1 | pin1 | pin1;anode;pos;left;1 | MIC_SD_REF | pcb_port_433 | pcb_smtpad_422 | False | False
R30 | 2 | pin2 | pin2;cathode;neg;right;2 | GND | pcb_port_434 | pcb_copper_pour_88 | True | False
C25 | 1 | pin1 | pin1;1 | V3V3 | pcb_port_435 | pcb_smtpad_480 | False | False
C25 | 2 | pin2 | pin2;2 | GND | pcb_port_436 | pcb_copper_pour_88 | True | False
C26 | 1 | pin1 | pin1;1 | MIC_SD_REF | pcb_port_437 | pcb_smtpad_422 | False | False
C26 | 2 | pin2 | pin2;2 | GND | pcb_port_438 | pcb_copper_pour_88 | True | False
SW4 | 1 | pin1 | pin1;1 | V3V3 | pcb_port_439 | pcb_smtpad_480 | False | False
SW4 | 2 | pin2 | pin2;2 | HOLD_HARDWARE | pcb_port_440 | pcb_smtpad_372 | False | False
SW1 | 1 | pin1 | pin1;1 | MCU_BOOT_N | pcb_port_441 | pcb_smtpad_433 | False | False
SW1 | 2 | pin2 | pin2;2 | GND | pcb_port_442 | pcb_copper_pour_88 | True | False
SW2 | 1 | pin1 | pin1;1 | MCU_EN | pcb_port_443 | pcb_smtpad_85 | False | False
SW2 | 2 | pin2 | pin2;2 | GND | pcb_port_444 | pcb_copper_pour_88 | True | False
SW5 | 1 | pin1 | pin1;1 | V3V3 | pcb_port_445 | pcb_smtpad_480 | False | False
SW5 | 2 | pin2 | pin2;2 | MIC_INPUT | pcb_port_446 | pcb_smtpad_441 | False | False
SW5 | 3 | pin3 | pin3;3 | GND | pcb_port_447 | pcb_copper_pour_88 | True | False
SW5 | 4 | pin4 | pin4;4 | GND | pcb_port_448 | pcb_copper_pour_88 | True | False
SW5 |  | pin4_internal_1 | pin4_internal_1;pin4;4 | GND | pcb_port_449 | pcb_copper_pour_88 | True | False
SW5 |  | pin4_internal_2 | pin4_internal_2;pin4;4 | GND | pcb_port_450 | pcb_copper_pour_88 | True | False
SW5 |  | pin4_internal_3 | pin4_internal_3;pin4;4 | GND | pcb_port_451 | pcb_copper_pour_88 | True | False
TP_MOTOR_P | 1 | pin1 | pin1;1 | VMOTOR | pcb_port_452 | pcb_smtpad_321 | False | False
TP_MOTOR_N | 1 | pin1 | pin1;1 | HAPTIC_N | pcb_port_453 | pcb_smtpad_444 | False | False
U27 | 1 | ISET | ISET;pin1;1 |  | pcb_port_454 | pcb_smtpad_463 | False | False
U27 | 2 | D5 | D5;pin2;2 |  | pcb_port_455 | pcb_smtpad_446 | False | False
U27 | 3 | D4 | D4;pin3;3 | LCD_BACKLIGHT_RETURN_4 | pcb_port_456 | pcb_smtpad_447 | True | True
U27 | 4 | D3 | D3;pin4;4 | LCD_BACKLIGHT_RETURN_3 | pcb_port_457 | pcb_smtpad_448 | True | True
U27 | 5 | D2 | D2;pin5;5 | LCD_BACKLIGHT_RETURN_2 | pcb_port_458 | pcb_smtpad_449 | True | True
U27 | 6 | D1 | D1;pin6;6 | LCD_BACKLIGHT_RETURN_1 | pcb_port_459 | pcb_smtpad_450 | True | True
U27 | 7 | PGND | PGND;pin7;7 | GND | pcb_port_460 | pcb_copper_pour_88 | True | False
U27 | 8 | VOUT | VOUT;pin8;8 | LCD_BACKLIGHT_OUTPUT | pcb_port_461 | pcb_smtpad_452 | True | False
U27 | 9 | C2_POS | C2_POS;pin9;9 |  | pcb_port_462 | pcb_smtpad_453 | False | False
U27 | 10 | C1_POS | C1_POS;pin10;10 |  | pcb_port_463 | pcb_smtpad_469 | False | False
U27 | 11 | C1_NEG | C1_NEG;pin11;11 |  | pcb_port_464 | pcb_smtpad_468 | False | False
U27 | 12 | C2_NEG | C2_NEG;pin12;12 |  | pcb_port_465 | pcb_smtpad_456 | False | False
U27 | 13 | VIN | VIN;pin13;13 | V3V3 | pcb_port_466 | pcb_smtpad_480 | False | False
U27 | 14 | GND | GND;pin14;14 | GND | pcb_port_467 | pcb_copper_pour_88 | True | False
U27 | 15 | EN1 | EN1;pin15;15 | BACKLIGHT_GATE | pcb_port_468 | pcb_smtpad_460 | False | False
U27 | 16 | EN2 | EN2;pin16;16 | BACKLIGHT_GATE | pcb_port_469 | pcb_smtpad_460 | False | False
U27 | 17 | EP | EP;pin17;17 | GND | pcb_port_470 | pcb_copper_pour_88 | True | False
R102 | 1 | pin1 | pin1;anode;pos;left;1 |  | pcb_port_471 | pcb_smtpad_463 | False | False
R102 | 2 | pin2 | pin2;cathode;neg;right;2 | GND | pcb_port_472 | pcb_copper_pour_88 | True | False
R103 | 1 | pin1 | pin1;anode;pos;left;1 | MCU_BACKLIGHT_PWM | pcb_port_473 | pcb_smtpad_465 | False | False
R103 | 2 | pin2 | pin2;cathode;neg;right;2 | BACKLIGHT_GATE | pcb_port_474 | pcb_smtpad_460 | False | False
R104 | 1 | pin1 | pin1;anode;pos;left;1 | BACKLIGHT_GATE | pcb_port_475 | pcb_smtpad_460 | False | False
R104 | 2 | pin2 | pin2;cathode;neg;right;2 | GND | pcb_port_476 | pcb_copper_pour_88 | True | False
C82 | 1 | pin1 | pin1;1 |  | pcb_port_477 | pcb_smtpad_469 | False | False
C82 | 2 | pin2 | pin2;2 |  | pcb_port_478 | pcb_smtpad_468 | False | False
C83 | 1 | pin1 | pin1;1 |  | pcb_port_479 | pcb_smtpad_453 | False | False
C83 | 2 | pin2 | pin2;2 |  | pcb_port_480 | pcb_smtpad_456 | False | False
C84 | 1 | pin1 | pin1;1 | V3V3 | pcb_port_481 | pcb_smtpad_480 | False | False
C84 | 2 | pin2 | pin2;2 | GND | pcb_port_482 | pcb_copper_pour_88 | True | False
C85 | 1 | pin1 | pin1;1 | LCD_BACKLIGHT_OUTPUT | pcb_port_483 | pcb_smtpad_452 | True | False
C85 | 2 | pin2 | pin2;2 | GND | pcb_port_484 | pcb_copper_pour_88 | True | False
TP1 | 1 | pin1 | pin1;1 | GND | pcb_port_485 | pcb_copper_pour_88 | True | False
TP2 | 1 | pin1 | pin1;1 | VBUS | pcb_port_486 | pcb_smtpad_112 | False | False
TP3 | 1 | pin1 | pin1;1 | PACK_BAT | pcb_port_487 | pcb_smtpad_478 | False | False
TP4 | 1 | pin1 | pin1;1 | VSYS | pcb_port_488 | pcb_smtpad_287 | False | False
TP5 | 1 | pin1 | pin1;1 | V3V3 | pcb_port_489 | pcb_smtpad_480 | False | False
TP6 | 1 | pin1 | pin1;1 | VMIC | pcb_port_490 | pcb_smtpad_401 | False | False
TP7 | 1 | pin1 | pin1;1 | HOLD_HARDWARE | pcb_port_491 | pcb_smtpad_372 | False | False
TP8 | 1 | pin1 | pin1;1 | CHARGE_STATUS_N | pcb_port_492 | pcb_smtpad_483 | False | False
