AnasSarkiz/tscircuit-ai-agent-remote/BOM-preview.md

**Historical preview:** this table predates A5. J8 is now removed; see BOM.md and the fresh native circuit.json. This is not a fabrication CSV.

# A1 integrated preview inventory

Derived directly from the native full-board Circuit JSON. **Not an assembler BOM release.** Native fabrication CSV/MPN qualification remains B-015.

122 genuine imported electronic parts plus 8 native copper pads. Stock/rating/footprint qualification remains provisional.

| Ref | Manufacturer part number | Exact JLC code |
|---|---|---|
| U1 | ESP32-S3-WROOM-1-N8R8 | C2913201 |
| J1 | TYPE-C-31-M-12 | C165948 |
| D2 | TPD2EUSB30ADRTR | C94934 |
| U12 | TPS3839G33DBZR | C485802 |
| J6 | SM06B-SRSS-TB(LF)(SN) | C160405 |
| R31 | RC0603FR-0722RL | C107701 |
| R32 | RC0603FR-0722RL | C107701 |
| R33 | RC0603FR-075K1L | C105580 |
| R34 | RC0603FR-075K1L | C105580 |
| R35 | RC0603FR-074K7L | C99782 |
| R36 | RC0603FR-0710KL | C98220 |
| R37 | RC0603FR-07100KL | C14675 |
| R38 | RC0603FR-071KL | C22548 |
| C30 | GRM188R61A106ME69D | C90053 |
| C31 | GRM188R71C104KA01D | C45000 |
| C32 | GRM188R71C104KA01D | C45000 |
| U16 | BQ24074RGTR | C54313 |
| J3 | S3B-PH-SM4-TB(LF)(SN) | C265101 |
| C1 | GRM188R61A106ME69D | C90053 |
| C2 | GRM188R61A106ME69D | C90053 |
| C3 | GRM188R61A106ME69D | C90053 |
| R1 | RC0603FR-073KL | C126358 |
| R2 | RC0603FR-073KL | C126358 |
| R3 | RC0603FR-07100KL | C14675 |
| R4 | RC0603FR-07100KL | C14675 |
| U2 | TPS63802DLAR | C2845237 |
| L1 | DFE201612E-R47M=P2 | C668312 |
| C4 | GRM188R61A106ME69D | C90053 |
| C5 | GRM188R61A226ME15D | C84419 |
| R5 | RC0603FR-0751K1L | C364359 |
| R6 | RC0603FR-079K1L | C114639 |
| R7 | RC0603FR-07100KL | C14675 |
| U13 | TPS7A2028PDBVR | C2869847 |
| U14 | SN74LVC245APWR | C7848 |
| J7 | AFC07-S10FCC-00 | C11050 |
| C40 | GRM188R61A106ME69D | C90053 |
| C41 | GRM188R61A226ME15D | C84419 |
| C42 | GRM188R71C104KA01D | C45000 |
| C43 | GRM188R71C104KA01D | C45000 |
| R40 | RC0603FR-07100KL | C14675 |
| R41 | RC0603FR-071KL | C22548 |
| R47 | RC0603FR-07100KL | C14675 |
| R42 | RC0603FR-0710KL | C98220 |
| R48 | RC0603FR-07100KL | C14675 |
| R43 | RC0603FR-0710KL | C98220 |
| R49 | RC0603FR-07100KL | C14675 |
| R44 | RC0603FR-0710KL | C98220 |
| R50 | RC0603FR-07100KL | C14675 |
| R45 | RC0603FR-0710KL | C98220 |
| R51 | RC0603FR-07100KL | C14675 |
| R46 | RC0603FR-0710KL | C98220 |
| U3 | MAX98357AETE+T | C910544 |
| Q1 | AO3400A | C20917 |
| Q2 | AO3401A | C15127 |
| J4 | S2B-PH-SM4-TB(LF)(SN) | C295747 |
| C50 | GRM188R61A106ME69D | C90053 |
| C51 | GRM188R71C104KA01D | C45000 |
| R60 | RC0603FR-07100RL | C105588 |
| R61 | RC0603FR-0710KL | C98220 |
| R62 | RC0603FR-071KL | C22548 |
| R63 | RC0603FR-07100RL | C105588 |
| R64 | RC0603FR-071KL | C22548 |
| R65 | RC0603FR-0722RL | C107701 |
| R68 | RC0603FR-0710KL | C98220 |
| R66 | RC0603FR-0722RL | C107701 |
| R69 | RC0603FR-0710KL | C98220 |
| R67 | RC0603FR-0722RL | C107701 |
| R70 | RC0603FR-0710KL | C98220 |
| U22 | TPS7A2030PDBVR | C963429 |
| Q9 | AO3400A | C20917 |
| D3 | SS14 | C2480 |
| C70 | GRM188R61A106ME69D | C90053 |
| C71 | GRM188R61A226ME15D | C84419 |
| C72 | GRM188R71C104KA01D | C45000 |
| R82 | RC0603FR-071KL | C22548 |
| R83 | RC0603FR-07100RL | C105588 |
| R84 | RC0603FR-0710KL | C98220 |
| R85 | RC0603FR-07100KL | C14675 |
| U23 | TPS7A2028PDBVR | C2869847 |
| U24 | 74LVC2G07GW,125 | C24478 |
| C73 | GRM188R61A106ME69D | C90053 |
| C74 | GRM188R61A106ME69D | C90053 |
| C75 | GRM188R71C104KA01D | C45000 |
| R86 | RC0603FR-071KL | C22548 |
| R87 | RC0603FR-07100KL | C14675 |
| R88 | RC0603FR-07100RL | C105588 |
| R89 | RC0603FR-07100RL | C105588 |
| R90 | RC0603FR-0710KL | C98220 |
| R91 | RC0603FR-0710KL | C98220 |
| R92 | RC0603FR-07330RL | C105881 |
| R93 | RC0603FR-07330RL | C105881 |
| R94 | RC0603FR-0710KL | C98220 |
| R95 | RC0603FR-0710KL | C98220 |
| U26 | SN74LVC1G17DBVR | C7836 |
| R99 | RC0603FR-0710KL | C98220 |
| R100 | 0603WAF1001T5E | C21190 |
| C78 | GRM188R71C104KA01D | C45000 |
| U25 | TPS3808G33DBVR | C43698 |
| R96 | RC0603FR-07470KL | C114622 |
| R97 | RC0603FR-07470KL | C114622 |
| C76 | GRM188R71C104KA01D | C45000 |
| C77 | GRM188R71C104KA01D | C45000 |
| U4 | ICS-43434 | C5656610 |
| U5 | ICS-43434 | C5656610 |
| C80 | GRM188R71C104KA01D | C45000 |
| C81 | GRM188R71C104KA01D | C45000 |
| U7 | TLV3201AIDBVR | C105188 |
| R26 | RC0603FR-07100KL | C14675 |
| R27 | RC0603FR-071KL | C22548 |
| R29 | RC0603FR-0710KL | C98220 |
| R30 | RC0603FR-0710KL | C98220 |
| C25 | GRM188R71C104KA01D | C45000 |
| C26 | GRM188R71C104KA01D | C45000 |
| SW4 | SKSWCFE010 | C255576 |
| SW1 | SKSWCFE010 | C255576 |
| SW2 | SKSWCFE010 | C255576 |
| SW5 | MSK12C02 | C431540 |
| J8 | S2B-PH-SM4-TB(LF)(SN) | C295747 |
| Q10 | AO3400A | C20917 |
| R102 | RC0603FR-07100RL | C105588 |
| R103 | RC0603FR-07100RL | C105588 |
| R104 | RC0603FR-0710KL | C98220 |
| TP1 | Native test pad | Native copper feature |
| TP2 | Native test pad | Native copper feature |
| TP3 | Native test pad | Native copper feature |
| TP4 | Native test pad | Native copper feature |
| TP5 | Native test pad | Native copper feature |
| TP6 | Native test pad | Native copper feature |
| TP7 | Native test pad | Native copper feature |
| TP8 | Native test pad | Native copper feature |
