AnasSarkiz/tscircuit-ai-agent-remote/evidence/layout-bom-audit-2026-10-04/inventory.md

# Current source inventory — audit only

Generated from the unchanged native Circuit JSON. This is not an approved assembler BOM. Stock is the exact catalogue observation, not reserved assembly allocation.

| JLC | Exact source MPN | References | Qty | Observed stock |
|---|---|---|---:|---:|
| C2480 | SS14 | D3 | 1 | 2818967 |
| C7836 | SN74LVC1G17DBVR | U26 | 1 | 34179 |
| C7848 | SN74LVC245APWR | U14 | 1 | 75200 |
| C14675 | RC0603FR-07100KL | R37, R3, R4, R7, R40, R47, R48, R49, R50, R51, R85, R87, R26 | 13 | 5999 |
| C15127 | AO3401A | Q2 | 1 | 715902 |
| C15849 | CL10A105KB8NNNC | C82, C83 | 2 | 5979916 |
| C19666 | CL10A475KO8NNNC | C1 | 1 | 1373603 |
| C20917 | AO3400A | Q1, Q9 | 2 | 1535925 |
| C21190 | 0603WAF1001T5E | R100 | 1 | 8013731 |
| C22548 | RC0603FR-071KL | R38, R41, R62, R64, R82, R86, R27 | 7 | 5 |
| C24478 | 74LVC2G07GW,125 | U24 | 1 | 348 |
| C43698 | TPS3808G33DBVR | U25 | 1 | 6139 |
| C45000 | GRM188R71C104KA01D | C31, C32, C42, C43, C51, C72, C75, C78, C76, C77, C80, C81, C25, C26 | 14 | 3848 |
| C54313 | BQ24074RGTR | U16 | 1 | 677 |
| C84419 | GRM188R61A226ME15D | C5, C41, C71 | 3 | 55406 |
| C90053 | GRM188R61A106ME69D | C30, C2, C3, C4, C40, C50, C70, C73, C74, C84, C85 | 11 | 8623 |
| C94934 | TPD2EUSB30ADRTR | D2 | 1 | 5439 |
| C98220 | RC0603FR-0710KL | R36, R42, R43, R44, R45, R46, R61, R68, R69, R70, R84, R90, R91, R94, R95, R99, R29, R30, R102, R104 | 20 | 22 |
| C99782 | RC0603FR-074K7L | R35 | 1 | 20923 |
| C105188 | TLV3201AIDBVR | U7 | 1 | 31358 |
| C105580 | RC0603FR-075K1L | R33, R34 | 2 | 5622 |
| C105588 | RC0603FR-07100RL | R60, R63, R83, R88, R89, R103 | 6 | No exact in-stock result |
| C105881 | RC0603FR-07330RL | R92, R93 | 2 | 85110 |
| C107701 | RC0603FR-0722RL | R31, R32, R65, R66, R67 | 5 | 8 |
| C114622 | RC0603FR-07470KL | R96, R97 | 2 | 44425 |
| C114639 | RC0603FR-079K1L | R6 | 1 | 14893 |
| C126358 | RC0603FR-073KL | R1, R2 | 2 | 192 |
| C157929 | S3B-PH-K-S(LF)(SN) | J3 | 1 | 227315 |
| C160405 | SM06B-SRSS-TB(LF)(SN) | J6 | 1 | 60961 |
| C165948 | TYPE-C-31-M-12 | J1 | 1 | 89797 |
| C173752 | S2B-PH-K-S(LF)(SN) | J4 | 1 | 100050 |
| C255576 | SKSWCFE010 | SW4, SW1, SW2 | 3 | 18510 |
| C262650 | AFC07-S50ECA-00 | J7 | 1 | 28817 |
| C364359 | RC0603FR-0751K1L | R5 | 1 | 7984 |
| C431540 | MSK12C02 | SW5 | 1 | 147825 |
| C485802 | TPS3839G33DBZR | U12 | 1 | 3520 |
| C668312 | DFE201612E-R47M=P2 | L1 | 1 | 1427 |
| C910544 | MAX98357AETE+T | U3 | 1 | 29625 |
| C963429 | TPS7A2030PDBVR | U22 | 1 | 6825 |
| C1848364 | TPS60230RGTR | U27 | 1 | 2723 |
| C2845237 | TPS63802DLAR | U2 | 1 | 3970 |
| C2869847 | TPS7A2028PDBVR | U13, U23 | 2 | 71 |
| C2913201 | ESP32-S3-WROOM-1-N8R8 | U1 | 1 | 6547 |
| C5656610 | ICS-43434 | U4, U5 | 2 | 3807 |
