AnasSarkiz/tscircuit-ai-agent-remote/evidence/routing-intake-2026-10-04/AFC07-S12FCC-00-supplier-html.txt

<!DOCTYPE html><html lang="en"><head><meta charSet="utf-8"/><meta name="viewport" content="width=device-width, initial-scale=1, minimum-scale=0.3, maximum-scale=2, user-scalable=yes"/><link rel="canonical" href="https://www.lcsc.com/datasheet/C11051.pdf"/><meta property="og:site_name" content="LCSC Electronics"/><meta property="og:locale" content="en_US"/><meta property="og:url" content="https://www.lcsc.com/datasheet/C11051.pdf"/><title>AFC07-S12FCC-00 | Datasheet | JUSHUO | LCSC Electronics</title><meta name="description" content="Free download the datasheet for AFC07-S12FCC-00 from JUSHUO."/><meta name="keywords" content="JUSHUO | AFC07-S12FCC-00 | Datasheet"/><script type="application/ld+json">{"@context":"https://schema.org/","@type":"Article","name":"AFC07-S12FCC-00 | Datasheet | JUSHUO | LCSC Electronics","description":"Free download the datasheet for AFC07-S12FCC-00 from JUSHUO."}</script><meta name="next-head-count" content="10"/><link rel="preconnect" href="https://assets.lcsc.com"/><link rel="preconnect" href="https://static.lcsc.com"/><link rel="preconnect" href="https://www.googletagmanager.com"/><link rel="dns-prefetch" href="https://wmsc.lcsc.com"/><link rel="dns-prefetch" href="https://monitor.lcsc.com"/><link rel="preload" href="https://static.lcsc.com/feassets/svg/wmsc/sprite.svg?version=1790042845018" as="fetch" crossorigin="anonymous"/><link rel="preload" href="https://static.lcsc.com/feassets/pc/fonts/poppins/Poppins-Regular.ttf" as="font" type="font/ttf" crossorigin="anonymous"/><link rel="preload" href="https://static.lcsc.com/feassets/pc/fonts/poppins/Poppins-SemiBold.ttf" as="font" type="font/ttf" crossorigin="anonymous"/><link rel="shortcut icon" href="https://static.lcsc.com/feassets/pc/images/favicon.ico" type="image/x-icon"/><link rel="bookmark" href="https://static.lcsc.com/feassets/pc/images/favicon.ico" type="image/x-icon"/><meta http-equiv="X-UA-Compatible" content="IE=edge,chrome=1"/><meta name="renderer" content="webkit"/><meta name="google" content="notranslate"/><meta name="data-spm" content="wm"/><meta name="revised" content="1790042845018"/><script id="ga-consent-default" data-nscript="beforeInteractive" crossorigin="anonymous">window.dataLayer=window.dataLayer||[];function gtag(){dataLayer.push(arguments)}gtag('consent','default',{ad_storage:'denied',ad_user_data:'denied',ad_personalization:'denied',analytics_storage:'denied'});</script><script id="apmScriptId" data-nscript="beforeInteractive" crossorigin="anonymous">
              !(function (c, b, d, a) {
                  c[a] = c[a] || {};
                  c[a] = {
                    url: 'https://monitor.lcsc.com/monitor',
                    appID: 'nextjs-item-app',
                    env: 'pro'
                  };
                  const script = b.createElement('script');
                  script.src = d;
                  var ss = document.getElementsByTagName('script')[0];
                  ss.parentNode.insertBefore(script, ss);
                })(window, document, 'https://static.lcsc.com/js/fe-monitor/1.3.5/monitor.js?version=1790042845018', '__apmbl');
              </script><link rel="preload" href="https://static.lcsc.com/item/_next/static/css/97b0a3afa2b47dc6.css" as="style" crossorigin="anonymous"/><link rel="stylesheet" href="https://static.lcsc.com/item/_next/static/css/97b0a3afa2b47dc6.css" crossorigin="anonymous" data-n-g=""/><noscript data-n-css=""></noscript><script defer="" crossorigin="anonymous" nomodule="" src="https://static.lcsc.com/item/_next/static/chunks/polyfills-42372ed130431b0a.js"></script><script src="https://static.lcsc.com/item/_next/static/chunks/webpack-4ba145bf429890b2.js" defer="" crossorigin="anonymous"></script><script src="https://static.lcsc.com/item/_next/static/chunks/framework-79e9ccd1d3295a61.js" defer="" crossorigin="anonymous"></script><script src="https://static.lcsc.com/item/_next/static/chunks/main-9c51b8ca90eb898d.js" defer="" crossorigin="anonymous"></script><script src="https://static.lcsc.com/item/_next/static/chunks/pages/_app-4a9a9832873f37d2.js" defer="" crossorigin="anonymous"></script><script src="https://static.lcsc.com/item/_next/static/chunks/pages/datasheet/%5Bid%5D-7aa86b284fbbd384.js" defer="" crossorigin="anonymous"></script><script src="https://static.lcsc.com/item/_next/static/onUTry6LftoaiS4QeCJe0/_buildManifest.js" defer="" crossorigin="anonymous"></script><script src="https://static.lcsc.com/item/_next/static/onUTry6LftoaiS4QeCJe0/_ssgManifest.js" defer="" crossorigin="anonymous"></script></head><body class="lcsc-i1-c0" data-spm="ggs"><script>(function () {
  var SPRITE_URL = 'https://static.lcsc.com/feassets/svg/wmsc/sprite.svg?version=1790042845018';
  var SPRITE_ID = 'svg-sprite-wmsc';
  var TIMEOUT = 10000;
  var retried = false;

  function parseSprite(text) {
    var svg = new DOMParser().parseFromString(text, 'image/svg+xml').documentElement;
    // DOMParser 对非良构 XML 不抛错，而是返回 <parsererror> 根节点；显式校验，避免坏内容被注入
    if (svg.nodeName === 'parsererror' || svg.namespaceURI !== 'http://www.w3.org/2000/svg') {
      throw new Error('invalid sprite content');
    }
    return svg;
  }

  function inject(text) {
    if (document.getElementById(SPRITE_ID)) return;
    var svg = parseSprite(text);
    svg.setAttribute('id', SPRITE_ID);
    svg.setAttribute('aria-hidden', 'true');
    svg.style.cssText = 'position:absolute;width:0;height:0;overflow:hidden;';
    document.body.prepend(svg);
  }

  function load() {
    // 对齐 SvgIcon 兜底的 10s 超时：fetch 默认无超时，悬挂请求会让标记永久卡在 true
    var controller = typeof AbortController !== 'undefined' ? new AbortController() : null;
    var timer = controller ? setTimeout(function () { controller.abort(); }, TIMEOUT) : null;
    fetch(SPRITE_URL, { signal: controller ? controller.signal : undefined })
      .then(function (res) {
        if (!res.ok) throw new Error('HTTP ' + res.status);
        return res.text();
      })
      .then(function (text) {
        if (text.indexOf('<symbol') === -1) throw new Error('invalid sprite content');
        inject(text);
      })
      .catch(function (err) {
        if (timer) clearTimeout(timer);
        console.error('[svg-sprite] Failed to load:', err);
        if (retried) {
          // 彻底失败后放开对应 app 的标记并通知 SvgIcon 兜底接管（含已挂载、effect 已早退的组件）
          window.__svgSpriteHandled['wmsc'] = false;
          window.dispatchEvent(new CustomEvent('svg-sprite-failed', { detail: { app: 'wmsc' } }));
          return;
        }
        retried = true;
        setTimeout(load, 3000);
      });
  }

  if (window.fetch) {
    // 按 app 键控，避免单个全局布尔误判多 app 场景
    window.__svgSpriteHandled = window.__svgSpriteHandled || {};
    window.__svgSpriteHandled['wmsc'] = true;
    load();
  }
})();</script><div id="__next"><div class="relative flex h-screen w-screen [word-break:break-word]"><iframe src="https://datasheet.lcsc.com/datasheet/pdf/f5f48304d1bacdadded5d0c3d32d01c0.pdf?productCode=C11051" loading="lazy" frameBorder="0" rel="nofollow" class="hidden flex-1 lg:block" title="Datasheet PDF"></iframe><iframe src="https://static.lcsc.com/feassets/pc/html/pdfjs/web/viewer.html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" loading="lazy" frameBorder="0" rel="nofollow" class="flex-1 lg:hidden" title="Datasheet PDF Viewer"></iframe></div></div><script id="__NEXT_DATA__" type="application/json" crossorigin="anonymous">{"props":{"pageProps":{"tdkData":{"title":"AFC07-S12FCC-00 | Datasheet | JUSHUO | LCSC Electronics","description":"Free download the datasheet for AFC07-S12FCC-00 from JUSHUO.","keywords":"JUSHUO | AFC07-S12FCC-00 | Datasheet","articleJsonLd":{"@context":"https://schema.org/","@type":"Article","name":"AFC07-S12FCC-00 | Datasheet | JUSHUO | LCSC Electronics","description":"Free download the datasheet for AFC07-S12FCC-00 from JUSHUO."}},"previewPdfUrl":"https://datasheet.lcsc.com/datasheet/pdf/f5f48304d1bacdadded5d0c3d32d01c0.pdf?productCode=C11051","_sentryTraceData":"45ac5bf169ae94c71047187861c70a30-d2f395a5df33882c","_sentryBaggage":"sentry-environment=pro,sentry-release=nextjs-item-app%402026-09-22,sentry-public_key=4bd99c0425e32dd79d70b21be0d80d7b,sentry-trace_id=45ac5bf169ae94c71047187861c70a30"},"__N_SSP":true},"page":"/datasheet/[id]","query":{"id":"C11051.pdf"},"buildId":"onUTry6LftoaiS4QeCJe0","assetPrefix":"https://static.lcsc.com/item","isFallback":false,"isExperimentalCompile":false,"gssp":true,"scriptLoader":[{"id":"gtm-script","strategy":"afterInteractive","dangerouslySetInnerHTML":{"__html":"\n                  (function(w,d,s,l,i){w[l]=w[l]||[];w[l].push({'gtm.start':\n                  new Date().getTime(),event:'gtm.js'});var f=d.getElementsByTagName(s)[0],\n                  j=d.createElement(s),dl=l!=='dataLayer'?'\u0026l='+l:'';j.defer=true;j.src=\n                  'https://www.googletagmanager.com/gtm.js?id='+i+dl;f.parentNode.insertBefore(j,f);\n                  })(window,document,'script','dataLayer','GTM-5VJ4HKV');\n                "}}]}</script><noscript><p>This website requires JavaScript to function properly. Please enable JavaScript in your browser settings.</p></noscript></body></html>
