AnasSarkiz/tscircuit-ai-agent-remote/evidence/pcb-completion-2026-10-08/NOT-FOR-FABRICATION-bom.csv

Designator | Comment | Value | Footprint | JLCPCB Part #
U1 |  | C2913201 | C2913201 | C2913201
J1 |  | C165948 | C165948 | C165948
D2 |  | C94934 | C94934 | C94934
U12 |  | C485802 | C485802 | C485802
J6 |  | C160389 | C160389 | C160389
R31 | 22 | 22 | C107701 | C107701
R32 | 22 | 22 | C107701 | C107701
R33 | 5.1k | 5.1k | C105580 | C105580
R34 | 5.1k | 5.1k | C105580 | C105580
R35 | 4.7k | 4.7k | C99782 | C99782
R36 | 10k | 10k | C98220 | C98220
R37 | 100k | 100k | C14675 | C14675
R38 | 1k | 1k | C21190 | C21190
C30 | 22u | 22u | C84419 | C84419
C31 | 100n | 100n | C45000 | C45000
C32 | 100n | 100n | C45000 | C45000
U16 |  | C54313 | C54313 | C54313
J3 |  | C157929 | C157929 | C157929
C1 | 4.7u | 4.7u | C19666 | C19666
C2 | 10u | 10u | C90053 | C90053
C3 | 10u | 10u | C90053 | C90053
R1 | 3k | 3k | C126358 | C126358
R2 | 3k | 3k | C126358 | C126358
R3 | 100k | 100k | C14675 | C14675
R4 | 100k | 100k | C14675 | C14675
U2 |  | C2845237 | C2845237 | C2845237
L1 |  | C668312 | C668312 | C668312
C4 | 10u | 10u | C90053 | C90053
C5 | 22u | 22u | C84419 | C84419
R5 | 51.1k | 51.1k | C364359 | C364359
R6 | 9.1k | 9.1k | C114639 | C114639
R7 | 100k | 100k | C14675 | C14675
U13 |  | C2869847 | C2869847 | C2869847
U14 |  | C7848 | C7848 | C7848
J7 |  | C262650 | C262650 | C262650
C40 | 10u | 10u | C90053 | C90053
C41 | 22u | 22u | C84419 | C84419
C42 | 100n | 100n | C45000 | C45000
C43 | 100n | 100n | C45000 | C45000
R40 | 100k | 100k | C14675 | C14675
R41 | 1k | 1k | C21190 | C21190
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
U27 |  | C1848364 | C1848364 | C1848364
R102 | 10k | 10k | C98220 | C98220
R103 | 100 | 100 | C22775 | C22775
R104 | 10k | 10k | C98220 | C98220
C82 | 1u | 1u | C15849 | C15849
C83 | 1u | 1u | C15849 | C15849
C84 | 10u | 10u | C90053 | C90053
C85 | 10u | 10u | C90053 | C90053
