AnasSarkiz/tscircuit-ai-agent-remote/evidence/a6-bom-routing-2026-10-04/layers-contact-sheet.png

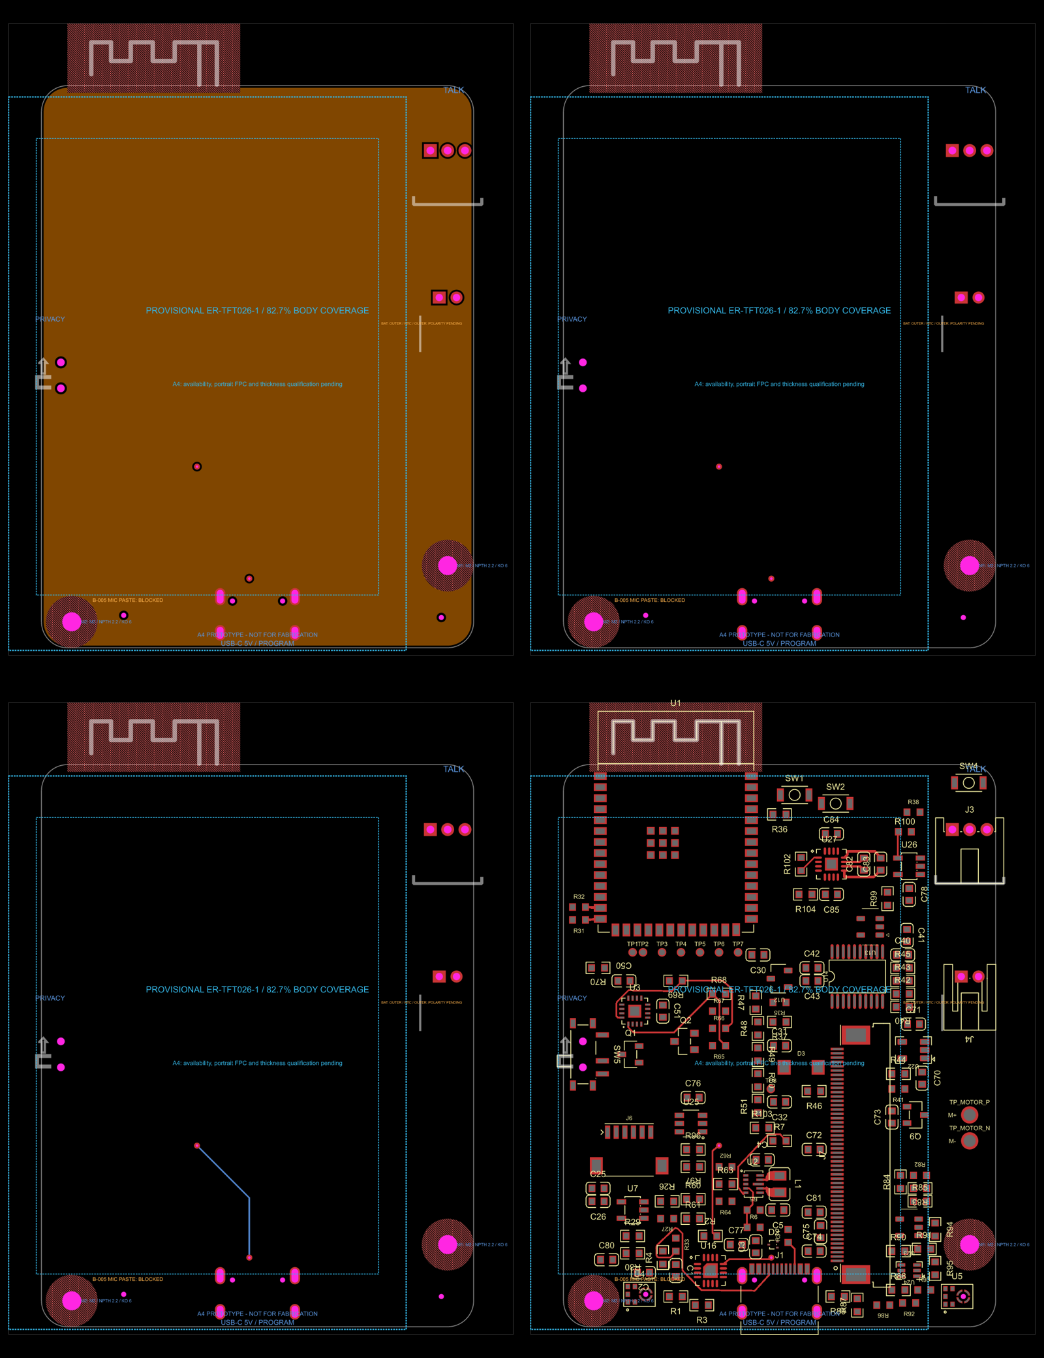
evidence/a6-bom-routing-2026-10-04/layers-contact-sheet.png
