AnasSarkiz/tscircuit-ai-agent-remote/evidence/a6-bom-routing-2026-10-04/sheet-MicrophonesSheet.png

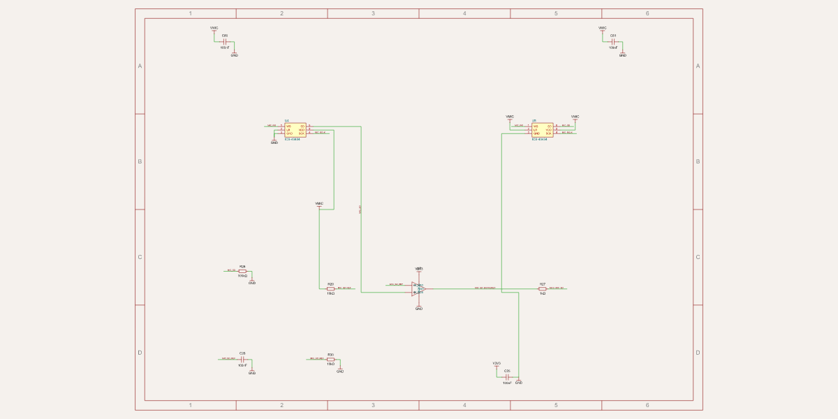
evidence/a6-bom-routing-2026-10-04/sheet-MicrophonesSheet.png
