AnasSarkiz/tscircuit-ai-agent-remote/evidence/layout-bom-audit-2026-10-04/native-paste-mask.png

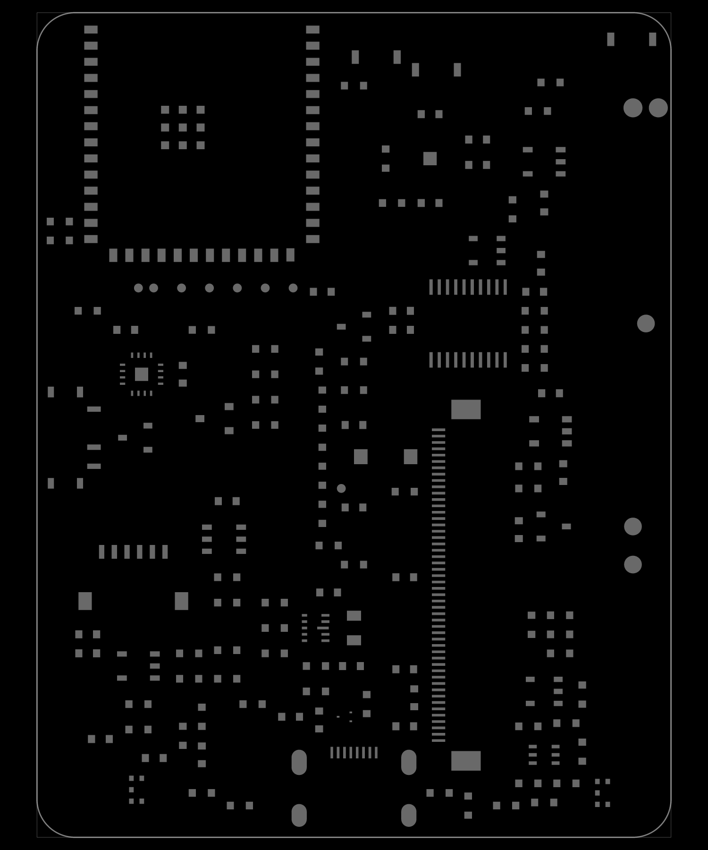
evidence/layout-bom-audit-2026-10-04/native-paste-mask.png
