AnasSarkiz/tscircuit-ai-agent-remote/evidence/layout-bom-audit-2026-10-04/sheet-13.png

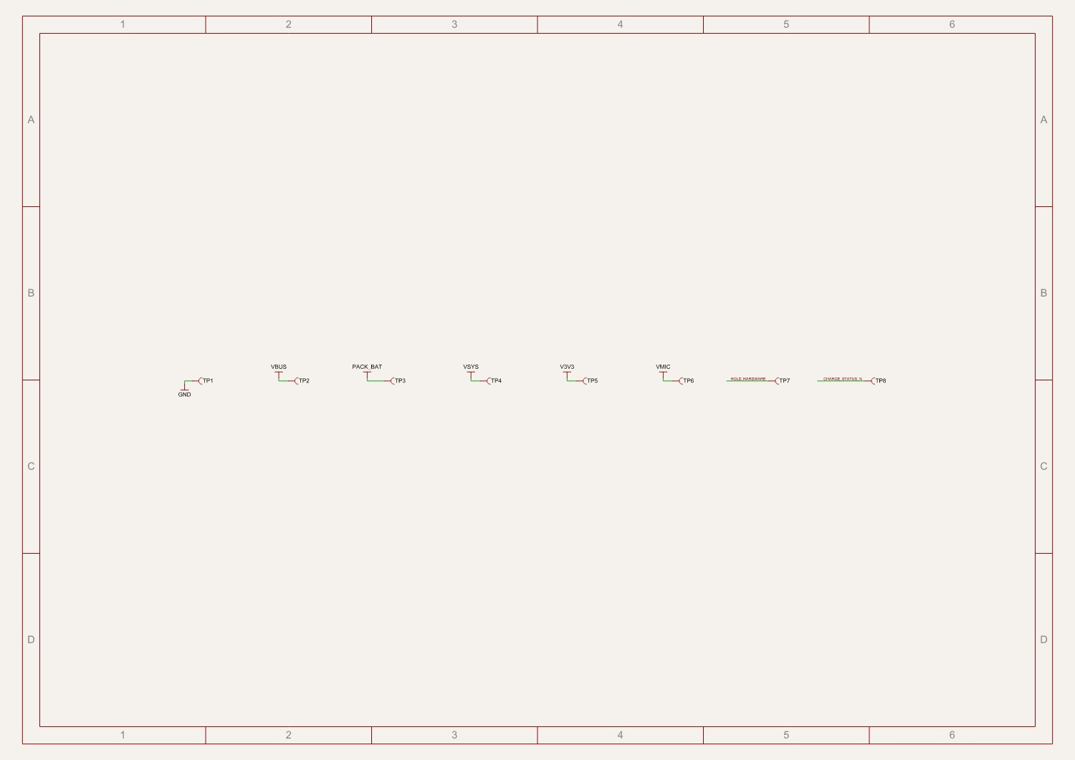
evidence/layout-bom-audit-2026-10-04/sheet-13.png
