AnasSarkiz/tscircuit-ai-agent-remote/evidence/layout-bom-audit-2026-10-04/sheets-1.png

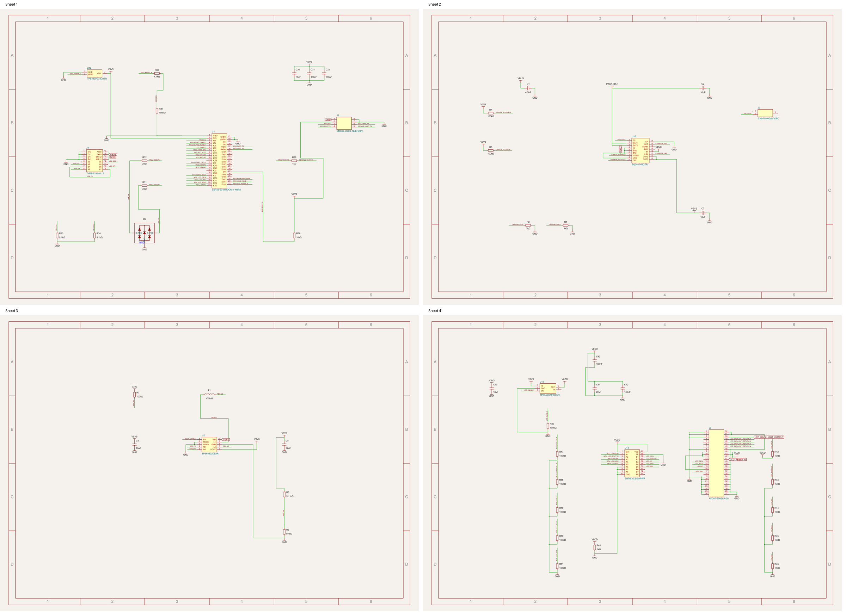
evidence/layout-bom-audit-2026-10-04/sheets-1.png
