AnasSarkiz/tscircuit-ai-agent-remote/evidence/layout-bom-audit-2026-10-04/sheets-9.png

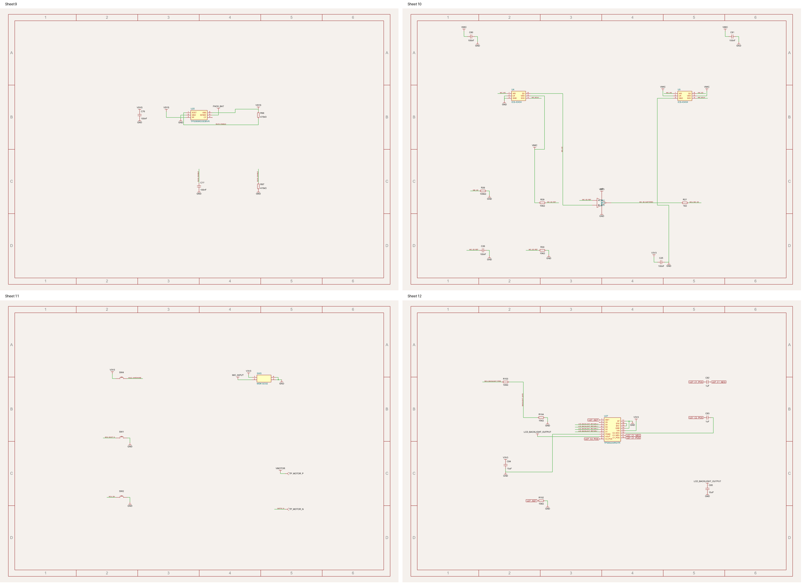
evidence/layout-bom-audit-2026-10-04/sheets-9.png
