AnasSarkiz/tscircuit-ai-agent-remote/evidence/routing-continuation-2026-10-07/pair-corridor-components.png

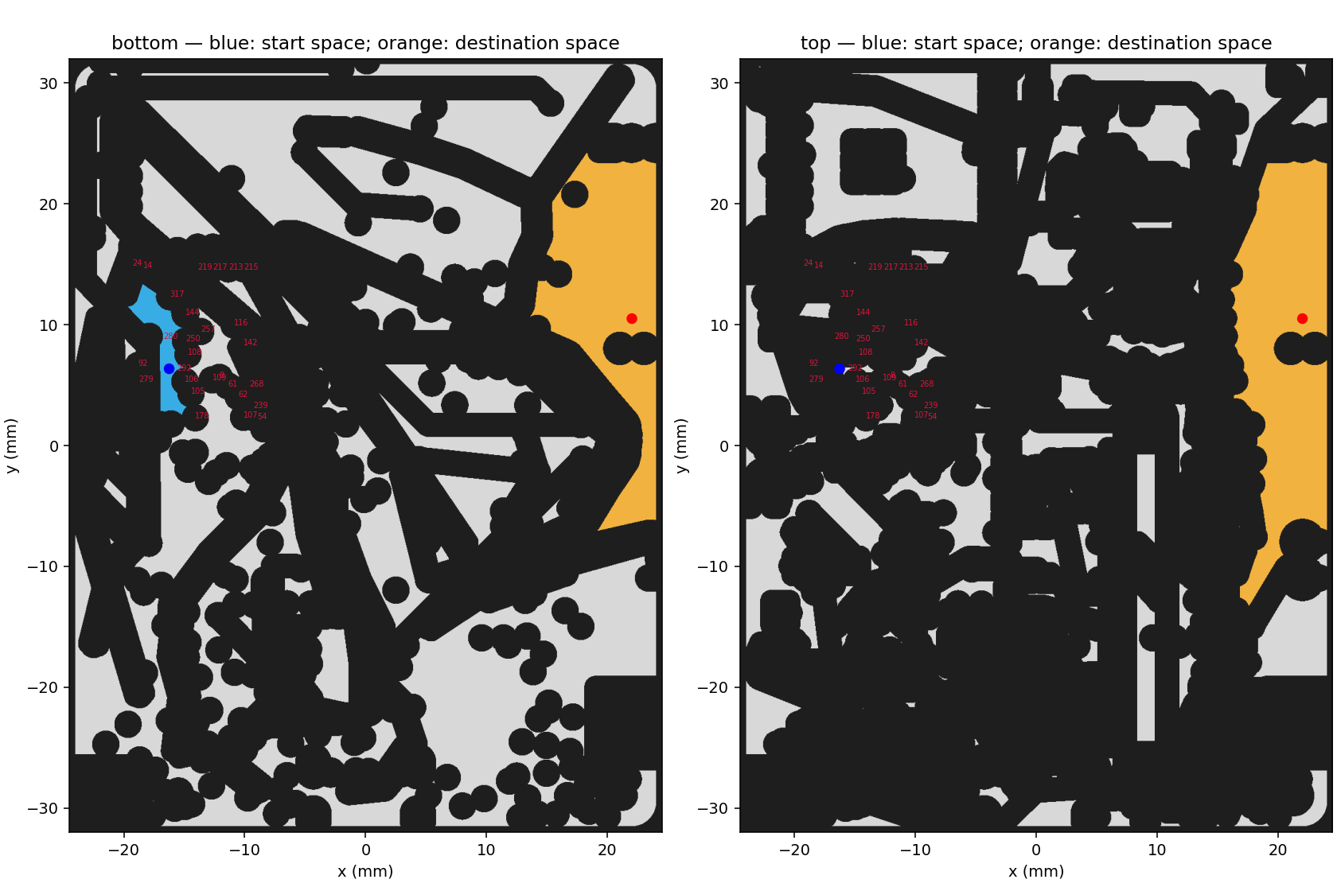
evidence/routing-continuation-2026-10-07/pair-corridor-components.png
