AnasSarkiz/tscircuit-ai-agent-remote/evidence/routing-continuation-2026-10-07/suppliers/aky2945-page9.png

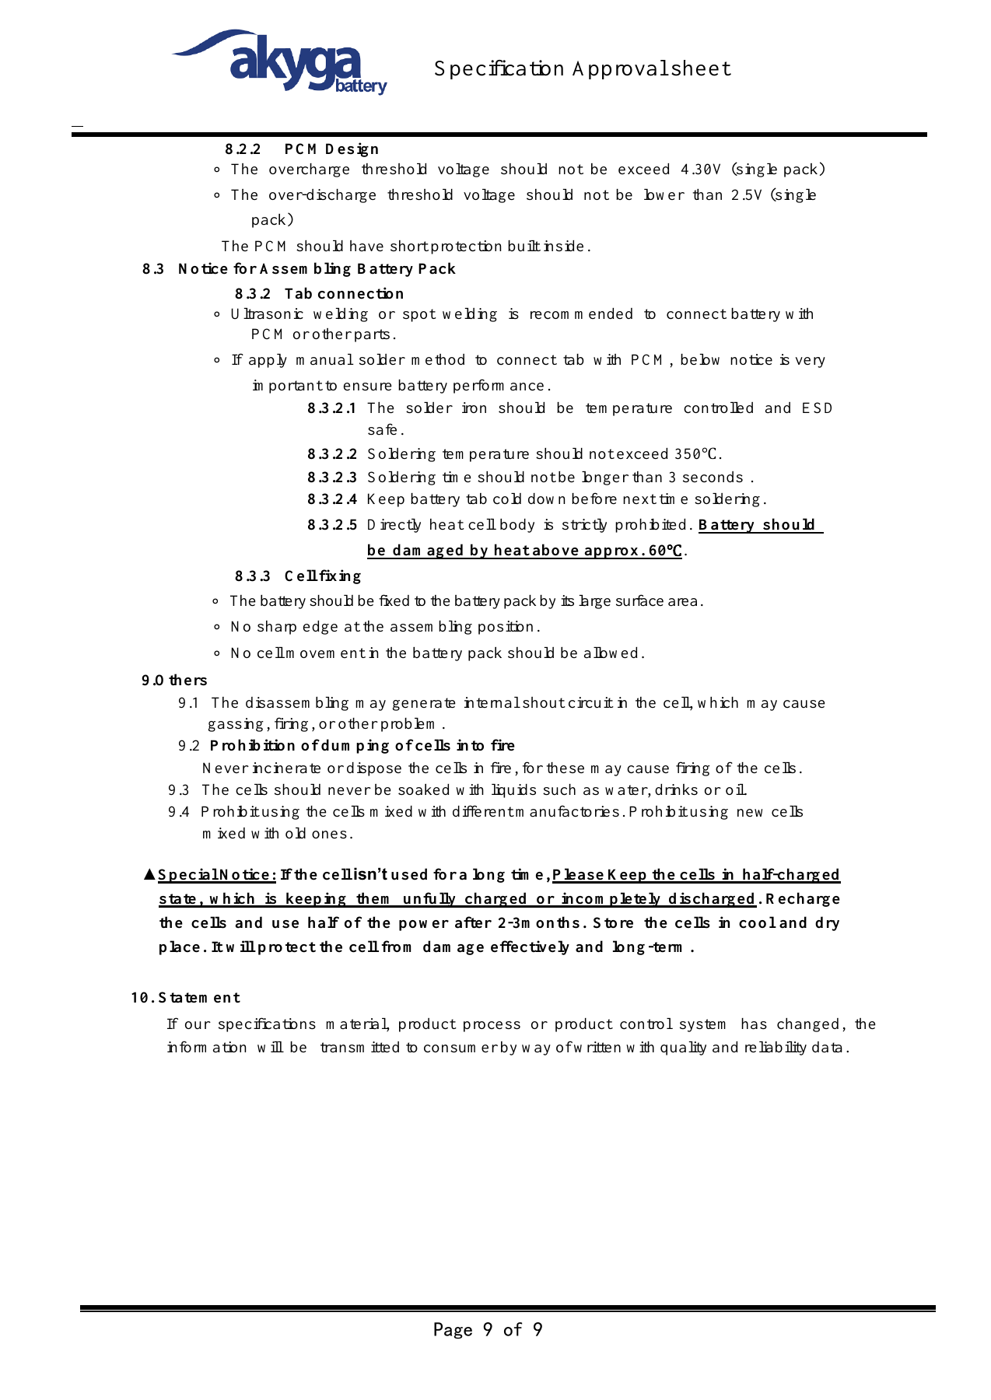
evidence/routing-continuation-2026-10-07/suppliers/aky2945-page9.png
