AnasSarkiz/tscircuit-ai-agent-remote/imports/SKSWCFE010/SKSWCFE010.step

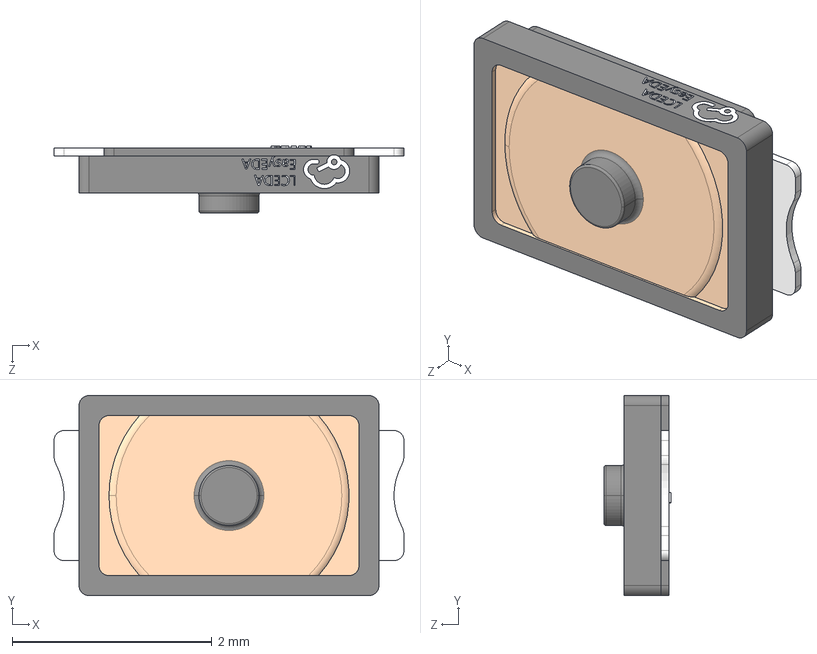
[picture p216: CAD file, 2026-10-03]
imports/SKSWCFE010/SKSWCFE010.step
3.50 x 2.00 x 0.67 mm
