AnasSarkiz/tscircuit-ai-agent-remote/imports/SM06B_SRSS_TB_LF__SN_/SM06B_SRSS_TB_LF__SN_.step

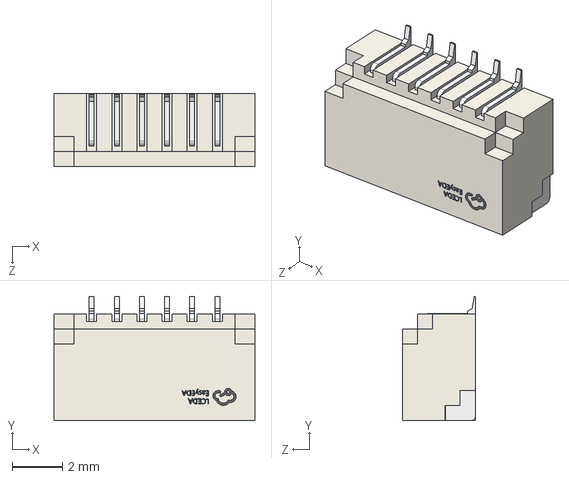
[picture p217: CAD file, 2026-10-03]
imports/SM06B_SRSS_TB_LF__SN_/SM06B_SRSS_TB_LF__SN_.step
8.00 x 4.95 x 2.91 mm
