AnasSarkiz/tscircuit-ai-agent-remote/imports/SN74LVC1G08DBVR/SN74LVC1G08DBVR.step

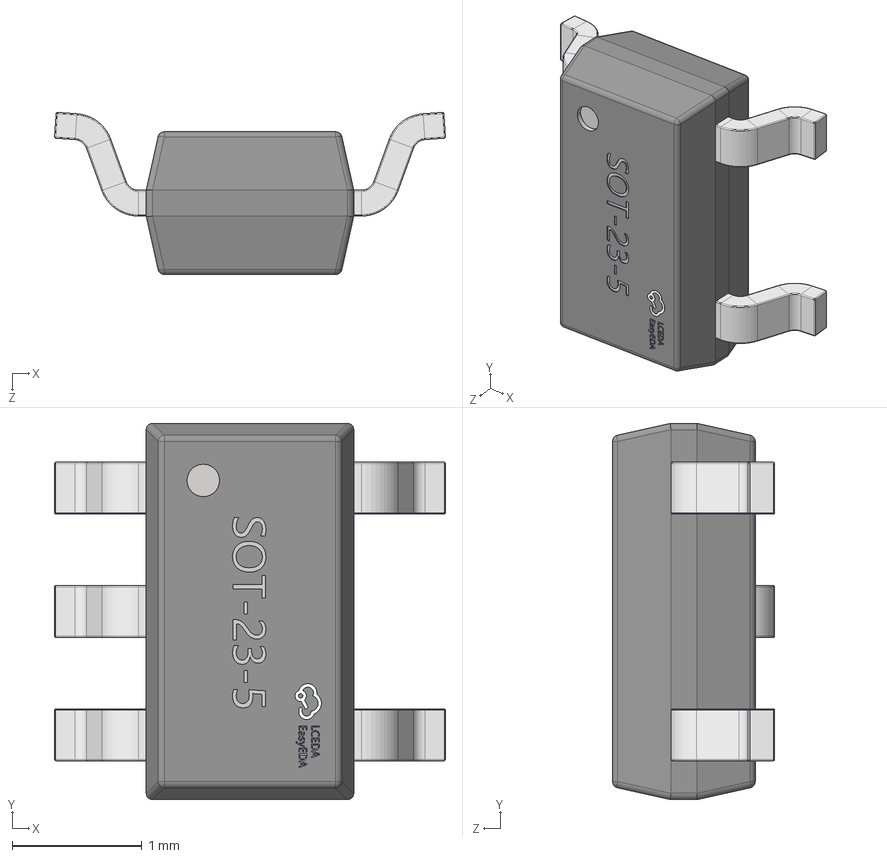
[picture p218: CAD file, 2026-10-02]
imports/SN74LVC1G08DBVR/SN74LVC1G08DBVR.step
3.01 x 2.90 x 1.25 mm
