AnasSarkiz/tscircuit-ai-agent-remote/imports/SN74LVC245APWR/SN74LVC245APWR.step

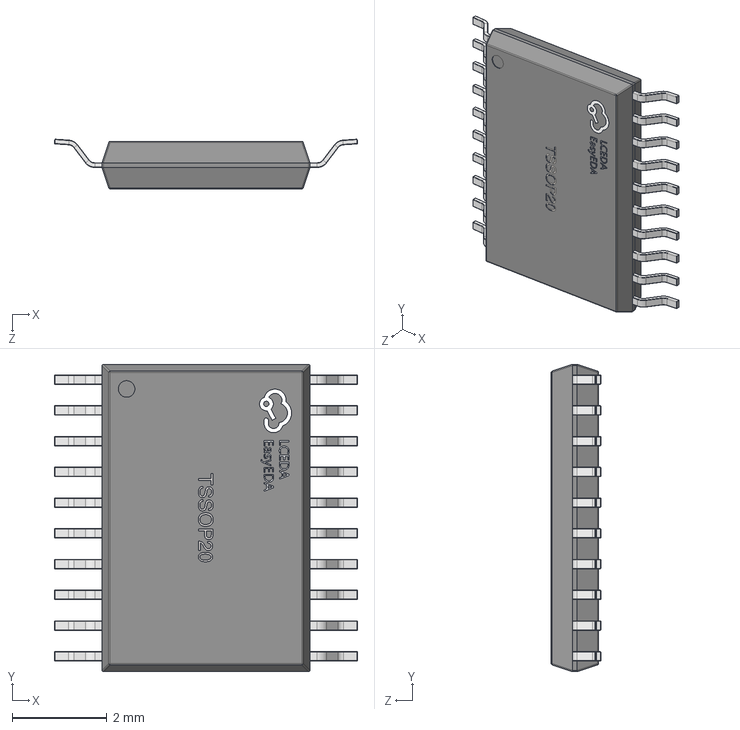
[picture p219: CAD file, 2026-10-03]
imports/SN74LVC245APWR/SN74LVC245APWR.step
6.41 x 6.50 x 1.05 mm
