AnasSarkiz/tscircuit-ai-agent-remote/imports/SN74LVC2G125DCUR/SN74LVC2G125DCUR.step

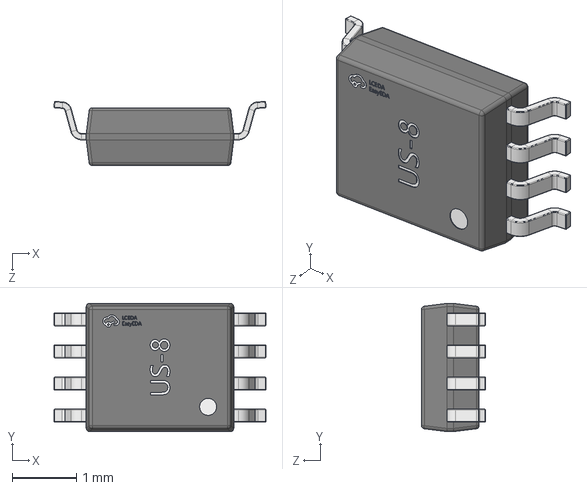
[picture p220: CAD file, 2026-10-02]
imports/SN74LVC2G125DCUR/SN74LVC2G125DCUR.step
3.31 x 2.00 x 1.00 mm
