AnasSarkiz/tscircuit-ai-agent-remote/imports/TPD2EUSB30ADRTR/TPD2EUSB30ADRTR.step

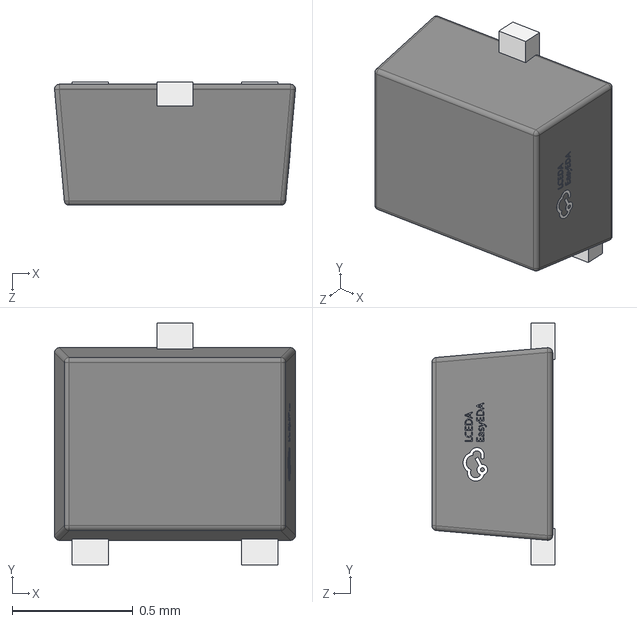
[picture p221: CAD file, 2026-10-03]
imports/TPD2EUSB30ADRTR/TPD2EUSB30ADRTR.step
0.996 x 1.00 x 0.51 mm
