AnasSarkiz/tscircuit-ai-agent-remote/imports/TPS3808G33DBVR/TPS3808G33DBVR.step

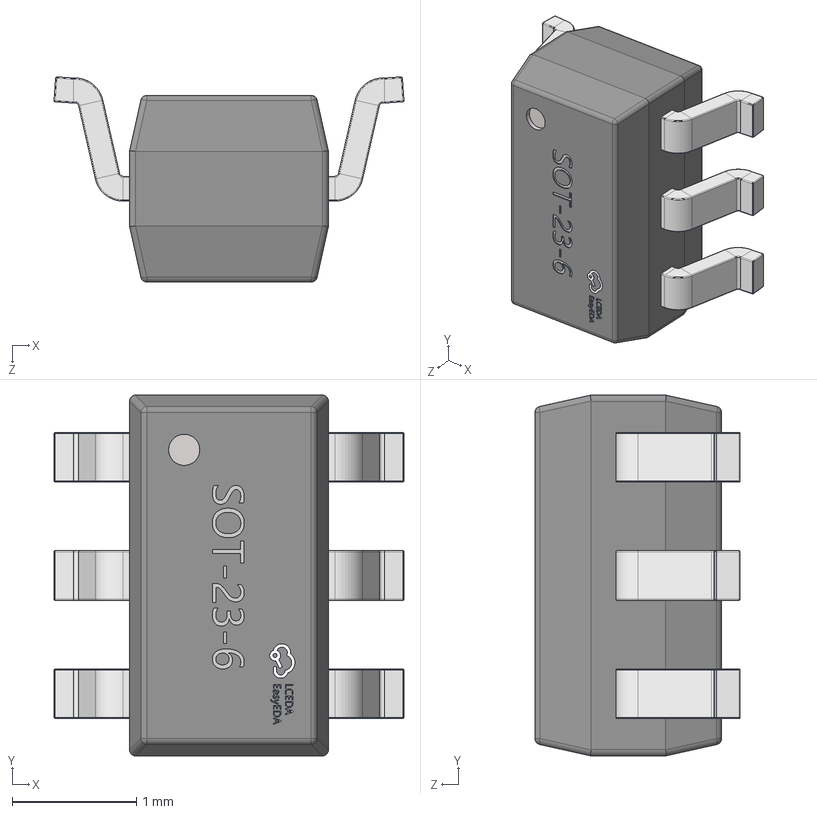
[picture p222: CAD file, 2026-10-03]
imports/TPS3808G33DBVR/TPS3808G33DBVR.step
2.81 x 2.90 x 1.65 mm
