AnasSarkiz/tscircuit-ai-agent-remote/imports/TPS7A2033PDBVR/TPS7A2033PDBVR.step

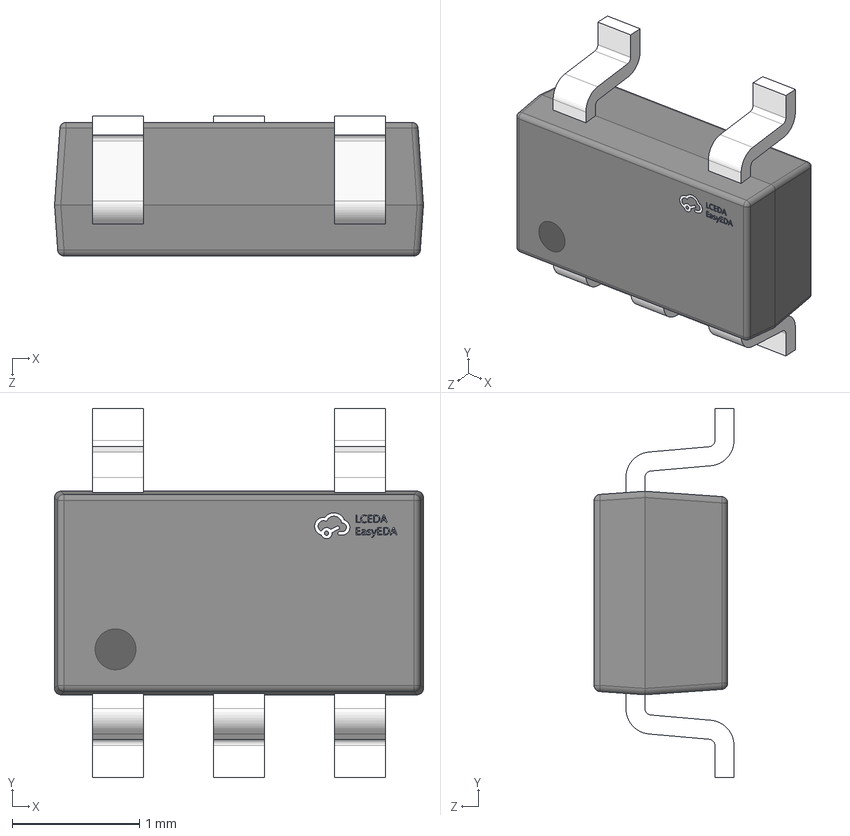
[picture p223: CAD file, 2026-10-03]
imports/TPS7A2033PDBVR/TPS7A2033PDBVR.step
2.90 x 2.90 x 1.10 mm
