AnasSarkiz/tscircuit-ai-agent-remote/imports/TS5A23157DGSR/TS5A23157DGSR.step

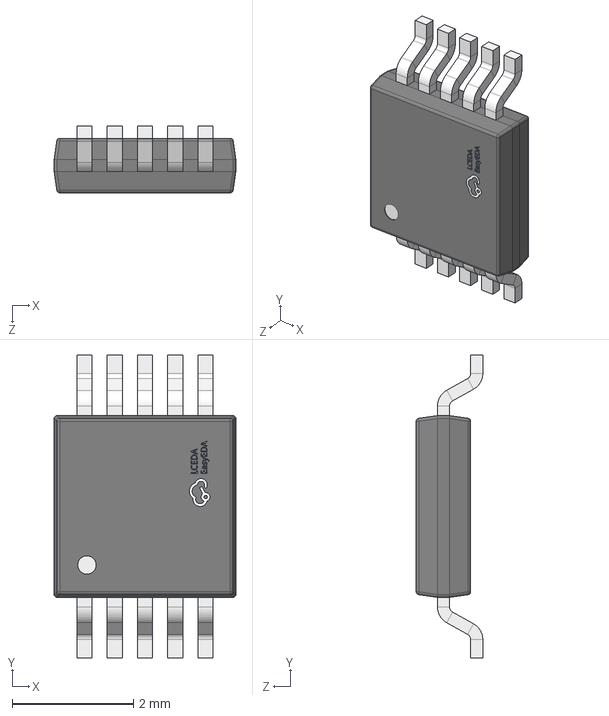
[picture p224: CAD file, 2026-10-03]
imports/TS5A23157DGSR/TS5A23157DGSR.step
3.00 x 5.00 x 1.10 mm
