AnasSarkiz/tscircuit-ai-agent-remote/imports/TUSB320LAIRWBR/TUSB320LAIRWBR.step

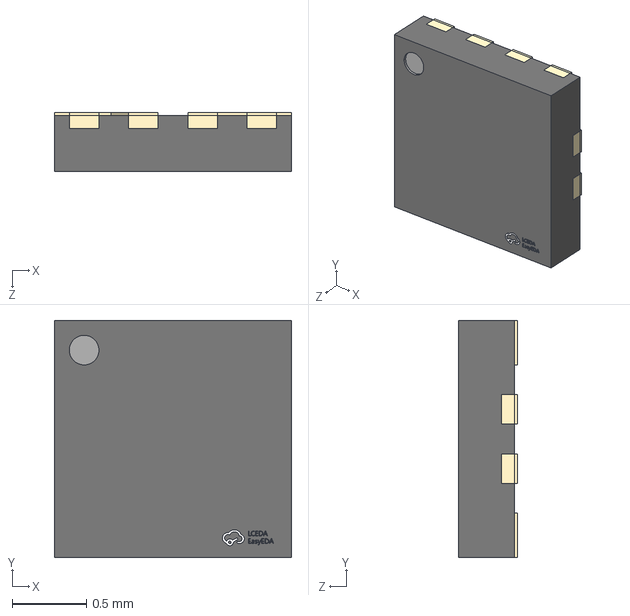
[picture p225: CAD file, 2026-10-03]
imports/TUSB320LAIRWBR/TUSB320LAIRWBR.step
1.60 x 1.60 x 0.401 mm
