AnasSarkiz/tscircuit-ai-agent-remote/evidence/routing-zero-drc-2026-10-07/before/build-checkpoint.json.txt

{
  "native_build": "evidence/connection-repair-2026-10-06/nominal-envelope-native/circuit.json",
  "canonical_circuit_json": "dist/index/circuit.json",
  "byte_identical": true,
  "sha256": "fb2f9c96ff000de1e18d6bf4d35bd41fea2323fc0b10730df4a0262b0bbdb73d",
  "size_bytes": 6947353,
  "traces": 380,
  "vias": 322,
  "native_pours": 269,
  "native_open_port_errors": 53,
  "J7_native_open_port_errors": 46,
  "physically_open_nets": 13,
  "measured_geometry_violations": 0,
  "measured_shorts": 0,
  "authored_region_widths_checked": 245,
  "authored_region_width_failures": 0,
  "all_ordinary_vias_full_span": true,
  "fabrication_ready": false,
  "limitations": [
    "52 native open-port errors and 13 physically open nets remain: 46 J7 contacts, four U27 backlight contacts and two SPEAKER_N contacts. J3 outer polarity is unassigned and omitted from the count.",
    "J7 FPC face, pin-1 and fold/mating orientation remain unqualified.",
    "32 missing U16/U27 pill-pad paste records, 169 strict native-schema failures and unsupported polygon Gerber/official shorts export remain.",
    "Two regulator source routes contain .275 mm sections below their explicit 1 mm requirement; 63 native traces fall below named-net nominal widths. Current/neck and USB/speaker signal-integrity qualification remain open.",
    "Exact dated stock still shows J6/C160405 unavailable; U1/D2/U16 allocation, all supplier rotations, final stackup/fabrication/mechanics and remaining bypass placement remain unqualified.",
    "Standard JST programmer requires the documented three-to-six adapter, separate power and manual BOOT/RESET. No physical prototype, working-hardware, cloud-CI passing or fabrication-ready claim."
  ],
  "routing_selection": "beta_pipeline9",
  "pipeline9_trials_accepted": false,
  "pipeline9_trial_review": "evidence/pipeline9-routing-2026-10-05/review.md",
  "freerouting_new_routes_accepted": false,
  "freerouting_trial_review": "evidence/freerouting-continuation-2026-10-06/review.md",
  "freerouting_native_source_unchanged": true,
  "latest_order_readiness_review": "evidence/connection-repair-2026-10-06/review.md",
  "fresh_order_readiness_render_identical": false,
  "native_traces_width_checked": 380,
  "native_wire_segments_width_checked": 654,
  "native_traces_below_general_0p20_mm": 0,
  "native_traces_below_explicit_source_minimum": 2,
  "native_traces_below_named_net_nominal_requiring_review": 63,
  "current_board_test_pass_count": 48,
  "current_board_test_failure_count": 2,
  "routing_regression_pass_count": 80,
  "latest_programmer_component_placement_review": "evidence/board-programmer-stock-review-2026-10-06/review.md",
  "electrical_decoupling_placement_qualified": false,
  "current_supplier_stock_verified": false,
  "programmer_direct_cable_mating": false,
  "programmer_adapter_review": "evidence/board-programmer-stock-review-2026-10-06/programmer-compatibility.json",
  "programming_hardware_tested": false,
  "latest_accepted_correction": "evidence/connection-repair-2026-10-06/review.md",
  "accepted_source_snapshot": "evidence/connection-repair-2026-10-06/nominal-envelope-native/source-snapshot",
  "source_snapshot_byte_verified": true,
  "local_mcu_100nf_bypass_connected": true,
  "mcu_bulk_nominal_capacitance_f": 2.2e-05,
  "resolved_bom_blank_descriptions": 0,
  "resolved_bom_supplier_codes_as_packages": 0,
  "resolved_bom_receipt": "evidence/connection-repair-2026-10-06/resolved-bom-receipt.json",
  "completed_publication_runtime_cli_build": true,
  "publication_runtime_cli_build_passed": false,
  "publication_runtime_cli_build_seconds": 256.86,
  "publication_runtime_cli_build_error_count": 53,
  "publication_runtime_physical_records_identical": true,
  "publication_runtime_frozen_install_passed": true,
  "publication_runtime_frozen_install_packages": 303,
  "publication_runtime_snapshot_completed": true,
  "publication_runtime_snapshot_passed": false,
  "publication_runtime_snapshot_seconds": 58.59,
  "publication_runtime_snapshot_references_changed": false,
  "publication_runtime_snapshot_receipt": "evidence/connection-repair-2026-10-06/final-source-snapshot-against-baseline.log.outcome.json",
  "public_source_commit": "d2da371641867f83c2a141bbc9f44baeb4f304ec",
  "public_package_version": "0.0.6-wip-connection-repairs",
  "public_package_release_id": "09585856-d339-4615-b86b-b13eeca0115e",
  "public_package_files_verified": 125,
  "public_package_all_bytes_match": true,
  "public_native_preview_exact_object_match": true,
  "public_preview_url": "https://tscircuit.com/AnasSarkiz/tscircuit-ai-agent-remote/releases/09585856-d339-4615-b86b-b13eeca0115e/preview",
  "public_package_cloud_build_id": "a5f966cc-ea8c-4c0e-80b7-a676792340bd",
  "public_package_cloud_CI_passed": false,
  "public_package_cloud_CI_status": "running-at-read-only-observation",
  "public_package_publication_receipt": "evidence/connection-repair-2026-10-06/final-registry-receipt.json",
  "public_package_preview_receipt": "evidence/connection-repair-2026-10-06/final-public-preview-receipt.json",
  "latest_schematic_annotation_review": "evidence/connection-repair-2026-10-06/guide-coverage.json",
  "schematic_original_circuit_sheets": 13,
  "schematic_component_guide_sheets": 13,
  "schematic_component_explanations": 135,
  "schematic_component_coverage_passed": true,
  "prior_order_readiness_physical_geometry_identical": false,
  "publication_runtime_schematic_snapshot_reference_changed": false,
  "publication_runtime_pcb_snapshot_reference_changed": false,
  "source_entry_snapshot_completed": true,
  "source_entry_snapshot_termination": null,
  "source_entry_snapshot_seconds": 61.13,
  "source_entry_snapshot_receipt": "evidence/six-point-board-review-2026-10-06/final-source-snapshot-against-baseline.log.outcome.json",
  "publication_runtime_schematic_snapshot_passed": false,
  "publication_runtime_pcb_snapshot_passed": false,
  "public_package_cloud_CI_observation_receipt": "evidence/six-point-board-review-2026-10-06/cloud-build-observation.json",
  "public_package_cloud_CI_started_at": "2026-10-06T17:55:43.520Z",
  "latest_six_point_review": "evidence/six-point-board-review-2026-10-06/review.md",
  "via_drill_mm": 0.3,
  "via_pad_mm": 0.45,
  "blind_buried_vias": false,
  "high_current_trunks_outer_only": true,
  "high_current_native_traces_checked": 59,
  "high_current_regions_checked": 80,
  "previously_connected_port_pairs_preserved": 8146,
  "all_125_purchased_geometry_unchanged": true,
  "supplier_exact_identities_checked": 43,
  "supplier_total_stock_covers_identities": 42,
  "supplier_out_of_stock": [
    "J6/C160405"
  ],
  "supplier_assembly_availability_qualified": false,
  "supplier_stock_receipt": "evidence/six-point-board-review-2026-10-06/official-stock/receipt.json",
  "supplier_stock_interpretation": "evidence/six-point-board-review-2026-10-06/inventory-interpretation.json",
  "cli_schematic_style_issues": 0,
  "ui_schematic_style_passed": false,
  "ui_schematic_style_blocker": "Actual viewer action failed to fetch CDN analysis module: browser proxy certificate / network policy.",
  "current_local_version": "0.0.5-wip-style-vias-power",
  "public_fields_describe_parent_until_new_publication_verified": false,
  "source_entry_snapshot_passed": false,
  "final_visual_review": "evidence/six-point-board-review-2026-10-06/final-visual-review.json",
  "schematic_component_coverage_receipt": "evidence/six-point-board-review-2026-10-06/final-guide-coverage.json",
  "supplier_current_identity_binding_receipt": "evidence/six-point-board-review-2026-10-06/final-stock-application.json",
  "current_publication_source_matches_checked_runtime": true,
  "public_package_ready_to_build": true,
  "public_package_is_private": false,
  "public_package_is_unlisted": false,
  "previous_publication_cloud_CI_status": "completed-failed",
  "previous_publication_cloud_CI_observation_receipt": "evidence/six-point-board-review-2026-10-06/parent-cloud-build-observation.json",
  "pending_public_version": null,
  "previously_connected_pairs_preserved": 8152,
  "newly_connected_numbered_terminal_pairs": 1690,
  "remaining_native_error_receipt": "evidence/connection-repair-2026-10-06/remaining-native-errors.json",
  "latest_actual_srj": "evidence/connection-repair-2026-10-06/final-native.srj.json",
  "new_connection_regions_checked": 97,
  "new_supply_speaker_regions_checked": 21,
  "new_supply_inner_gain_input_current_qualified": false,
  "source_checks_passed": true,
  "current_native_component_inventory": "evidence/connection-repair-2026-10-06/component-summary.json",
  "dated_stock_identity_binding": "evidence/connection-repair-2026-10-06/dated-stock-application.json",
  "latest_programmer_contact_review": "evidence/connection-repair-2026-10-06/programmer-and-microphone-contact-checks.json",
  "public_github_publication_receipt": "evidence/connection-repair-2026-10-06/github-publication-receipt.json",
  "cloud_setup_receipt": "evidence/connection-repair-2026-10-06/cloud-setup-receipt.json"
}
