AnasSarkiz/tscircuit-ai-agent-remote/evidence/connection-repair-2026-10-06/power-control-manual-native/source-snapshot/src/board/connection-copper.json.txt

{
  "classification": "Authored native connection repairs and low-current signal relocation; not autorouter caches",
  "paths": [
    {
      "net": "MCU_LCD_RESET_N",
      "from": ".U14 > .pin3",
      "to": "net.MCU_LCD_RESET_N",
      "width": 0.2,
      "pcbPath": [
        {
          "x": -1.625,
          "y": -4.67095
        },
        {
          "x": -1.625,
          "y": -4.67095,
          "via": true,
          "fromLayer": "top",
          "toLayer": "bottom"
        }
      ],
      "global_path_mm": [[7.375, 5.12905], [7.375, 3.32905]],
      "segment_layers": ["top", "top"],
      "classification": "manual native ordinary via escape; power current qualification pending",
      "top_length_mm": 1.8000000000000003,
      "via_outer_mm": 0.45,
      "via_hole_mm": 0.3
    },
    {
      "net": "MIC_SD",
      "from": ".U5 > .pin6",
      "to": "net.MIC_SD",
      "width": 0.2,
      "pcbPath": [
        {
          "x": -2.692826,
          "y": -0.800127
        },
        {
          "x": -2.692826,
          "y": -0.800127,
          "via": true,
          "fromLayer": "top",
          "toLayer": "bottom"
        }
      ],
      "global_path_mm": [[19.1928144, -29.000127], [17.807174, -29.800127]],
      "segment_layers": ["top", "top"],
      "classification": "manual native ordinary via escape; power current qualification pending",
      "top_length_mm": 1.599999786910036,
      "via_outer_mm": 0.45,
      "via_hole_mm": 0.3
    },
    {
      "net": "MIC_BCLK",
      "from": ".R92 > .pin2",
      "to": "net.MIC_BCLK",
      "width": 0.2,
      "pcbPath": [
        {
          "x": 0.75335,
          "y": -0.8
        },
        {
          "x": 0.75335,
          "y": -0.8,
          "via": true,
          "fromLayer": "top",
          "toLayer": "bottom"
        }
      ],
      "global_path_mm": [[15.75335, -29.75], [15.75335, -30.55]],
      "segment_layers": ["top", "top"],
      "classification": "manual native ordinary via escape; power current qualification pending",
      "top_length_mm": 0.8000000000000007,
      "via_outer_mm": 0.45,
      "via_hole_mm": 0.3
    },
    {
      "net": "GND",
      "from": ".R41 > .pin2",
      "to": "net.GND",
      "width": 0.3,
      "pcbPath": [
        {
          "x": 0.35,
          "y": 0.9
        },
        {
          "x": 0.35,
          "y": 0.9,
          "via": true,
          "fromLayer": "top",
          "toLayer": "bottom"
        }
      ],
      "global_path_mm": [[14.50335, -5], [14.100000000000549, -4.0999999999996035]],
      "segment_layers": ["top", "top"],
      "classification": "manual native GND via escape",
      "top_length_mm": 0.9862510950565635,
      "via_outer_mm": 0.45,
      "via_hole_mm": 0.3
    },
    {
      "net": "GND",
      "from": ".R69 > .pin2",
      "to": "net.GND",
      "width": 0.3,
      "pcbPath": [
        {
          "x": 2.9,
          "y": -1.1
        },
        {
          "x": 2.9,
          "y": -1.1,
          "via": true,
          "fromLayer": "top",
          "toLayer": "bottom"
        }
      ],
      "global_path_mm": [[-12.753364, 7.5], [-14.899999999999864, 8.600000000000577]],
      "segment_layers": ["top", "top"],
      "classification": "manual native GND via escape",
      "top_length_mm": 2.412062626984773,
      "via_outer_mm": 0.45,
      "via_hole_mm": 0.3
    },
    {
      "net": "GND",
      "from": ".C70 > .pin2",
      "to": "net.GND",
      "width": 0.3,
      "pcbPath": [
        {
          "x": -0.25,
          "y": -0.9
        },
        {
          "x": -1.75,
          "y": -1.2
        },
        {
          "x": -3.85,
          "y": -1.5
        },
        {
          "x": -3.85,
          "y": -1.5,
          "via": true,
          "fromLayer": "top",
          "toLayer": "bottom"
        }
      ],
      "global_path_mm": [
        [16.5, -3.049976],
        [17.400000000000595, -3.999999999999602],
        [17.7000000000006, -5.499999999999623],
        [18.000000000000604, -7.599999999999653]
      ],
      "segment_layers": ["top", "top", "top", "top"],
      "classification": "manual native GND via escape",
      "top_length_mm": 4.959668853436398,
      "via_outer_mm": 0.45,
      "via_hole_mm": 0.3
    },
    {
      "net": "LCD_DC",
      "from": ".U14 > .pin16",
      "to": "net.LCD_DC",
      "width": 0.2,
      "pcbPath": [
        {
          "x": -0.15,
          "y": 3.95
        },
        {
          "x": 0.15,
          "y": 4.1
        },
        {
          "x": 1.15,
          "y": 4.2
        },
        {
          "x": 1.55,
          "y": 4.6
        },
        {
          "x": 1.55,
          "y": 4.6,
          "via": true,
          "fromLayer": "top",
          "toLayer": "bottom"
        }
      ],
      "global_path_mm": [
        [8.675, 10.87095],
        [8.850000000000477, 11.950000000000628],
        [9.150000000000475, 12.100000000000627],
        [10.150000000000489, 12.200000000000628],
        [10.550000000000495, 12.600000000000634]
      ],
      "segment_layers": ["top", "top", "top", "top", "top"],
      "classification": "manual native ordinary via escape; power current qualification pending",
      "top_length_mm": 2.9992318023569515,
      "via_outer_mm": 0.45,
      "via_hole_mm": 0.3
    },
    {
      "net": "LCD_DC",
      "from": ".R44 > .pin1",
      "to": "net.LCD_DC",
      "width": 0.2,
      "pcbPath": [
        {
          "x": -0.753364,
          "y": 1.8
        },
        {
          "x": -0.753364,
          "y": 1.8,
          "via": true,
          "fromLayer": "top",
          "toLayer": "bottom"
        }
      ],
      "global_path_mm": [[12.996636, -3.25], [12.996636, -1.45]],
      "segment_layers": ["top", "top"],
      "classification": "manual native ordinary via escape; power current qualification pending",
      "top_length_mm": 1.8,
      "via_outer_mm": 0.45,
      "via_hole_mm": 0.3
    },
    {
      "net": "MIC_BCLK_INPUT",
      "from": ".U24 > .pin1",
      "to": "net.MIC_BCLK_INPUT",
      "width": 0.2,
      "pcbPath": [
        {
          "x": 2.0999,
          "y": -0.65
        },
        {
          "x": 2.0999,
          "y": -0.65,
          "via": true,
          "fromLayer": "top",
          "toLayer": "bottom"
        }
      ],
      "global_path_mm": [[15.8999, -26.65], [17.0999, -26.65]],
      "segment_layers": ["top", "top"],
      "classification": "manual native ordinary via escape; power current qualification pending",
      "top_length_mm": 1.200000000000001,
      "via_outer_mm": 0.45,
      "via_hole_mm": 0.3
    },
    {
      "net": "MIC_BCLK_INPUT",
      "from": ".R88 > .pin2",
      "to": "net.MIC_BCLK_INPUT",
      "width": 0.2,
      "pcbPath": [
        {
          "x": 1.75,
          "y": -0.75
        },
        {
          "x": 2.95,
          "y": -0.75
        },
        {
          "x": 2.95,
          "y": -0.75,
          "via": true,
          "fromLayer": "top",
          "toLayer": "bottom"
        }
      ],
      "global_path_mm": [
        [14.503364, -28.25],
        [15.500000000000568, -28.999999999999957],
        [16.700000000000585, -28.999999999999957]
      ],
      "segment_layers": ["top", "top", "top"],
      "classification": "manual native ordinary via escape; power current qualification pending",
      "top_length_mm": 2.4473104330907813,
      "via_outer_mm": 0.45,
      "via_hole_mm": 0.3
    },
    {
      "net": "MIC_BCLK_INPUT",
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
      "x": 11.800000000000516,
      "y": -16.54999999999978,
      "outer_mm": 0.45,
      "hole_mm": 0.3
    },
    {
      "net": "AMP_SD_MODE",
      "x": 3.3500000000003958,
      "y": -16.59999999999978,
      "outer_mm": 0.45,
      "hole_mm": 0.3
    }
  ],
  "repaired_islands": [
    {
      "net": "MCU_LCD_RESET_N",
      "ports": [".U14 > .pin3"]
    },
    {
      "net": "MIC_SD",
      "ports": [".U5 > .pin6"]
    },
    {
      "net": "MIC_BCLK",
      "ports": [".R92 > .pin2"]
    },
    {
      "net": "GND",
      "ports": [".R41 > .pin2", ".R44 > .pin2", ".C73 > .pin2"]
    },
    {
      "net": "GND",
      "ports": [".C50 > .pin2", ".R69 > .pin2"]
    },
    {
      "net": "GND",
      "ports": [".U22 > .pin2", ".C70 > .pin2"]
    },
    {
      "net": "LCD_DC",
      "ports": [".R44 > .pin1"]
    },
    {
      "net": "AUDIO_ENABLE_SUPPLY",
      "ports": [".R63 > .pin1"]
    },
    {
      "net": "VMIC",
      "ports": [".U24 > .pin5"]
    },
    {
      "net": "VMIC",
      "ports": [".R93 > .pin1"]
    },
    {
      "net": "VMIC",
      "ports": [".U5 > .pin2"]
    },
    {
      "net": "VMIC",
      "ports": [".U5 > .pin5"]
    },
    {
      "net": "MIC_WS",
      "ports": [".R93 > .pin2"]
    },
    {
      "net": "MIC_BCLK",
      "ports": [".U5 > .pin4"]
    },
    {
      "net": "AMP_SD_MODE",
      "ports": [".U3 > .pin4"]
    },
    {
      "net": "VSYS",
      "ports": [".U16 > .pin10"]
    },
    {
      "net": "VSYS",
      "ports": [".U16 > .pin11"]
    },
    {
      "net": "VSYS",
      "ports": [".U3 > .pin2"]
    }
  ],
  "retired_manual_path_indices": [42, 43, 47, 48],
  "retired_replay_connections": [
    {
      "phase_index": 5,
      "connection": ".R68 > port.pin1",
      "original_pcb_trace_id": "saved_phase_null_5_1"
    },
    {
      "phase_index": 5,
      "connection": ".R65 > port.pin2",
      "original_pcb_trace_id": "saved_phase_null_5_0"
    }
  ],
  "retired_inner_escapes": [
    {
      "source_name": "MANUAL_INNER_ESCAPE_38_0",
      "original_path_index": 38,
      "escape_index": 0,
      "original_pcb_trace_id": "pcb_trace_283",
      "retired_via_id": "pcb_via_195"
    }
  ],
  "pad_necks": [
    {
      "net": "VSYS",
      "terminal": ".U16 > .pin10",
      "width_mm": 0.275,
      "length_mm": 4.305880293452751,
      "nominal_trunk_width_mm": 1,
      "layer": "top",
      "status": "Measured layout proposal; current/stackup/thermal qualification pending"
    },
    {
      "net": "VSYS",
      "terminal": ".U16 > .pin11",
      "width_mm": 0.275,
      "length_mm": 4.510893847629043,
      "nominal_trunk_width_mm": 1,
      "layer": "top",
      "status": "Measured layout proposal; current/stackup/thermal qualification pending"
    }
  ],
  "branch_requirements": [
    {
      "net": "VSYS",
      "terminal": ".U3 > .pin2",
      "nominal_width_mm": 0.2,
      "layers": ["inner2", "inner1"],
      "maximum_dc_current_a": null,
      "basis": "MAX98357A pin2 GAIN_SLOT is a gain-mode input; PVDD pins7/8 carry amplifier supply current separately. Exact gain-input current/width qualification remains blocked; the fresh official ADI datasheet request is policy-denied."
    }
  ]
}
