AnasSarkiz/tscircuit-ai-agent-remote/evidence/board-corrections-2026-10-06/capacitor-native/source-snapshot/src/board/manual-power-copper.json.txt

{
  "classification": "manual native copper regions and ordinary through vias; not solver caches",
  "source_circuit_json": "evidence/cloud-runs/power-first-base/circuit.json",
  "pours": [
    {
      "net": "VSYS",
      "layer": "inner2",
      "outline": [
        {
          "x": -2.750612,
          "y": -14.169727
        },
        {
          "x": -1.749388,
          "y": -14.130321
        },
        {
          "x": -1.383363,
          "y": -23.430321
        },
        {
          "x": -2.384587,
          "y": -23.469727
        }
      ],
      "nominal_width_mm": 1,
      "path_mm": [[-1.883975, -23.450024], [-2.25, -14.150024]],
      "classification": "manual native power copper region; current qualification pending",
      "drawn_width_mm": 1.002
    },
    {
      "net": "VSYS",
      "layer": "bottom",
      "outline": [
        {
          "x": -3.548658,
          "y": -11.164564
        },
        {
          "x": -5.46133,
          "y": -9.342971
        },
        {
          "x": -8.050427,
          "y": -8.52792
        },
        {
          "x": -7.749553,
          "y": -7.57216
        },
        {
          "x": -4.93867,
          "y": -8.457029
        },
        {
          "x": -2.651342,
          "y": -10.635436
        },
        {
          "x": -1.765303,
          "y": -14.023258
        },
        {
          "x": -2.734697,
          "y": -14.27679
        }
      ],
      "nominal_width_mm": 1,
      "path_mm": [
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
      "net": "LCD_CS_N",
      "x": 21.6,
      "y": 4.0,
      "hole_mm": 0.3,
      "outer_mm": 0.7,
      "classification": "manual native through via between power regions"
    },
    {
      "net": "LCD_CS_N",
      "x": 20.9,
      "y": -9.2,
      "hole_mm": 0.3,
      "outer_mm": 0.7,
      "classification": "manual native through via between power regions"
    }
  ]
}
