AnasSarkiz/tscircuit-ai-agent-remote/evidence/core-pill-paste-fix-2026-10-07/coupon-source/build-coupon.tsx.txt

import { buildPasteCoupon } from "./lib/build-paste-coupon"

await buildPasteCoupon()
