AnasSarkiz/tscircuit-ai-agent-remote/evidence/programmer-direct-uart-2026-10-07/before/manual-power-copper.json.txt

{
  "classification": "authored outer-layer high-current replacement; requires native replay and audit",
  "source_circuit_json": "evidence/six-point-board-review-2026-10-06/via-baseline-native/circuit.json",
  "pours": [
    {
      "net": "PACK_BAT",
      "nominal_width_mm": 1,
      "path_mm": [
        [-8.8, -28.5],
        [-13.19999999999984, -24.9999999999999],
        [-14.299999999999855, -25.099999999999902],
        [-15.549976, -25.383975]
      ],
      "layer": "bottom",
      "outline": [
        {
          "x": -13.354685,
          "y": -25.517128
        },
        {
          "x": -14.22148,
          "y": -25.595928
        },
        {
          "x": -15.438985,
          "y": -25.872526
        },
        {
          "x": -15.660967,
          "y": -24.895424
        },
        {
          "x": -14.410991,
          "y": -24.611449
        },
        {
          "x": -14.397984,
          "y": -24.608675
        },
        {
          "x": -14.384908,
          "y": -24.606247
        },
        {
          "x": -14.371772,
          "y": -24.604168
        },
        {
          "x": -14.358586,
          "y": -24.602437
        },
        {
          "x": -14.345358,
          "y": -24.601058
        },
        {
          "x": -13.245358,
          "y": -24.501058
        },
        {
          "x": -13.233072,
          "y": -24.500093
        },
        {
          "x": -13.220765,
          "y": -24.49943
        },
        {
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
          "y": -10.194484
        },
        {
          "x": -20.089295,
          "y": -10.184643
        },
        {
          "x": -20.081281,
          "y": -10.174999
        },
        {
          "x": -20.073028,
          "y": -10.165559
        },
        {
          "x": -20.064542,
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
