AnasSarkiz/tscircuit-ai-agent-remote/evidence/fabrication-rule-review-2026-10-03/calculator.jpg

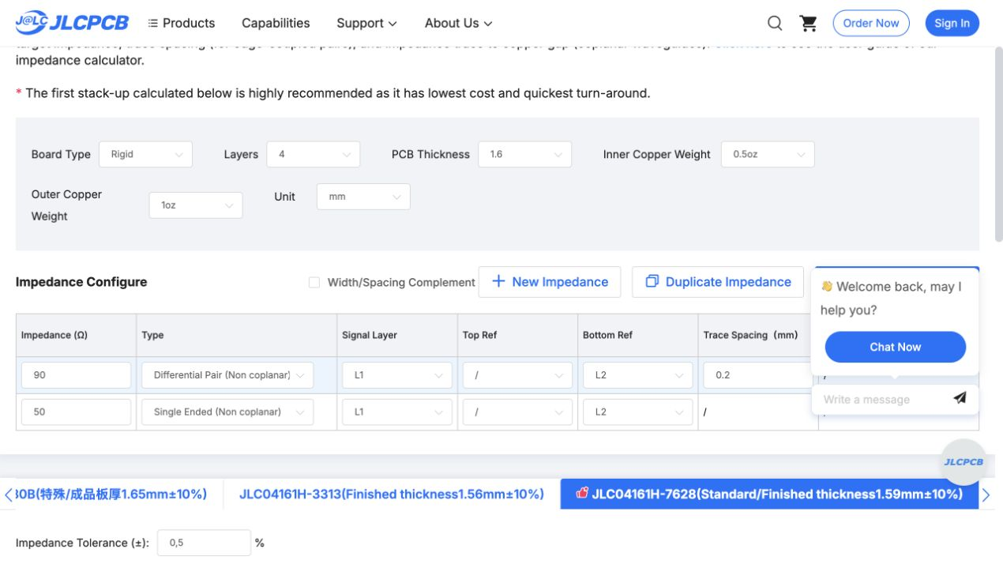
evidence/fabrication-rule-review-2026-10-03/calculator.jpg
