AnasSarkiz/tscircuit-ai-agent-remote/evidence/hold-readback-review-2026-10-03/manufacturer-pin-page.png

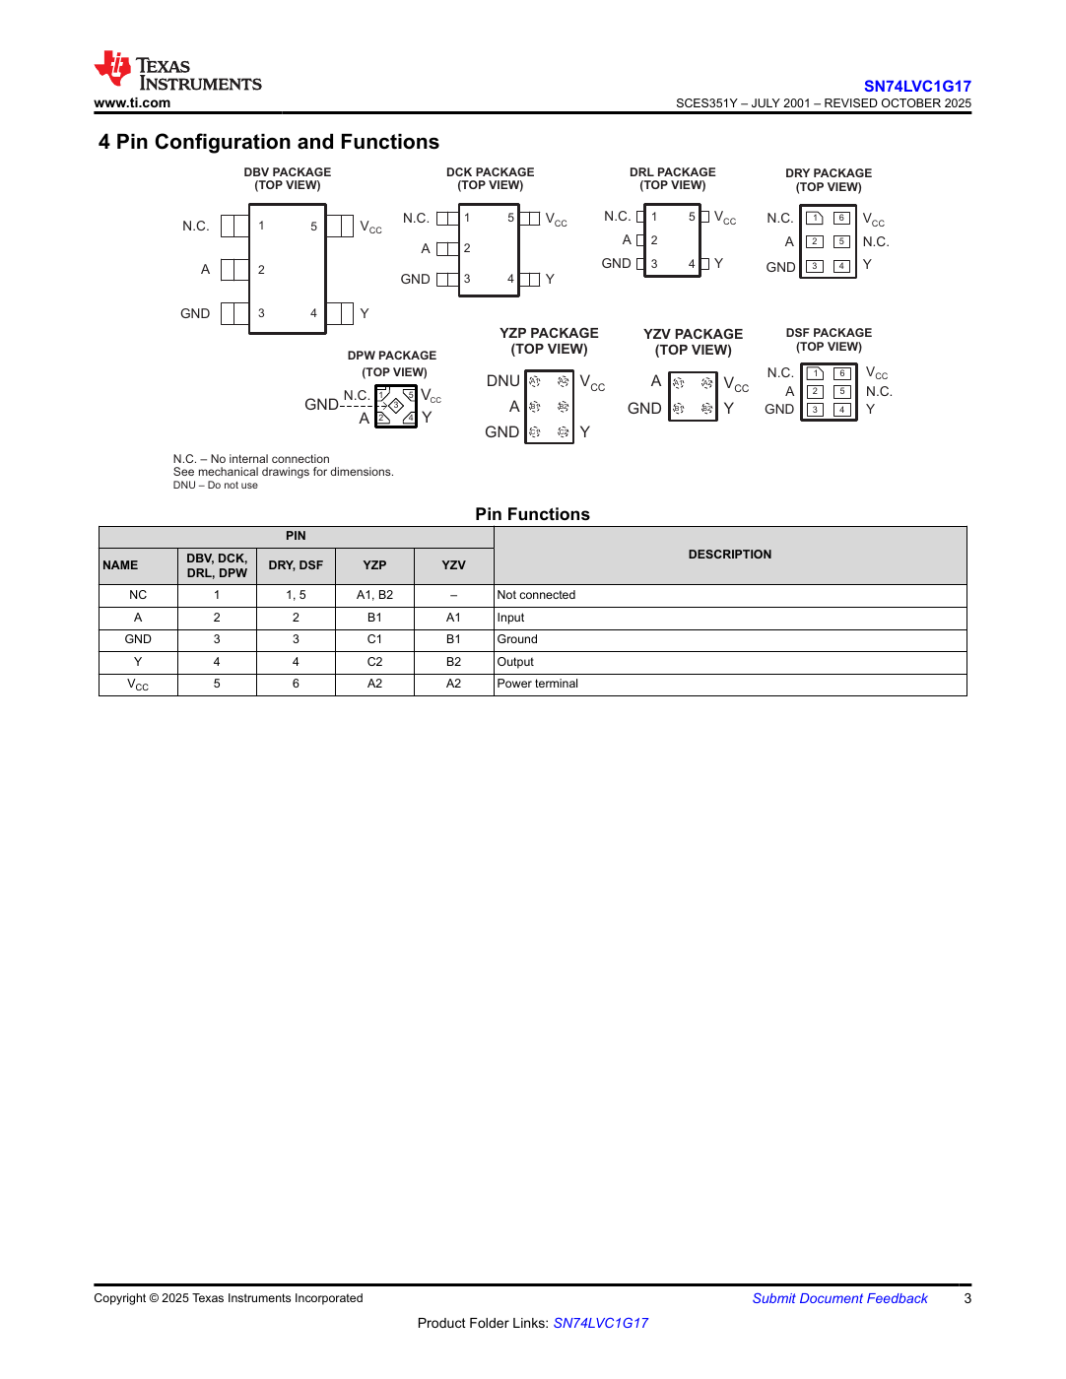
evidence/hold-readback-review-2026-10-03/manufacturer-pin-page.png
