AnasSarkiz/tscircuit-ai-agent-remote/evidence/microphone-local-bypass-2026-10-08/schematics/14-component-guide-mcu-usb-review.png

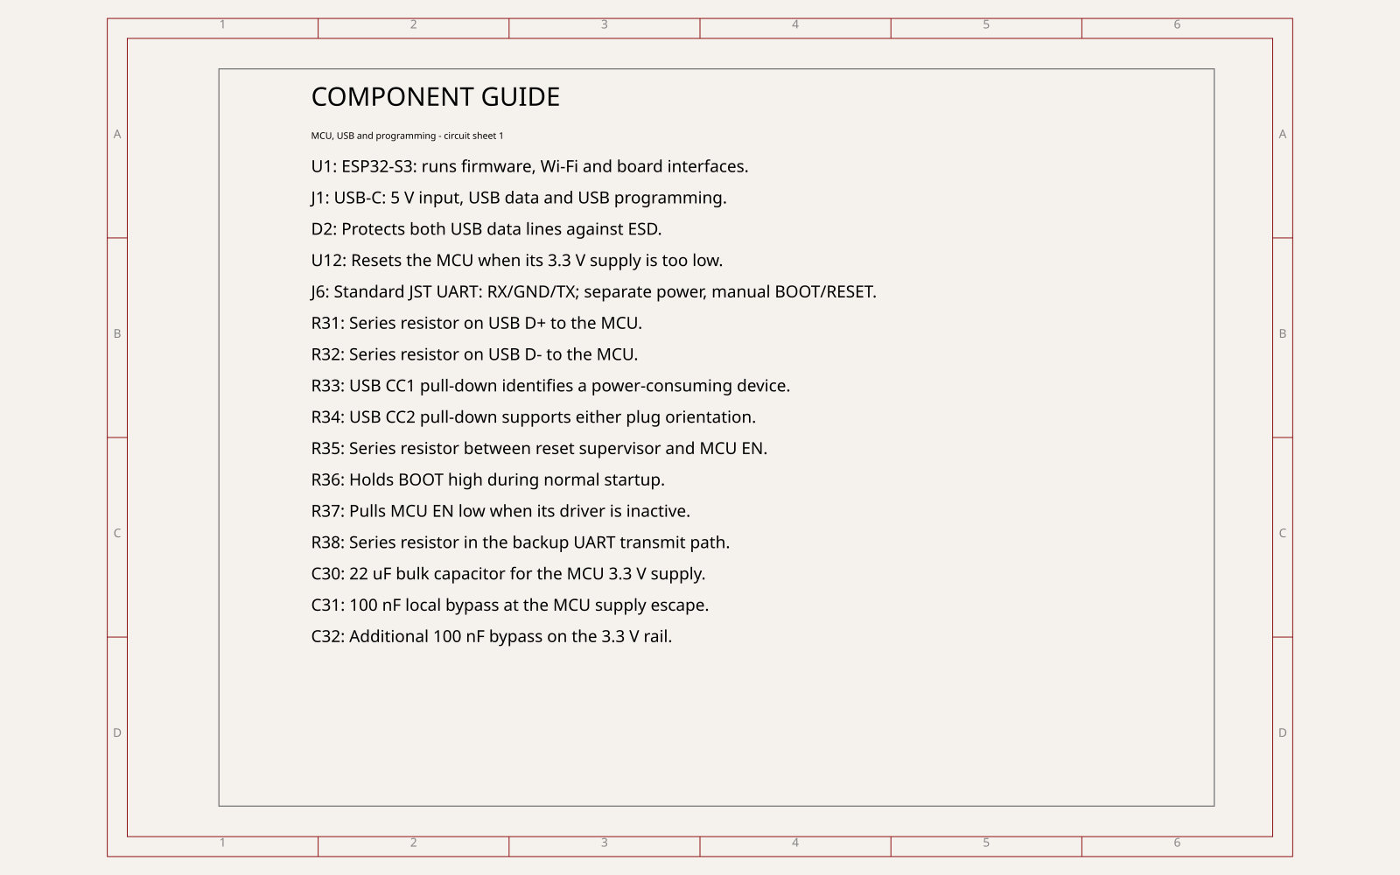
evidence/microphone-local-bypass-2026-10-08/schematics/14-component-guide-mcu-usb-review.png
