AnasSarkiz/tscircuit-ai-agent-remote/evidence/microphone-local-bypass-2026-10-08/schematics/15-component-guide-ChargerSheet.png

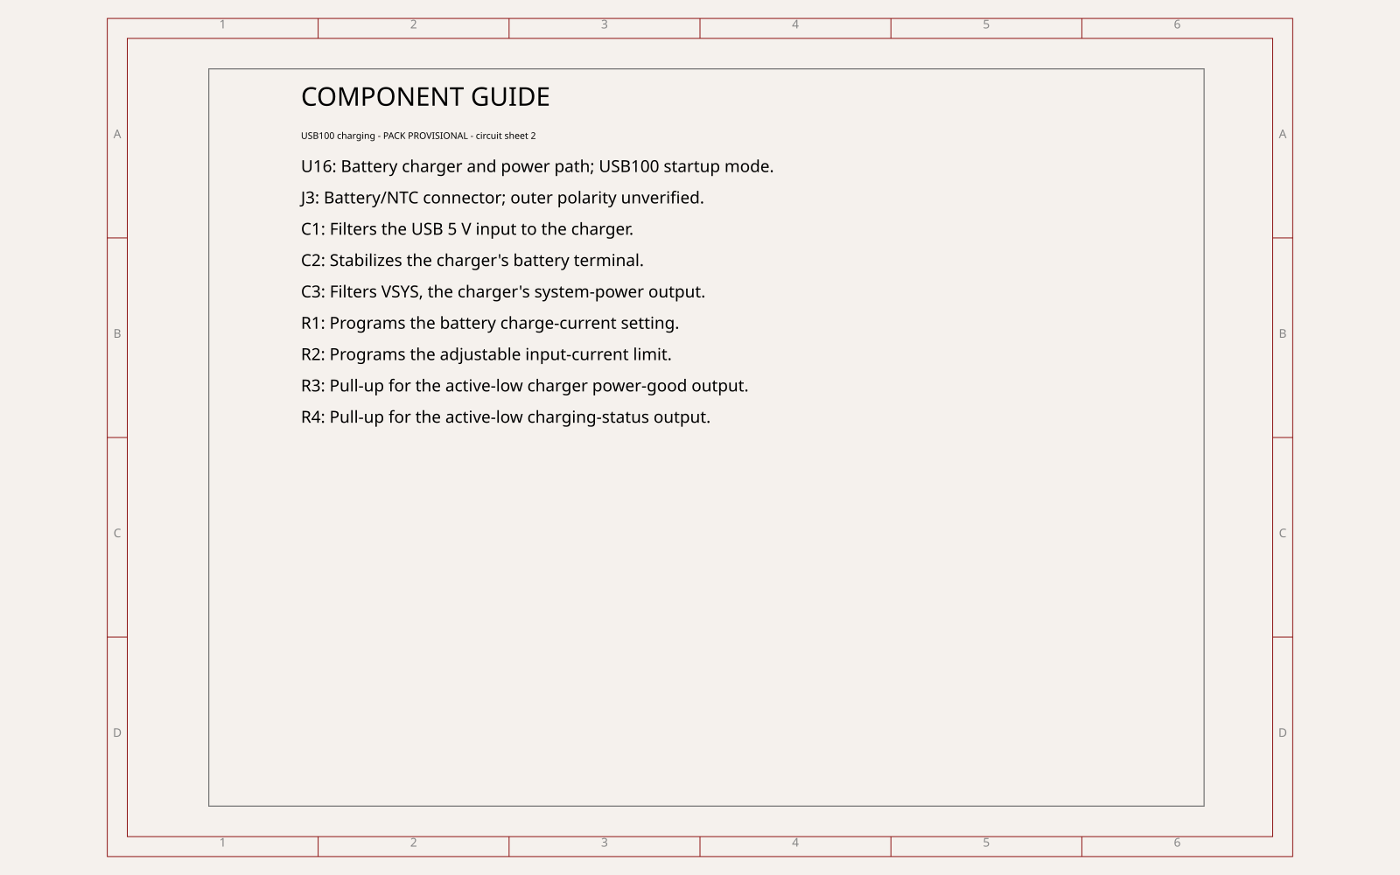
evidence/microphone-local-bypass-2026-10-08/schematics/15-component-guide-ChargerSheet.png
