AnasSarkiz/tscircuit-ai-agent-remote/evidence/microphone-local-bypass-2026-10-08/schematics/17-component-guide-display-logic-review.png

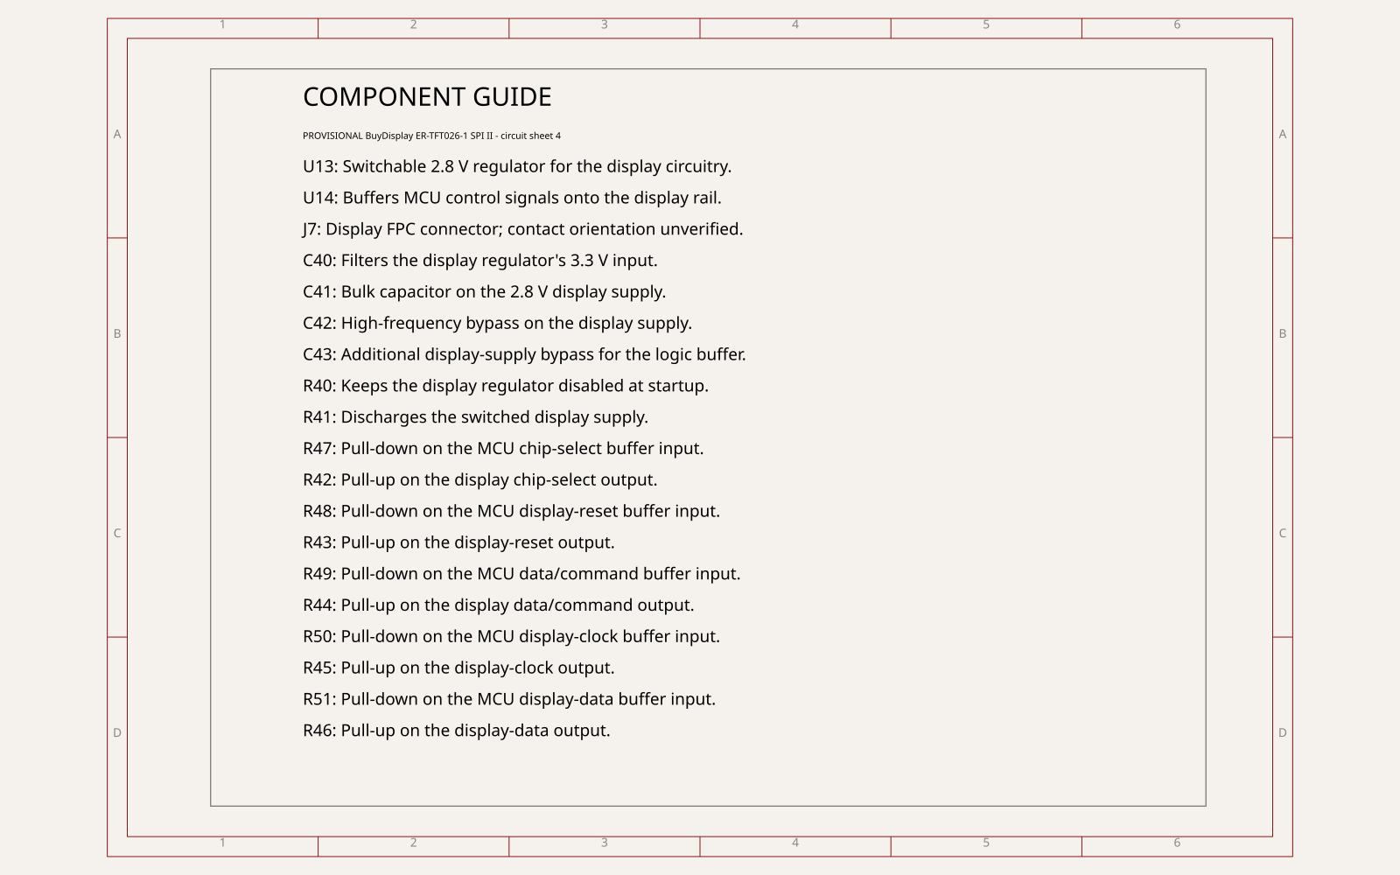
evidence/microphone-local-bypass-2026-10-08/schematics/17-component-guide-display-logic-review.png
