AnasSarkiz/tscircuit-ai-agent-remote/evidence/microphone-local-bypass-2026-10-08/schematics/24-component-guide-ControlsSheet.png

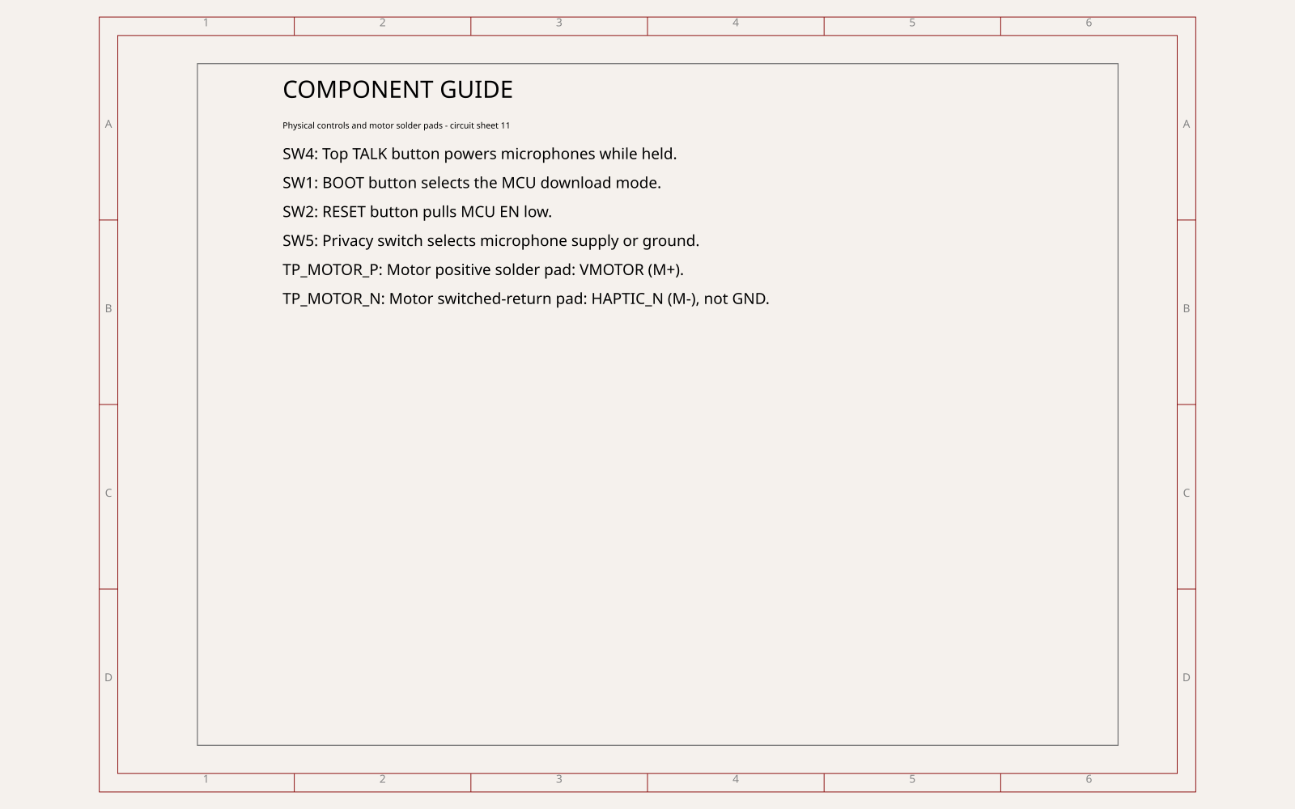
evidence/microphone-local-bypass-2026-10-08/schematics/24-component-guide-ControlsSheet.png
