AnasSarkiz/tscircuit-ai-agent-remote/evidence/pcb-completion-2026-10-08/NOT-FOR-FABRICATION-qualified-gerbers/F_Cu.png

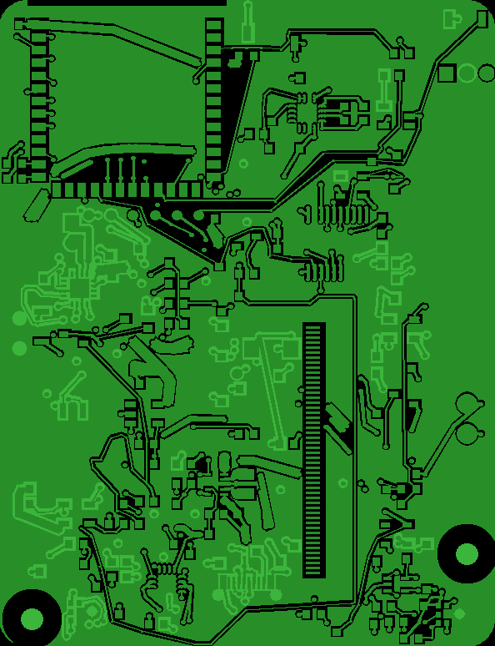
evidence/pcb-completion-2026-10-08/NOT-FOR-FABRICATION-qualified-gerbers/F_Cu.png
