AnasSarkiz/tscircuit-ai-agent-remote/evidence/schematic-component-notes-2026-10-06/final-views/guide-overview-2.png

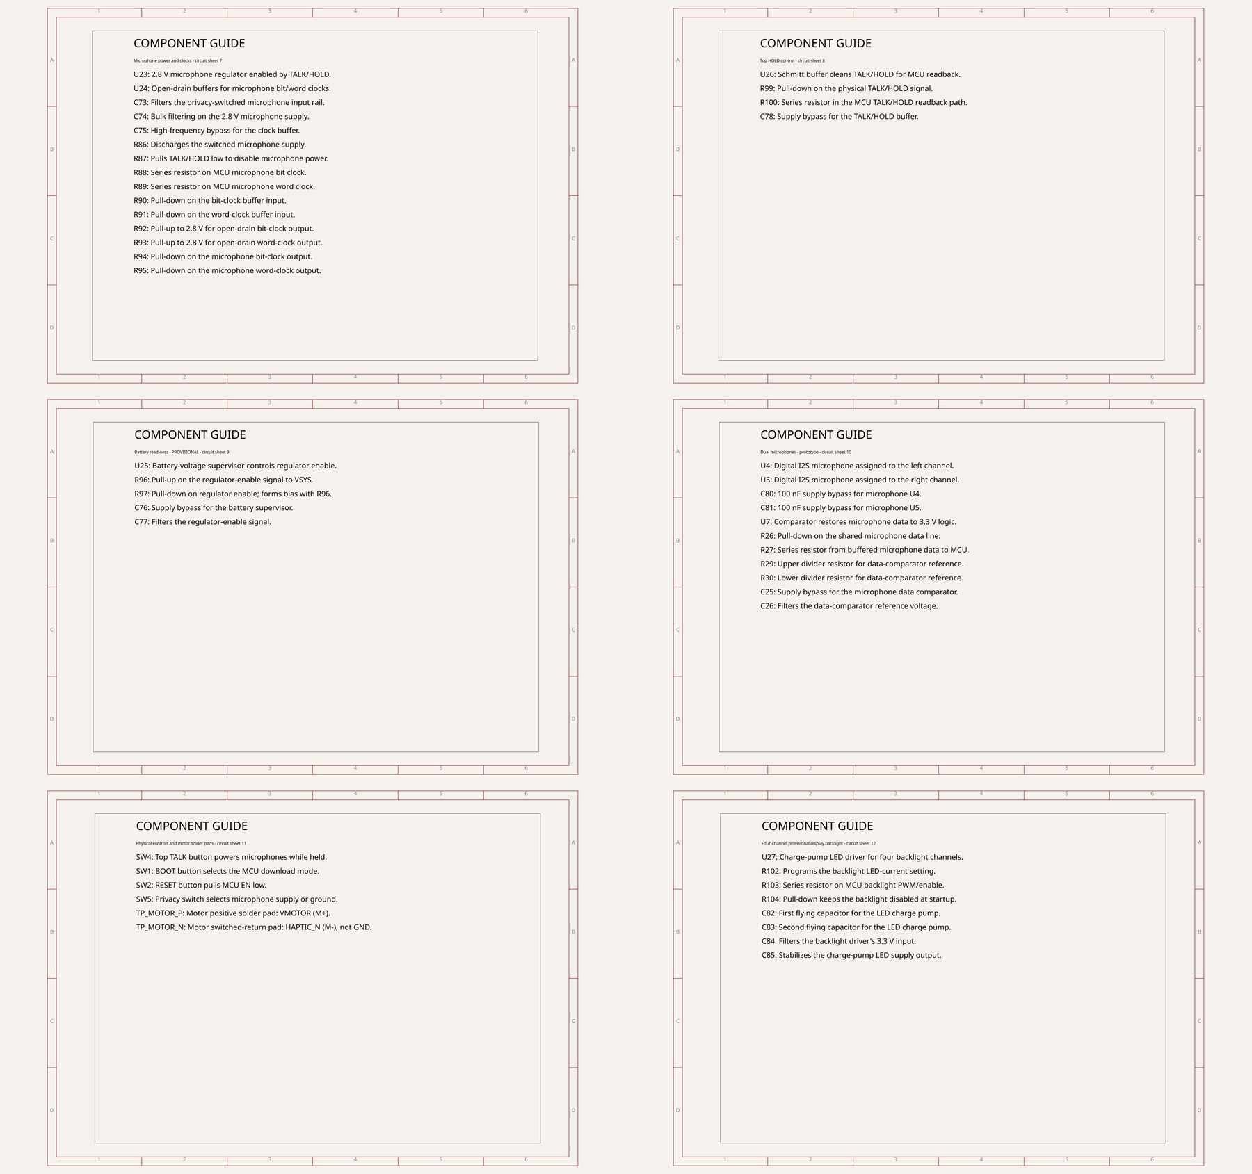
evidence/schematic-component-notes-2026-10-06/final-views/guide-overview-2.png
