AnasSarkiz/tscircuit-ai-agent-remote/evidence/six-point-board-review-2026-10-06/final-schematics/guides-21-26-contact.png

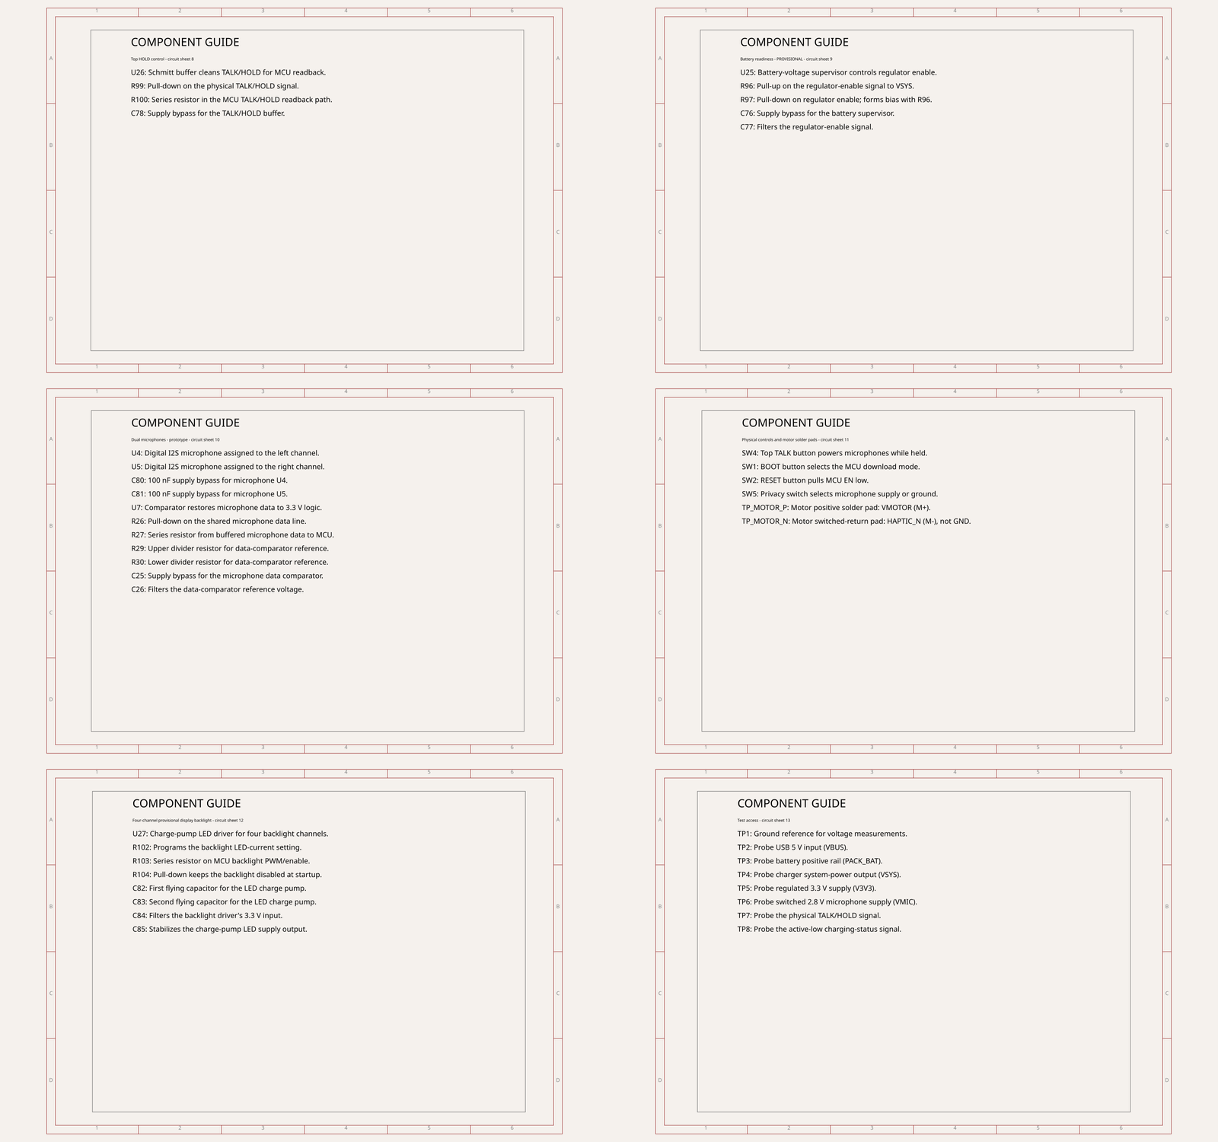
evidence/six-point-board-review-2026-10-06/final-schematics/guides-21-26-contact.png
