AnasSarkiz/tscircuit-ai-agent-remote/evidence/programmer-direct-uart-2026-10-07/before/VALIDATION.md.txt

## Canonical paste source repair — 2026-10-07

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

## Latest landscape replacement qualification —2026-10-07

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

Historical validation follows.

## Current speaker implementation step — 2026-10-07

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

---

## Historical manual routing repair — 2026-10-07

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

---

## Previous connection repairs — 2026-10-06

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

---

## Current six-point review — 2026-10-06

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

---

## Schematic component explanations — 2026-10-06

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

---

## Latest MCU correction — 2026-10-06

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

---

## Latest placement, component and programmer review — 2026-10-06

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

## Current order-readiness audit — 2026-10-06

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

## Manual/Freerouting continuation — 2026-10-06

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

## Current Pipeline9 WIP checkpoint — 2026-10-05

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

---

## Historical initial U2 move application — superseded by current native verification

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

## A7 cloud migration validation — 2026-10-05

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

---

## A6 public outcome — verified 2026-10-04

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

---

## A6 current checkpoint — 2026-10-04

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

### Current validation gates

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

---

## Current layout/BOM audit — 2026-10-04

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

---

## A5 public publication outcome — verified 2026-10-04

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

---

## A5 — motor solder pads and independent routing, 2026-10-04

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

---

## A4 placement-review public outcome - verified

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

## Latest placement gate review — A4

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

## A4 publication verified — partial registry outcome

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

# Latest A4 — 82.7% physical display coverage trial

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

---

## Latest A3 result — verified approved compressed attempt

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

## A3 publication result — verified 2026-10-04

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

# Latest A3 BuyDisplay and first-copper checkpoint — 2026-10-04

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

## A3 commands and evidence

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

## Current A3 gates

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

## Public A2 remote outcome — verified 2026-10-04

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

# Latest A2 checkpoint — 2026-10-04

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

## A2 evidence and gates

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

## Public visibility and committed native build — 2026-10-04

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

# Validation — A1 integrated placement preview (work in progress)

## Connector orientation implementation — 2026-10-04

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

## Runtime-only package step — 2026-10-04

### Verified publication outcome

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

### Current method: standard native upload with genuine CDN imports

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

### Initial preparation (superseded file count and upload method)

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

## A1 implementation and evidence

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

## Historical A0 validation (preserved; current A1 status above supersedes it)

# Validation — A0-reference-import-review (work in progress)

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

## Source and dependencies

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

## Requirements

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

## B-001 — C370970: resolved locally for reported drill dimensions

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

## Other preliminary evidence

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

## Commands actually run

Commands run from this project directory. Logs under `evidence/tooling/`.

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

## Routes and fabrication

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

## Historical user-authorized chip-box symbol review — 1f63764, 2026-10-02

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

## User-authorized footprint correction and component review — 2026-10-02

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

## Historical B-002 diagnosis — locally corrected in the later milestone

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

## Published-release recheck and accepted design — 2026-10-03

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

## A0-C5656610-local-hole — user-authorized implementation step

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

Current evidence: `evidence/microphone-local-correction-2026-10-03/`.

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

## A0-power-review milestone — 2026-10-03

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

## A0-core-alignment milestone — 2026-10-03

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

### B-005 assembly defect discovered after native port resolution

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

## A0-controls-review milestone — 2026-10-03

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

## A0-MCU/USB review in progress — 2026-10-03

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

Native pin check retains eight metadata warnings; two chip-based imported
connectors also carry J-prefix convention warnings. They remain visible.
Manufacturer pin-role review is independent of incomplete imported metadata.
C94934 ESD has B-008 missing reference text, visibly confirmed. USB-C C165948
has B-005 missing paste on all four polygon VBUS/GND pads; native diagnostic
Gerber export exits 0 with 97 flashes and zero regions. This is an unrouted
fixture ZIP, not fabrication output. Both material issue updates were sent.

The new full native-output schema regression fails on 18 elements (B-010):
null schematic group subcircuit id, numeric PCB display offsets on 16 components,
null PCB group anchor alignment. Circuit-json 0.0.510 schema remains strict;
no output was patched. The fix chat independently confirmed the core source
still emits these invalid fields. Current tests: **9 pass, 1 fail**, 40 assertions.
TypeScript and formatting pass. All schema failures remain explicit. Full board
build still intentionally fails until the real circuit is authored.

Regulator feedback now uses untouched C364359 51.1 kΩ / C114639 9.1 kΩ,
nominal 3.3077 V, provisional PWM static corners 3.1820–3.4382 V. New native
network-enabled build and all five checks exit 0; pin/source report zero
errors/warnings. PCB and A4 previews inspected, zero traces/vias. Initial
sandbox build could not fetch supplier footprints; network-enabled native rerun
resolves that access failure. Retain both logs; no unavailable supplier review
was called passed. Seven component bodies fit the isolated fixture; final
power-loop layout/effective capacitance/inductance/thermal/transients pending.
POWER.md records assumptions and divider idle-current tradeoff.

Exact display/logic candidates were imported unchanged. LCD HS17QS178RX C5329581
requires 2.7–3.3 V logic and 40 mA backlight (Vf 3.0–3.4 V); interface/connector,
backlight/off-state behavior and mechanics unfinished. TPS7A2028 C2869847
accuracy requires VIN≥3.1 V; C7848 logic buffer and C11133 clock switch are
research candidates, not yet qualified. TLV757 C2863639 is rejected for headroom.
ALPS C110293 switch comparison is in progress, without imported-definition edits.

Battery decision is pending: candidate protected NTC pack's PCM limits continuous
current to 1 A versus provisional 1.488 A budget. A human question asks whether
separately sourced enclosure batteries may be allowed; no reply or exception
is assumed. All other electronics still require supported exact JLC imports.

Core 0.0.2059 and CLI 0.1.2236 were checked at official release sources: motor
assembly/frame changes, no verified relevant blocker fix. Pinned tested versions
remain unchanged. Continue independent engineering, report confirmed defects
to authorized chat, verify fixes through native workflows when available.
No full-board routes, DRC/shorts pass, snapshots, fabrication package or hardware
measurements exist. Heartbeat remains ACTIVE. GitHub/private publication of
this review is unfinished; never treat failed native releases as fully published.

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

Authored-source whitespace check passes. Full Git whitespace scan reports native
SVG/log trailing whitespace and raw imported STEP CRLF endings; these generated
artifacts/imports are preserved byte-for-byte rather than reformatted. This
source-text finding is not a DRC result or imported-geometry waiver.

## A0-display-logic-review milestone — 2026-10-03

Independent partial LCD logic application implemented with19 exact imported
top-side PCB components, native A4,45×32 diagnostic canvas, routing disabled.
Current build and five required checks exit 0. Rotated actual J7 to face the
right edge; moved C43 out of its courtyard and grouped schematic VLCD bypasses
to resolve the actionable warnings. Final schematic-placement output empty;
placement0errors/0warnings. Current PCB and schematic PNG/SVG inspected.
Native snapshot exits0 and matches; generated snapshots reviewed. Five imported
metadata/convention warnings remain visible, no component edits/suppressions.
Pin-map tests checked actual TI LDO/buffer physical pins and LCD/FPC contact
order, LED polarity, unused inputs and open outputs.12tests pass,1failsB-010,
75 assertions; TypeScript and formatting exit 0. Current JSON has19top parts,
zero traces/vias/errors but21schema-invalid elements. This is diagnostic
evidence, not a full-board stage3–6 pass. DISPLAY.md records voltage/leakage
estimates, required sequencing and unfinished backlight/IDD/cable/mechanics.

Core source proposal, isolated from board dependencies, base18e1d11…(0.0.2061),
was reproduced/tested with upstream CI Bun1.4.0 and declared dependencies.
Unchanged baseline fails; correction passes strict schema/physical-pad
regression205assertions; related suite29pass/0fail/1existing skip,332assertions.
Core TypeScript and ESM/declaration build exit 0. Five existing changed PCB
snapshots and new PCB/A4 snapshots visually reviewed. Proposal saved and sent
to fix chat; full core suite unrun and no upstream release/push performed.
Board remains pinned official0.0.2058, strict B-010 failure intact.
Task tooling excludes the separate upstream checkout and limits board test
discovery to ./tests; this does not remove any board tests or schema checks.

C11050 land comparison (B-011) is not a demonstrated imported footprint defect:
raw/import geometry matches; nominal0.20mm differences are at drawing's
±0.20mm boundary. Source drawing date2004.6.16; revision applicability and
physical FPC mating qualification remain pending. No imported edits.

Git02950fb exact readback verified on private main. Native private version
0.0.2-wip-a0-mcu-usb-review exited1 (535success/4fail). Both timed-out STEP
files arrived byte-for-byte;413-rejected SN74LVC245APWR.step and TPS7A20 PDF
are missing on exact release readback; ready_to_build=false. Receipt/log saved
in display evidence, material B-009 update sent. No forced ready flag, model
omission, publication success or full-build pass. This current milestone's
publication has not yet been attempted.

Whole-board requirements/schematic/mechanics remain unfinished; routing,
shorts/copper validation, fabrication exports and physical tests remain pending.
Protected battery sourcing exception still awaits the human reply.

## A0 amplifier application review and charge intake — 2026-10-03

Independent17part top-side46×32mm amplifier application added as an unrouted
native A4 diagnostic; complete-board source guard remains. Native build and all
five required checks exit 0. C51 rotated180° to remove actionable placement
advisory; native PCB/A4 outputs reviewed.53rectangular pads/53native paste
shapes,zeroPCB traces/vias/errors.14tests pass/1strict B-010 test fails,
107assertions; TypeScript/format pass.19native schema-invalid elements are
saved separately. Missing Q1/Q2 imported reference text is B-008; snapshot
acceptance withheld. No schema/runtime/import edit or checker suppression.
Manufacturer physical amplifier/MOSFET/differential-output pin tests pass;
static gate/shutdown corner estimates are conditional, not measured behavior.

Exact new importsC265101/C132554/C2862740/C6617702 support independent battery
connector/USB controller/LDO/hold-switch intake. Full manufacturer/mechanical
qualification and actual charger/NTC/dead-pack policy remain pending. Protected
pack procurement exception awaits a human answer. B-012 speaker libraries
C3311258/C6230316/C50387211 unavailable. B-004 exact-MPN resistor search
returned unrelated components, unselected and reported. Native parts are not
modified to hide warnings or substituted by authored component definitions.

Gitc82e7deb display milestone verified remotely. Its nativeprivate package
0.0.2-wip-a0-display-logic-review exited1:582success/4fail. Both timeout files
arrived with exact hashes; both413 files missing404; ready_to_build=false.
Receipt and log preserved in audio/charge evidence. This amplifier milestone's
Git/package publication is still pending. All material issues were sent to the
authorized fix chat; useful independent work continues.

Whole-board stages1/2remain unfinished/blocked,3–6not started,7physicalpending.
No saved routes exist and no fabrication-ready, copper/shorts or hardware-test
claim is made. Save native routes before changes once prerequisite gates pass.

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

## A0 WIP — hardware Type-C current review, 2026-10-03

Source: `src/power/type-c-current-review.tsx`; full notes in `TYPE-C.md`; exact dependency/source hashes and command outputs in `evidence/type-c-current-review-2026-10-03/`. This independent 17-component native A4/top-side diagnostic has no routing. Native build and required netlist, pin_specification, source, schematic-placement and placement checks all exit 0. Current A4 and PCB images were actually inspected: inside boundary, no component overlap; R74/R75 labels remain legible at 180 degrees. Native output has 54 pads and 54 paste shapes, zero PCB traces/vias/emitted errors. C2862740's missing requires_power metadata warning is preserved (B-007); physical IN/EN/OUT pins were verified with TI's drawing.

Three manufacturer connection/corner tests pass. Canonical format/typecheck pass. Canonical board suite has 17 pass / 1 fail / 155 assertions: existing B-010 full-native-schema failure persists. The Type-C diagnostic independently has 19 invalid native schema elements; `schema-failures.json` preserves the failures. No schema/runtime edit, check suppression or full-board stage pass.

C22765 / 0603WAF1201T5E is a native-imported 1.2k candidate for future BQ24074 ILIM; not wired or temperature-qualified. The controller itself has no charger/pack/system-load-enable connection yet. Actual protection, TS limits, battery qualification, ramp timing, default-current dead-battery behavior, effective capacitance, current/thermal/mechanical fit still need completion. The pending battery-sourcing question is not assumed approved. Earlier complete-board stage statuses remain unchanged.

The C6617702 hold candidate is unmodified and remains unqualified: native cutout width 5.334 mm differs from the historical Panasonic 2012 drawing's 5.1 +0.1/-0 mm. Current manufacturer drawing confirmation remains pending. Its independent 2-component reproduction builds and all five native checks exit 0; PCB/A4 were inspected, but that does not qualify the imported cutout or actual edge mounting. It is forwarded to the authorized fix chat as a discrepancy, not declared a proven current supplier bug.

## A0 WIP — haptic driver review, 2026-10-03

Independent native A4/top-side regulator and flyback review added with10 actual
JLC imports. `HAPTICS.md` records manufacturer pin, voltage, default-off and
remaining qualification requirements. Native build and all five required checks
exit 0. Network-enabled build resolves sandbox supplier lookup failures; retained
import metadata/reference advisories remain B-007/B-008.24 native pads/24 paste
shapes;zero PCB traces/vias/errors. PCB/A4 images actually inspected. Two new
manufacturer connection/physical-pad/polarity tests pass; canonical suite19pass,
1existing B-010 failure,177assertions. TypeScript passes;12 strict schema-invalid
elements preserved. No full-board gate or snapshot acceptance claimed.

**BLOCKING B-014 — C2942347 / LCM0720A3176F:** imported courtyard misses the
top-side motor body. Actual overlap reproduction passes placement0/0 yet puts
a resistor under that body. Fix chat confirmed converter body-bounds generation
defect. Native OBJ height3.85mm versus drawing-derived provisional2.65mm maximum
stack is a separate model qualification concern. C2895081 alternate import lacks
EasyEDA data. All supplier/library/model/reproduction evidence saved in
`evidence/haptic-review-2026-10-03/` and forwarded. Motor placement/integration
stays blocked; driver review does not substitute a generic motor.

The earlier high-current Type-C detector has a newly identified electrical
startup qualification gap: AND gate operation is undefined below1.65V supply,
where BQ EN2's guaranteed-high level starts at1.4V. A supervisor on one input
does not guarantee output low throughout that ramp. No fault transient has been
measured and no tscircuit defect is alleged. It remains unintegrated. Proposed
fixed USB100 with EN1/EN2 grounded needs actual pack, TS, charge-time, thermal,
dead-pack and system-load readiness review. `evidence/charger-safe-default-review-2026-10-03/startup-review.md`
preserves the scope and proposal; battery sourcing question remains unanswered.

Preceding source6700842b16f651adbc93bc899e9839412bfc3191 is verified on GitHub.
Supported private native version0.0.2-wip-a0-type-c-current-review exited1:
689reported successful uploads/33reported failed. Exact readback verifies28
reported timeout files byte-for-byte and five actual missing404 files;
private=true,ready_to_build=false. Readback includes native binary download,
not metadata alone. Logs/receipt/script saved with this review. B-009 persists;
no evidence omitted, forced ready flag, successful-publication or full-build
claim. This haptic milestone's remote publication remains pending.

Native generated SVG whitespace and a netlist-log trailing blank line remain
unchanged; git whitespace inspection reports those three non-geometric lines.
Installed CLI0.1.2235 supports `push --compress`: official source packs the same
enumerated files with lossless gzip and uses native upload_archive. This supported
publication mode will be tried without omitting models/evidence or forcing ready.

Whole-board stages1/2 remain unfinished/blocked;3–6not started;physical stage7
pending. No copper, saved routes or fabrication-ready package exists. Future
native routes must be saved before moving/rerouting and revalidated afterward.

Publication read-back: preceding amplifier Git revision `50bebdb6c283cf72ab4ab1e28321782e28065cf8` is pushed. Native private `0.0.2-wip-a0-amplifier-review` exits 1 (665 successes, 13 failures), ready_to_build=false. Amplifier TSX, bun.lock and three timeout STEP files have exact remote hashes; nine reported failures are actually absent. Four HTTP413 failures and remaining network failures remain B-009. Logs and receipt saved in this step's evidence folder; no ready flag or upload omission workaround.

## Regulated microphone clocks and nominal mechanical study — 2026-10-03

Parent source: a1e76d5f2879d74b68d882c3ea5576359b0ccc42. The new milestone
commit and evidence/microphone-open-drain-review-2026-10-03/source-manifest.json
identify the candidate. Its native A4 fixture uses 15 imported top parts,
37 pads and 37 paste entries, zero PCB traces/vias/error elements. Native build
and all five diagnostic checks exit 0 after rotating C74 by 180 degrees cleared
an initial placement orientation failure. Both logs are preserved; no imported
footprint was edited. Network-enabled build resolved sandbox supplier fetch
failures. PCB PNG and landscape A4 schematic PDF were inspected; snapshots match.
Formatting and TypeScript exit 0. Two new hardware-boundary tests pass. Canonical tests report 21 pass, 1 fail,
204 assertions (B-010). Strict candidate JSON has 17 invalid elements; original
JSON and every failing index/type are preserved. No schema/checker weakening.

ICS-43434 C5656610 I2S Table 5 specifies 1.8 < VDD < 3.3 V; the provisional
main rail reaches 3.43818 V. A dedicated TPS7A2028PDBVR C2869847 regulator
controlled by HOLD_HARDWARE gives a conditional 2.758–2.842 V with VIN >= 3.1 V
and load >= 1 mA. Nexperia 74LVC2G07GW,125 C24478 open-drain clocks are powered
from VMIC and pulled high only to VMIC by YAGEO 330-ohm C105881 resistors.
All imports are genuine and unchanged. The conservative total clock-load bound
is about 30 pF for TDK's 25 ns rise limit, accounting for the pulldown-limited
high level. Actual input capacitance, timing, partial-power AC feedthrough,
off-state injection and release-to-off deadline remain unqualified. IOZ's
5.5 V test condition is not expanded to an invented 2.8 V guarantee.
Privacy, complete microphone circuitry, switch and stencil remain pending or
blocked; detailed sources/conditions are recorded in qualification.md.

The dimension study in evidence/mechanical-envelope-review-2026-10-03 uses
actual C5329581 LCD dimensions, module pad coordinates/body-origin offset and
Espressif's 15 mm RF recommendation. The 50 x 50 mm trial fails; the approved
50 x 65 mm trial gives a nominal 15.82 mm LCD-to-antenna gap and 4.78 mm upper
land support margin. Raised LCD, tolerances, substrate removal, top button,
case, pack and speaker fit are unqualified. This does not prove all square
layouts impossible or establish a new exterior design. The sketch creates no
electronic component definitions or native placement/keepouts/cutouts.

Haptic parent publication: GitHub verified; private native version
0.0.2-wip-a0-haptic-driver-review exited 1 after archive HTTP413 and native
file-by-file fallback (771 reported successes, 13 failures). All seven timeout
files match exact readback hashes; six HTTP413 files remain 404. Package remains
private=true, ready_to_build=false; B-009 persists. Receipt/script are in the
clock evidence. Original private archive error payload remains in the tmp log;
the diagnostic copy replaces only that 97 MB payload line with original path,
length and hash, retaining errors and statuses. The CLI logging defect was
separately confirmed by the fix chat. No uploaded evidence was omitted and
no ready flag was forced. Current official core 0.0.2063 is unchanged; CLI
0.1.2237's current gitHead differs only by a package version bump. Required fixes
are not verified published. Pinned board dependencies remain unchanged.

Whole-board stage 1 remains in progress, stage 2 blocked, stages 3–6 not started
and physical stage 7 pending. No full copper routes or fabrication package
exists. Battery sourcing exception remains unanswered. Confirmed findings were
sent to the authorized fix chat; independent work continues.

## Battery-readiness candidate and latest publication review — 2026-10-03

Independent `src/power/battery-ready-review.tsx` uses genuine unmodified TPS3808G33DBVR / C43698 to sense charger BAT while powered from charger OUT. Five top parts, 14 SMT/paste pads, zero copper/vias/errors. Native build, all five diagnostics, A4 PDF export and snapshots exit 0; PCB, A4 schematic, snapshots and TI pin page visually inspected. Formatting and TypeScript pass; canonical suite 22 pass / one existing B-010 fail / 213 assertions. Seven strict native JSON failures persist. No full-board gate passes. Exact evidence and conditional static limits: `evidence/charger-battery-ready-review-2026-10-03/qualification.md`.

TI documents asserted RESET between POR and minimum operating supply, but arbitrary supply ramps, the 100 nF reset load, absence/open pack, capacitor history, cutoff relative to actual PCM, full VSYS load isolation and charging/NTC policy remain unqualified. G33 minimum trip 3.02395 V cannot ensure shutdown before the unselected example pack's maximum 3.10 V protection threshold. Protected rechargeable pack/harness/NTC choice still requires resolution. No battery or thermistor substitute was authored. New wrong-part searches are saved as supporting B-004 evidence and excluded from selection.

Latest official core remains 0.0.2063; importer easyeda remains 0.0.368; CLI remains 0.1.2237. Exact Circuit JSON 0.0.510-to-0.0.511 published source comparison changes missing-MPN warning fields only and does not fix B-010. No board dependency update applied.

GitHub revision 435493d1574c19dfb2e732ed359cda79e4d1205d was pushed and exact remote head verified. Supported native private `0.0.2-wip-a0-mic-clock-review` exited 1: 834 reported successes, nine failures (six HTTP413, three timeouts). Readback evidence is in this new review directory. Publication remains B-009; no omission, forced-ready flag or weakened checks. Source and artifacts at the previous milestone were held unchanged throughout its publisher run.

Publication identity correction: native --version-tag prefixes package version. Actual previous release is `0.0.2-0.0.2-wip-a0-mic-clock-review`. The initial single-prefix lookup was invalid and its404 results are excluded from absence conclusions; corrected readback is retained separately.

Corrected mic-clock readback: all three timeout files match exact hashes; six HTTP413 files are absent; package private=true and ready_to_build=false. This confirms B-009 without relying on the invalid initial lookup.

## Two-contact hold candidate, fabrication rules and BOM export review — 2026-10-03

Base Git revision d6826fa23d7160007f83bbc99a0c1204ae20e7e7 is pushed. The current milestone commit and new source manifests identify this additional independent review; no complete-board gate advances.

Genuine ALPS SKSWCFE010/C255576 native import is unchanged. Its two contacts and absence of locating holes avoid the four-contact ambiguity of earlier B-006 candidates, but it remains unselected: imported0.7999984×1.524mm lands differ from the current ALPS recommended pattern. Supplier raw pads are identical to the imported/native dimensions; this is an acceptance gap, not a proven converter defect. Native two-part hold fixture build/allfivechecks/snapshot/A4PDF/types/format pass, zero traces/vias/errors; four strict native JSON failures remain B-010. PCB/A4/snapshots/manufacturer drawing were inspected. The exact C202371 alternate supplier check has the same lands and was not imported/selected. Full switch mechanism, land/paste acceptance and release behavior remain unqualified. Evidence: evidence/hold-control-alternate-review-2026-10-03/qualification.md and hashes.

Current JLCPCB rule/stack review saves proposed four-layer standard JLC04161H-7628,1.6mm order thickness,outer1oz/inner0.5oz. Verified official calculator gives 90-ohm L1/L2 noncoplanar USB pair width0.2906mm/space0.1999mm; physical impedance tolerance±10%, distinct from0.5% calculator fit tolerance. Ordinary proposed trace0.20mm/clearance0.20mm, through via0.30mm hole/0.70mm diameter and other nominal manufacturing rules remain requirements, not actual copper measurements. Read-only native measurements give microphone hole0.60mm with minimum pad clearance0.2580203mm and minimum different-net rectangular SMT clearance0.1976628mm across51 fixture component instances, above JLC's0.15mm SMT-pad minimum. Conditional manufacturing tolerance sweeps are not asserted as DRC failures. Acoustic process/paste/full placement/routed copper remain unresolved. Exact native hashes, calculator AX/JPEG, measurement scripts/results and source links are in evidence/fabrication-rule-review-2026-10-03/qualification.md.

**BLOCKING B-015 — native BOM Comment metadata loss:** official latest circuit-json-to-bom-csv0.0.19 (also bundled by pinned CLI0.1.2235) emits blank Comment for genuine imported U1/C2913201, J1/C165948, U25/C43698 and SW4/C255576 despite native MPNs. Its documented resolver comment is independently reproduced as ignored too. Exact JLCPCB IDs remain preserved. JLC's current BOM specification requires descriptive Comment. This gates approval of the native stage6 BOM once earlier gates pass; stage6 is not reached. Footprint supplier-code fallback is separately unqualified; no actual assembler mismatch alleged. Public API reproduction, official isolated exact-version runtime/lock, native input hashes and NOT-FOR-FABRICATION CSV are saved in evidence/bom-export-review-2026-10-03. Fix chat independently confirms converter ownership. No library/component/output rewrite or relaxed schema is applied.

Saved-route source investigation verifies pinned native autorouting:end.pcbTracePaths and <autoroutingphase pcbTracePaths> APIs with per-phase/connection identity. Original events/full JSON must be preserved before route movement; every phase requires actual replay/geometry/connectivity/shorts validation. Omitted saved paths with an actual unavailable reason cannot be replaced by an empty/partial cache. Older pcbRouteCache behavior is unqualified and no new defect is claimed from source inspection alone. evidence/saved-route-api-review-2026-10-03/qualification.md records verified types/source and required round trip. No actual copper or saved routes exist.

Official core0.0.2064 changes only capacity-autorouter dependency and version, not B-010. Open core PR4283 currently contains an async PCB-port matching fix despite its older repro-only body; the preserved explicit-import board fixture has101source/101PCBports with numeric coordinates. No unmerged fix/runtime update applied and no future routing pass inferred. Whole-board stages1inprogress,2blocked,3–6notstarted,physical7pending; exact pack/harness/NTC/procurement question still unresolved. No order or fabrication-ready claim.

Final preceding battery milestone publication: native session48547 exited1,834reported successes/62failures for actual private0.0.2-wip-a0-battery-ready-review. Exact readback verifies55reported timeout files byte-for-byte; six previously known HTTP413 files and one new timeout file imports/SN74LVC1G17DBVR/SN74LVC1G17DBVR.tsx are currently404. Seven absent, no unverified files; private=true,ready_to_build=false. Evidence/readback/source hashes in the fabrication-rule review; material update sent to fix chat. Source was held unchanged throughout publisher run. B-009 persists; no full-publication claim or forced-ready/upload-omission workaround.

Current milestone checks: formatting and TypeScript exit 0; canonical22pass/one existing strict-native-JSON B-010fail/213assertions/8files. Independent official BOM converter characterization exits0 and reproduces B-015; all raw native failures remain disclosed. No routing or full-board gate enabled. Current milestone remote commit/publication follows standing authorization and remains pending until verified.

Git whitespace inspection reports22,063warnings:22,054in the untouched supplier STEP (native line endings),twoin unchanged official BOM CSV,twoSVG lines,fournative calculator AX lines and one netlist-log EOF. Original bytes/hashes are preserved; summary and original diagnostic hash/path saved in whitespace-review.json. These are disclosed non-geometric formatting artifacts, not accepted DRC violations or a fabricated clean whitespace result.

## Hardware hold readback and top-control clearance review — 2026-10-03

Base fa90b5420f8e567270697c68132f311444a42424 was pushed and exact GitHub main verified. Its native private0.0.2-wip-a0-fabrication-review publisher exited1:957 reported successes/28 failures. Exact readback confirms22timeout files persisted with matching hashes and six known HTTP413 files remain404; no failed-file cases unverified or mismatched. private=true, ready_to_build=false. Evidence/log/readback receipt and script are preserved in evidence/hold-readback-review-2026-10-03. All enumerated source/artifact bytes stayed unchanged throughout that publisher and its readback. B-009 remains unresolved.

Independent src/audio/hold-readback-review.tsx uses unchanged genuine C7836 SN74LVC1G17DBVR input on hardware HOLD, a distinct buffered output through1kohm C21190 to MCU_HOLD_READ,10kohm C98220 ground bias and100nF C45000 decoupling. Its pin1NC stays open. The Schmitt input accommodates slow button transitions; no GPIO is directly wired to the microphone-enable net. This is an architecture/connectivity review, not full dynamic privacy qualification. Actual GPIO/boot pulls, low-voltage input leakage, contact bounce, capacitor history, partial-supply behavior, local decoupling loops and microphone off deadline remain open.

Native independent A4 build/allfive diagnostics/PDF/snapshots exit 0; fourtop components,11SMT/11paste/11PCBports, zeroPCBtraces/vias/emitted errors. PCB/A4/snapshots/TI pin diagram and UNI-ROYAL package/land drawing visually reviewed. Strict unchanged nativeJSON fails sixelements B-010. Canonical formatting/TypeScript exit 0; tests23pass/one existing B-010fail/228assertions. The additional boundary test verifies source pin identity, distinct input/output/readback nets, resistor values and openNC; it does not waive the full JSON gate or establish physical privacy. Original low-stock source/JSON/checks/snapshots were preserved before the genuine resistor change. Native group pcbStyle provides1mm reference labels without an imported-definition edit. Exact hashes and conditional electrical limits are in the dated qualification/source manifest.

Current native searches report C22548 stock5, C98220 stock22, C7836 stock34179, C45000 stock3848 and exact higher-stock C21190/0603WAF1001T5E stock8,013,731. Supported unchanged C21190 import is used in this candidate; other candidate sheets retain their prior exact parts and need final whole-BOM procurement review. C25804/0603WAF1002T5E was genuinely imported but remains unselected because both catalogue queries are empty. The fix chat confirms positive-stock filtering and independent EasyEDA libraries: this alone is not a bug or assembly-stock proof. Observation/report/response saved without creating a false new defect. Resistor temperature and initial-tolerance allocation2.1%, local loading and full supplier-land acceptance remain conditional; aging/final temperature policy pending.

Read-only top-control study moves the module physical center from(0,22) to(-8,22)mm on the50x65trial, increasing actual switch body/terminal-to-antenna gap from9.9495088 to17.9495088mm, above the15mm recommendation nominally. Native module origin accounts for3.775456mm body offset. All49native MCU lands retain minimum4.7805042mm edge margin; two switch lands retain1.238mm. LCD gap remains15.82mm with2.19mm body/shield plan overlap requiring raised fit. The diagram was inspected. No full native placement, keepout/cutout or electronic definitions are generated by the study. Top-edge actuation, RF/manufacturing tolerances, antenna substrate, square enclosure/dominant-screen coverage, exact battery/speaker and final vertical fit remain unqualified. Evidence: evidence/top-control-mechanical-review-2026-10-03/findings.md and native input/output hashes.

Latest checked official core0.0.2066 (b8fa4aae7c67d03e2d53160d44c4307269496545) adds bend diagnostics/tear-relief and checks dependency; no relevant blocker correction found in exact published-source diff. CLI0.1.2237/easyeda0.0.368/CircuitJSON0.0.511/tscircuit0.0.2742/BOM converter0.0.19 unchanged. PR4283 stays open at7fa3beb2f9c83878d1d65cec4e591f68e8fb4b50. Pinned board runtime remains unchanged. No full-board gate advances: stage1inprogress,2blocked,3–6notstarted,7physicalpending. No saved copper routes or fabrication package exists. This WIP step will be committed/pushed and natively privately published under standing authorization; actual remote results must be verified separately.

Current milestone Git whitespace inspection reports29,514warnings:29,508untouched supplier STEP CR lines, fournative SVG lines and twonetlist-log EOF lines. Original bytes preserved; diagnostic hash/path and per-file counts recorded in evidence/hold-readback-review-2026-10-03/whitespace-review.json. No whitespace-clean or DRC-pass claim is inferred.

Publication outcome for0573bf4492817ea0263827b6f0431fb7905d4959: supported private0.0.2-wip-a0-hold-readback-review publisher17411 exited1,1081reported successes/20failures. Exact readback confirms13reported timeout files byte-identical and seven404: six existing HTTP413 files plus imports/TLV3201AIDBVR/TLV3201AIDBVR.tsx (C105188), reported as a timeout. No failed-file mismatches or unverified cases. Package private=true/ready_to_build=false. Evidence/log/script/receipt are in evidence/hold-readback-publication-2026-10-03. Existing files stayed frozen through publication/readback; subsequent local watch/receipt notes are not part of that release. GitHub source0573bf4 succeeded, private publication remains incomplete B-009. No new implementation version, fabrication gate advancement, upload omission or forced readiness is inferred.

Official read-only release check05:18UTC: core2067 preserves supplied imported electrical attributes; easyeda369 accepts caller-supplied pinAttributes. Native fresh C2149796 import still only declares ground2/NC4, no supply1, so B-007 remains an enrichment gap rather than a newly proven converter defect. Exact source diff/native import/latest CLI source and fix-chat corroboration are in evidence/upstream-watch-2026-10-03-0511. No dependency/import-definition update; B-010 and separate geometry/BOM blockers remain. Versions rechecked unchanged approximately05:32UTC.

Independent read-only GPIO allocation proposal: evidence/gpio-allocation-review-2026-10-03 proposes15 unique peripheral/readback GPIOs, all15 matching unchanged C2913201 import contact labels and reviewed Espressif modulev1.8 table3-1. HOLD input21/contact23 avoids straps/USB/PSRAM; independent I2S0 microphone and I2S1 amplifier clock sets plus SPI2 LCD pins are proposed. Manufacturer reset/glitch/USB-OTG pad tables reviewed; GPIO18 and pad-JTAG pins excluded from output candidates. This is a candidate, not implemented native wiring or a full boot/privacy proof. Backlight, battery/status sensing and actual timing/partial-power qualification remain open. Source/dependencies remain unchanged; no native checks, fabrication gates or new board version are inferred from this static label review. Primary links and source hash are retained with the proposal.

## A0-reference-import-review — 2026-10-03

Human instruction: recheck actual assembly/routing blockers, continue independent work and seek genuine alternatives. B-009 publication and B-015 BOM descriptive metadata do not prevent schematic authoring or placement work; they remain publication/final-export gates. B-004 catalogue errors do not invalidate verified exact-part imports. B-007 is a visible role-metadata warning, not an established electrical connection failure. B-011 remains a tolerance/land acceptance question, not a proven fabrication defect. B-006/B-012/B-014 affect rejected or unselected candidates; actual replacements still require qualification. None of these classifications waive the earlier requirement/BOM/placement gates.

B-008 is resolved for C105188, C94934, C20917 and C15127: regenerated complete, unedited definitions using documented official `easyeda0.0.370 convert -i <C-number> -o <file>`; native core0.0.2070 owns each label on the correct schematic component. The four pin-label and footprint blocks are byte-identical to their preserved originals. Official generated CAD URLs replace local asset aliases; previous local assets remain preserved. Native tsci import on pinned2235 still returned the old definition; its converter uses a CDN browser endpoint, so the documented converter CLI was used instead. No imported definition or runtime was manually patched. Initial core installation exposed a missing props export; official props0.0.682 and circuit-json0.0.513 were aligned and installed with Bun's supported force refresh.

All four fixture builds and all20 required diagnostic checks exit 0; all remain unrouted with zero traces/vias. Three native A4 PDF exports and snapshots exit 0; corrected PCB/schematic images and rendered A4 pages were inspected. Correct references U7/D2/Q1/Q2 have native component ownership; missing-reference warnings are absent. B-003 has four linked ground pads/ports. B-005 persists: microphone has nine copper shapes but only five paste records; four polygon ground pads lack paste. USB polygon paste remains unqualified. Strict native schema still rejects comparator26/USB18/amplifier19 elements (B-010); the isolated microphone has zero strict schema failures. Canonical tests26pass/one existing B-010fail/235assertions/10files; formatting and TypeScript exit 0. A saved upstream CLI excerpt was renamed `.ts.txt` preserving its bytes, because it is documentary source with absent upstream-relative files; no actual board code was excluded from TypeScript checking.

Alternatives: C20613566, C49246973 and C7430168 speaker imports each fail with no EasyEDA library. Broad `speaker` search again returns unrelated components, retained but not selected. C41348533/LEADER LD-SM-430 imports and native builds successfully. Manufacturer drawing inspected: SMT2.7V motor, operating2.3–3.2V, 11mm maximum length, reference PCB lands. Its three native lands are polygons with zero paste records, so it does not avoid B-005. No CAD model is provided; electrical role of third mounting land, body bounds/courtyard, mechanical fit, reflow and full driver application remain unqualified. It stays a candidate; no blocked part has been silently substituted.

Current evidence: `evidence/blocker-recheck-2026-10-03-1357/` (baseline definitions/dependencies, unmodified official generated imports, import receipts, native logs/outputs/A4 PDFs, source checks, strict schema failures, alternative supplier drawing/imports). Whole-board stages1inprogress/2blocked/3–6notstarted/physical7pending remain. No complete schematic, final placement, saved routes, copper or fabrication package exists. New implementation remote commit/private publication must be verified separately; source will be frozen during native publication.

Current main build was run and exits1 with the intentional incomplete-board guard (main-build-guard.log). This is not a full-board validation pass. Native private publication planned suffix wip-a0-reference-import-review; GitHub/private package results will be independently recorded after the source commit. Fix chat reports core PR4344 open for polygon paste; unpublished code was not installed.

Staged diff whitespace review reports13 supplier/native-output warnings: one untouched native motor import blank line, eight SVG/snapshot blank-line spaces and four native log EOF blank lines. Exact evidence/component bytes are preserved; these do not represent copper/assembly checks or accepted electrical warnings. Authored formatting passes. The unstaged diff check before staging had no findings; it did not inspect then-untracked evidence.
# Pipeline9 selection — 2026-10-05

`main.tsx` explicitly selects `beta_pipeline9`. Native routing metadata confirms
`AutoroutingPipelineSolver9_PreloadedTraceGraph` from unchanged capacity-autorouter
0.0.958. The full-copper trial timed out; a direct public-library trial exhausted
the memory budget; a signal-first trial ended with an actual iteration-limit
routing error. No newly solved copper was accepted. The original copper was
restored and freshly rebuilt, byte-identical to SHA256
`81c31f77ac0871bfc4414b0940752e4f4fe0692a62089320b409908d4a8d5315`.
It still has 90 native opens and 26 physically disconnected nets. Prior schema,
paste, supplier-mating and fabrication failures remain unresolved. The explicit
selection does not reroute saved paths or make the board fabrication ready.
Evidence and final publication receipts: [Pipeline9 review](evidence/pipeline9-routing-2026-10-05/review.md).

Published board source: [GitHub a9600d8](https://github.com/AnasSarkiz/tscircuit-ai-agent-remote/commit/a9600d81e40761d3fc7c2471c57cb05d77c548a4).
Public [Pipeline9 WIP preview](https://tscircuit.com/AnasSarkiz/tscircuit-ai-agent-remote/releases/60b0df33-f229-4c85-8515-e9f5d2250674/preview)
has 116/116 original files verified by anonymous hash readback. The preview API
returns the exact local native board. Upload completion is verified; cloud CI,
new browser visual review and fabrication approval are not inferred.

# Native bus-lane/fanout continuation — 2026-10-06

Actual native bus-lanes and public fanout trials failed. Manual AMP_SD_MODE
routes closed the signal net but split U3's previously connected ground.
The later top cutout trial retained that regression and introduced six drill
clearance violations. No proposed route, placement or margin change was accepted;
exact baseline source bytes and native JSON are restored. Current accepted
counts remain 90 native open errors / 26 physically open nets, with zero measured
geometry violations and shorts and all 152 baseline region widths passing.
The whole-board connectivity/fabrication gate remains blocked.

[Routing trial review](evidence/native-remaining-routing-2026-10-06/review.md)
contains original native inputs/events, resource outcomes, source snapshots,
physical audits, width checks and byte-verified restoration. The stock DSN
converter loses required copper/keepouts and uses weaker defaults; no
Freerouting result was accepted. Maintained diagnostic helpers add the finer
power grid, optional larger planning reserve and public bus/fanout repro.
No manufacturer imports, dependency versions, genuine caches or manufacturing
checks were modified. The existing public `0.0.2-wip-pipeline9` release remains
the exact accepted board revision; this change publishes diagnostics only.

Fresh diagnostics checks: TypeScript passes; routing regressions 17/17 pass;
board tests 42 pass / 2 existing fabrication/schema failures; root formatting
passes after force-ignoring cloud runtime caches. All 325 checkpoint files
verify, including unchanged board native/source/cache bytes. The formatter's
local credential-bearing diagnostic was redacted before publication; the
hygiene scan found no credential pattern in newly saved evidence.
