AnasSarkiz/tscircuit-ai-agent-remote/evidence/a3-routing-2026-10-04/buydisplay/cad-measurements.txt

module {'min': [-21.000999450683594, 13.174036835998535, 0.8], 'max': [-2.9990005493164062, 38.675037240356446, 3.909999895095825], 'max_z_under_lcd': 3.909999895095825}
connectors {'J1': {'min': [-4.46999979019165, -33.77507254169922, -0.05001099109649654], 'max': [4.46999979019165, -25.875072446331785, 4.050988960266113]}, 'J3': {'min': [-1.6000510215759278, 16.475031852722168, 0.8], 'max': [8.399948978424073, 25.525031566619873, 6.3]}, 'J4': {'min': [9.799999618530272, 24.049987316131592, 0.8], 'max': [18.39999952316284, 31.949987411499023, 6.300999927520752]}, 'J6': {'min': [-21.399923706054686, -14.522001018524168, 0.8], 'max': [-13.399923706054686, -9.572000970840453, 3.7100000858306883]}, 'J7': {'min': [6.174960088729856, -27.925000190734863, 0.8], 'max': [11.924960088729856, 2.6750001907348633, 2.8]}, 'J8': {'min': [14.999999618530275, 15.299987316131592, 0.8], 'max': [23.599999523162843, 23.199987411499023, 6.300999927520752]}}
under LCD [('U1', 3.909999895095825), ('J6', 3.7100000858306883), ('D3', 2.849999952316284), ('J7', 2.8), ('U25', 2.44893901348114), ('SW5', 2.3000009536743162), ('U26', 2.049083042144775), ('U7', 2.049083042144775), ('U13', 1.900000023841858), ('U23', 1.900000023841858), ('U24', 1.900000023841858), ('U12', 1.84920494556427), ('U14', 1.84920494556427), ('Q1', 1.84920494556427), ('Q2', 1.84920494556427), ('U22', 1.84920494556427), ('Q9', 1.84920494556427), ('U27', 1.8099999904632569), ('L1', 1.8), ('U2', 1.749999988079071)]
