AnasSarkiz/tscircuit-ai-agent-remote/evidence/microphone-local-bypass-2026-10-08/schematics/13-test-access.png

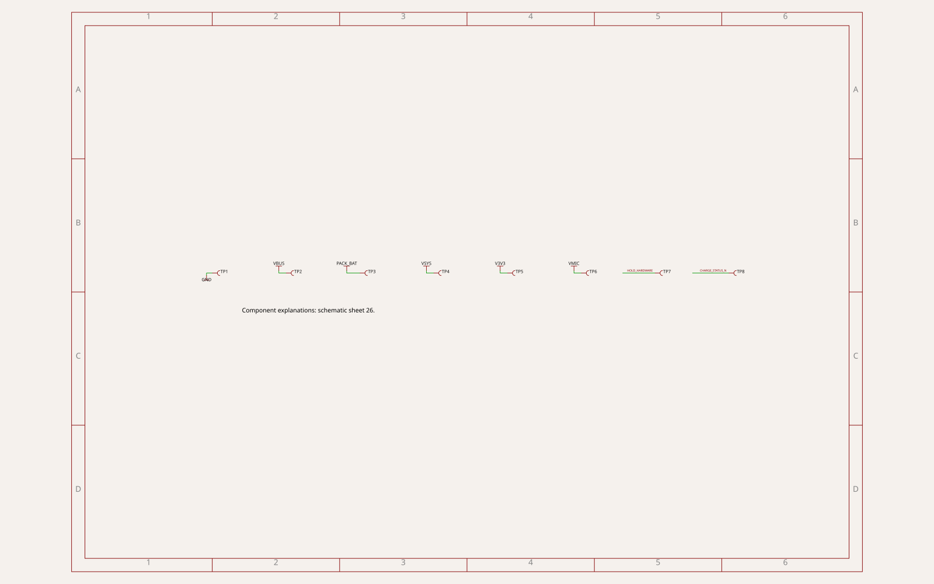
evidence/microphone-local-bypass-2026-10-08/schematics/13-test-access.png
