AnasSarkiz/tscircuit-ai-agent-remote/evidence/connection-repair-2026-10-06/control-corridors-cap-native/source-snapshot/src/board/connection-copper.json.txt

{
  "classification": "Authored native connection repairs and low-current signal relocation; not autorouter caches",
  "paths": [
    {
      "net": "MCU_LCD_RESET_N",
      "from": ".U14 > .pin3",
      "to": "net.MCU_LCD_RESET_N",
      "width": 0.2,
      "pcbPath": [
        {
          "x": -1.625,
          "y": -4.67095
        },
        {
          "x": -1.625,
          "y": -4.67095,
          "via": true,
          "fromLayer": "top",
          "toLayer": "bottom"
        }
      ],
      "global_path_mm": [[7.375, 5.12905], [7.375, 3.32905]],
      "segment_layers": ["top", "top"],
      "classification": "manual native ordinary via escape; power current qualification pending",
      "top_length_mm": 1.8000000000000003,
      "via_outer_mm": 0.45,
      "via_hole_mm": 0.3
    },
    {
      "net": "MIC_SD",
      "from": ".U5 > .pin6",
      "to": "net.MIC_SD",
      "width": 0.2,
      "pcbPath": [
        {
          "x": -2.692826,
          "y": -0.800127
        },
        {
          "x": -2.692826,
          "y": -0.800127,
          "via": true,
          "fromLayer": "top",
          "toLayer": "bottom"
        }
      ],
      "global_path_mm": [[19.1928144, -29.000127], [17.807174, -29.800127]],
      "segment_layers": ["top", "top"],
      "classification": "manual native ordinary via escape; power current qualification pending",
      "top_length_mm": 1.599999786910036,
      "via_outer_mm": 0.45,
      "via_hole_mm": 0.3
    },
    {
      "net": "MIC_BCLK",
      "from": ".R92 > .pin2",
      "to": "net.MIC_BCLK",
      "width": 0.2,
      "pcbPath": [
        {
          "x": 0.75335,
          "y": -0.8
        },
        {
          "x": 0.75335,
          "y": -0.8,
          "via": true,
          "fromLayer": "top",
          "toLayer": "bottom"
        }
      ],
      "global_path_mm": [[15.75335, -29.75], [15.75335, -30.55]],
      "segment_layers": ["top", "top"],
      "classification": "manual native ordinary via escape; power current qualification pending",
      "top_length_mm": 0.8000000000000007,
      "via_outer_mm": 0.45,
      "via_hole_mm": 0.3
    },
    {
      "net": "GND",
      "from": ".R41 > .pin2",
      "to": "net.GND",
      "width": 0.3,
      "pcbPath": [
        {
          "x": 0.35,
          "y": 0.9
        },
        {
          "x": 0.35,
          "y": 0.9,
          "via": true,
          "fromLayer": "top",
          "toLayer": "bottom"
        }
      ],
      "global_path_mm": [[14.50335, -5], [14.100000000000549, -4.0999999999996035]],
      "segment_layers": ["top", "top"],
      "classification": "manual native GND via escape",
      "top_length_mm": 0.9862510950565635,
      "via_outer_mm": 0.45,
      "via_hole_mm": 0.3
    },
    {
      "net": "GND",
      "from": ".R69 > .pin2",
      "to": "net.GND",
      "width": 0.3,
      "pcbPath": [
        {
          "x": 2.9,
          "y": -1.1
        },
        {
          "x": 2.9,
          "y": -1.1,
          "via": true,
          "fromLayer": "top",
          "toLayer": "bottom"
        }
      ],
      "global_path_mm": [[-12.753364, 7.5], [-14.899999999999864, 8.600000000000577]],
      "segment_layers": ["top", "top"],
      "classification": "manual native GND via escape",
      "top_length_mm": 2.412062626984773,
      "via_outer_mm": 0.45,
      "via_hole_mm": 0.3
    },
    {
      "net": "GND",
      "from": ".C70 > .pin2",
      "to": "net.GND",
      "width": 0.3,
      "pcbPath": [
        {
          "x": -0.25,
          "y": -0.9
        },
        {
          "x": -1.75,
          "y": -1.2
        },
        {
          "x": -3.85,
          "y": -1.5
        },
        {
          "x": -3.85,
          "y": -1.5,
          "via": true,
          "fromLayer": "top",
          "toLayer": "bottom"
        }
      ],
      "global_path_mm": [
        [16.5, -3.049976],
        [17.400000000000595, -3.999999999999602],
        [17.7000000000006, -5.499999999999623],
        [18.000000000000604, -7.599999999999653]
      ],
      "segment_layers": ["top", "top", "top", "top"],
      "classification": "manual native GND via escape",
      "top_length_mm": 4.959668853436398,
      "via_outer_mm": 0.45,
      "via_hole_mm": 0.3
    },
    {
      "net": "LCD_DC",
      "from": ".U14 > .pin16",
      "to": "net.LCD_DC",
      "width": 0.2,
      "pcbPath": [
        {
          "x": -0.35,
          "y": 4.1
        },
        {
          "x": -0.35,
          "y": 4.1,
          "via": true,
          "fromLayer": "top",
          "toLayer": "bottom"
        }
      ],
      "global_path_mm": [[8.675, 10.87095], [8.650000000000475, 12.100000000000627]],
      "segment_layers": ["top", "top"],
      "classification": "manual native ordinary via escape; power current qualification pending",
      "top_length_mm": 1.229304235127137,
      "via_outer_mm": 0.45,
      "via_hole_mm": 0.3
    },
    {
      "net": "LCD_DC",
      "from": ".R44 > .pin1",
      "to": "net.LCD_DC",
      "width": 0.2,
      "pcbPath": [
        {
          "x": -0.753364,
          "y": 1.8
        },
        {
          "x": -0.753364,
          "y": 1.8,
          "via": true,
          "fromLayer": "top",
          "toLayer": "bottom"
        }
      ],
      "global_path_mm": [[12.996636, -3.25], [12.996636, -1.45]],
      "segment_layers": ["top", "top"],
      "classification": "manual native ordinary via escape; power current qualification pending",
      "top_length_mm": 1.8,
      "via_outer_mm": 0.45,
      "via_hole_mm": 0.3
    },
    {
      "net": "MIC_BCLK_INPUT",
      "from": ".U24 > .pin1",
      "to": "net.MIC_BCLK_INPUT",
      "width": 0.2,
      "pcbPath": [
        {
          "x": 2.0999,
          "y": -0.65
        },
        {
          "x": 2.0999,
          "y": -0.65,
          "via": true,
          "fromLayer": "top",
          "toLayer": "bottom"
        }
      ],
      "global_path_mm": [[15.8999, -26.65], [17.0999, -26.65]],
      "segment_layers": ["top", "top"],
      "classification": "manual native ordinary via escape; power current qualification pending",
      "top_length_mm": 1.200000000000001,
      "via_outer_mm": 0.45,
      "via_hole_mm": 0.3
    },
    {
      "net": "MIC_BCLK_INPUT",
      "from": ".R88 > .pin2",
      "to": "net.MIC_BCLK_INPUT",
      "width": 0.2,
      "pcbPath": [
        {
          "x": 1.75,
          "y": -0.75
        },
        {
          "x": 2.95,
          "y": -0.75
        },
        {
          "x": 2.95,
          "y": -0.75,
          "via": true,
          "fromLayer": "top",
          "toLayer": "bottom"
        }
      ],
      "global_path_mm": [
        [14.503364, -28.25],
        [15.500000000000568, -28.999999999999957],
        [16.700000000000585, -28.999999999999957]
      ],
      "segment_layers": ["top", "top", "top"],
      "classification": "manual native ordinary via escape; power current qualification pending",
      "top_length_mm": 2.4473104330907813,
      "via_outer_mm": 0.45,
      "via_hole_mm": 0.3
    },
    {
      "net": "MIC_BCLK_INPUT",
      "from": ".R90 > .pin1",
      "to": "net.MIC_BCLK_INPUT",
      "width": 0.2,
      "pcbPath": [
        {
          "x": -0.8,
          "y": -0.8
        },
        {
          "x": -0.8,
          "y": -0.8,
          "via": true,
          "fromLayer": "top",
          "toLayer": "bottom"
        }
      ],
      "global_path_mm": [[12.996636, -23.75], [12.950000000000529, -24.549999999999894]],
      "segment_layers": ["top", "top"],
      "classification": "manual native ordinary via escape; power current qualification pending",
      "top_length_mm": 0.801358169918908,
      "via_outer_mm": 0.45,
      "via_hole_mm": 0.3
    },
    {
      "net": "AMP_BCLK",
      "from": ".R69 > .pin1",
      "to": "net.AMP_BCLK",
      "width": 0.2,
      "pcbPath": [
        {
          "x": 1.65,
          "y": -1.9
        },
        {
          "x": 1.65,
          "y": -1.9,
          "via": true,
          "fromLayer": "top",
          "toLayer": "bottom"
        }
      ],
      "global_path_mm": [[-11.246636, 7.5], [-13.649999999999846, 9.400000000000588]],
      "segment_layers": ["top", "top"],
      "classification": "manual native ordinary via escape; power current qualification pending",
      "top_length_mm": 3.0636838147069767,
      "via_outer_mm": 0.45,
      "via_hole_mm": 0.3
    },
    {
      "net": "AMP_BCLK",
      "from": ".R66 > .pin2",
      "to": "net.AMP_BCLK",
      "width": 0.2,
      "pcbPath": [
        {
          "x": 3.75335,
          "y": 0.0
        },
        {
          "x": 3.75335,
          "y": 0.0,
          "via": true,
          "fromLayer": "top",
          "toLayer": "bottom"
        }
      ],
      "global_path_mm": [[-6.24665, 2], [-3.24665, 2.0]],
      "segment_layers": ["top", "top"],
      "classification": "manual native ordinary via escape; power current qualification pending",
      "top_length_mm": 3.0,
      "via_outer_mm": 0.45,
      "via_hole_mm": 0.3
    },
    {
      "net": "MIC_WS",
      "from": ".U5 > .pin1",
      "to": "net.MIC_WS",
      "width": 0.2,
      "pcbPath": [
        {
          "x": -2.000006,
          "y": -1.300049
        },
        {
          "x": -2.000006,
          "y": -1.300049,
          "via": true,
          "fromLayer": "top",
          "toLayer": "bottom"
        }
      ],
      "global_path_mm": [[19.1928144, -29.900049], [18.499994, -30.300049]],
      "segment_layers": ["top", "top"],
      "classification": "manual native ordinary via escape; power current qualification pending",
      "top_length_mm": 0.8000000666600972,
      "via_outer_mm": 0.45,
      "via_hole_mm": 0.3
    },
    {
      "net": "AUDIO_ENABLE_SUPPLY",
      "from": ".Q2 > .pin3",
      "to": "net.AUDIO_ENABLE_SUPPLY",
      "width": 0.2,
      "pcbPath": [
        {
          "x": -3.1,
          "y": -1.1
        },
        {
          "x": -3.1,
          "y": -1.1,
          "via": true,
          "fromLayer": "top",
          "toLayer": "bottom"
        }
      ],
      "global_path_mm": [[-12.149985000000001, 0.5], [-14.099999999999852, -0.5999999999995538]],
      "segment_layers": ["top", "top"],
      "classification": "manual native ordinary via escape; power current qualification pending",
      "top_length_mm": 2.2388743824126083,
      "via_outer_mm": 0.45,
      "via_hole_mm": 0.3
    },
    {
      "net": "AUDIO_ENABLE_SUPPLY",
      "from": ".R63 > .pin1",
      "to": "net.AUDIO_ENABLE_SUPPLY",
      "width": 0.2,
      "pcbPath": [
        {
          "x": -0.753364,
          "y": -0.8
        },
        {
          "x": -0.753364,
          "y": -0.8,
          "via": true,
          "fromLayer": "top",
          "toLayer": "bottom"
        }
      ],
      "global_path_mm": [[-7.003364, -16], [-7.003364, -16.8]],
      "segment_layers": ["top", "top"],
      "classification": "manual native ordinary via escape; power current qualification pending",
      "top_length_mm": 0.8000000000000007,
      "via_outer_mm": 0.45,
      "via_hole_mm": 0.3
    },
    {
      "net": "VMIC",
      "from": ".U24 > .pin5",
      "to": "net.VMIC",
      "width": 0.3,
      "pcbPath": [
        {
          "x": -2.25,
          "y": -0.25
        },
        {
          "x": -3.1,
          "y": -1.15
        },
        {
          "x": -3.1,
          "y": -1.8
        },
        {
          "x": -3.1,
          "y": -1.8,
          "via": true,
          "fromLayer": "top",
          "toLayer": "bottom"
        }
      ],
      "global_path_mm": [
        [14.1001, -26],
        [12.750000000000526, -26.24999999999992],
        [11.900000000000517, -27.14999999999993],
        [11.900000000000517, -27.79999999999994]
      ],
      "segment_layers": ["top", "top", "top", "top"],
      "classification": "manual native ordinary via escape; power current qualification pending",
      "top_length_mm": 3.2609931904093235,
      "via_outer_mm": 0.45,
      "via_hole_mm": 0.3
    },
    {
      "net": "VMIC",
      "from": ".R93 > .pin1",
      "to": "net.VMIC",
      "width": 0.3,
      "pcbPath": [
        {
          "x": 0.35,
          "y": 0.9
        },
        {
          "x": 2.6,
          "y": 0.9
        },
        {
          "x": 2.6,
          "y": 0.9,
          "via": true,
          "fromLayer": "top",
          "toLayer": "bottom"
        }
      ],
      "global_path_mm": [
        [15.99665, -28.25],
        [17.10000000000059, -27.349999999999934],
        [19.35000000000062, -27.349999999999934]
      ],
      "segment_layers": ["top", "top", "top"],
      "classification": "manual native ordinary via escape; power current qualification pending",
      "top_length_mm": 3.6738613775580484,
      "via_outer_mm": 0.45,
      "via_hole_mm": 0.3
    },
    {
      "net": "VMIC",
      "from": ".U5 > .pin2",
      "to": "net.VMIC",
      "width": 0.3,
      "pcbPath": [
        {
          "x": -0.485242,
          "y": -1.700049
        },
        {
          "x": -0.485242,
          "y": -1.700049,
          "via": true,
          "fromLayer": "top",
          "toLayer": "bottom"
        }
      ],
      "global_path_mm": [[20.0147584, -29.900049], [20.014758, -30.700049]],
      "segment_layers": ["top", "top"],
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
    },
    {
      "net": "VSYS",
      "from": ".U16 > .pin10",
      "to": "net.VSYS",
      "width": 0.275,
      "pcbPath": [
        {
          "x": 2.4,
          "y": -0.25
        },
        {
          "x": 2.2,
          "y": -3.65
        },
        {
          "x": 2.2,
          "y": -3.65,
          "via": true,
          "fromLayer": "top",
          "toLayer": "bottom"
        }
      ],
      "global_path_mm": [
        [-6.5000029999999995, -26.249809],
        [-5.599999999999731, -26.24999999999992],
        [-5.799999999999734, -29.649999999999967]
      ],
      "segment_layers": ["top", "top", "top"],
      "classification": "manual native ordinary via escape; power current qualification pending",
      "top_length_mm": 4.305880293452751,
      "via_outer_mm": 0.45,
      "via_hole_mm": 0.3
    },
    {
      "net": "VSYS",
      "from": ".U16 > .pin11",
      "to": "net.VSYS",
      "width": 0.275,
      "pcbPath": [
        {
          "x": 2.4,
          "y": -0.65
        },
        {
          "x": 1.65,
          "y": -3.8
        },
        {
          "x": 1.65,
          "y": -3.8,
          "via": true,
          "fromLayer": "top",
          "toLayer": "bottom"
        }
      ],
      "global_path_mm": [
        [-6.5000029999999995, -25.749937],
        [-5.599999999999731, -26.649999999999924],
        [-6.349999999999742, -29.79999999999997]
      ],
      "segment_layers": ["top", "top", "top"],
      "classification": "manual native ordinary via escape; power current qualification pending",
      "top_length_mm": 4.510893847629043,
      "via_outer_mm": 0.45,
      "via_hole_mm": 0.3
    },
    {
      "net": "VSYS",
      "from": ".U3 > .pin2",
      "to": "net.VSYS",
      "width": 0.2,
      "pcbPath": [
        {
          "x": -0.248539,
          "y": -2.299997
        },
        {
          "x": -0.248539,
          "y": -2.299997,
          "via": true,
          "fromLayer": "top",
          "toLayer": "bottom"
        }
      ],
      "global_path_mm": [[-16.998539, 2.500003], [-16.998539, 1.700003]],
      "segment_layers": ["top", "top"],
      "classification": "manual native ordinary via escape; power current qualification pending",
      "top_length_mm": 0.8,
      "via_outer_mm": 0.45,
      "via_hole_mm": 0.3
    },
    {
      "net": "AMP_DIN",
      "from": ".R65 > .pin2",
      "to": ".R68 > .pin1",
      "width": 0.2,
      "pcbPath": [
        {
          "x": 0.046432176,
          "y": 0.706917824
        },
        {
          "x": 0.046432176,
          "y": 5.200203824
        },
        {
          "x": -0.753364,
          "y": 6.0
        }
      ],
      "global_path_mm": [
        [-6.24665, 0],
        [-6.953567824127888, 0.7069178241278887],
        [-6.953567824127888, 5.200203824127888],
        [-7.753364, 6]
      ],
      "segment_layers": ["top", "top", "top", "top"],
      "classification": "authored native retention of the untouched R65-to-R68 geometry; the entire old three-terminal replay phase is replaced to keep native endpoint validation intact",
      "retained_from_native_sha256": "019f640b94eb33928659d15ca591cd3e5d6d1dc03bed57fe32227ff1ac9273fb",
      "original_pcb_trace_id": "saved_phase_null_5_0",
      "via_outer_mm": 0.45,
      "via_hole_mm": 0.3
    },
    {
      "net": "BUCK_ENABLE",
      "from": ".U2 > .pin1",
      "to": "net.BUCK_ENABLE",
      "width": 0.2,
      "pcbPath": [
        {
          "x": -0.900043,
          "y": 2.399998
        },
        {
          "x": -0.900043,
          "y": 2.399998,
          "via": true,
          "fromLayer": "top",
          "toLayer": "bottom"
        }
      ],
      "global_path_mm": [[-3.90004265, -15.000002], [-3.900043, -13.600002]],
      "segment_layers": ["top", "top"],
      "classification": "manual native ordinary via escape; power current qualification pending",
      "top_length_mm": 1.400000000000044,
      "via_outer_mm": 0.45,
      "via_hole_mm": 0.3
    },
    {
      "net": "BUCK_ENABLE",
      "from": ".R97 > .pin1",
      "to": "net.BUCK_ENABLE",
      "width": 0.2,
      "pcbPath": [
        {
          "x": -0.753364,
          "y": -0.8
        },
        {
          "x": -0.753364,
          "y": -0.8,
          "via": true,
          "fromLayer": "top",
          "toLayer": "bottom"
        }
      ],
      "global_path_mm": [[-9.246636, -14], [-9.246636, -13.2]],
      "segment_layers": ["top", "top"],
      "classification": "manual native ordinary via escape; power current qualification pending",
      "top_length_mm": 0.8000000000000007,
      "via_outer_mm": 0.45,
      "via_hole_mm": 0.3
    },
    {
      "net": "MIC_SD",
      "from": ".U4 > .pin6",
      "to": "net.MIC_SD",
      "width": 0.2,
      "pcbPath": [
        {
          "x": -0.507186,
          "y": -0.000127
        },
        {
          "x": -0.507186,
          "y": -0.000127,
          "via": true,
          "fromLayer": "top",
          "toLayer": "bottom"
        }
      ],
      "global_path_mm": [[-17.5571856, -28.750127], [-16.757186, -28.750127]],
      "segment_layers": ["top", "top"],
      "classification": "manual native ordinary via escape; power current qualification pending",
      "top_length_mm": 0.7999995999999996,
      "via_outer_mm": 0.45,
      "via_hole_mm": 0.3
    },
    {
      "net": "MIC_SD",
      "from": ".U7 > .pin3",
      "to": "net.MIC_SD",
      "width": 0.2,
      "pcbPath": [
        {
          "x": 2.300099,
          "y": 2.682011
        },
        {
          "x": 2.300099,
          "y": 2.682011,
          "via": true,
          "fromLayer": "top",
          "toLayer": "bottom"
        }
      ],
      "global_path_mm": [[-15.699901, -18.05004], [-14.699901, -16.317989]],
      "segment_layers": ["top", "top"],
      "classification": "manual native ordinary via escape; power current qualification pending",
      "top_length_mm": 2.0000001666502416,
      "via_outer_mm": 0.45,
      "via_hole_mm": 0.3
    },
    {
      "net": "HAPTIC_NMOS_GATE",
      "from": ".Q9 > .pin1",
      "to": "net.HAPTIC_NMOS_GATE",
      "width": 0.2,
      "pcbPath": [
        {
          "x": 1.85,
          "y": 0.6
        },
        {
          "x": 1.85,
          "y": 4.25
        },
        {
          "x": 1.85,
          "y": 4.25,
          "via": true,
          "fromLayer": "top",
          "toLayer": "bottom"
        }
      ],
      "global_path_mm": [
        [14.750002, -7.05004],
        [13.900000000000546, -8.599999999999667],
        [13.900000000000546, -12.24999999999972]
      ],
      "segment_layers": ["top", "top", "top"],
      "classification": "manual native ordinary via escape; power current qualification pending",
      "top_length_mm": 5.417732842259323,
      "via_outer_mm": 0.45,
      "via_hole_mm": 0.3
    },
    {
      "net": "HAPTIC_NMOS_GATE",
      "from": ".R83 > .pin2",
      "to": "net.HAPTIC_NMOS_GATE",
      "width": 0.2,
      "pcbPath": [
        {
          "x": 2.9,
          "y": -0.7
        },
        {
          "x": 2.9,
          "y": -0.7,
          "via": true,
          "fromLayer": "top",
          "toLayer": "bottom"
        }
      ],
      "global_path_mm": [[15.496636, -16.5], [13.350000000000534, -15.79999999999977]],
      "segment_layers": ["top", "top"],
      "classification": "manual native ordinary via escape; power current qualification pending",
      "top_length_mm": 2.2578853196063857,
      "via_outer_mm": 0.45,
      "via_hole_mm": 0.3
    },
    {
      "net": "AMP_LRCLK",
      "from": ".U3 > .pin14",
      "to": "net.AMP_LRCLK",
      "width": 0.2,
      "pcbPath": [
        {
          "x": -2.2,
          "y": 0.35
        },
        {
          "x": -2.1,
          "y": 1.2
        },
        {
          "x": -2.05,
          "y": 1.25
        },
        {
          "x": -2.05,
          "y": 1.25,
          "via": true,
          "fromLayer": "top",
          "toLayer": "bottom"
        }
      ],
      "global_path_mm": [
        [-18.249997, 4.252095],
        [-18.94999999999992, 4.35000000000052],
        [-18.84999999999992, 5.200000000000529],
        [-18.79999999999992, 5.250000000000526]
      ],
      "segment_layers": ["top", "top", "top", "top"],
      "classification": "manual native ordinary via escape; power current qualification pending",
      "top_length_mm": 1.6333893337832728,
      "via_outer_mm": 0.45,
      "via_hole_mm": 0.3
    },
    {
      "net": "AMP_LRCLK",
      "from": ".R70 > .pin1",
      "to": "net.AMP_LRCLK",
      "width": 0.2,
      "pcbPath": [
        {
          "x": -4.3,
          "y": 0.2
        },
        {
          "x": -4.3,
          "y": 0.2,
          "via": true,
          "fromLayer": "top",
          "toLayer": "bottom"
        }
      ],
      "global_path_mm": [[-20.246636, 9], [-16.69999999999989, 8.80000000000058]],
      "segment_layers": ["top", "top"],
      "classification": "manual native ordinary via escape; power current qualification pending",
      "top_length_mm": 3.552270670500285,
      "via_outer_mm": 0.45,
      "via_hole_mm": 0.3
    },
    {
      "net": "AMP_LRCLK",
      "from": ".R67 > .pin2",
      "to": "net.AMP_LRCLK",
      "width": 0.2,
      "pcbPath": [
        {
          "x": 2.831811,
          "y": 1.2
        },
        {
          "x": 2.831811,
          "y": 1.2,
          "via": true,
          "fromLayer": "top",
          "toLayer": "bottom"
        }
      ],
      "global_path_mm": [[-6.24665, 4], [-4.168189, 5.2]],
      "segment_layers": ["top", "top"],
      "classification": "manual native ordinary via escape; power current qualification pending",
      "top_length_mm": 2.400000026775208,
      "via_outer_mm": 0.45,
      "via_hole_mm": 0.3
    },
    {
      "net": "MIC_INPUT",
      "from": ".C73 > .pin1",
      "to": "net.MIC_INPUT",
      "width": 0.3,
      "pcbPath": [
        {
          "x": 0.1,
          "y": 0.8
        },
        {
          "x": 2.3,
          "y": 1.1
        },
        {
          "x": 2.8,
          "y": 1.6
        },
        {
          "x": 2.8,
          "y": 1.6,
          "via": true,
          "fromLayer": "top",
          "toLayer": "bottom"
        }
      ],
      "global_path_mm": [
        [13, -8.950023999999999],
        [12.200000000000522, -8.149999999999661],
        [11.900000000000517, -5.94999999999963],
        [11.40000000000051, -5.449999999999623]
      ],
      "segment_layers": ["top", "top", "top", "top"],
      "classification": "manual native ordinary via escape; power current qualification pending",
      "top_length_mm": 4.058854932892412,
      "via_outer_mm": 0.45,
      "via_hole_mm": 0.3
    },
    {
      "net": "MIC_INPUT",
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
      ],
      "global_path_mm": [
        [-7.75335, 0],
        [-7.75335, -0.6354509891958123],
        [-7.83429066206103, -0.7163916512568423],
        [-7.83429066206103, -0.8162906620610298],
        [-7.9, -0.882]
      ],
      "segment_layers": ["top", "top", "top", "top", "top"],
      "classification": "manual native ordinary via escape; power current qualification pending",
      "top_length_mm": 0.9427444189220144,
      "via_outer_mm": 0.45,
      "via_hole_mm": 0.3
    },
    {
      "net": "USB_DP",
      "from": ".J1 > .pin10",
      "to": "net.USB_DP",
      "width": 0.2979,
      "pcbPath": [
        {
          "x": 0.75,
          "y": 3.05
        },
        {
          "x": 0.45,
          "y": 3.2
        },
        {
          "x": -0.05,
          "y": 3.2
        },
        {
          "x": -0.249936,
          "y": 3.074043
        },
        {
          "x": -0.249936,
          "y": 2.174043
        }
      ],
      "global_path_mm": [
        [0.750062, -25.8259568],
        [0.7500000000003588, -24.9499999999999],
        [0.45000000000035456, -24.799999999999898],
        [-0.049999999999652545, -24.799999999999898],
        [-0.249936, -24.9259568],
        [-0.249936, -25.8259568]
      ],
      "segment_layers": ["top", "top", "top", "top", "top", "top"],
      "classification": "manual native route to existing copper; physical contact must pass independent audit",
      "via_outer_mm": 0.45,
      "via_hole_mm": 0.3
    },
    {
      "net": "USB_DP",
      "from": ".D2 > .pin1",
      "to": "net.USB_DP",
      "width": 0.2979,
      "pcbPath": [
        {
          "x": 0.500064,
          "y": -2.825957
        }
      ],
      "global_path_mm": [[-0.250001, -23.350012], [-0.249936, -25.8259568]],
      "segment_layers": ["top", "top"],
      "classification": "manual native route to existing copper; physical contact must pass independent audit",
      "via_outer_mm": 0.45,
      "via_hole_mm": 0.3
    },
    {
      "net": "SPEAKER_P",
      "from": ".U3 > .pin9",
      "to": "net.SPEAKER_P",
      "width": 0.275,
      "pcbPath": [
        {
          "x": 1.149935,
          "y": 2.192817
        },
        {
          "x": 1.149935,
          "y": 2.192817,
          "via": true,
          "fromLayer": "top",
          "toLayer": "bottom"
        }
      ],
      "global_path_mm": [[-16.000065, 5.4999970000000005], [-15.600065, 6.192817]],
      "segment_layers": ["top", "top"],
      "classification": "manual native ordinary via escape; power current qualification pending",
      "top_length_mm": 0.7999997202499498,
      "via_outer_mm": 0.45,
      "via_hole_mm": 0.3
    },
    {
      "net": "GND",
      "from": ".R64 > .pin2",
      "to": "net.GND",
      "width": 0.3,
      "pcbPath": [
        {
          "x": 1.6,
          "y": -0.1
        },
        {
          "x": 1.6,
          "y": -0.1,
          "via": true,
          "fromLayer": "top",
          "toLayer": "bottom"
        }
      ],
      "global_path_mm": [[-5.49665, -18], [-4.649999999999718, -18.099999999999802]],
      "segment_layers": ["top", "top"],
      "classification": "manual native GND via escape",
      "top_length_mm": 0.8525351737614336,
      "via_outer_mm": 0.45,
      "via_hole_mm": 0.3
    },
    {
      "net": "USB_DP",
      "from": ".J1 > .pin8",
      "to": "net.USB_DP",
      "width": 0.2979,
      "pcbPath": [
        {
          "x": -0.249936,
          "y": 3.774043
        },
        {
          "x": -0.249936,
          "y": 3.774043,
          "via": true,
          "fromLayer": "top",
          "toLayer": "bottom"
        }
      ],
      "global_path_mm": [[-0.249936, -25.8259568], [-0.249936, -24.225957]],
      "segment_layers": ["top", "top"],
      "classification": "manual native ordinary via escape; power current qualification pending",
      "top_length_mm": 1.599999799999999,
      "via_outer_mm": 0.45,
      "via_hole_mm": 0.3
    },
    {
      "net": "USB_DP",
      "from": ".R31 > .pin1",
      "to": "net.USB_DP",
      "width": 0.2979,
      "pcbPath": [
        {
          "x": 0.0,
          "y": 0.9
        },
        {
          "x": 0.0,
          "y": 2.15
        },
        {
          "x": 0.6,
          "y": 2.6
        },
        {
          "x": 0.6,
          "y": 2.6,
          "via": true,
          "fromLayer": "top",
          "toLayer": "bottom"
        }
      ],
      "global_path_mm": [
        [-23.95335, 14.55],
        [-23.19999999999998, 15.45000000000067],
        [-23.19999999999998, 16.700000000000692],
        [-22.599999999999973, 17.150000000000702]
      ],
      "segment_layers": ["top", "top", "top", "top"],
      "classification": "manual native ordinary via escape; power current qualification pending",
      "top_length_mm": 3.173684890633476,
      "via_outer_mm": 0.45,
      "via_hole_mm": 0.3
    },
    {
      "net": "USB_CC1",
      "from": ".J1 > .pin6",
      "to": "net.USB_CC1",
      "width": 0.2,
      "pcbPath": [
        {
          "x": -1.2,
          "y": 1.25
        },
        {
          "x": -0.8,
          "y": 1.05
        },
        {
          "x": -0.8,
          "y": 1.05,
          "via": true,
          "fromLayer": "top",
          "toLayer": "bottom"
        }
      ],
      "global_path_mm": [
        [-1.249934, -25.8259568],
        [-1.1999999999996689, -26.749999999999925],
        [-0.7999999999996632, -26.94999999999993]
      ],
      "segment_layers": ["top", "top", "top"],
      "classification": "manual native ordinary via escape; power current qualification pending",
      "top_length_mm": 1.372604993678127,
      "via_outer_mm": 0.45,
      "via_hole_mm": 0.3
    },
    {
      "net": "LCD_SDA",
      "from": ".U14 > .pin14",
      "to": "net.LCD_SDA",
      "width": 0.2,
      "pcbPath": [
        {
          "x": 1.55,
          "y": 6.05
        },
        {
          "x": 1.7,
          "y": 6.2
        },
        {
          "x": 1.7,
          "y": 6.2,
          "via": true,
          "fromLayer": "top",
          "toLayer": "bottom"
        }
      ],
      "global_path_mm": [
        [9.975, 10.87095],
        [10.550000000000495, 14.05000000000065],
        [10.7000000000005, 14.200000000000657]
      ],
      "segment_layers": ["top", "top", "top"],
      "classification": "manual native ordinary via escape; power current qualification pending",
      "top_length_mm": 3.442764155552179,
      "via_outer_mm": 0.45,
      "via_hole_mm": 0.3
    },
    {
      "net": "LCD_SDA",
      "from": ".R46 > .pin1",
      "to": "net.LCD_SDA",
      "width": 0.2,
      "pcbPath": [
        {
          "x": 0.25,
          "y": 0.9
        },
        {
          "x": 0.25,
          "y": 0.9,
          "via": true,
          "fromLayer": "top",
          "toLayer": "bottom"
        }
      ],
      "global_path_mm": [[3.246636, -5.25], [4.250000000000409, -4.349999999999607]],
      "segment_layers": ["top", "top"],
      "classification": "manual native ordinary via escape; power current qualification pending",
      "top_length_mm": 1.3478647248509499,
      "via_outer_mm": 0.45,
      "via_hole_mm": 0.3
    },
    {
      "net": "VBUS",
      "from": ".C1 > .pin1",
      "to": "net.VBUS",
      "width": 0.3,
      "pcbPath": [
        {
          "x": -0.75,
          "y": 1.0
        },
        {
          "x": -0.75,
          "y": 1.0,
          "via": true,
          "fromLayer": "top",
          "toLayer": "bottom"
        }
      ],
      "global_path_mm": [[-12, -25.299976], [-11, -25.25]],
      "segment_layers": ["top", "top"],
      "classification": "manual native ordinary via escape; power current qualification pending",
      "top_length_mm": 1.0012480215091564,
      "via_outer_mm": 0.45,
      "via_hole_mm": 0.3
    }
  ],
  "pours": [
    {
      "net": "MCU_LCD_RESET_N",
      "layer": "inner1",
      "nominal_width_mm": 0.2,
      "drawn_width_mm": 0.202,
      "path_mm": [
        [7.375, 3.32905],
        [10.00000000000049, 6.400000000000546],
        [9.800000000000487, 7.000000000000554],
        [8.700000000000472, 7.700000000000564],
        [8.100000000000463, 7.700000000000564],
        [5.800000000000431, 4.500000000000519],
        [1.1000000000003638, 1.6000000000004775],
        [-3.2999999999996987, -0.39999999999955094],
        [-3.8999999999997073, -0.1999999999995481],
        [-3.9999999999997087, 0.40000000000046043],
        [-3.4999999999997016, 1.1000000000004704],
        [-1.633975, 1.746636]
      ],
      "outline": [
        {
          "x": 9.886128,
          "y": 6.422226
        },
        {
          "x": 9.715523,
          "y": 6.934042
        },
        {
          "x": 8.670589,
          "y": 7.599
        },
        {
          "x": 8.151788,
          "y": 7.599
        },
        {
          "x": 5.882014,
          "y": 4.441053
        },
        {
          "x": 5.880534,
          "y": 4.439047
        },
        {
          "x": 5.879006,
          "y": 4.437079
        },
        {
          "x": 5.87743,
          "y": 4.435149
        },
        {
          "x": 5.875806,
          "y": 4.433259
        },
        {
          "x": 5.874137,
          "y": 4.431409
        },
        {
          "x": 5.872422,
          "y": 4.429601
        },
        {
          "x": 5.870663,
          "y": 4.427836
        },
        {
          "x": 5.868862,
          "y": 4.426115
        },
        {
          "x": 5.867018,
          "y": 4.424438
        },
        {
          "x": 5.865134,
          "y": 4.422808
        },
        {
          "x": 5.863209,
          "y": 4.421225
        },
        {
          "x": 5.861247,
          "y": 4.419689
        },
        {
          "x": 5.859247,
          "y": 4.418203
        },
        {
          "x": 5.857211,
          "y": 4.416766
        },
        {
          "x": 5.85514,
          "y": 4.41538
        },
        {
          "x": 5.853036,
          "y": 4.414045
        },
        {
          "x": 1.153036,
          "y": 1.514045
        },
        {
          "x": 1.150849,
          "y": 1.512734
        },
        {
          "x": 1.148631,
          "y": 1.511478
        },
        {
          "x": 1.146381,
          "y": 1.510279
        },
        {
          "x": 1.144102,
          "y": 1.509137
        },
        {
          "x": 1.141794,
          "y": 1.508053
        },
        {
          "x": -3.258206,
          "y": -0.491947
        },
        {
          "x": -3.260512,
          "y": -0.492961
        },
        {
          "x": -3.262843,
          "y": -0.493917
        },
        {
          "x": -3.265198,
          "y": -0.494815
        },
        {
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
        [-4.149999999999711, 26.95000000000084],
        [-0.5999999999996604, 26.95000000000084],
        [-0.5499999999996597, 26.900000000000837],
        [-0.3999999999996575, 26.900000000000837],
        [-0.3499999999996568, 26.850000000000833],
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
