AnasSarkiz/tscircuit-ai-agent-remote/evidence/core-pill-paste-fix-2026-10-07/u16-u27-coupon.png

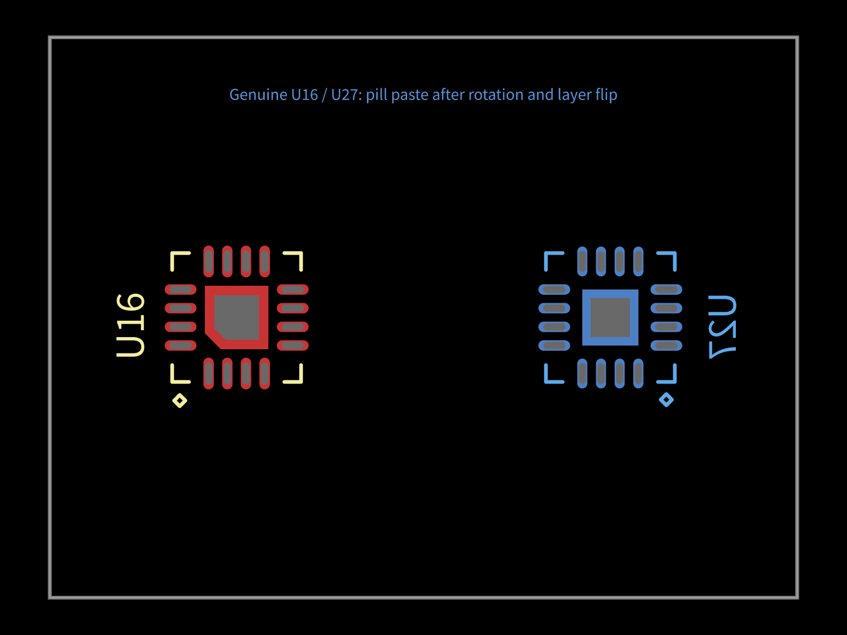
evidence/core-pill-paste-fix-2026-10-07/u16-u27-coupon.png
