AnasSarkiz/tscircuit-ai-agent-remote/evidence/pcb-completion-2026-10-08/schematic-style-repair/trial-2/ui-style-analysis.png

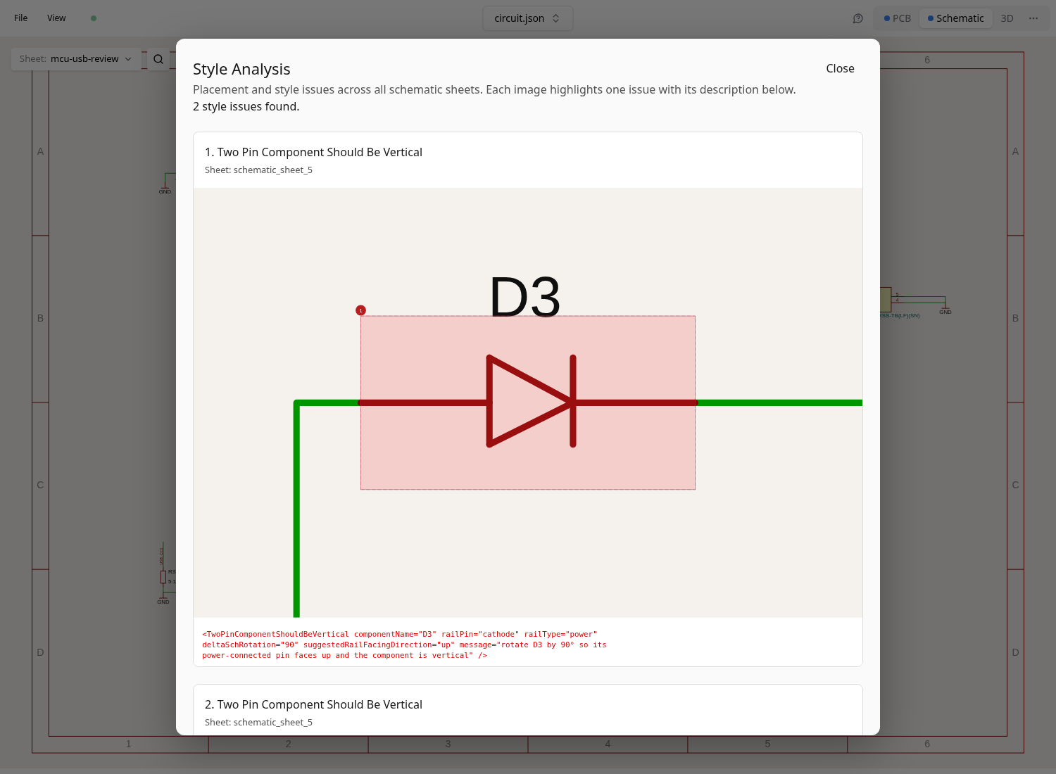
evidence/pcb-completion-2026-10-08/schematic-style-repair/trial-2/ui-style-analysis.png
